Pradeeparul2/house-plan/docs/index.md

# Master Documentation Index

| Section | File | Description |
|---|---|---|
| **Section_00** | `docs/00_section_00.md` | Section details |
| **Table of Contents** | `docs/01_table_of_contents.md` | Section details |
| **1. Executive Architectural Summary** | `docs/02_1_executive_architectural_summ.md` | Section details |
| **2. Visual Renderings Portfolio** | `docs/03_2_visual_renderings_portfolio.md` | Section details |
| **3. 3D Architectural & Structural Component Overview** | `docs/04_3_3d_architectural_structural_.md` | Section details |
| **4. Site, Substructure & Underground Utilities** | `docs/05_4_site_substructure_undergroun.md` | Section details |
| **5. Structural Column Grid & Floor Levels** | `docs/06_5_structural_column_grid_floor.md` | Section details |
| **6. Ground Floor Spatial Program & Room Schedules** | `docs/07_6_ground_floor_spatial_program.md` | Section details |
| **7. Staircase Bay & Integrated Utility Area** | `docs/08_7_staircase_bay_integrated_uti.md` | Section details |
| **8. Staircase Ergonomic & NBC Compliance Audit** | `docs/09_8_staircase_ergonomic_nbc_comp.md` | Section details |
| **9. Front Facade & Exterior Elevation Design** | `docs/10_9_front_facade_exterior_elevat.md` | Section details |
| **10. First Floor (G+1) Modular Expansion Design** | `docs/11_10_first_floor_g_1_modular_exp.md` | Section details |
| **11. Electrical & ELV Surveillance Engineering Specifications** | `docs/12_11_electrical_elv_surveillance.md` | Section details |
| **12. Material, Color & Finish Schedule** | `docs/13_12_material_color_finish_sched.md` | Section details |
| **13. FreeCAD Document Hierarchy & Tree Structure** | `docs/14_13_freecad_document_hierarchy_.md` | Section details |
| **14. Workspace File Organization** | `docs/15_14_workspace_file_organization.md` | Section details |
| **15. Verification & File Status** | `docs/16_15_verification_file_status.md` | Section details |
| **16. Structural Continuous Full-Width 360° Closed-Loop RCC Lintel & Seismic Ring Beam Schedule (IS 4326 & IS 456 / NBC Compliance)** | `docs/17_16_structural_continuous_full_.md` | Section details |
| **17. First Floor North Facade Optimization: Dust Prevention & Staircase Isolation** | `docs/18_17_first_floor_north_facade_op.md` | Section details |
| **18. Rooftop Staircase Headroom (Mumty) Structural Frame Integration** | `docs/19_18_rooftop_staircase_headroom_.md` | Section details |
| **19. First Floor Independent Electricity Board (EB) Service & Electrical Infrastructure (IS 732 & NBC 2016 Compliance)** | `docs/20_19_first_floor_independent_ele.md` | Section details |
| **20. First Floor Dedicated Uninterruptible Power Supply (UPS) System & Utility Loft** | `docs/21_20_first_floor_dedicated_unint.md` | Section details |
| **21. Continuous Vertical Wall Conduit Network into Modular Switch Boxes & Distribution Boards** | `docs/22_21_continuous_vertical_wall_co.md` | Section details |
| **22. Complete 1:1 Duplicate Electrical System Alignment (Ground Floor to First Floor)** | `docs/23_22_complete_1_1_duplicate_elec.md` | Section details |
| **23. Sitout & Entrance Verandah Lighting and Conduit Integration** | `docs/24_23_sitout_entrance_verandah_li.md` | Section details |
| **24. Staircase Luminaire Relocation to East Wall of Toilet** | `docs/25_24_staircase_luminaire_relocat.md` | Section details |
| **25. Direct Switchbox-to-Luminaire Staircase Wall Lighting & Slab Infrastructure De-Cluttering** | `docs/26_25_direct_switchbox_to_luminai.md` | Section details |
| **26. Under-Stair Utility Switchboard (SB-UTIL) Proper Repositioning** | `docs/27_26_under_stair_utility_switchb.md` | Section details |
| **27. De-scoping and Removal of Utility Switchboard (SB-UTIL) from First Floor** | `docs/28_27_de_scoping_and_removal_of_u.md` | Section details |
| **28. Relocation of Staircase Light Switchbox to South Staircase Wall** | `docs/29_28_relocation_of_staircase_lig.md` | Section details |
| **29. Sitout Area Electrical Pipelines Completion & Full Electrical Network Visualization (Walls Hidden)** | `docs/30_29_sitout_area_electrical_pipe.md` | Section details |
| **30. Integration of Deep PVC Pendant Pot Boxes at All Conduit Pipe Crossings & Multi-Branch Junctions** | `docs/31_30_integration_of_deep_pvc_pen.md` | Section details |
| **31. Relocation of Ground Floor Staircase Wall Luminaire to Low-Level Landing Elevation** | `docs/32_31_relocation_of_ground_floor_.md` | Section details |
| **32. FreeCAD GUI Direct Visualization & Tree Node Separation for Staircase Lighting and Switchbox (`SB_STAIR1`)** | `docs/33_32_freecad_gui_direct_visualiz.md` | Section details |
| **33. Relocation of GF Staircase Wall Luminaire to 2 Feet Below FF Stair Mid-Landing Slab** | `docs/34_33_relocation_of_gf_staircase_.md` | Section details |
| **34. First Floor Staircase Wall Luminaire Relocation: 2 Feet Below Rain Protection Canopy Slab** | `docs/35_34_first_floor_staircase_wall_.md` | Section details |
| **35. First Floor Staircase Wall Luminaire Relocation: Headroom Weatherproof Wall (2 Feet Below Headroom Roof Slab)** | `docs/36_35_first_floor_staircase_wall_.md` | Section details |
| **36. Under-Stair Sump Water Pump Motor Switch Integrated into Utility Switchboard (SB-UTIL)** | `docs/37_36_under_stair_sump_water_pump.md` | Section details |
| **37. Ground Floor Living Room: Isolated MEP Electrical & Wiring Pipeline Architecture** | `docs/38_37_ground_floor_living_room_is.md` | Section details |
| **38. Kitchen Exhaust Fan Relocation to East Side Wall (Over Sink Bay)** | `docs/39_38_kitchen_exhaust_fan_relocat.md` | Section details |
| **39. Master Bedroom Electrical Pipeline Optimization** | `docs/40_39_master_bedroom_electrical_p.md` | Section details |
| **40. Ground Floor Toilet (4'-0" x 6'-0") Architectural, MEP & Plumbing Pipeline System** | `docs/41_40_ground_floor_toilet_4_0_x_6.md` | Section details |
| **41. Living Room Slab Conduit Optimization** | `docs/42_41_living_room_slab_conduit_op.md` | Section details |
| **42. Master Bedroom Ceiling Fan Provision (`FB-BED`)** | `docs/43_42_master_bedroom_ceiling_fan_.md` | Section details |
| **43. Complete Living Room Ceiling Electrical Pipeline Optimization & De-duplication** | `docs/44_43_complete_living_room_ceilin.md` | Section details |
| **44. Breakfast Counter Spotlight MEP Pipeline Connection (`DL-BC`)** | `docs/45_44_breakfast_counter_spotlight.md` | Section details |
| **44.1 Ground Floor Master Bedroom (Room 2/5) Pipeline Recheck & Full Restoration** | `docs/46_44_1_ground_floor_master_bedro.md` | Section details |
| **45. Master Bedroom Wardrobe Zone — De-Cluttering & Redundant MEP Excision** | `docs/47_45_master_bedroom_wardrobe_zon.md` | Section details |
| **46. Kitchen Entrance — Removal of North-Facing Switchbox** | `docs/48_46_kitchen_entrance_removal_of.md` | Section details |
| **47. Kitchen & Living Room Pipelines Reconnected — Seamless Orthogonal Conduit Loop** | `docs/49_47_kitchen_living_room_pipelin.md` | Section details |
| **48. Sitout Electrical Pipelines Checked & Optimized — 100% Orthogonal Grid** | `docs/50_48_sitout_electrical_pipelines.md` | Section details |
| **49. Ground Floor Electrical Pipelines — Unified Tree Grouping** | `docs/51_49_ground_floor_electrical_pip.md` | Section details |
| **50. First Floor Electrical Pipelines — Identical Grouping Parity** | `docs/52_50_first_floor_electrical_pipe.md` | Section details |
| **51. First Floor Stairs Wall Light Pipeline — Seamless Jointing (Gap Elimination)** | `docs/53_51_first_floor_stairs_wall_lig.md` | Section details |
| **52. First Floor MCB Distribution Board (MDB) & Main Door Handle — 100% Ground Floor Parity** | `docs/54_52_first_floor_mcb_distributio.md` | Section details |
| **53. Outdoor Switchboard (SB-1) Consolidation into Staircase Switchboard (SB_STAIR1)** | `docs/55_53_outdoor_switchboard_sb_1_co.md` | Section details |
| **54. Full-Building Model Tree Hierarchy & Object Grouping Audit** | `docs/56_54_full_building_model_tree_hi.md` | Section details |
| **55. Under-Stair Utility Switchboard (SB-UTIL) Pipeline Connectivity Resolution** | `docs/57_55_under_stair_utility_switchb.md` | Section details |
| **56. Bedroom East Wall: Loft Removal & Split AC Electrical Provision Integration** | `docs/58_56_bedroom_east_wall_loft_remo.md` | Section details |
| **57. Split AC Outdoor Unit (ODU) East Elevation Implementation (Option 2)** | `docs/59_57_split_ac_outdoor_unit_odu_e.md` | Section details |
| **58. Detailed 2D Ground Floor Plan with Dimensions (From 3D Model)** | `docs/60_58_detailed_2d_ground_floor_pl.md` | Section details |
| **59. Substructure Isolated Footings, Column Pedestals & Plinth Beam System (BOQ & Construction Detailing)** | `docs/61_59_substructure_isolated_footi.md` | Section details |
| **60. Underground Sump Vertical Alignment to Plinth Floor & Sitout Manhole Integration** | `docs/62_60_underground_sump_vertical_a.md` | Section details |
| **61. Septic Tank Vertical Alignment to Plinth Floor & Airtight Inspection Manhole Integration** | `docs/63_61_septic_tank_vertical_alignm.md` | Section details |
| **62. Substructure Spatial Collision Elimination: Raft Foundations & Exact Bay-Fitted Tanks** | `docs/64_62_substructure_spatial_collis.md` | Section details |
| **63. Complete 3D Architectural Building Visualization (All Storeys & Facades Active)** | `docs/65_63_complete_3d_architectural_b.md` | Section details |
| **64. Municipal Water Inflow Pipeline, Dual-Tap Kitchen Sink & Underground Sump Integration** | `docs/66_64_municipal_water_inflow_pipe.md` | Section details |
| **65. Overhead Water Tank (OHT) on Mumty Headroom Roof & Mandatory Construction Safeguards** | `docs/67_65_overhead_water_tank_oht_on_.md` | Section details |
| **66. Closed-Loop Water Distribution Network: Gravity Down-take Risers & Zonal Leak Isolation System** | `docs/68_66_closed_loop_water_distribut.md` | Section details |
| **67. Kitchen Sink Plumbing Re-Orientation: East-Side Tap Relocation & Direct Chase Feed** | `docs/69_67_kitchen_sink_plumbing_re_or.md` | Section details |
| **68. Building Drainage Network: Kitchen Greywater Drainage System & North Road Outfall** | `docs/70_68_building_drainage_network_k.md` | Section details |
| **69. Dual-Stream Toilet Wastewater & Sullage Segregation System (IS 1742 & IS 2470 Compliant)** | `docs/71_69_dual_stream_toilet_wastewat.md` | Section details |
| **70. Toilet Sunken Wet Area (15 cm Drop Below Surface) Architectural & Sanitary Detailing** | `docs/72_70_toilet_sunken_wet_area_15_c.md` | Section details |
| **71. Ergonomic Staircase Overhaul: 4-Winder Turnaround Landing & 17 Uniform 186.65 mm Risers (NBC 2016 Compliant)** | `docs/73_71_ergonomic_staircase_overhau.md` | Section details |
| **72. Comprehensive Staircase Safety Railings & Void Guardrail System (NBC 2016 Compliant)** | `docs/74_72_comprehensive_staircase_saf.md` | Section details |
| **73. OHT Kitchen Sink Down-Take Pipeline Re-Routing: Headroom Weather Curb to Col NE (Zero Window Obstruction)** | `docs/75_73_oht_kitchen_sink_down_take_.md` | Section details |
| **74. Rooftop Terrace Weatherproof Wall Luminaire & Entrance Switchboard (SB-TERRACE)** | `docs/76_74_rooftop_terrace_weatherproo.md` | Section details |
| **75. RCC Structural Optimization: 8-Column Frame Layout, Primary Living Hall Cross-Beam & Substructure Sync** | `docs/77_75_rcc_structural_optimization.md` | Section details |
| **76. Ground Floor AAC Block Wall Schedule & Specifications** | `docs/02_ground_floor.md` | Parametric AAC masonry wall ledger, clearances, aperture cutouts & material takeoffs |
| **77. First Floor AAC Block Wall Schedule & Specifications** | `docs/03_first_floor.md` | First floor parametric AAC masonry wall ledger, 1:1 parity & material takeoffs |
| **78. Pre-Drafting Model Health & Specification Readiness Audit** | `docs/78_pre_drafting_audit.md` | Pre-drafting health audit, discrepancy matrix, 2D sheet readiness scorecard & automated fix validation |
