Pradeeparul2/house-plan/docs/31_30_integration_of_deep_pvc_pen.md

## 30. Integration of Deep PVC Pendant Pot Boxes at All Conduit Pipe Crossings & Multi-Branch Junctions

In strict compliance with the client's directive (*"whenever pipe crossing happen add Pendant Pot Boxes"*) and Indian electrical standard **IS 732 / NBC Part 8**, deep PVC circular pendant pot boxes ($\varnothing 85\text{ mm} \times 60\text{ mm}$) have been engineered and cast into the slab at every single horizontal conduit crossing and multi-branch convergence junction:

```carousel
![Direct Top Plan View Showing Pendant Pot Boxes at All Slab Conduit Crossings](C:\Users\prade\.gemini\antigravity\brain\086e9390-dcd1-4cec-9724-3cc5bbdd6a28\pendant_pot_boxes_top_view.png)
<!-- slide -->
![Zoomed-in Perspective View of Central Dining & Corridor Crossing Pot Boxes](C:\Users\prade\.gemini\antigravity\brain\086e9390-dcd1-4cec-9724-3cc5bbdd6a28\pendant_pot_boxes_crossing_zoom.png)
<!-- slide -->
![Full Two-Storey Isometric Overview Highlighting All 34 Embedded Blue Downlight & Pendant Pot Boxes](C:\Users\prade\.gemini\antigravity\brain\086e9390-dcd1-4cec-9724-3cc5bbdd6a28\pendant_pot_boxes_crossings_iso.png)
```

### 30.1 Engineering Rationale & Benefits of Crossing Pot Boxes

1. **Zero Slab Conduit Overlap & Flattening:**
   - In RCC monolithic slabs ($125\text{ mm}$ thickness), running $25\text{ mm}$ conduits over or under each other consumes $50\text{ mm} + \text{clearance}$, which severely degrades structural concrete cover and risks pipe crushing during concrete compaction.
   - Inserting a 4-way/3-way deep junction pot box allows all intersecting conduits to enter orthogonally at the exact same horizontal centerline elevation ($Z = 4020.0\text{ mm}$ GF / $Z = 7193.0\text{ mm}$ FF), preventing pipe pinch-points and easing cable pulling.
2. **Dual-Function Lighting & Access:**
   - Each crossing box provides a flush circular ceiling portal ($\varnothing 85\text{ mm}$) that functions as:
     - A decorative pendant chandelier / hanging luminaire point.
     - An inspection and wire pulling junction box for circuit branching and loop-in maintenance.

### 30.2 Newly Integrated Crossing & Multi-Branch Pot Boxes

Five critical crossing and convergence hubs have been upgraded with dedicated Pendant Pot Boxes across both Ground and First Floors:

| Pot Box ID | Room / Zone | Coordinates $(X, Y)$ (mm) | Slab Elevation ($Z$) | Intersecting / Converging Conduit Branches | Architectural & Lighting Function |
| :--- | :--- | :--- | :--- | :--- | :--- |
| **PB-CROSS-1** | Bedroom Entry Corridor | $(2572.9, 4720.2)$ | GF: $3992.4$, FF: $7165.4$ | - Living Fan `FB-1` to Bedroom Downlight `DL-5`<br>- Dining Entry to Bedroom Study Switchboard `SB-11` | Resolves interior conduit crossing; serves as a corridor transition downlight. |
| **PB-CROSS-2** | Central Dining Hall | $(1850.0, 4775.1)$ | GF: $3992.4$, FF: $7165.4$ | - Feeder from Kitchen Pot `DL-7`<br>- Drop to Dining Entry `SB-4`<br>- Drop to Dining South `SB-5`<br>- Drop to Bedroom Entry `SB-8`<br>- Feeder to Bedroom Study `SB-11` | Major 5-way central distribution hub; accommodates the Dining Table pendant chandelier. |
| **PB-CROSS-3** | Toilet & Stair Lobby | $(3810.0, 1828.8)$ | GF: $3992.4$, FF: $7165.4$ | - Living Room East Pot `DL-2`<br>- Toilet Entrance Drop `SB-12`<br>- Toilet Geyser Drop `SB-13`<br>- Under-Stair Utility Station `SB-UTIL` | 4-way wet-zone distribution hub; provides ceiling lobby ambient downlight. |
| **PB-CROSS-4** | Master Bedroom South Aisle | $(2200.0, 7467.6)$ | GF: $3992.4$, FF: $7165.4$ | - Bedroom Fan `FB-2`<br>- Bedside Left `SB-9`<br>- Wardrobe / AC Drop on South Wall | 3-way bedroom power distribution hub; wardrobe passage recessed downlight. |
| **PB-CROSS-5** | Sitout Entrance Transition | $(370.0, 1720.0)$ | GF: $3992.4$, FF: $7165.4$ | - Sitout Downlight Pot $(857, 857)$<br>- Vertical drop to Sitout Switchboard `SB-1`<br>- Plinth drop to Gate Post | Transition junction linking horizontal slab runs to vertical wall drops and gate feeds. |

### 30.3 Component Schedule Audit

* **`Electrical_Slab_Light_Pots` (Ground Floor):** Expanded from 12 to **17 solid pot units** (12 room downlights + 5 crossing/multi-branch pendant boxes).
* **`FF_Electrical_Slab_Light_Pots` (First Floor):** Expanded from 12 to **17 solid pot units** (exact 1:1 vertical duplicate shifted by $\Delta Z = +3173.0\text{ mm}$).
* **Total Building Ceiling Junction Units:** **34 deep PVC pot boxes** (Electric Blue `#0074E4`) + **6 heavy-duty fan hook boxes** (Crimson Red `#E74C3C`).
* **Document Integrity:** Fully recomputed in `HomeConstruction.FCStd` with zero geometric errors.

---
