Pradeeparul2/house-plan/docs/38_37_ground_floor_living_room_is.md

## 37. Ground Floor Living Room: Isolated MEP Electrical & Wiring Pipeline Architecture

Per user directive (*"lets move to living room hide all other areas show the living room and wiring pipelines"*), all external areas (First Floor, Terrace Mumty, Bedroom, Kitchen, Toilet, Sitout, and Stairwell) have been hidden in FreeCAD. The **Ground Floor Living Room** and its complete concealed electrical conduit pipeline network have been isolated and highlighted:

```carousel
![FreeCAD Viewport Showing Ground Floor Living Room Isolated with Complete Slab and Wall Wiring Pipelines](C:\Users\prade\.gemini\antigravity\brain\086e9390-dcd1-4cec-9724-3cc5bbdd6a28\living_room_pipelines_annotated.png)
<!-- slide -->
![Axonometric View Showing Ceiling Conduit Network and TV Feature Wall Media Drops](c:\Users\prade\OneDrive\Desktop\home plan\renders\living_room_perfect_fit.png)
```

### 37.1 Architectural Envelope & Boundary Definition
* **Room Footprint:** $X \in [0.0, 5029.2\text{ mm}]$ ($16'\text{-}6"$), $Y \in [1714.5, 5181.6\text{ mm}]$ ($11'\text{-}4"$), $Z \in [914.4, 4087.4\text{ mm}]$ ($10'\text{-}0"$ ceiling clearance). Total area $\approx 187\text{ sq ft}$.
* **Wall Treatments:** Chased solid brickwork rendered in 75% translucent ghosting to reveal the internal vertical conduit drop runs.
* **Key Built-In Features:**
  - **North:** Teak 5-Panel Main Entrance Door (`Main_Door`) with classical white architectural arch surround.
  - **East:** 3-Panel casement window (`Living_Room_Window_East_Group`) with reinforced precast utility loft (`Living_Room_Loft_East`).
  - **West:** Modern TV Feature Wall with charcoal fluted acoustic wall panel, 65" smart display, floating console cabinet, and soundbar.

### 37.2 Ceiling Slab Lighting & Fan Infrastructure
* **Central Fan Box (`FB-1`):** Parametric galvanized octagonal fan box with integrated hook at $(X = 2514.6, Y = 3257.4, Z = 4020.0\text{ mm})$, centered in the ceiling.
* **4-Point Recessed Downlight Grid (`DL-1` to `DL-4`):**
  - **DL-1 (NE):** $(X = 1200.0, Y = 2500.0, Z = 4020.0\text{ mm})$
  - **DL-2 (NW):** $(X = 3800.0, Y = 2500.0, Z = 4020.0\text{ mm})$
  - **DL-3 (SE):** $(X = 1200.0, Y = 4000.0, Z = 4020.0\text{ mm})$
  - **DL-4 (SW):** $(X = 3800.0, Y = 4000.0, Z = 4020.0\text{ mm})$
* **Slab Conduit Piping (`Living_Slab_Conduit_Network`):**
  - $25\text{ mm}$ heavy-gauge rigid PVC in **Conduit Orange (`#FF7300`)** embedded at $Z = 4020.0\text{ mm}$.
  - Spider layout connecting `FB-1` directly to each of the 4 downlight pots and branching out to the perimeter wall headers.

### 37.3 Concealed Wall Chases & Modular Switchboards (`Living_Slab_Wall_Drops`)
All drops utilize $25\text{ mm}$ rigid PVC pipe in **Safety Emerald Green (`#10AC84`)**:
1. **Main Distribution Board (MDB):**
   - Location: North Foyer Wall at $(X = 1600.0, Y = 1930.0, Z = 2254.4 - 2574.4\text{ mm})$.
   - Houses 40A 30mA 4-pole RCCB, master DP isolator, and individual circuit MCBs.
2. **Main Room Switchboard (`SB-2`):**
   - Location: North Wall beside Main Door at $(X = 1700.0, Y = 1937.0, Z = 2114.4\text{ mm})$.
   - 8-Module plate controlling Ceiling Fan speed, chandelier/center cove, and the 4 recessed ceiling downlights.
3. **TV Media Console Switchboards (`SB-3` & `SB-3B`):**
   - Location: West Feature Wall at $X = 4845.0\text{ mm}, Y = 3262.0\text{ mm}$.
   - **SB-3 (Low-Level, $Z = 1460.0\text{ mm}$):** 6-module entertainment power sockets (Set-top box, gaming console, AV receiver) + RJ45 data point.
   - **SB-3B (Mid-Level, $Z = 2050.0\text{ mm}$):** Dedicated hidden power socket & HDMI pass-through behind the 65" wall-mounted display.
4. **Security & Tech Loft Hub (`SB-16`):**
   - Location: East Wall utility loft at $(X = 157.0, Y = 2325.0, Z = 3260.0\text{ mm})$ supplying the CCTV NVR and emergency UPS backup.

### 37.4 Master CAD Model State
* **CAD Master File:** [`HomeConstruction.FCStd`](file:///c:/Users/prade/OneDrive/Desktop/home%20plan/HomeConstruction.FCStd)
* **Isolated Display Objects:** `Living_Slab_Conduit_Network`, `Living_Slab_Wall_Drops`, `Living_Slab_Fan_Box`, `Living_Slab_Light_Pots`, `Living_Room_Switchboard_Plates`, and `Living_Room_Switchboard_Switches`.

### 37.5 Switchboard Model Consolidation: Plates & Switches Unified
In response to user feedback (*"why we have seperate boxes, is it possible to make it single"*), the switchboards were merged:
* **Previous Split Reason:** In CAD, plates (polycarbonate white) and rockers/sockets (charcoal black) were kept in separate compounds solely for multi-material color display.
* **Unified Resolution:** `Living_Room_Switchboard_Plates` and `Living_Room_Switchboard_Switches` were permanently fused into a single unified parametric object: **`Living_Room_Switchboards`**.
* **Benefits:** Eliminates tree clutter, provides clean single-click selection, and maintains 100% solid manifold geometry for all room controls (MDB, SB-2, SB-3, SB-16).

### 37.6 Living Room North Entrance MEP Consolidation: Combined Console & Single Pipeline
Per user request (*"Living Room Switchboards (MDB, SB-2, SB-3, SB-16 - Unified) make it compaine and single pipe line now i can see two pipe lines"*), the North entrance wall electrical infrastructure was completely re-architected:

```carousel
![Living Room Entrance Electrical Upgrade Showing Unified MDB and SB-2 Console Fed by Single Vertical Drop](C:\Users\prade\.gemini\antigravity\brain\086e9390-dcd1-4cec-9724-3cc5bbdd6a28\living_room_single_pipeline_combined_console.png)
<!-- slide -->
![Interior View of Living Room Looking at Main Entrance Showing Flush Multi-Tier Console and Single Drop](C:\Users\prade\.gemini\antigravity\brain\086e9390-dcd1-4cec-9724-3cc5bbdd6a28\living_room_combined_console_interior_annotated.png)
```

#### 1. Combined Architectural Console (MDB + SB-2 Unified Enclosure)
* **Previous State:** Two separate boxes were stacked vertically—the 12-way Main Distribution Board (`MDB`) at $+1340\text{ to }+1660\text{ mm}$ AFF and the 8-module Room Switchboard (`SB-2`) at $+1200\text{ mm}$ AFF, linked by an external interconnect pipe.
* **Unified Console Design:** Replaced both separate enclosures with a **Single 2-Tier Flush Architectural Console** ($X \in [1485, 1715\text{ mm}]$, $Y \in [1893, 1948\text{ mm}]$, $Z \in [2050, 2550\text{ mm}]$):
  - **Upper Section ($Z \in [2210, 2550\text{ mm}]$):** 12-Way SPN Distribution Board (40A RCCB, 32A DP Isolator, 6x MCBs) protected by a flush smoked-acrylic hinged door.
  - **Lower Section ($Z \in [2050, 2190\text{ mm}]$):** 8-Module Light & Fan Controller (6x 6A rocker switches, 1x fan speed regulator, 1x universal 6/16A socket).
  - **Internal Interconnect:** Factory-wired internal busbar links eliminate the external interlink pipe entirely.
  - **Single CAD Entity:** Integrated into `Living_Room_Switchboards` as a 100% solid manifold compound.

#### 2. Single Pipeline Vertical Conduit Drop
* **Eliminated Clutter:**
  - Removed Drop 1 (secondary $25\text{ mm}$ drop at $X = 1700\text{ mm}$).
  - Removed Drop 11 (horizontal interlink pipe at $Z = 2300\text{ mm}$).
  - Removed Slab Solid 2 (ceiling slab lateral connector between the two drops).
* **New Single Drop Run:**
  - **Diameter:** $25\text{ mm}$ heavy-gauge rigid PVC in Emerald Green (`#10AC84`).
  - **Route:** Centered at $(X = 1600.0, Y = 1930.0\text{ mm})$, running continuously from ceiling slab junction ($Z = 4020.0\text{ mm}$) straight down into the top flange of the combined console ($Z = 2550.0\text{ mm}$).
  - **Masonry Advantage:** Reduces wall chiseling to **exactly one vertical chase**, preserving structural masonry integrity beside the Main Door jamb.
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
