Pradeeparul2/house-plan/docs/39_38_kitchen_exhaust_fan_relocat.md

## 38. Kitchen Exhaust Fan Relocation to East Side Wall (Over Sink Bay)

Following client directive (*"move exhaust fan east side wall since south side wall common wall"*), the kitchen exhaust fan has been relocated to the **East exterior wall directly adjacent to the sink bay**, completely avoiding the South boundary wall which is a shared common wall with the adjacent property.
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
