Pradeeparul2/house-plan/renders/3d_axonometric_model.png

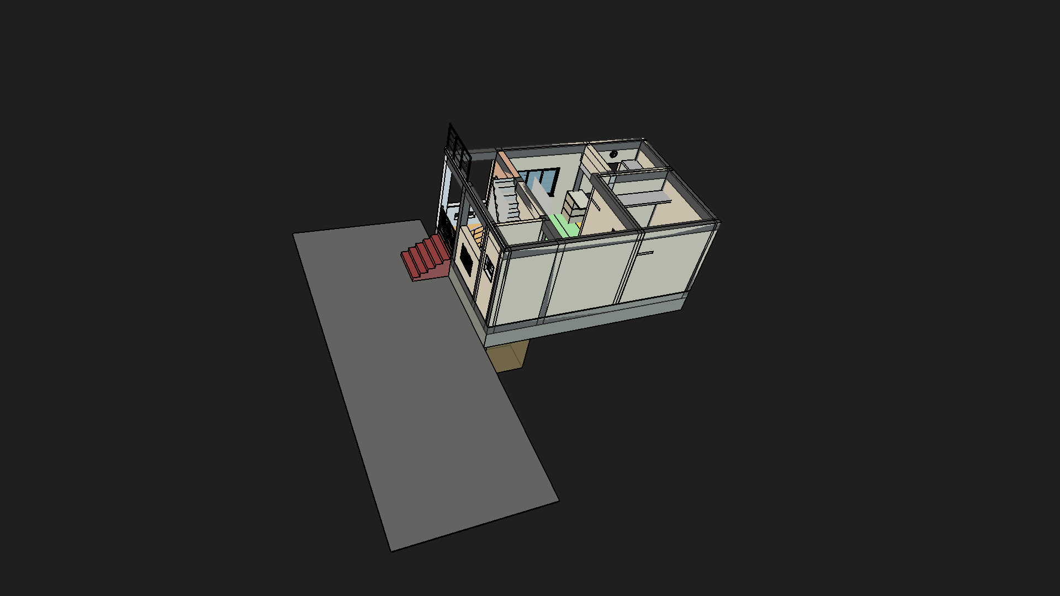
renders/3d_axonometric_model.png
