Pradeeparul2/house-plan/renders/3d_bedroom_door_wall_view.png

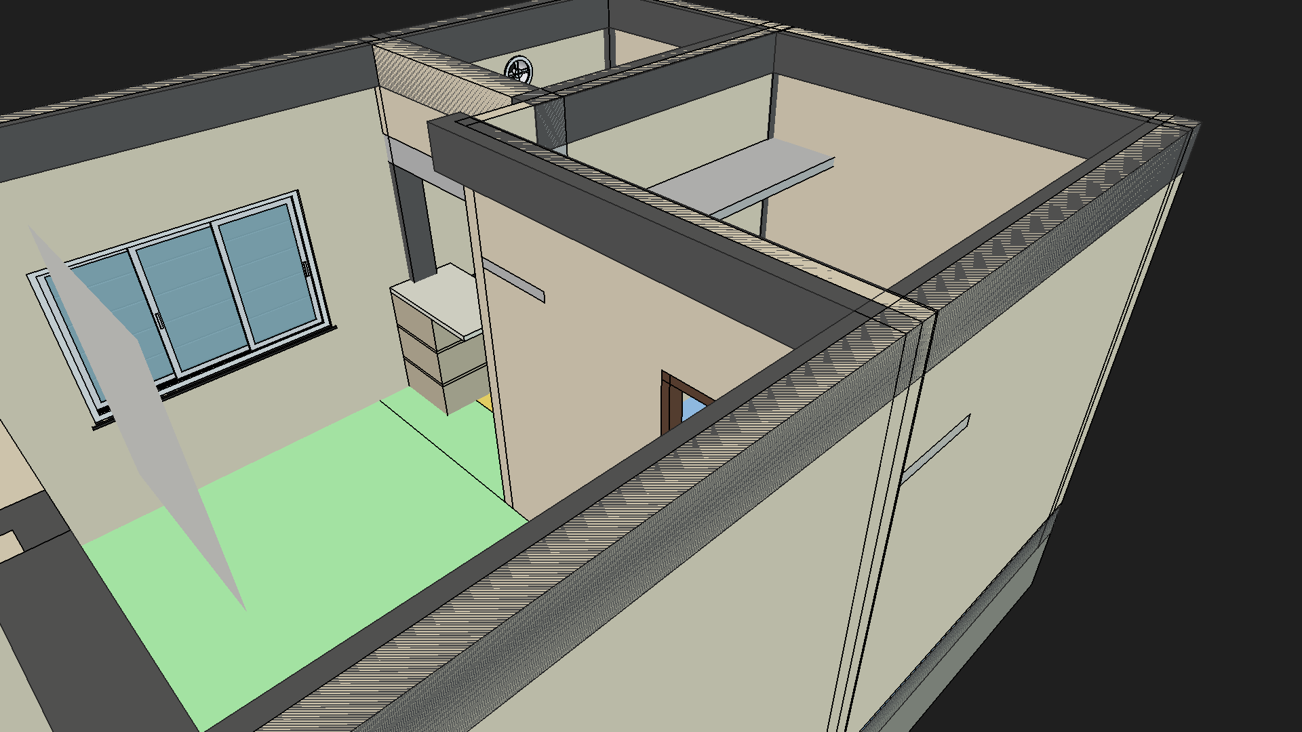
renders/3d_bedroom_door_wall_view.png
