Pradeeparul2/house-plan/renders/3d_model_painted_front_elevation.png

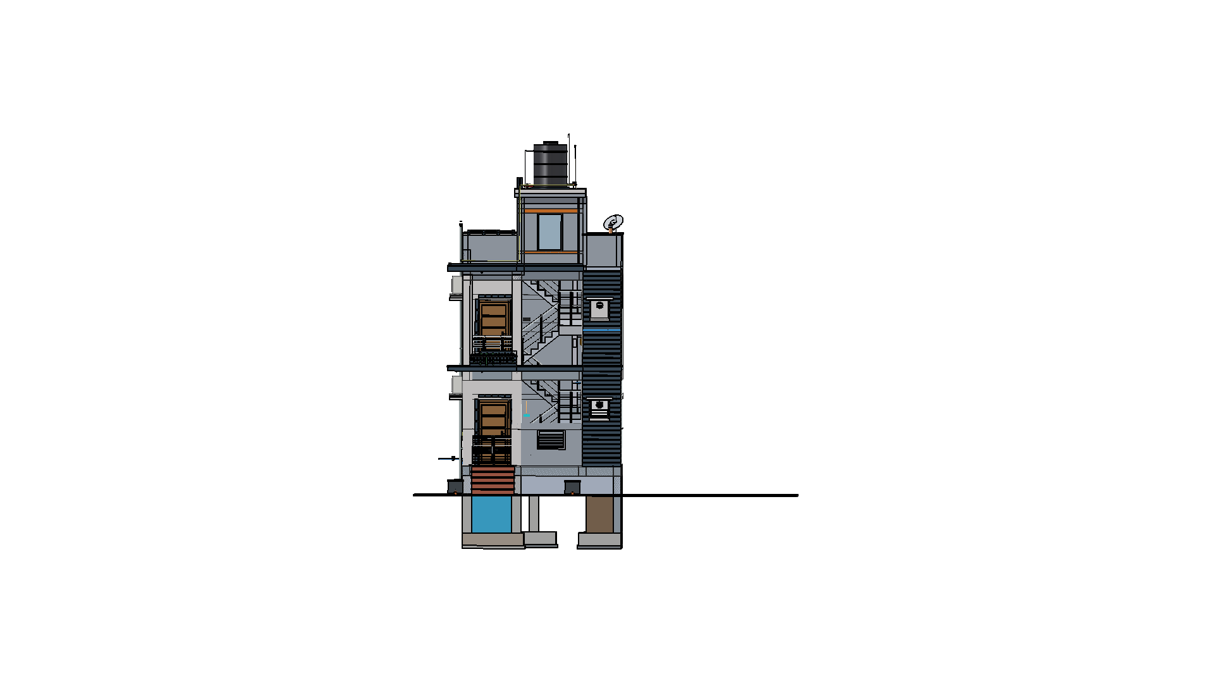
renders/3d_model_painted_front_elevation.png
