Pradeeparul2/house-plan/renders/all_electrical_pipelines_connected_southeast.png

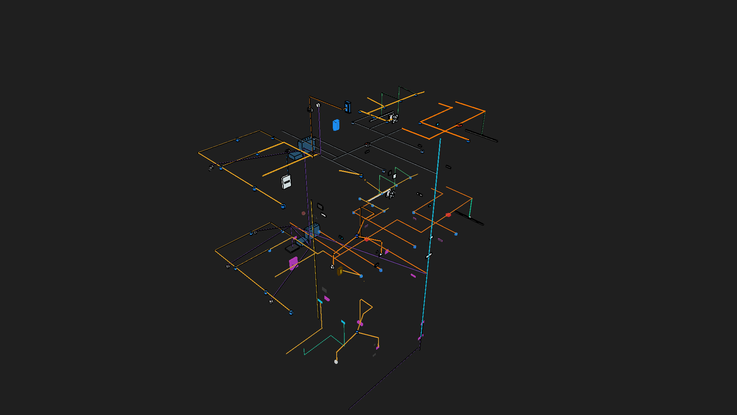
renders/all_electrical_pipelines_connected_southeast.png
