Pradeeparul2/house-plan/renders/all_electrical_pipelines_connected_top_plan.png

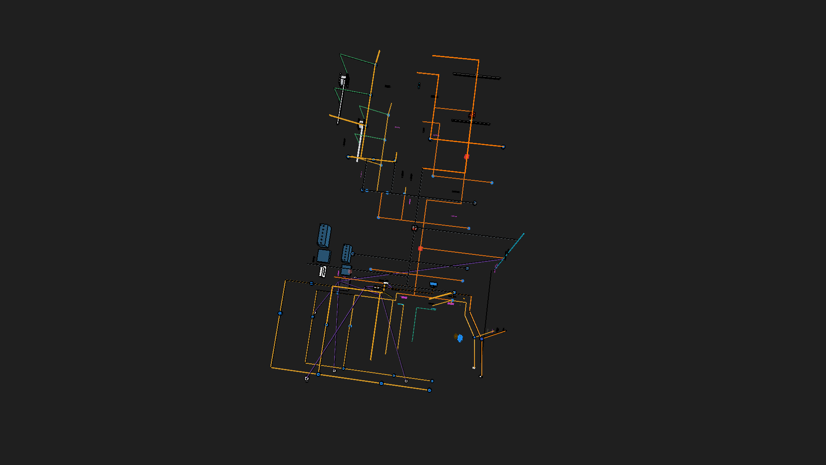
renders/all_electrical_pipelines_connected_top_plan.png
