Pradeeparul2/house-plan/renders/all_electrical_pipelines_front.png

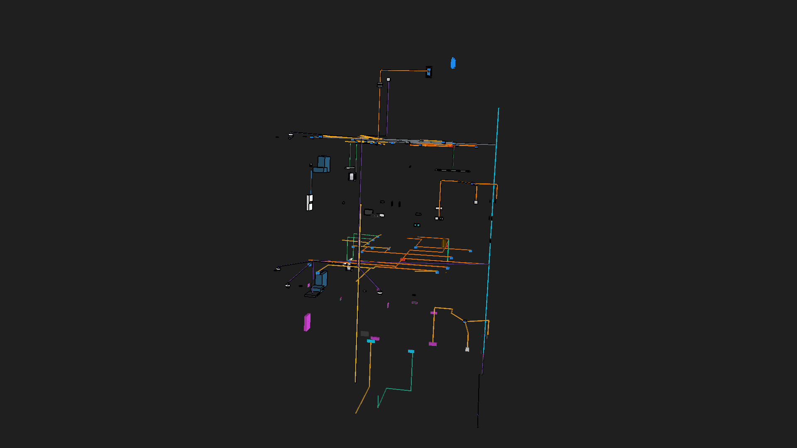
renders/all_electrical_pipelines_front.png
