Pradeeparul2/house-plan/renders/all_electrical_pipelines_full_view.png

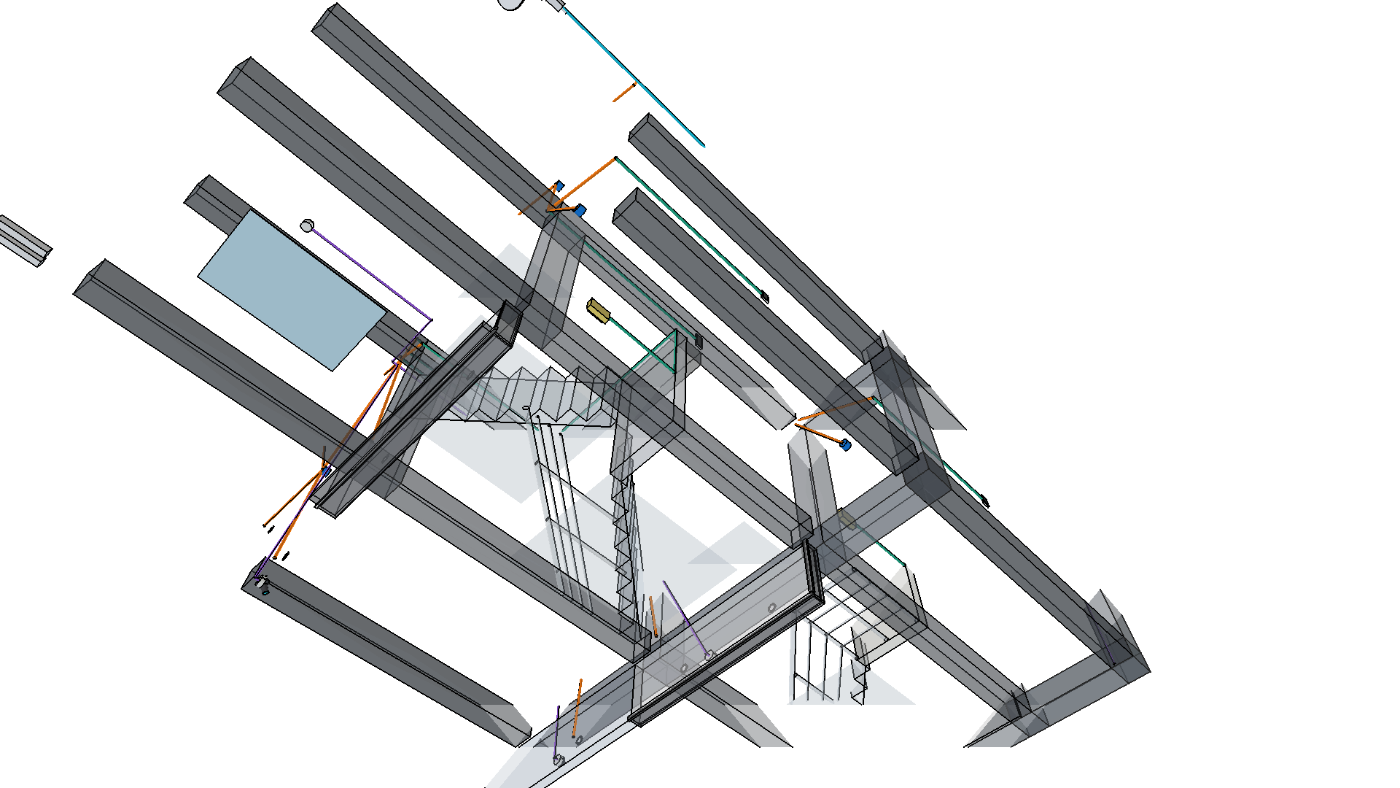
renders/all_electrical_pipelines_full_view.png
