Pradeeparul2/house-plan/renders/all_electrical_pipelines_isometric.png

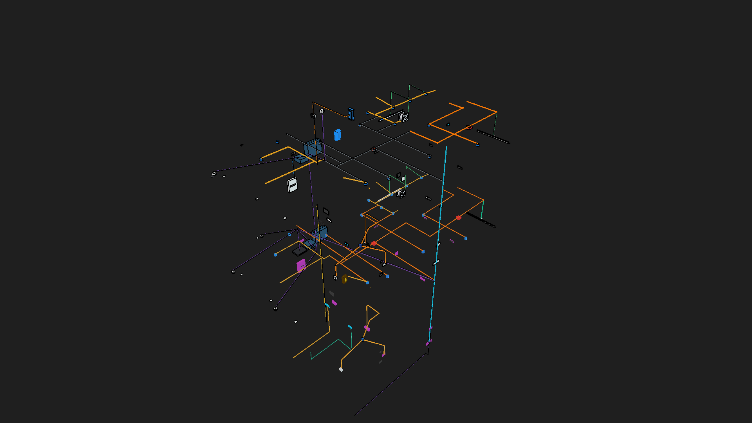
renders/all_electrical_pipelines_isometric.png
