Pradeeparul2/house-plan/renders/all_electrical_pipelines_top_plan_no_walls.png

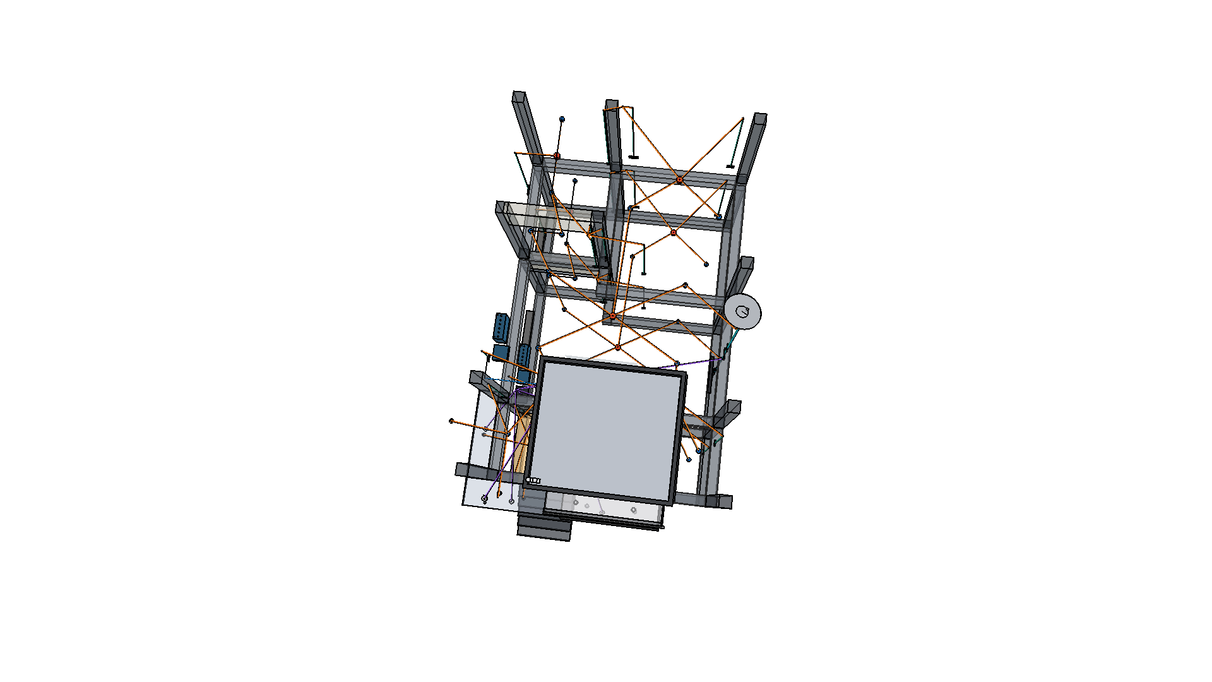
renders/all_electrical_pipelines_top_plan_no_walls.png
