Pradeeparul2/house-plan/renders/all_objects_visible_front.png

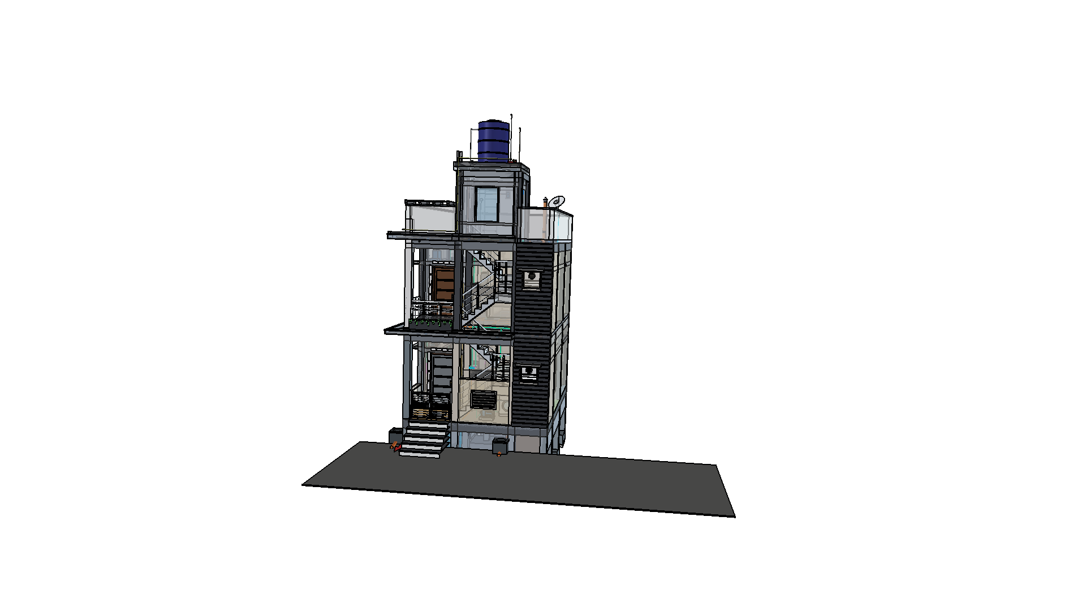
renders/all_objects_visible_front.png
