Pradeeparul2/house-plan/renders/all_staircase_railings_complete.png

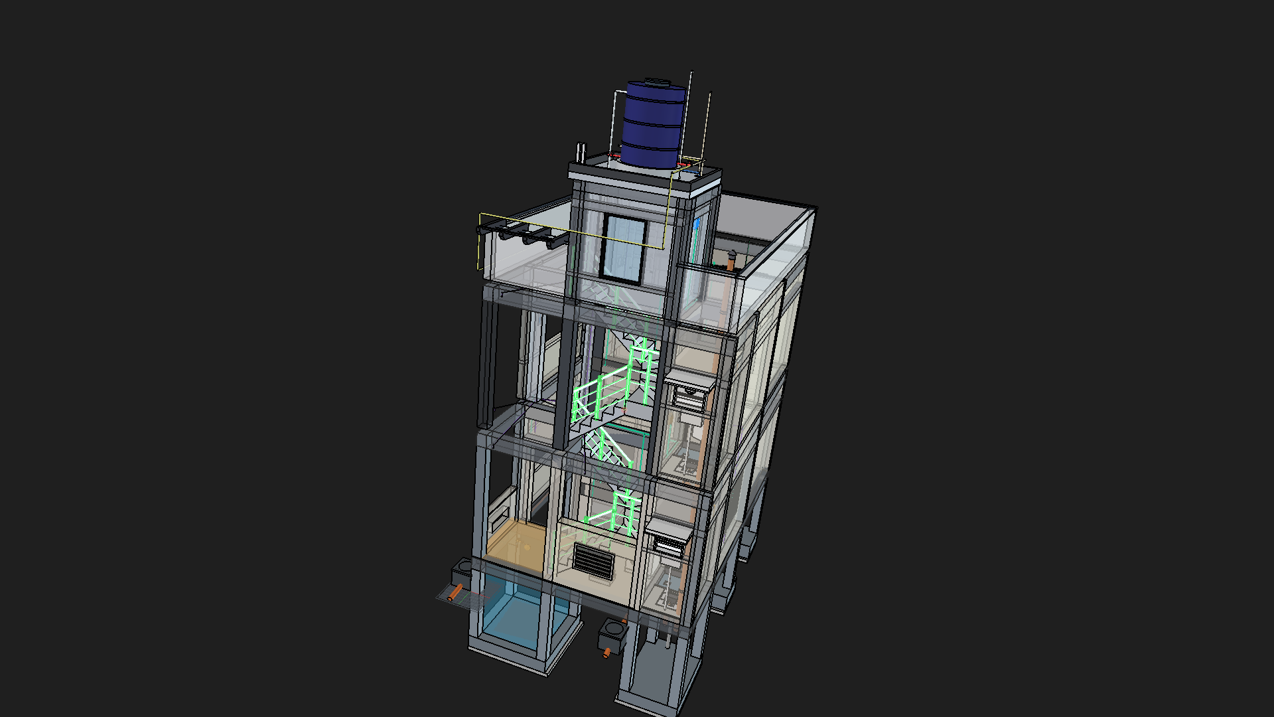
renders/all_staircase_railings_complete.png
