Pradeeparul2/house-plan/renders/bedroom_pipelines_and_switchboxes_annotated.png

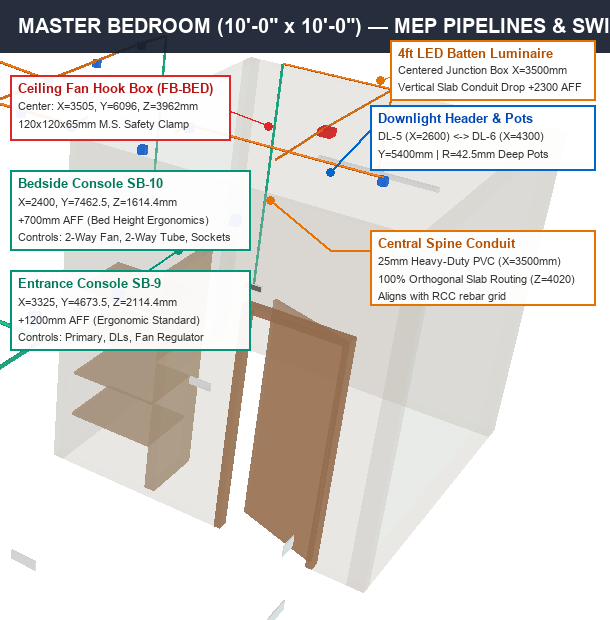
renders/bedroom_pipelines_and_switchboxes_annotated.png
