Pradeeparul2/house-plan/renders/bedroom_windows_both_floors.png

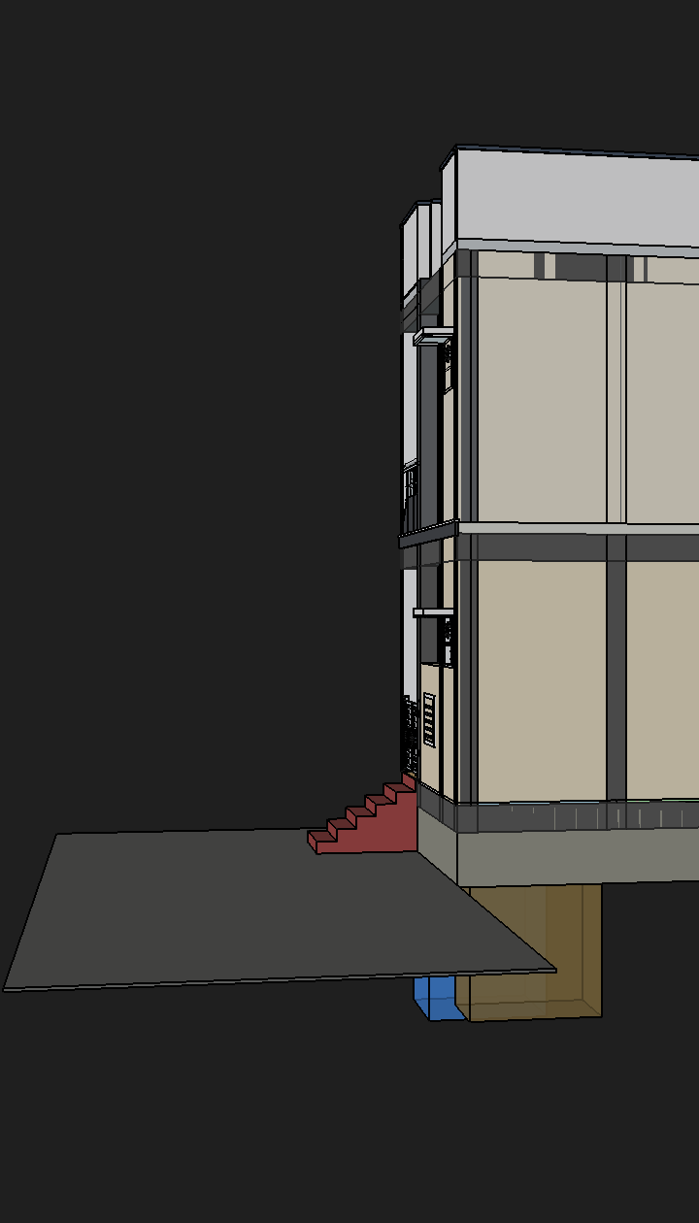
renders/bedroom_windows_both_floors.png
