Pradeeparul2/house-plan/renders/cam01_entrance_closeup.png

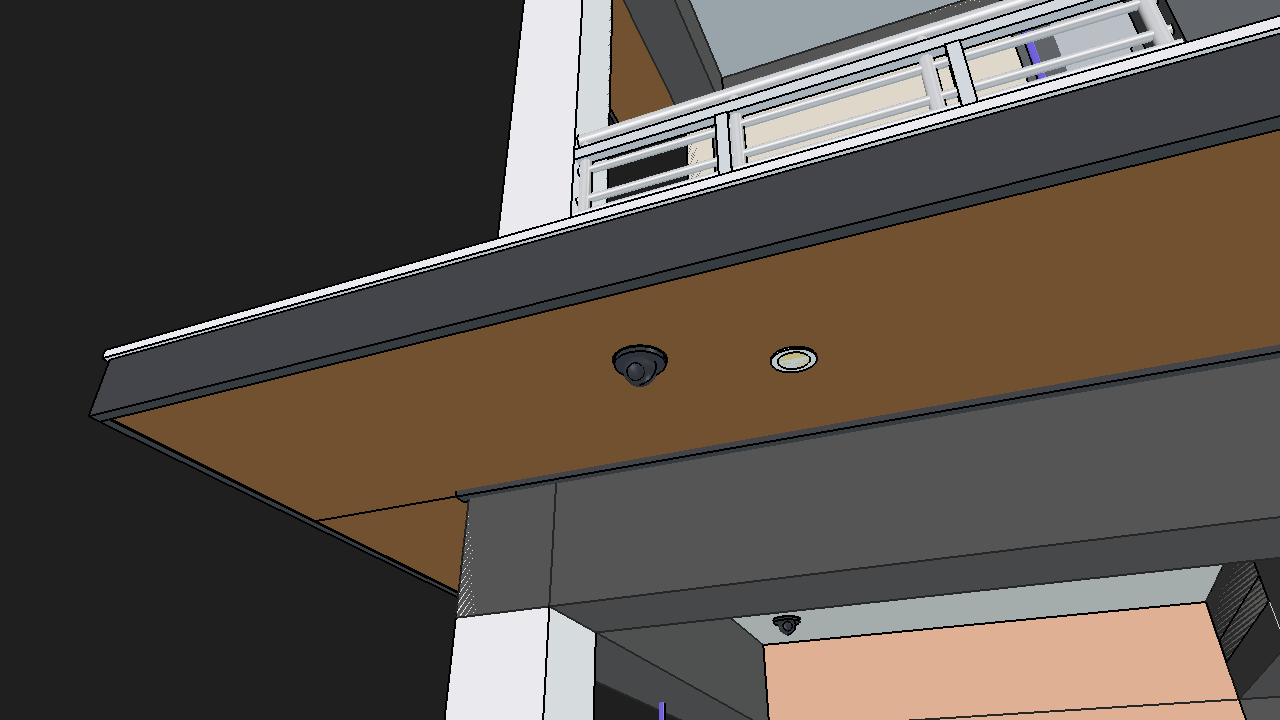
renders/cam01_entrance_closeup.png
