Pradeeparul2/house-plan/renders/cam03_east_closeup.png

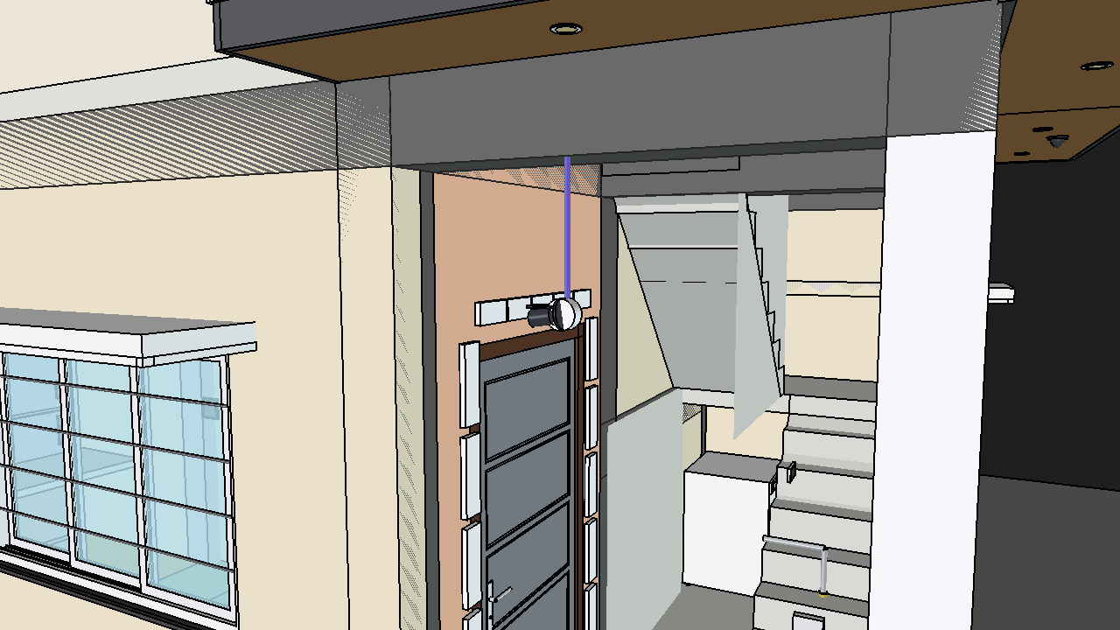
renders/cam03_east_closeup.png
