Pradeeparul2/house-plan/renders/cam05_mumty_terrace_view.png

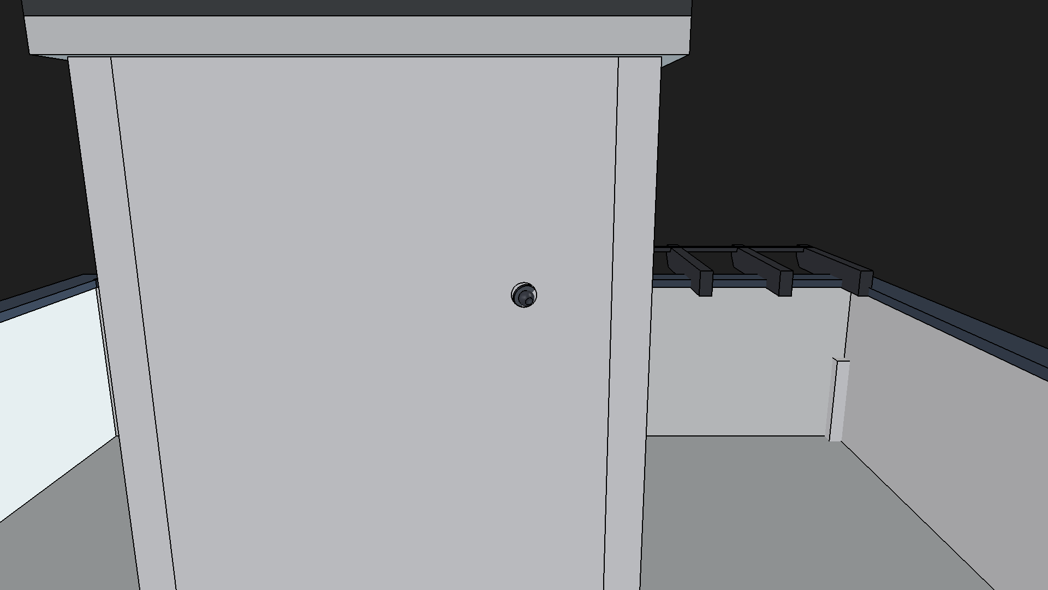
renders/cam05_mumty_terrace_view.png
