Pradeeparul2/house-plan/renders/canopy_pipes_closeup_top.png

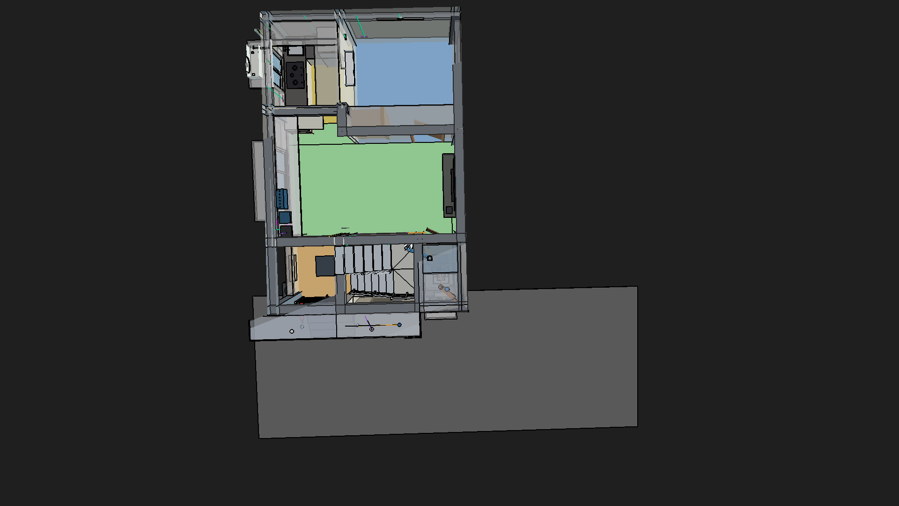
renders/canopy_pipes_closeup_top.png
