Pradeeparul2/house-plan/renders/cctv_complete_3storey_xray.png

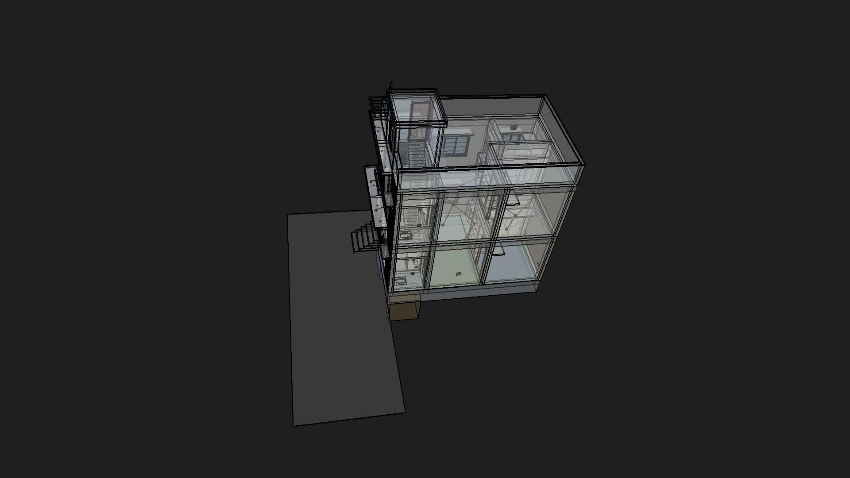
renders/cctv_complete_3storey_xray.png
