Pradeeparul2/house-plan/renders/cctv_east_facade_concealed.png

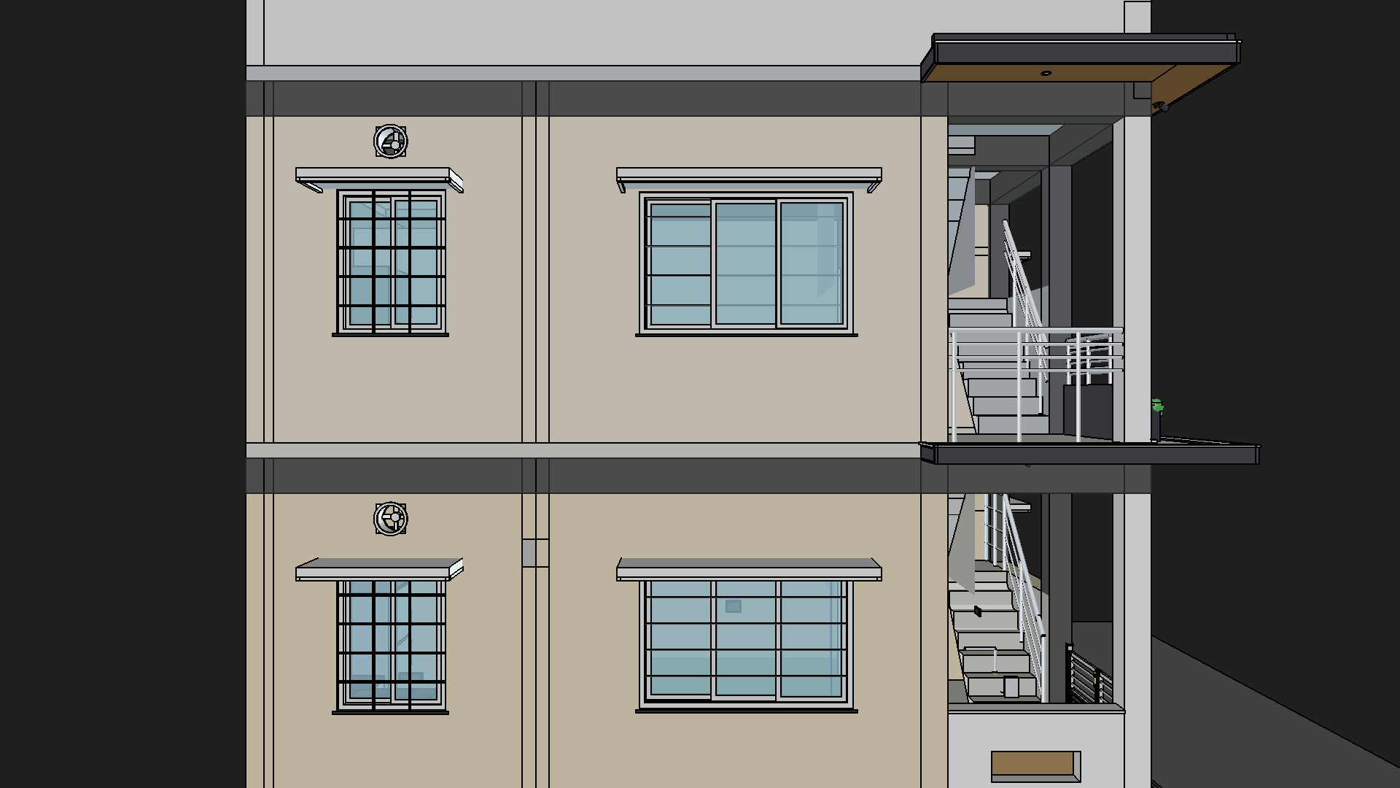
renders/cctv_east_facade_concealed.png
