Pradeeparul2/house-plan/renders/cctv_isolated_mep_iso.png

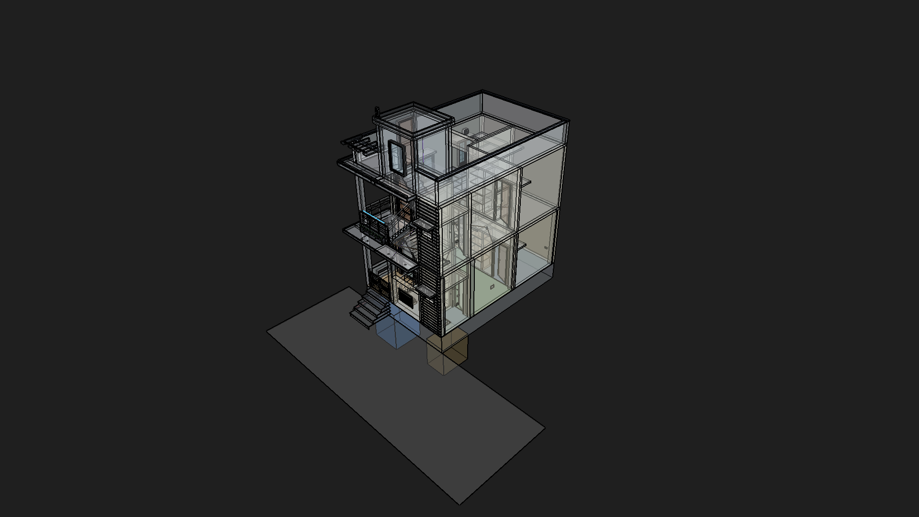
renders/cctv_isolated_mep_iso.png
