Pradeeparul2/house-plan/renders/cctv_wifi_conduit_full_schematic.png

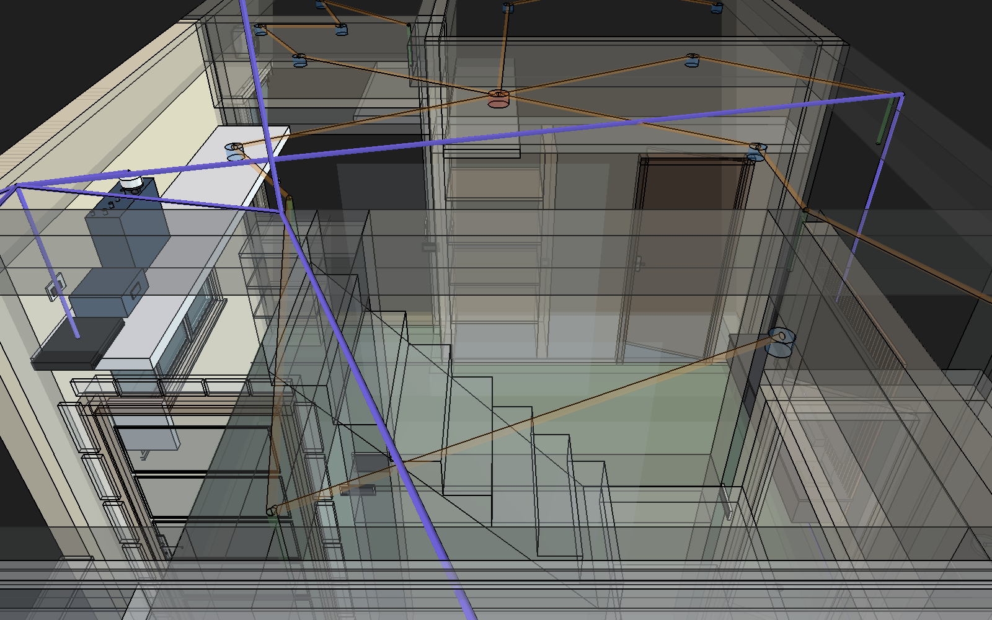
renders/cctv_wifi_conduit_full_schematic.png
