Pradeeparul2/house-plan/renders/column_clash_fixed_isometric.png

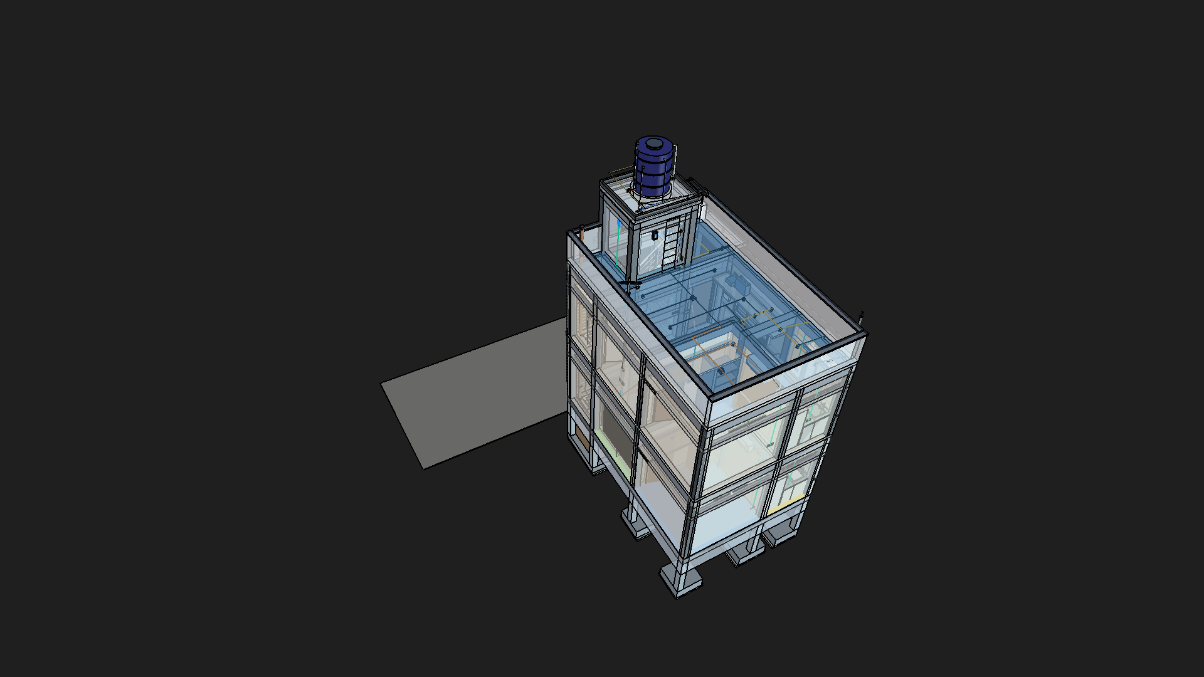
renders/column_clash_fixed_isometric.png
