Pradeeparul2/house-plan/renders/concealed_cctv_front.png

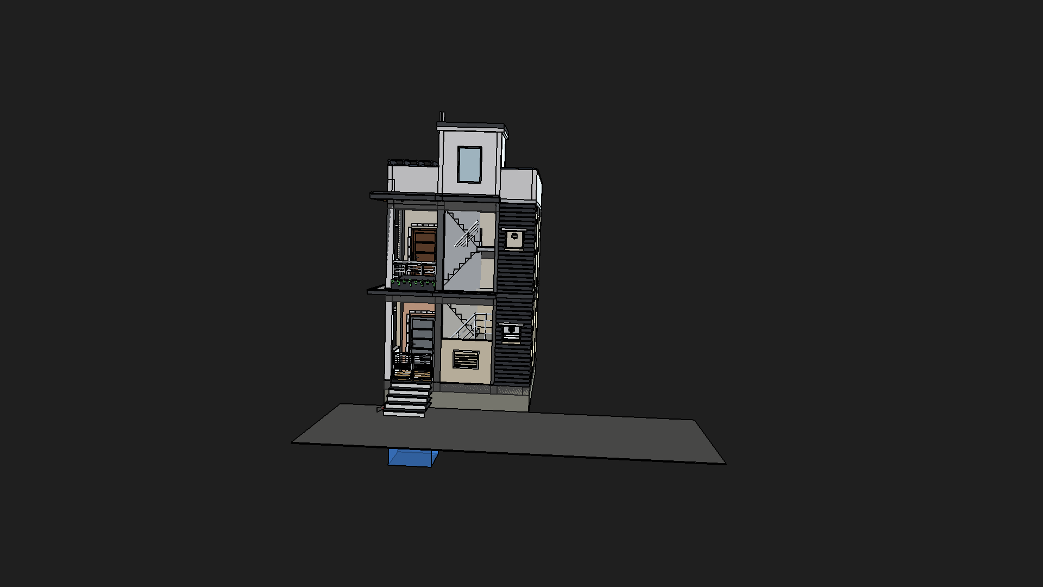
renders/concealed_cctv_front.png
