Pradeeparul2/house-plan/renders/crop_entry_area.png

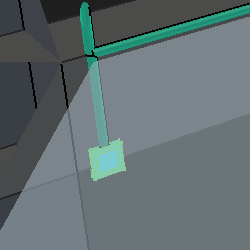
renders/crop_entry_area.png
