Pradeeparul2/house-plan/renders/crop_ff_light_rain_protection.png

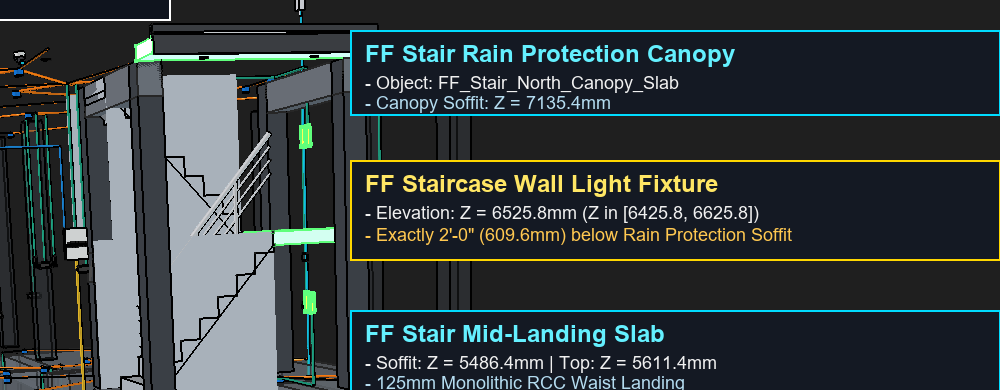
renders/crop_ff_light_rain_protection.png
