Pradeeparul2/house-plan/renders/crop_headroom_wall_light.png

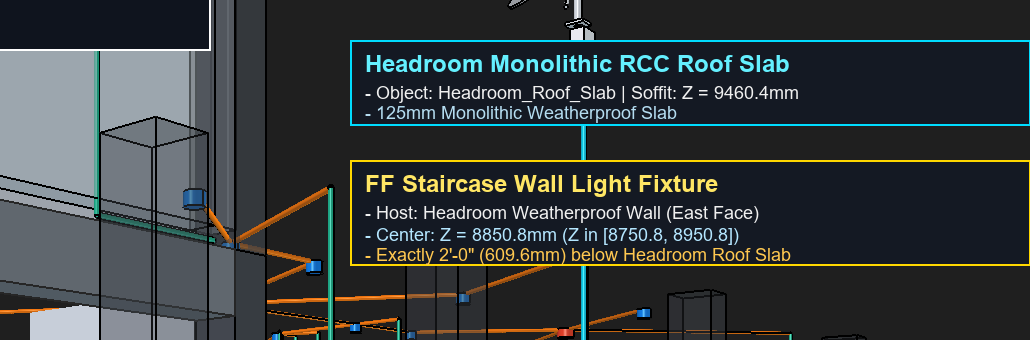
renders/crop_headroom_wall_light.png
