Pradeeparul2/house-plan/renders/crop_light_2ft_below_ff_landing.png

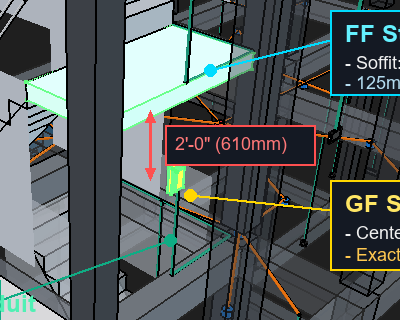
renders/crop_light_2ft_below_ff_landing.png
