Pradeeparul2/house-plan/renders/crop_light_fixture.png

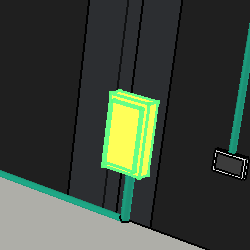
renders/crop_light_fixture.png
