Pradeeparul2/house-plan/renders/crop_under_stair_pump_power.png

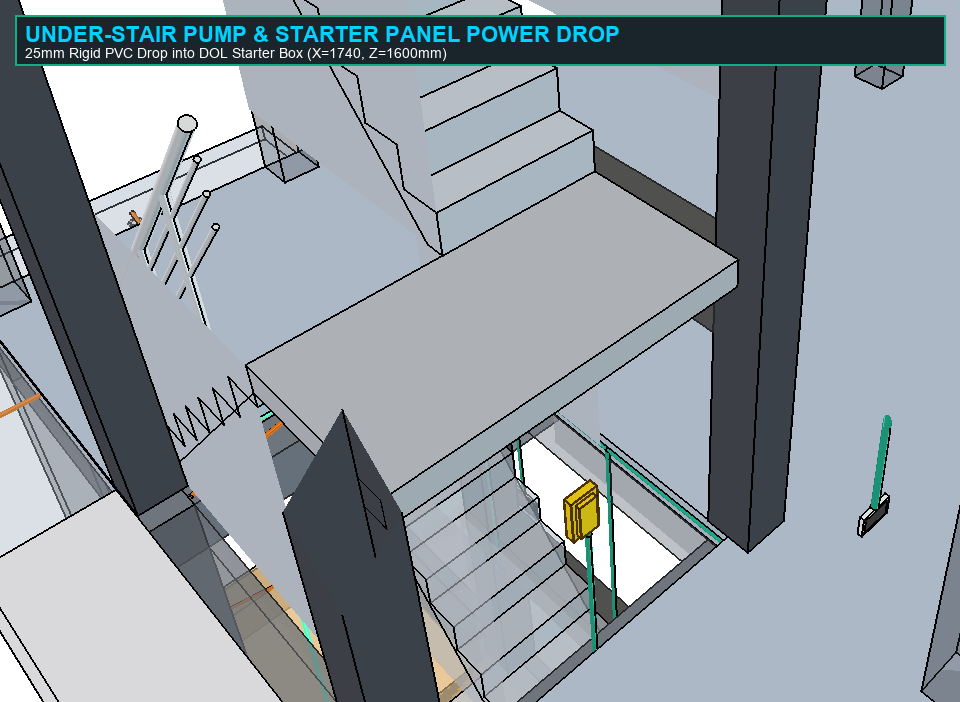
renders/crop_under_stair_pump_power.png
