Pradeeparul2/house-plan/renders/current_freecad_view.png

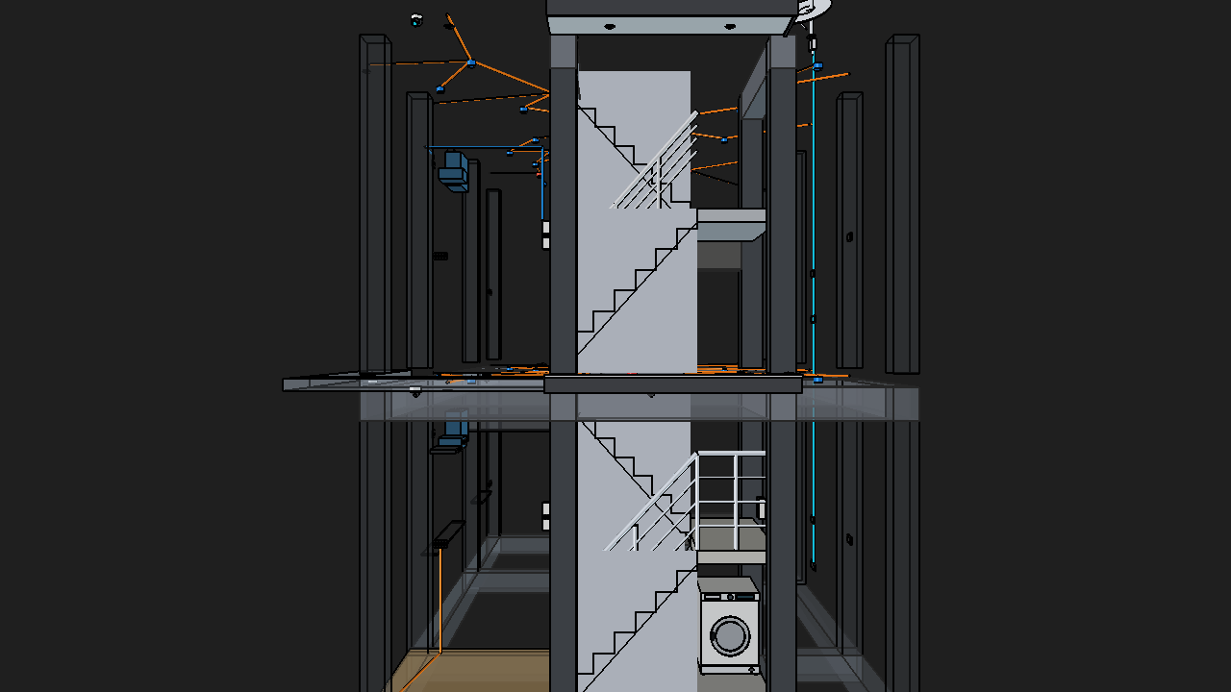
renders/current_freecad_view.png
