Pradeeparul2/house-plan/renders/dual_ups_two_storey_overview.png

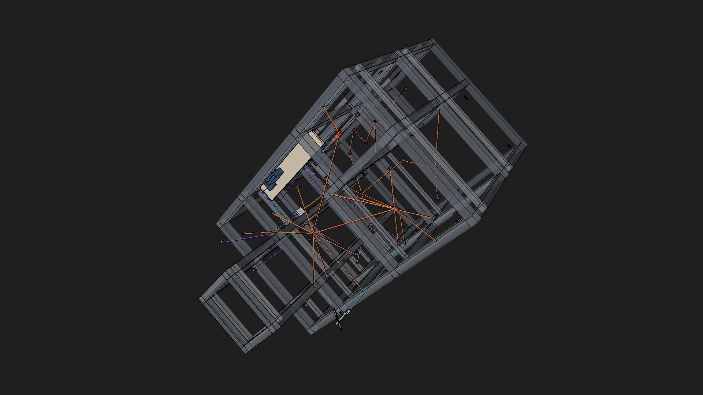
renders/dual_ups_two_storey_overview.png
