Pradeeparul2/house-plan/renders/east_elevation_lintels_sills.png

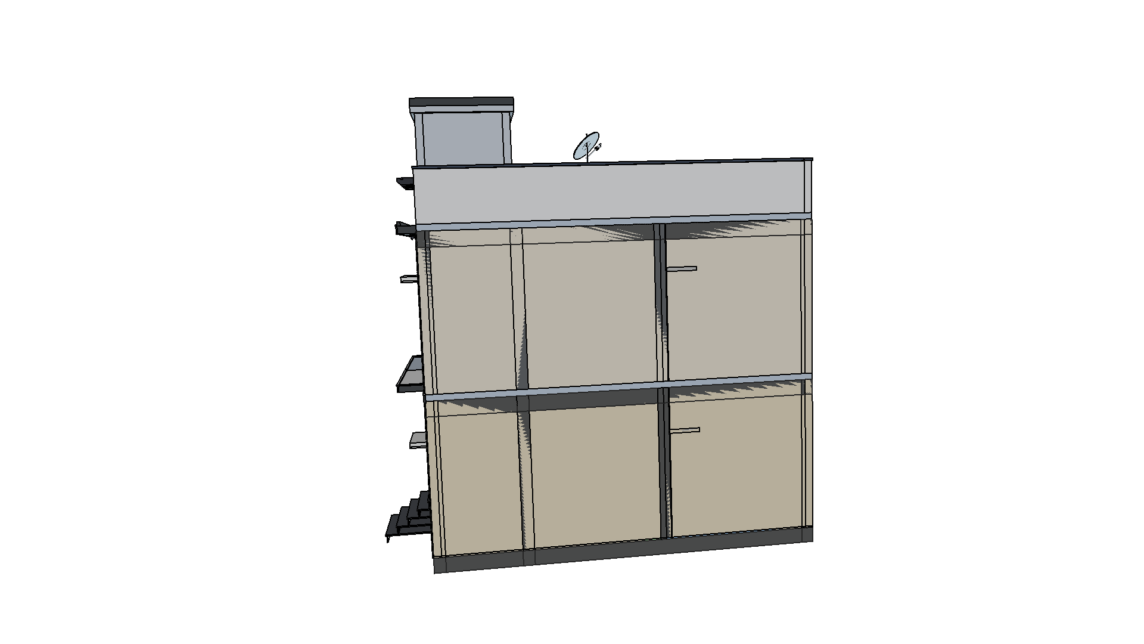
renders/east_elevation_lintels_sills.png
