Pradeeparul2/house-plan/renders/east_outer_parapet_pipeline.png

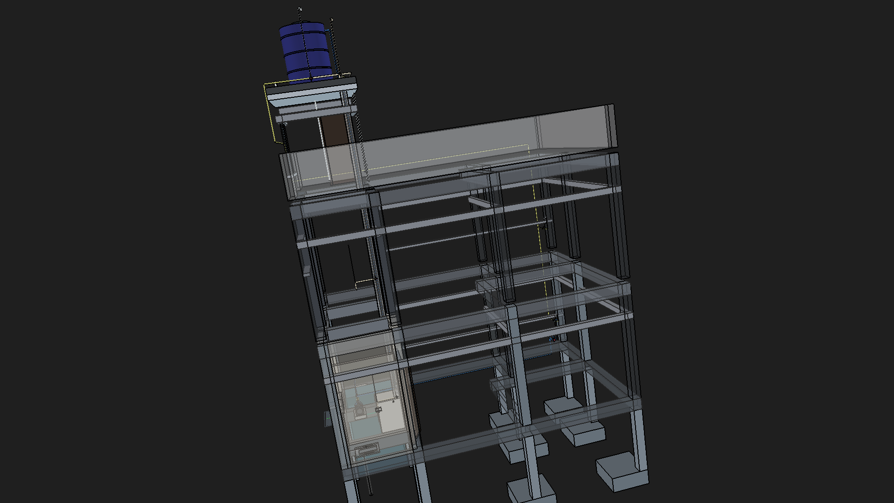
renders/east_outer_parapet_pipeline.png
