Pradeeparul2/house-plan/renders/east_parapet_kitchen_pipeline.png

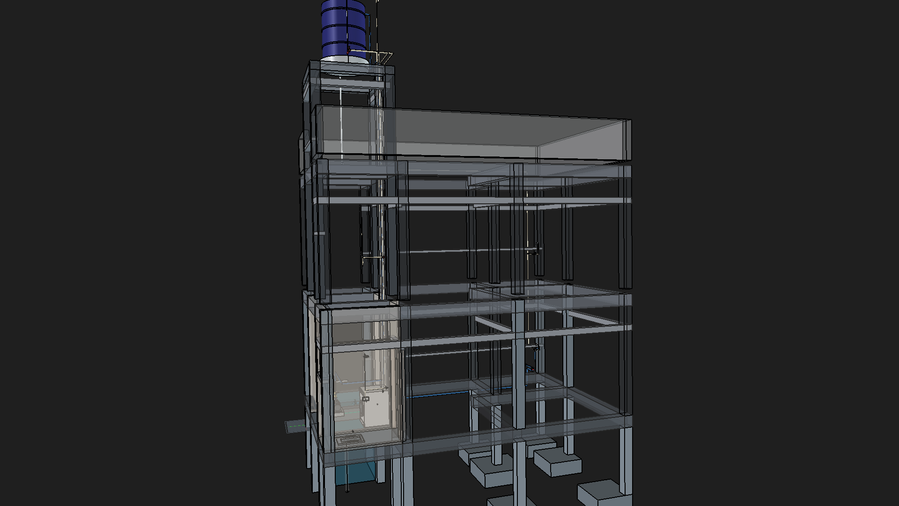
renders/east_parapet_kitchen_pipeline.png
