Pradeeparul2/house-plan/renders/east_side_switchbox_orange_pipe_explained.png

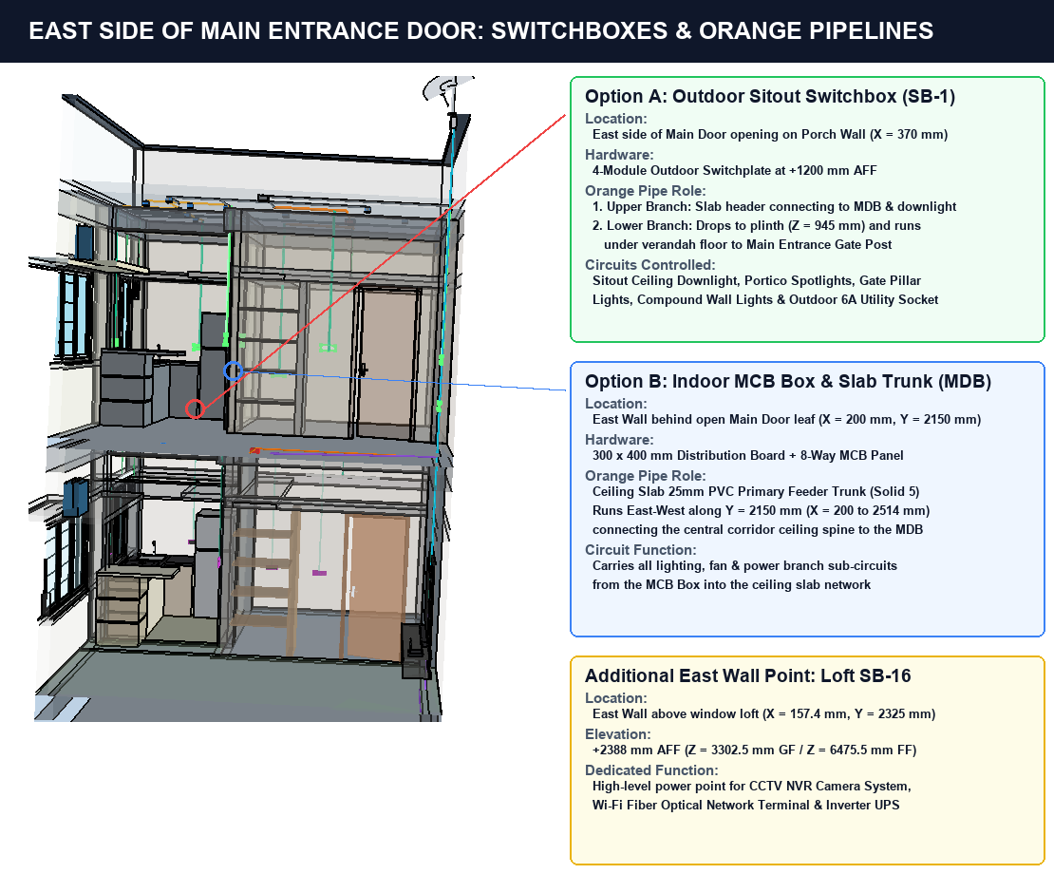
renders/east_side_switchbox_orange_pipe_explained.png
