Pradeeparul2/house-plan/renders/electrical_conduit_iso_tight.png

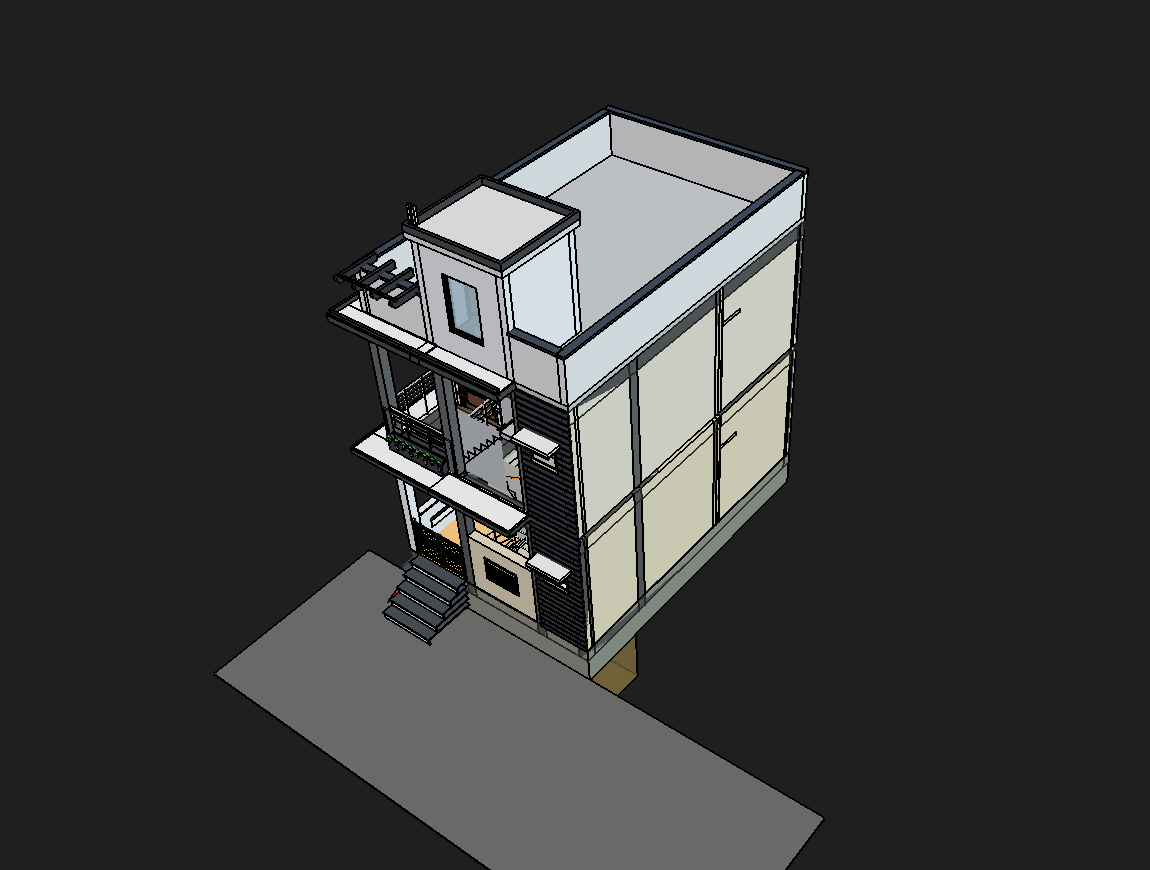
renders/electrical_conduit_iso_tight.png
