Pradeeparul2/house-plan/renders/electrical_conduits_to_switchboxes_overview.png

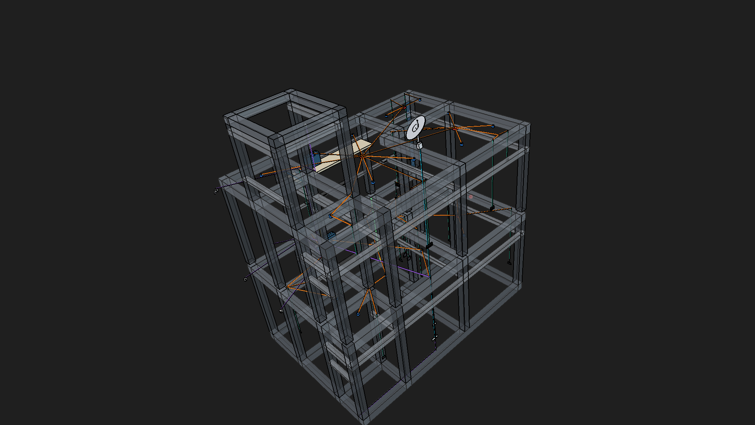
renders/electrical_conduits_to_switchboxes_overview.png
