Pradeeparul2/house-plan/renders/electrical_right_view_all_conduits.png

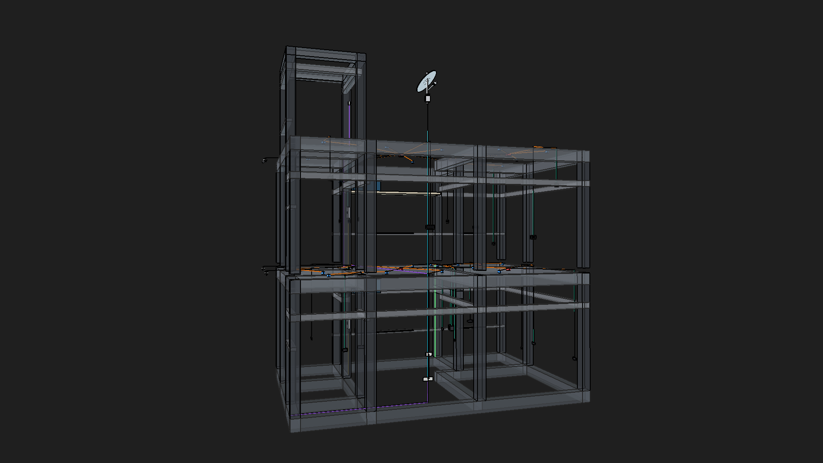
renders/electrical_right_view_all_conduits.png
