Pradeeparul2/house-plan/renders/ff_conduits_isometric_closeup.png

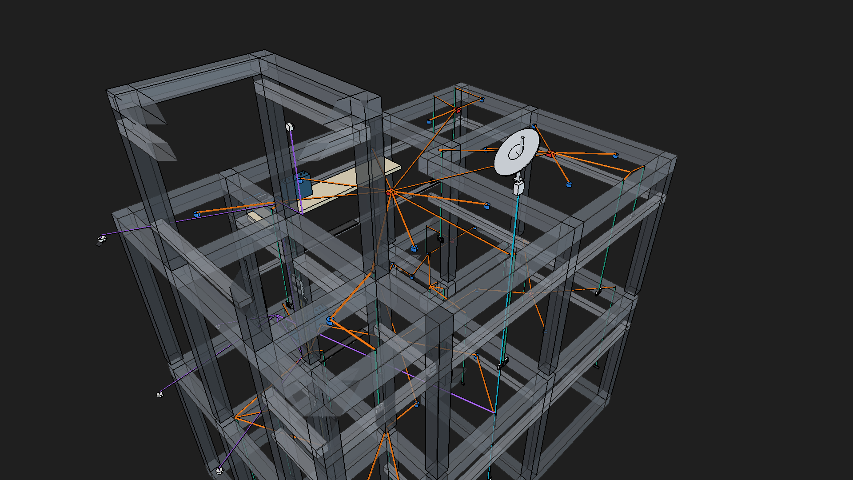
renders/ff_conduits_isometric_closeup.png
