Pradeeparul2/house-plan/renders/ff_electrical_plan_final_duplicate.png

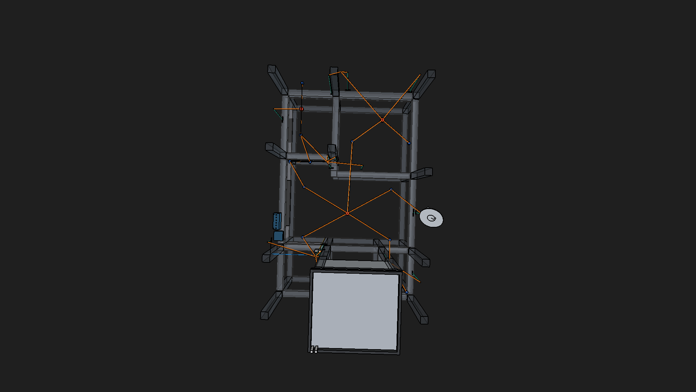
renders/ff_electrical_plan_final_duplicate.png
