Pradeeparul2/house-plan/renders/ff_entrance_stair_conduit_fixed_view1.png

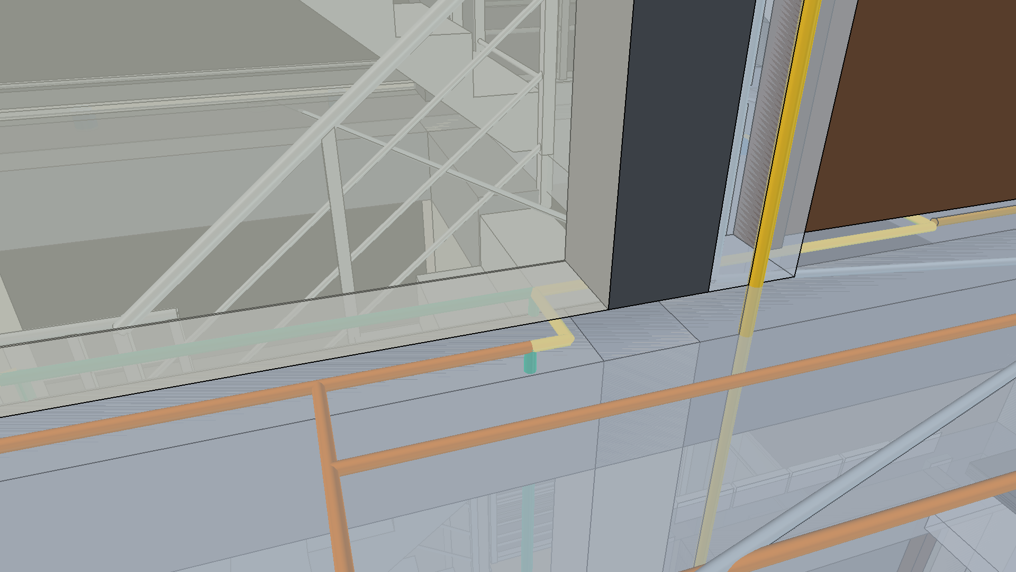
renders/ff_entrance_stair_conduit_fixed_view1.png
