Pradeeparul2/house-plan/renders/ff_entrance_stair_conduit_view2.png

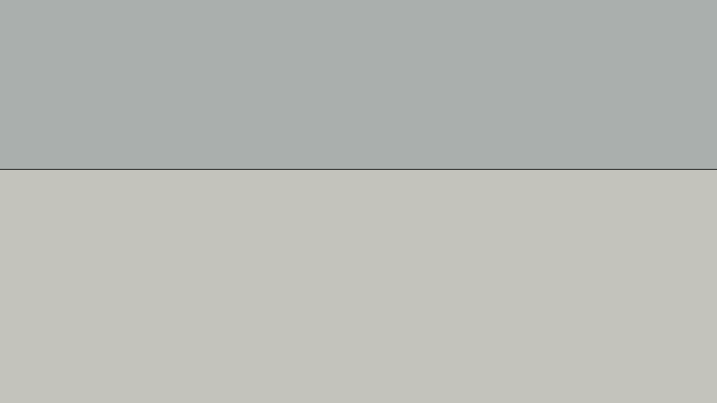
renders/ff_entrance_stair_conduit_view2.png
