Pradeeparul2/house-plan/renders/ff_gf_mcb_boxes_aligned_annotated.png

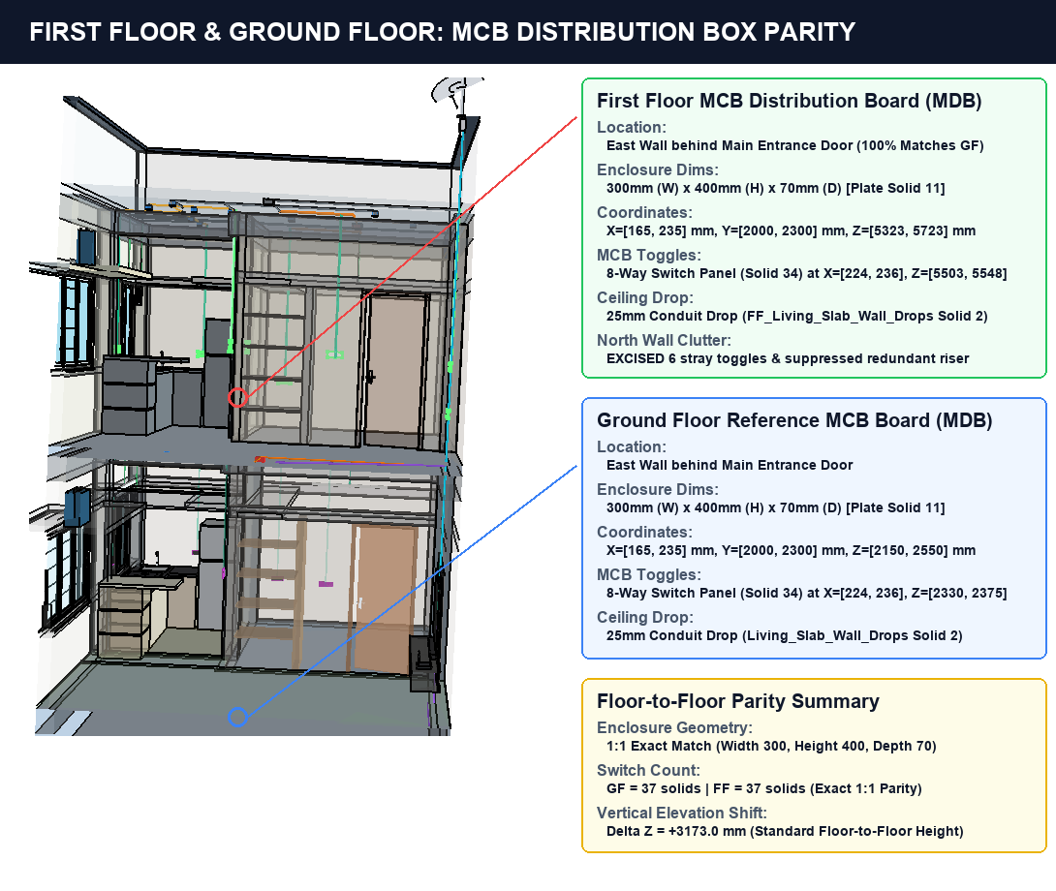
renders/ff_gf_mcb_boxes_aligned_annotated.png
