Pradeeparul2/house-plan/renders/ff_living_room_north_wall_solid.png

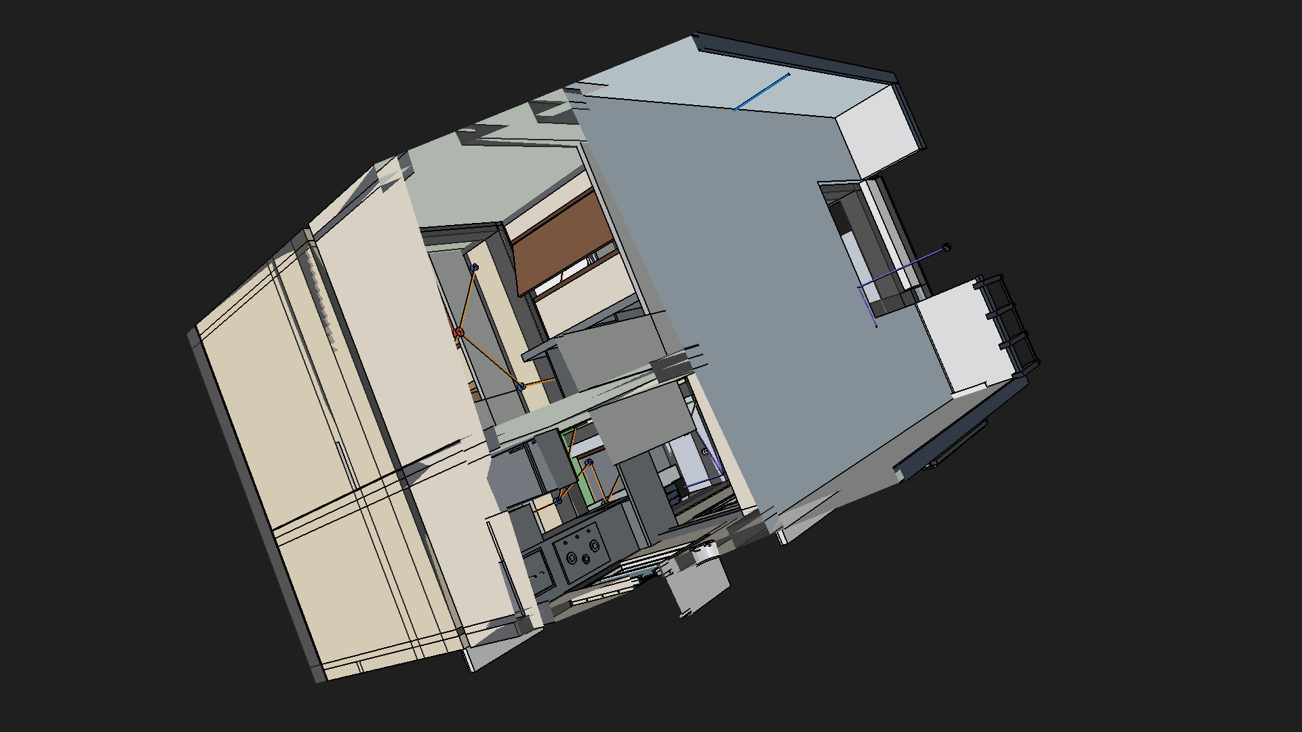
renders/ff_living_room_north_wall_solid.png
