Pradeeparul2/house-plan/renders/ff_north_no_window_balcony_stair.png

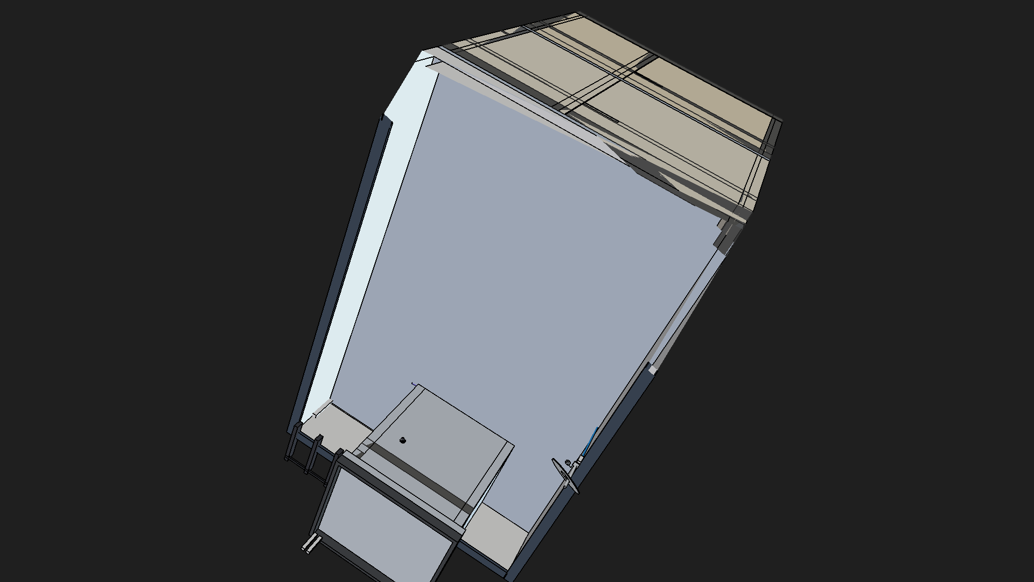
renders/ff_north_no_window_balcony_stair.png
