Pradeeparul2/house-plan/renders/ff_north_no_window_elevation.png

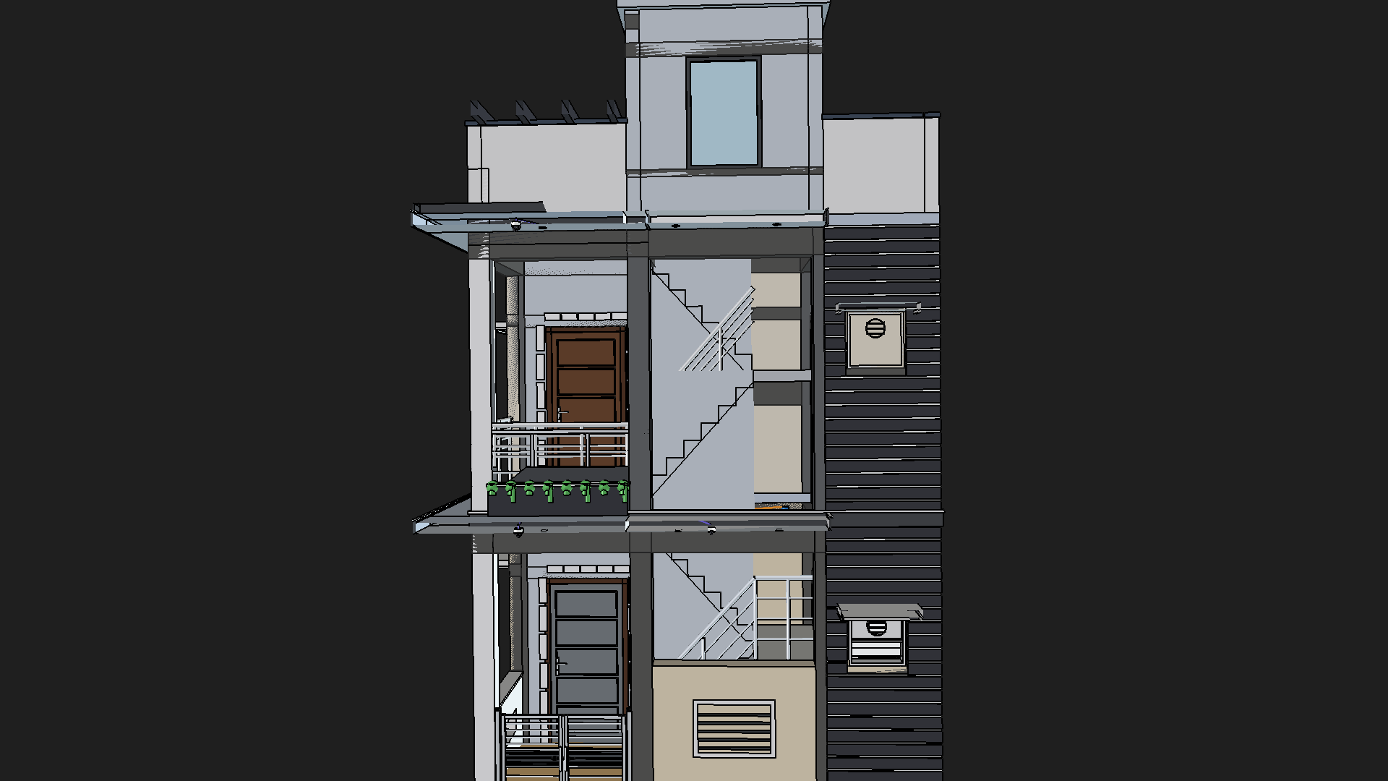
renders/ff_north_no_window_elevation.png
