Pradeeparul2/house-plan/renders/ff_rear_bedroom_kitchen_conduits.png

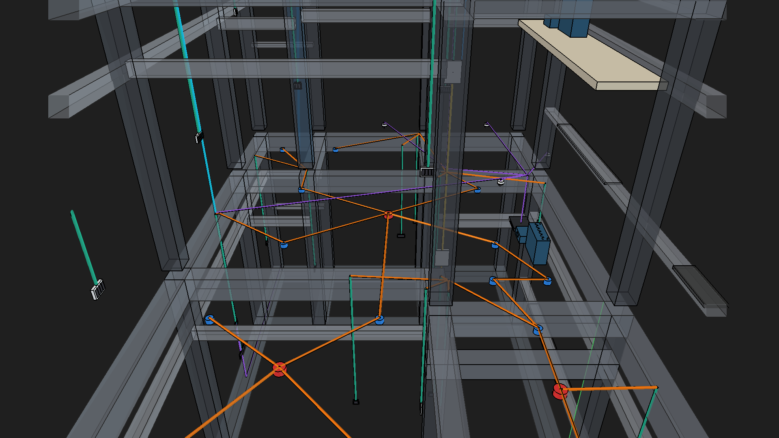
renders/ff_rear_bedroom_kitchen_conduits.png
