Pradeeparul2/house-plan/renders/ff_stair_entrance_cleared_view2.png

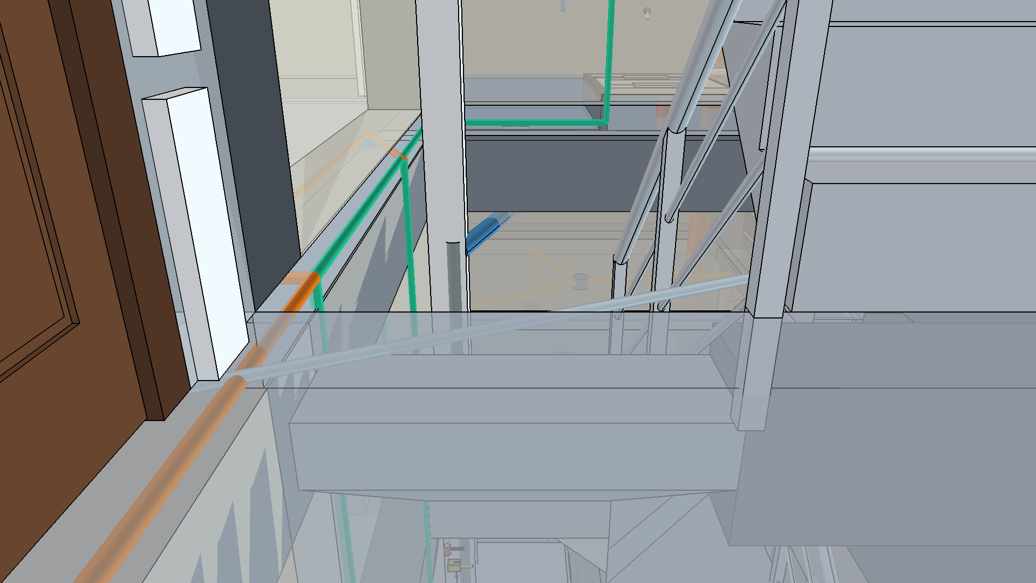
renders/ff_stair_entrance_cleared_view2.png
