Pradeeparul2/house-plan/renders/ff_stair_light_rain_protection_annotated.png

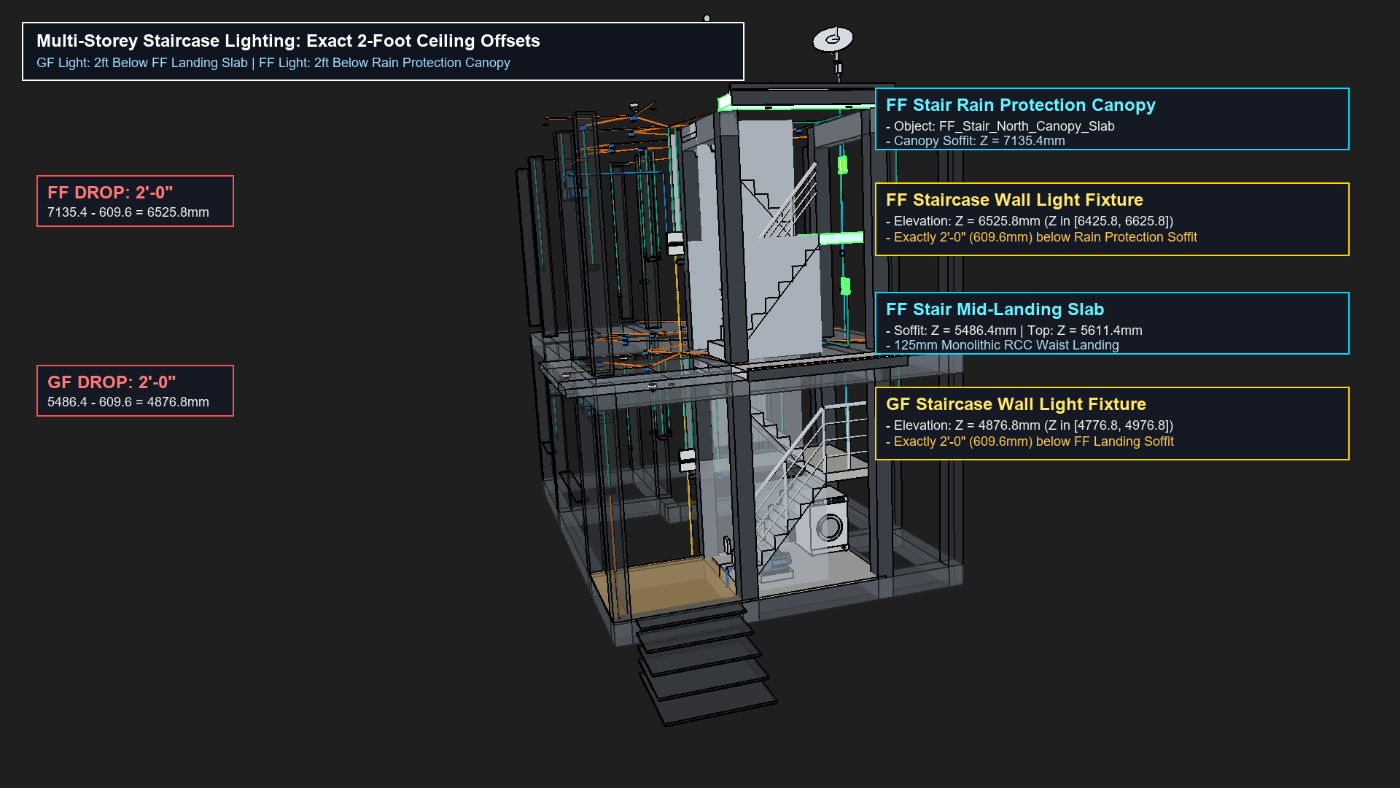
renders/ff_stair_light_rain_protection_annotated.png
