Pradeeparul2/house-plan/renders/ff_true_east_elevation.png

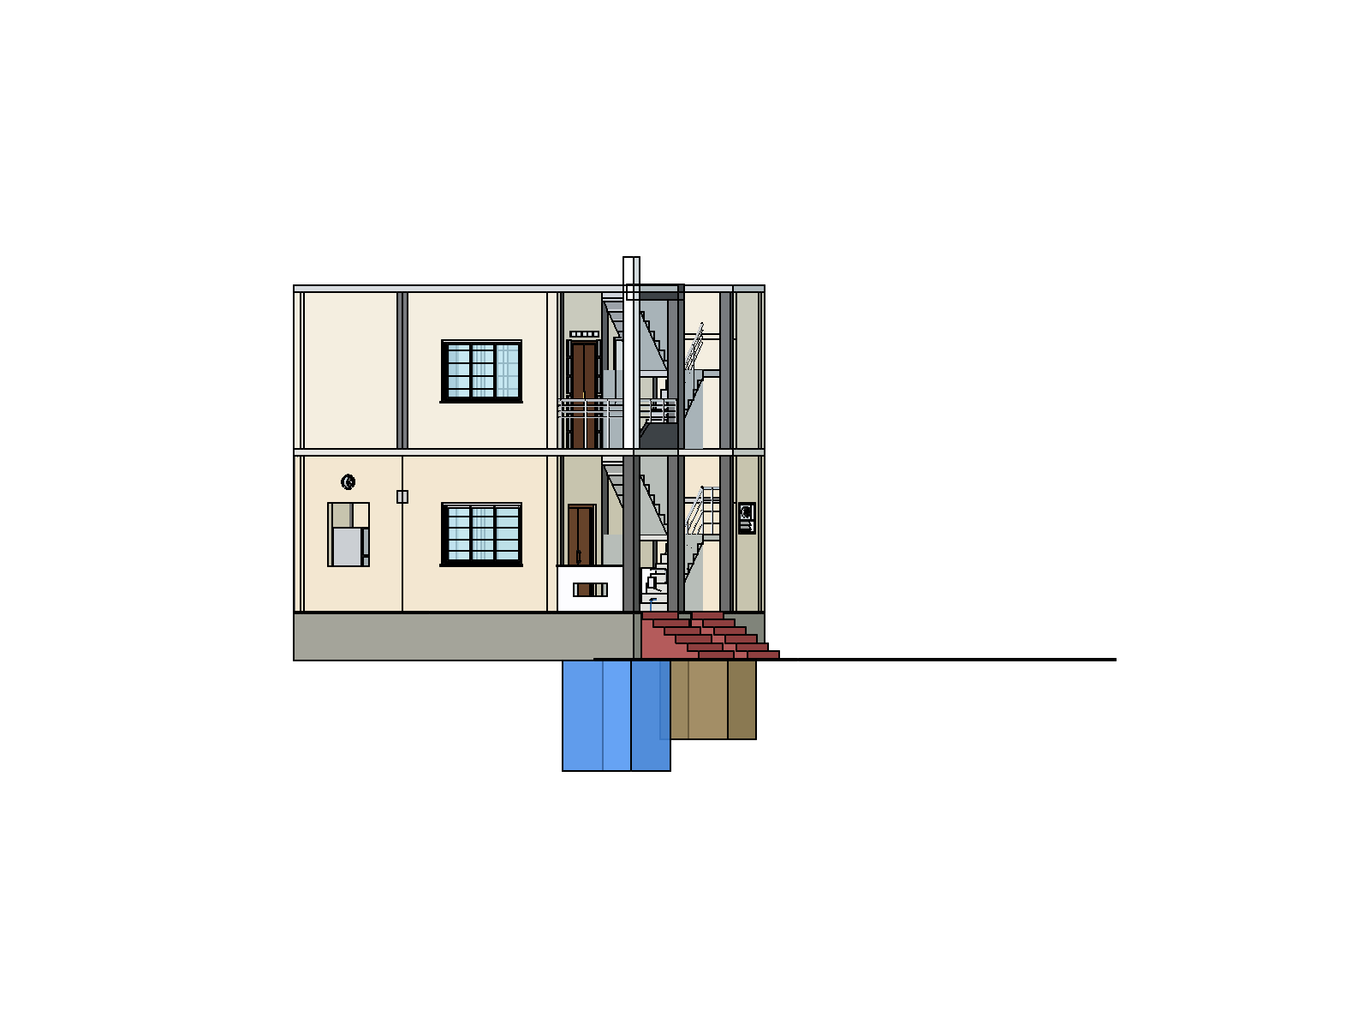
renders/ff_true_east_elevation.png
