Pradeeparul2/house-plan/renders/first_floor_north_closeup.png

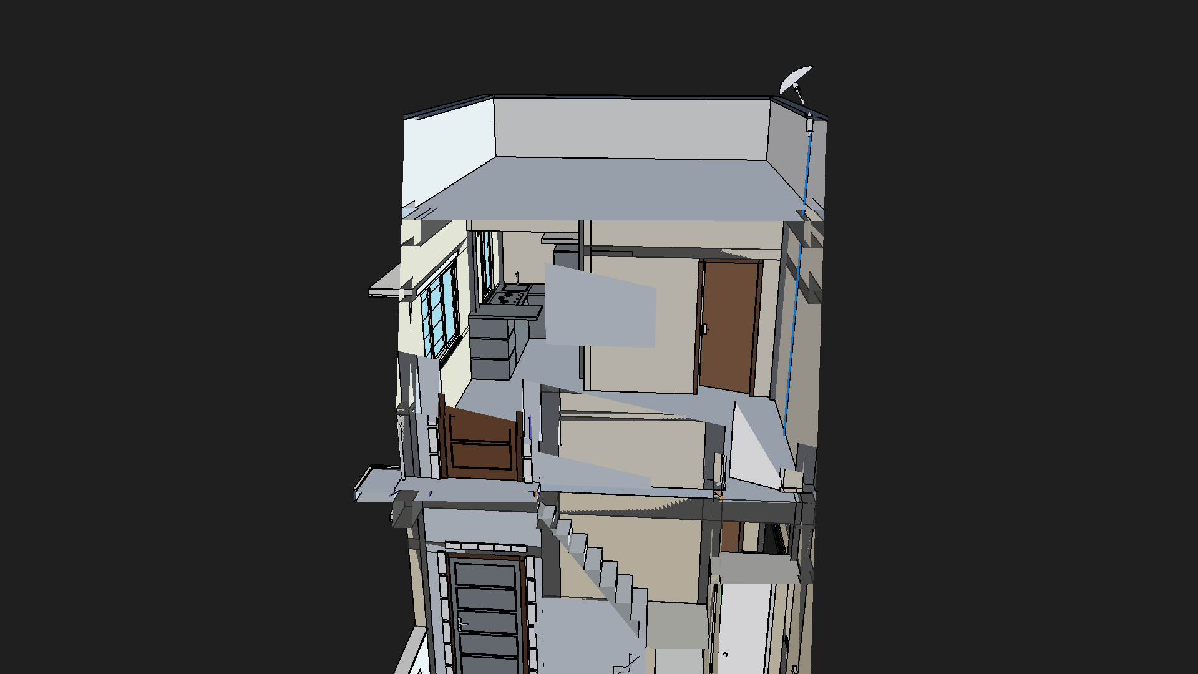
renders/first_floor_north_closeup.png
