Pradeeparul2/house-plan/renders/freecad_columns_and_beams_only.png

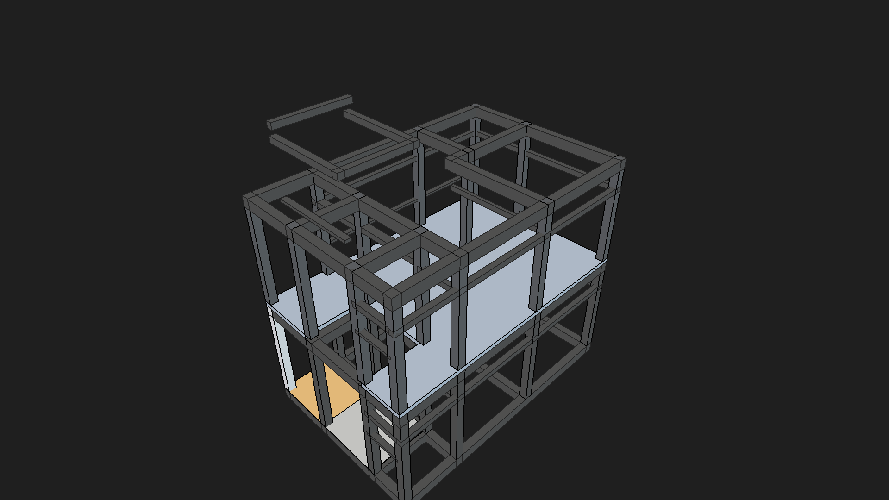
renders/freecad_columns_and_beams_only.png
