Pradeeparul2/house-plan/renders/freecad_gui_cctv_tree_scrolled.png

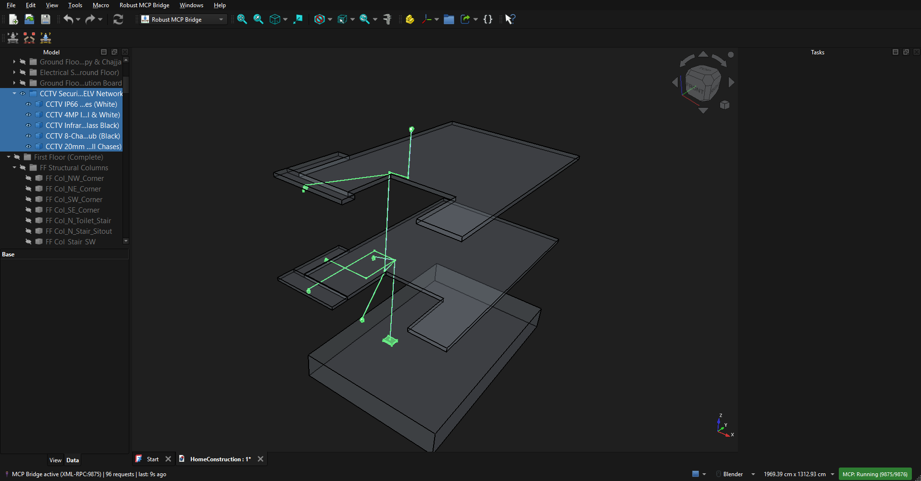
renders/freecad_gui_cctv_tree_scrolled.png
