Pradeeparul2/house-plan/renders/freecad_gui_dish_pipeline.png

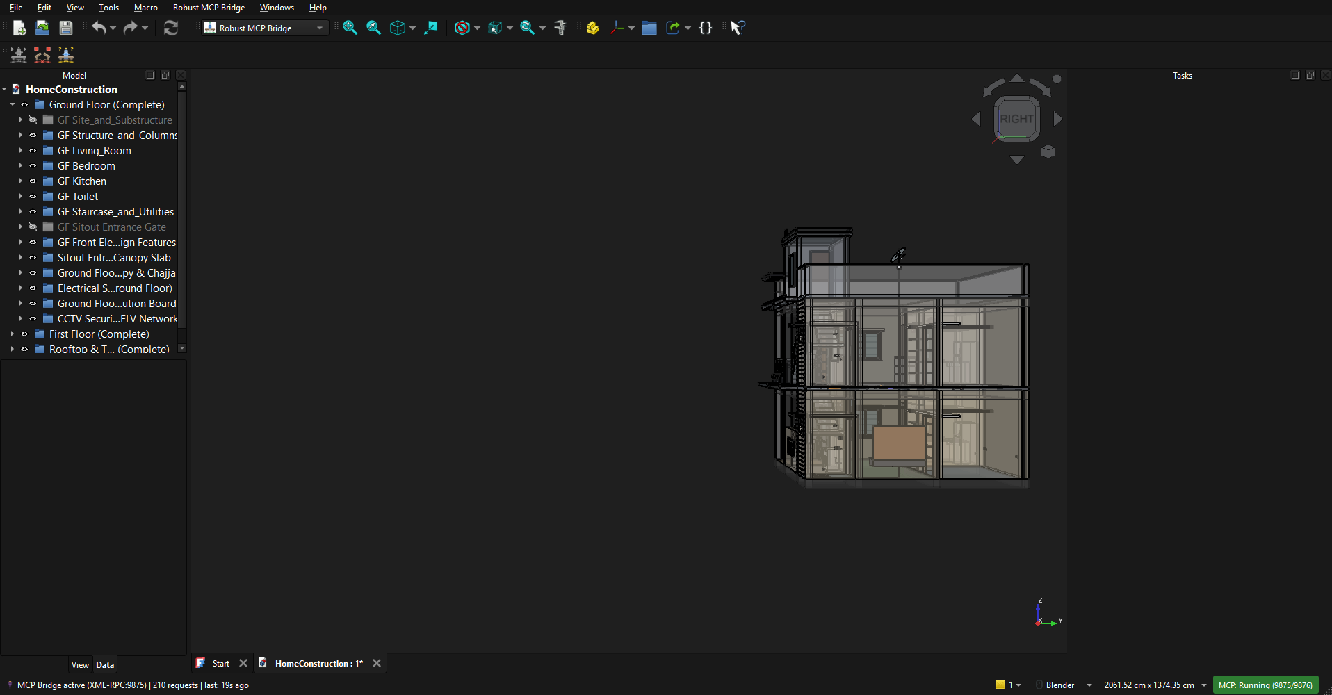
renders/freecad_gui_dish_pipeline.png
