Pradeeparul2/house-plan/renders/freecad_gui_single_door.png

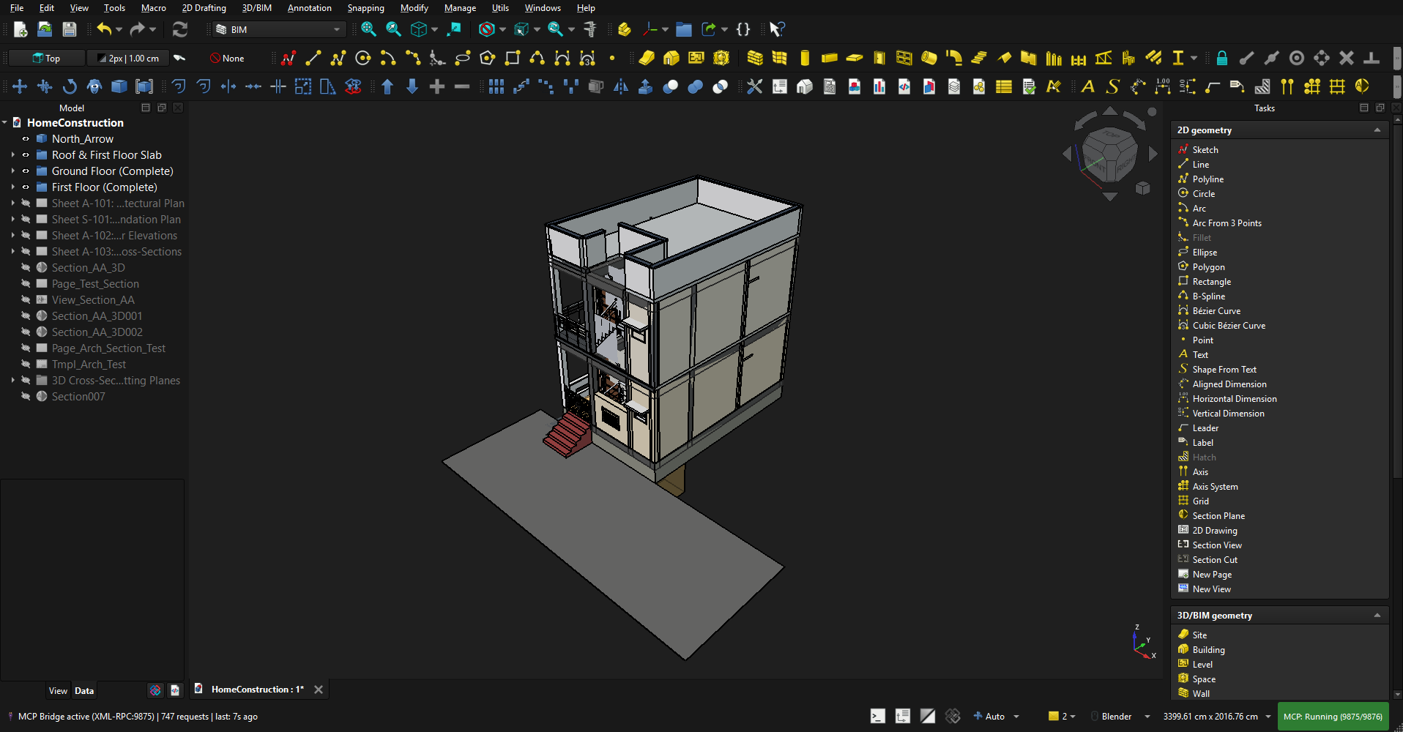
renders/freecad_gui_single_door.png
