Pradeeparul2/house-plan/renders/freecad_mainwindow_active.png

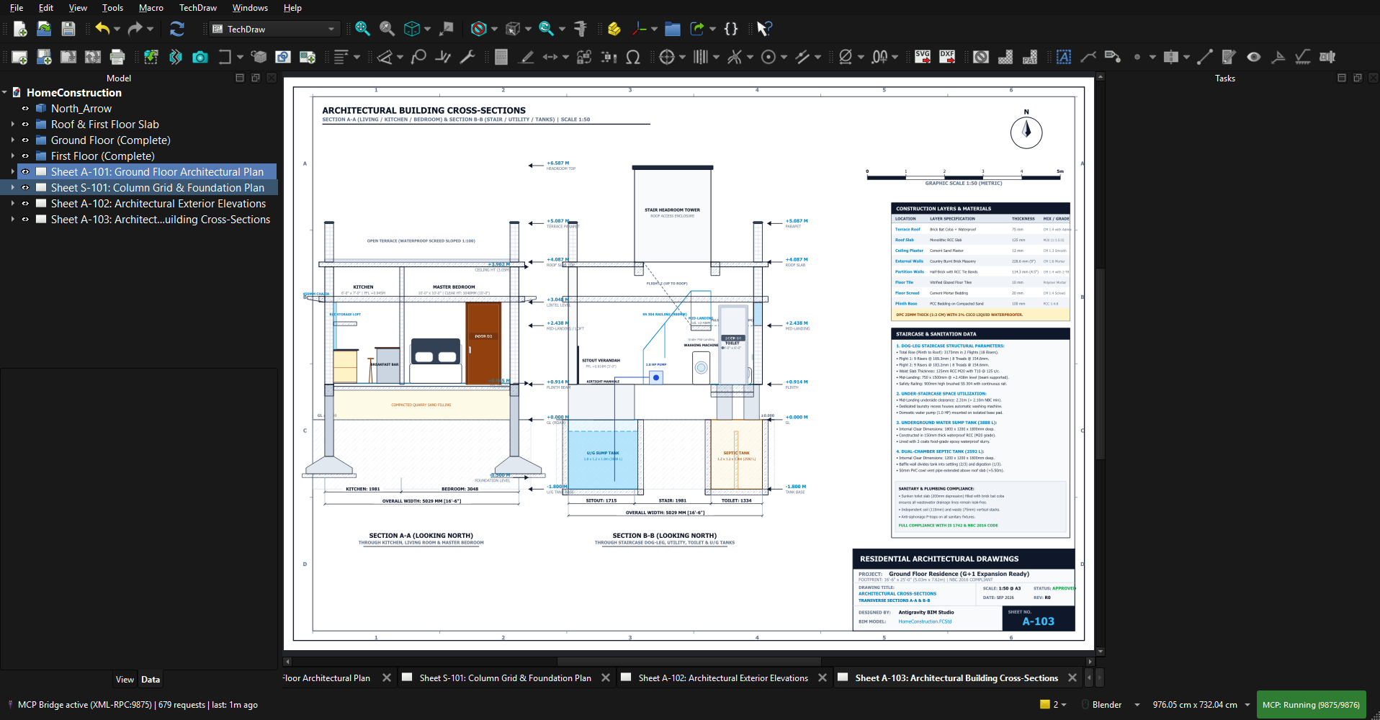
renders/freecad_mainwindow_active.png
