Pradeeparul2/house-plan/renders/freecad_structural_frame_styled.png

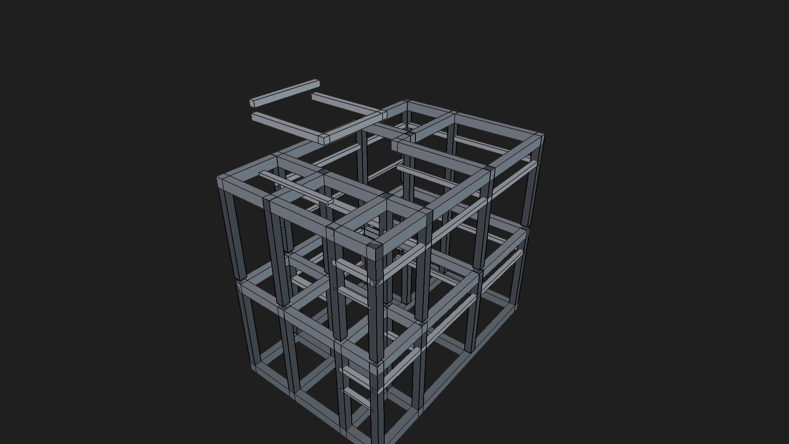
renders/freecad_structural_frame_styled.png
