Pradeeparul2/house-plan/renders/front_elevation_mystic_dream_white_oracle.jpg

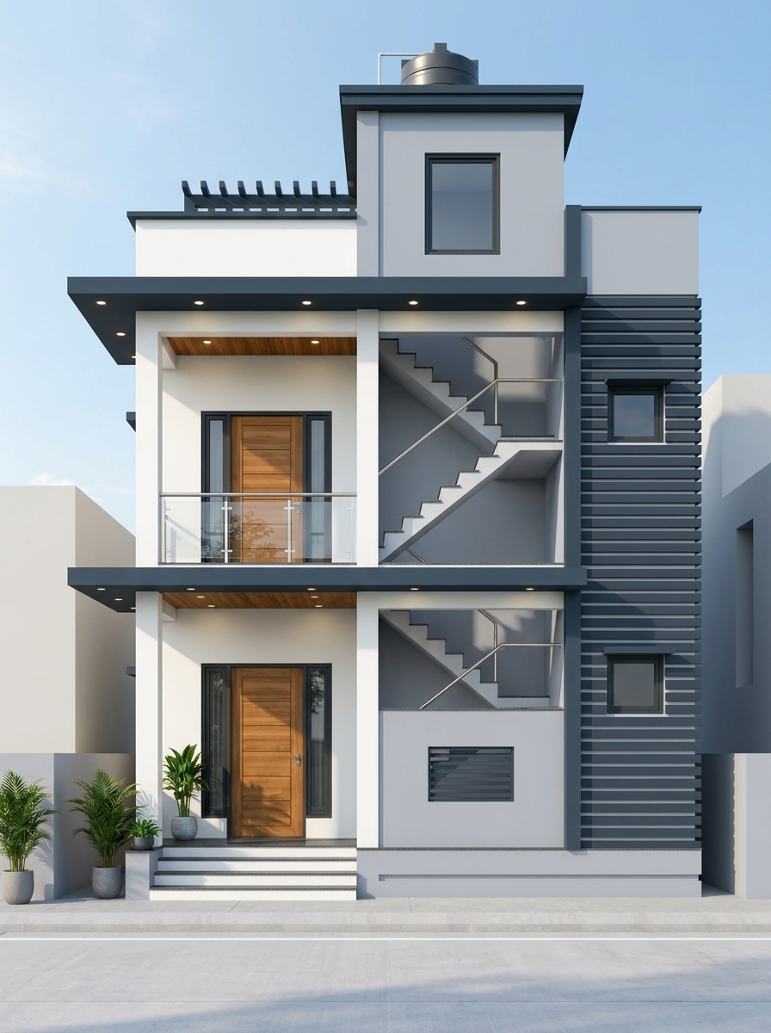
renders/front_elevation_mystic_dream_white_oracle.jpg
