Pradeeparul2/house-plan/renders/front_elevation_walls_100_visible.png

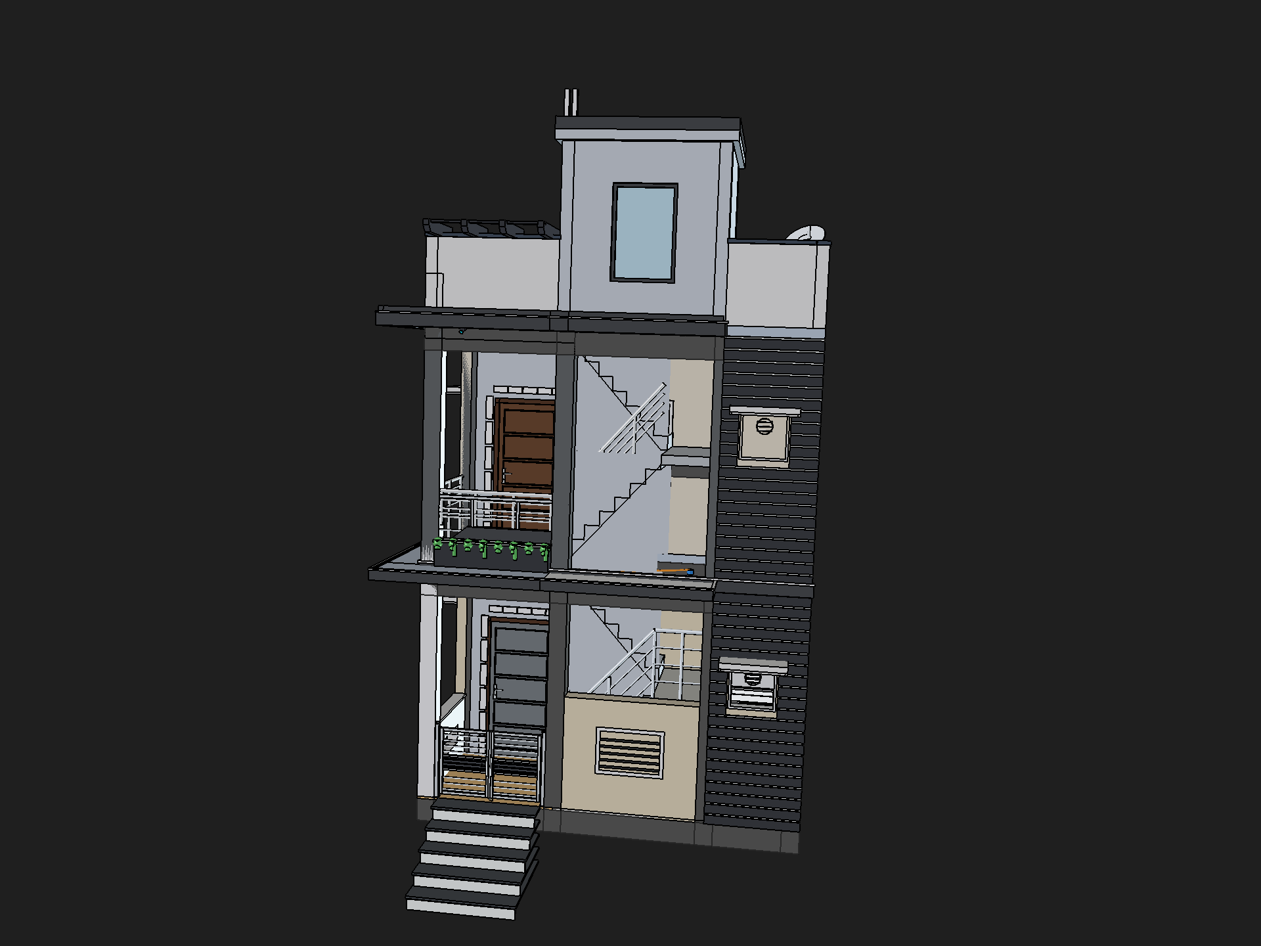
renders/front_elevation_walls_100_visible.png
