Pradeeparul2/house-plan/renders/full_width_east_loft_perspective.png

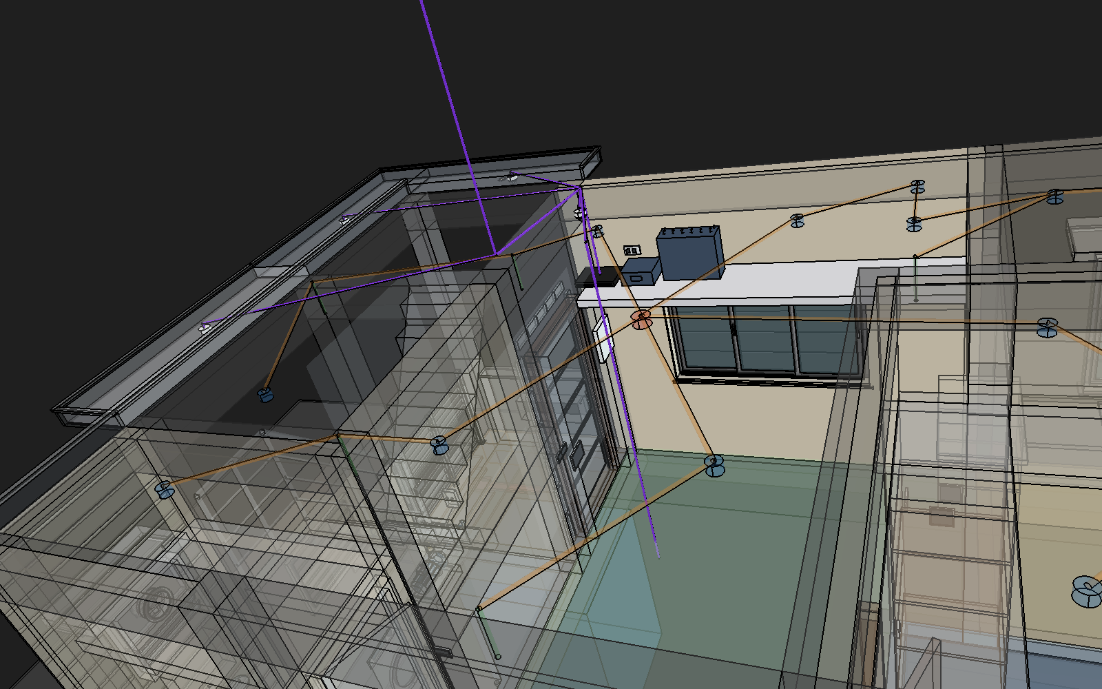
renders/full_width_east_loft_perspective.png
