Pradeeparul2/house-plan/renders/gf_bedroom_window_closeup.png

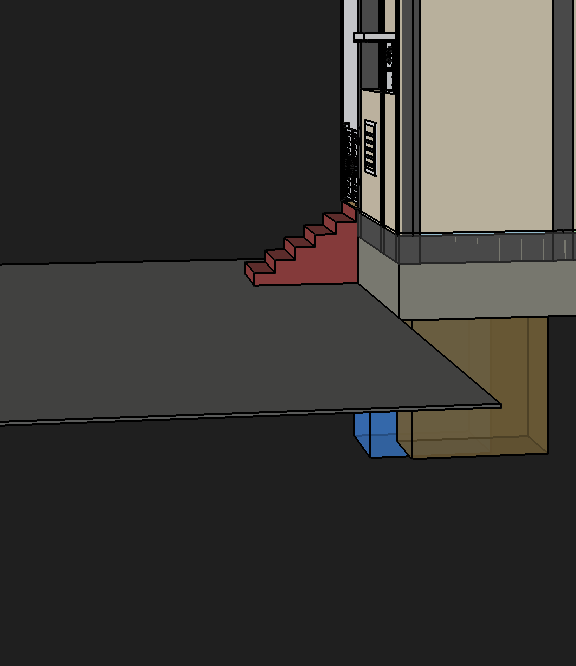
renders/gf_bedroom_window_closeup.png
