Pradeeparul2/house-plan/renders/gf_conduits_to_switchboxes_closeup.png

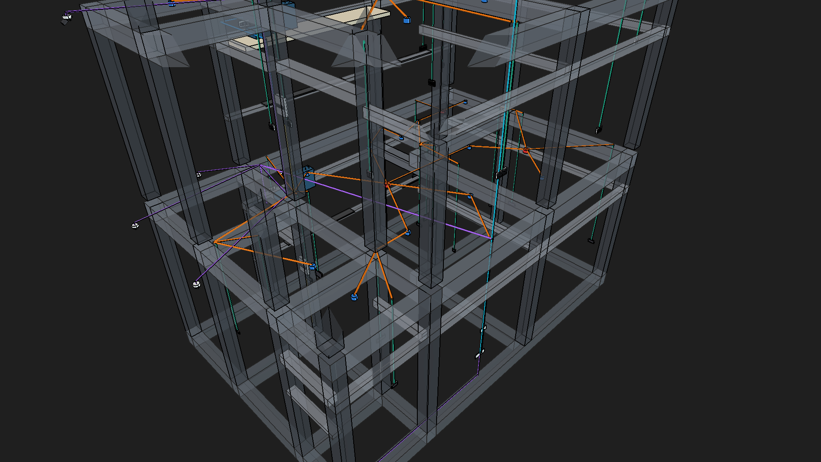
renders/gf_conduits_to_switchboxes_closeup.png
