Pradeeparul2/house-plan/renders/gf_electrical_conduit_plan_tight.png

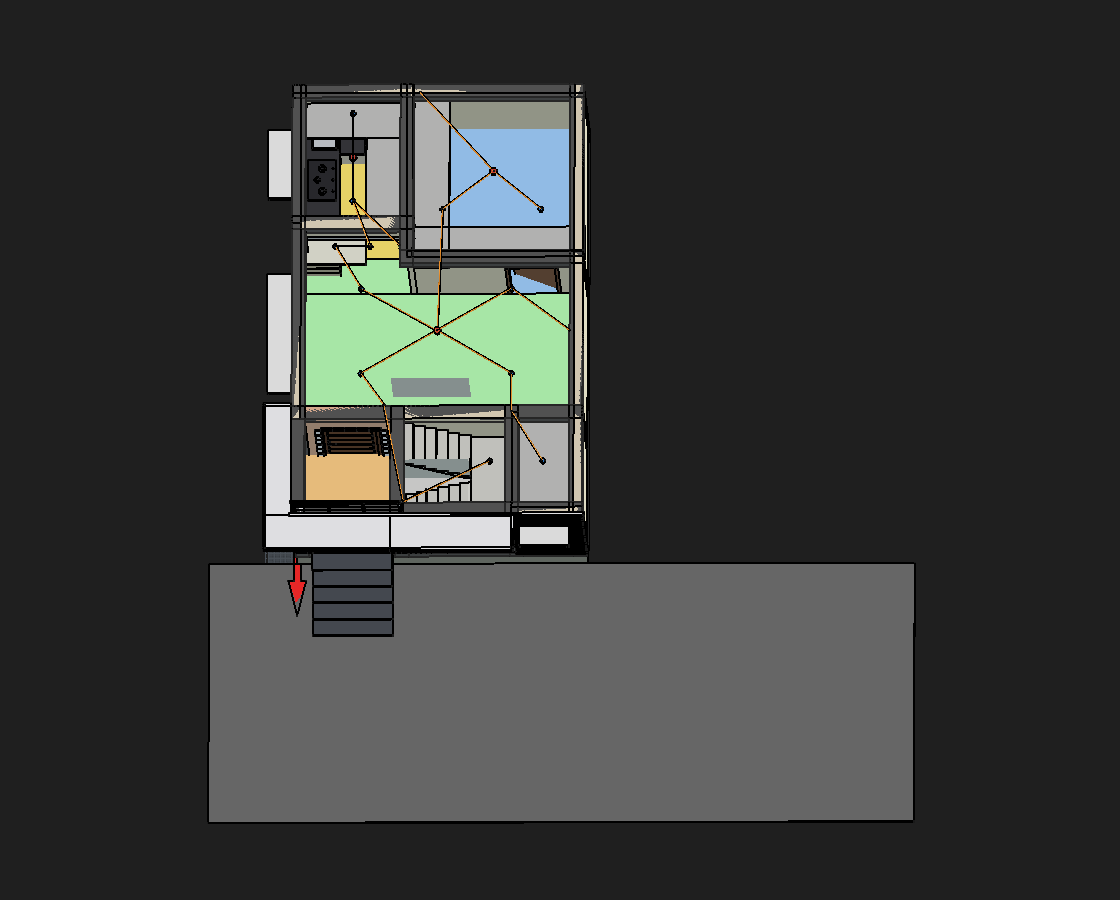
renders/gf_electrical_conduit_plan_tight.png
