Pradeeparul2/house-plan/renders/gf_electrical_conduit_zoom_tight.png

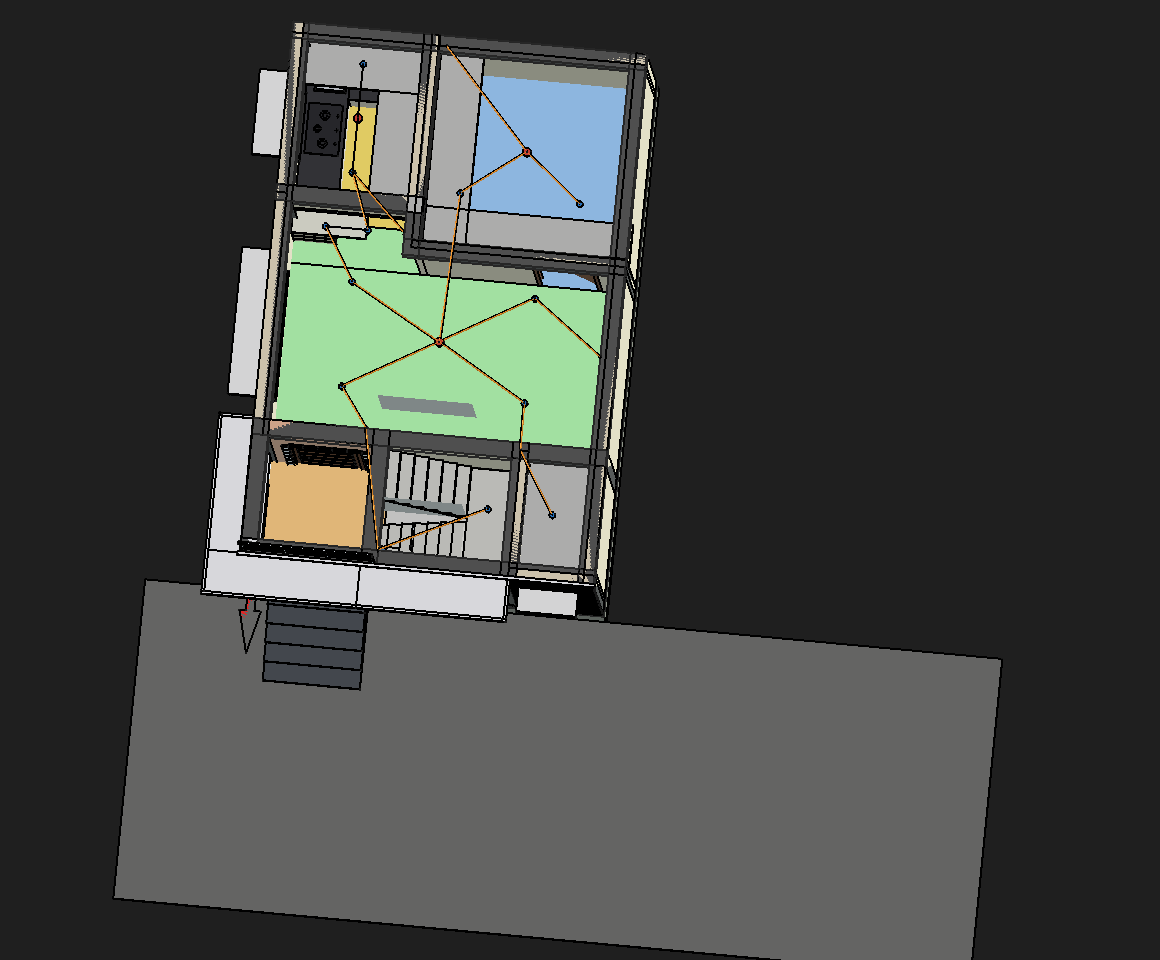
renders/gf_electrical_conduit_zoom_tight.png
