Pradeeparul2/house-plan/renders/gf_electrical_plan_top_view.png

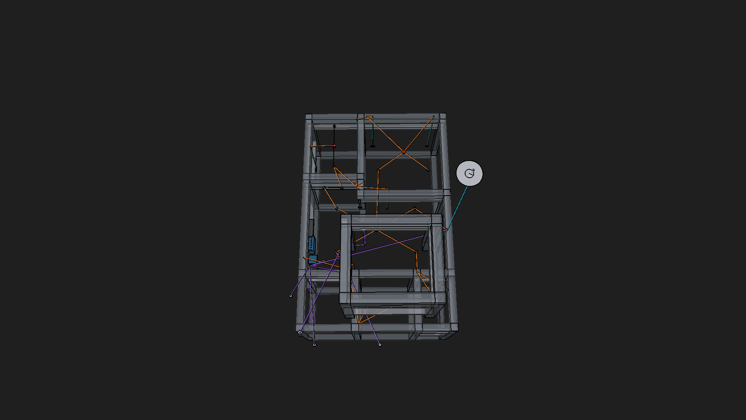
renders/gf_electrical_plan_top_view.png
