Pradeeparul2/house-plan/renders/gf_elev_front_cropped.png

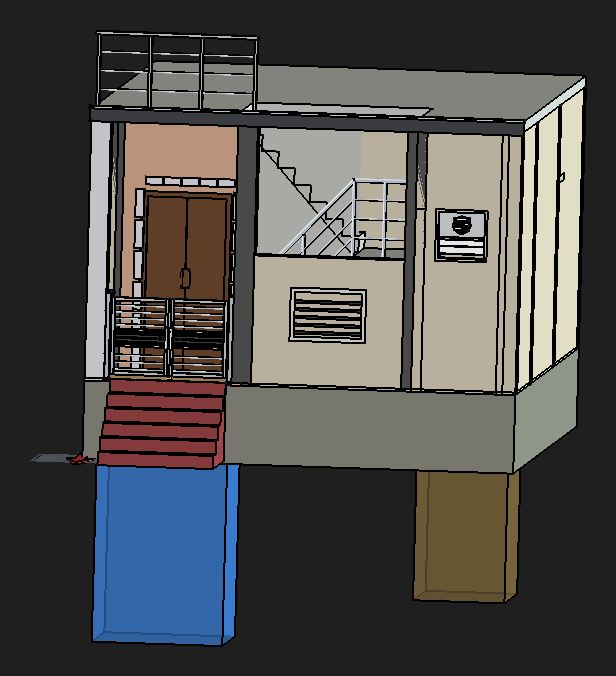
renders/gf_elev_front_cropped.png
