Pradeeparul2/house-plan/renders/gf_elev_persp_cropped.png

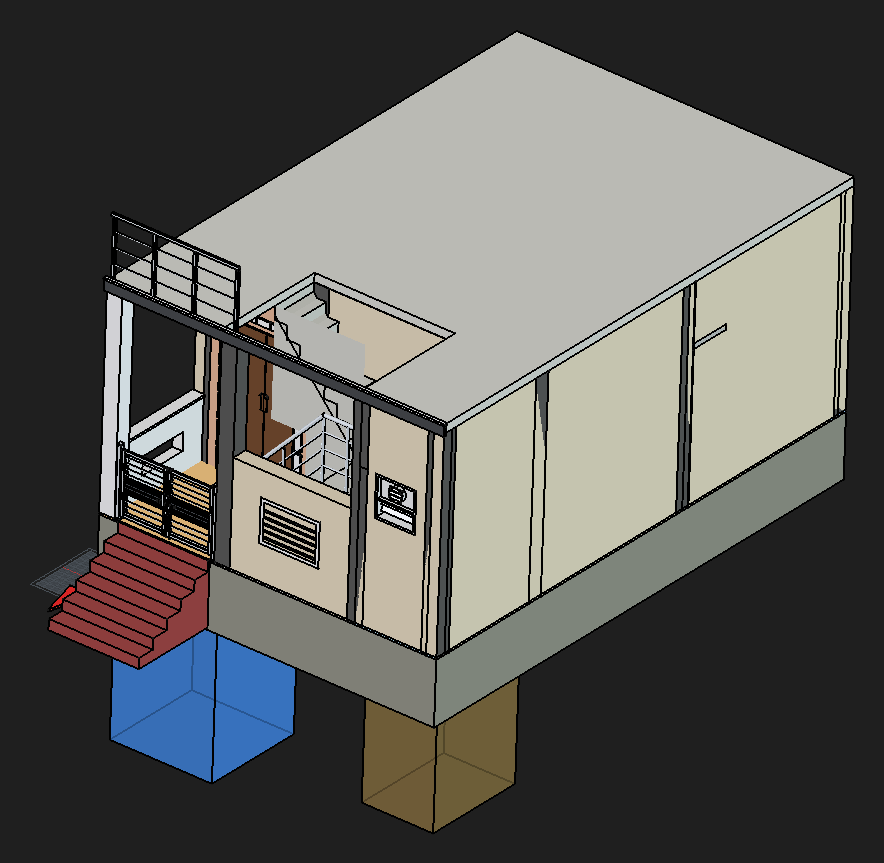
renders/gf_elev_persp_cropped.png
