Pradeeparul2/house-plan/renders/gf_interior_cutaway_cropped.png

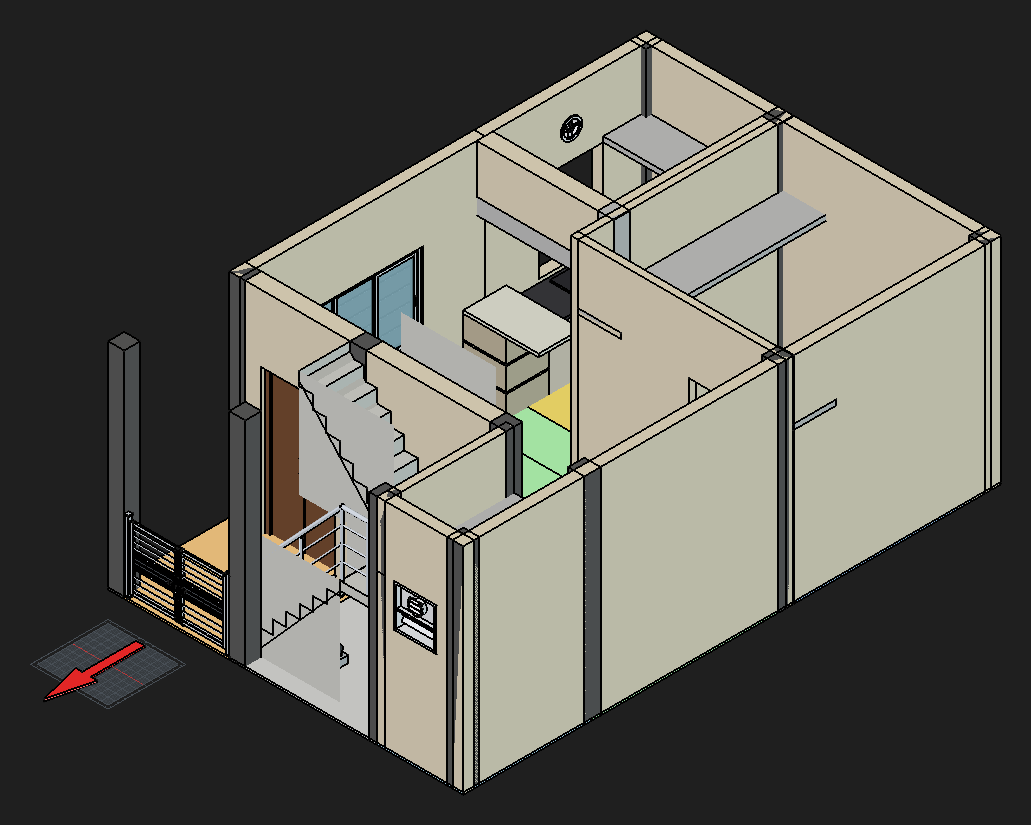
renders/gf_interior_cutaway_cropped.png
