Pradeeparul2/house-plan/renders/gf_kitchen_under_sink_valve_xray.png

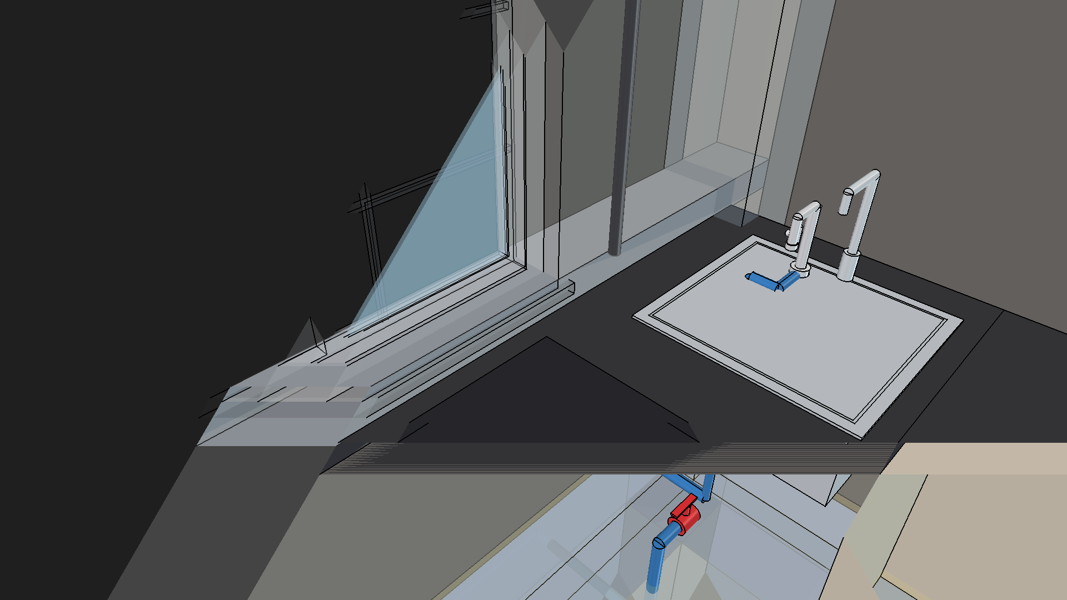
renders/gf_kitchen_under_sink_valve_xray.png
