Pradeeparul2/house-plan/renders/gf_toilet_wm_front_view.png

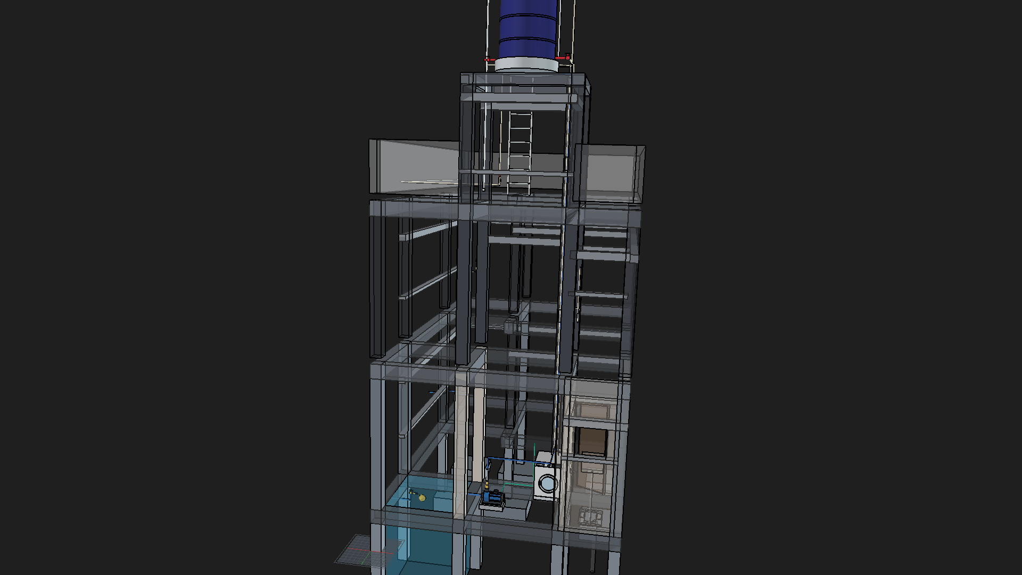
renders/gf_toilet_wm_front_view.png
