Pradeeparul2/house-plan/renders/gf_utility_wm_overlap_resolved.png

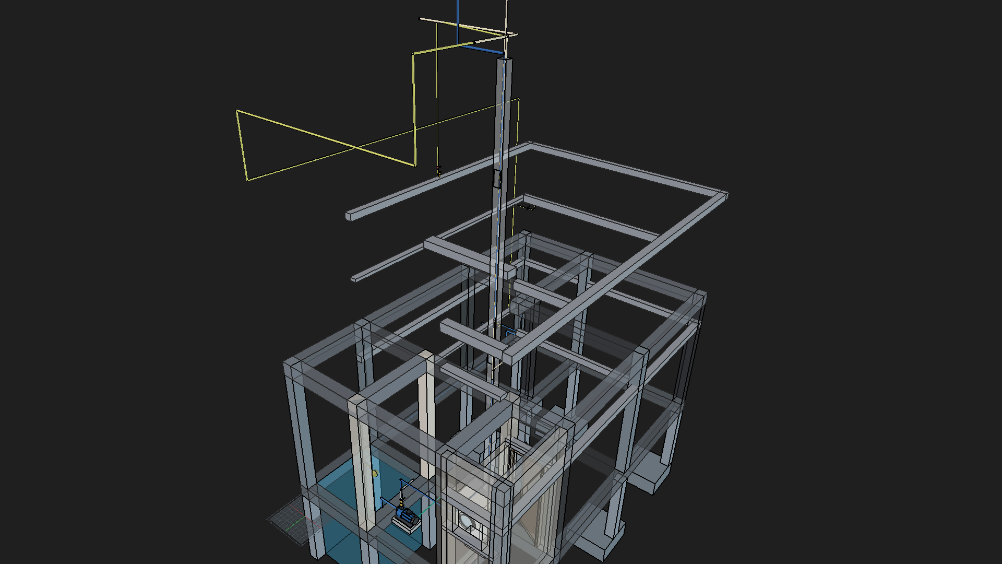
renders/gf_utility_wm_overlap_resolved.png
