Pradeeparul2/house-plan/renders/ground_floor_plan_2d_preview.png

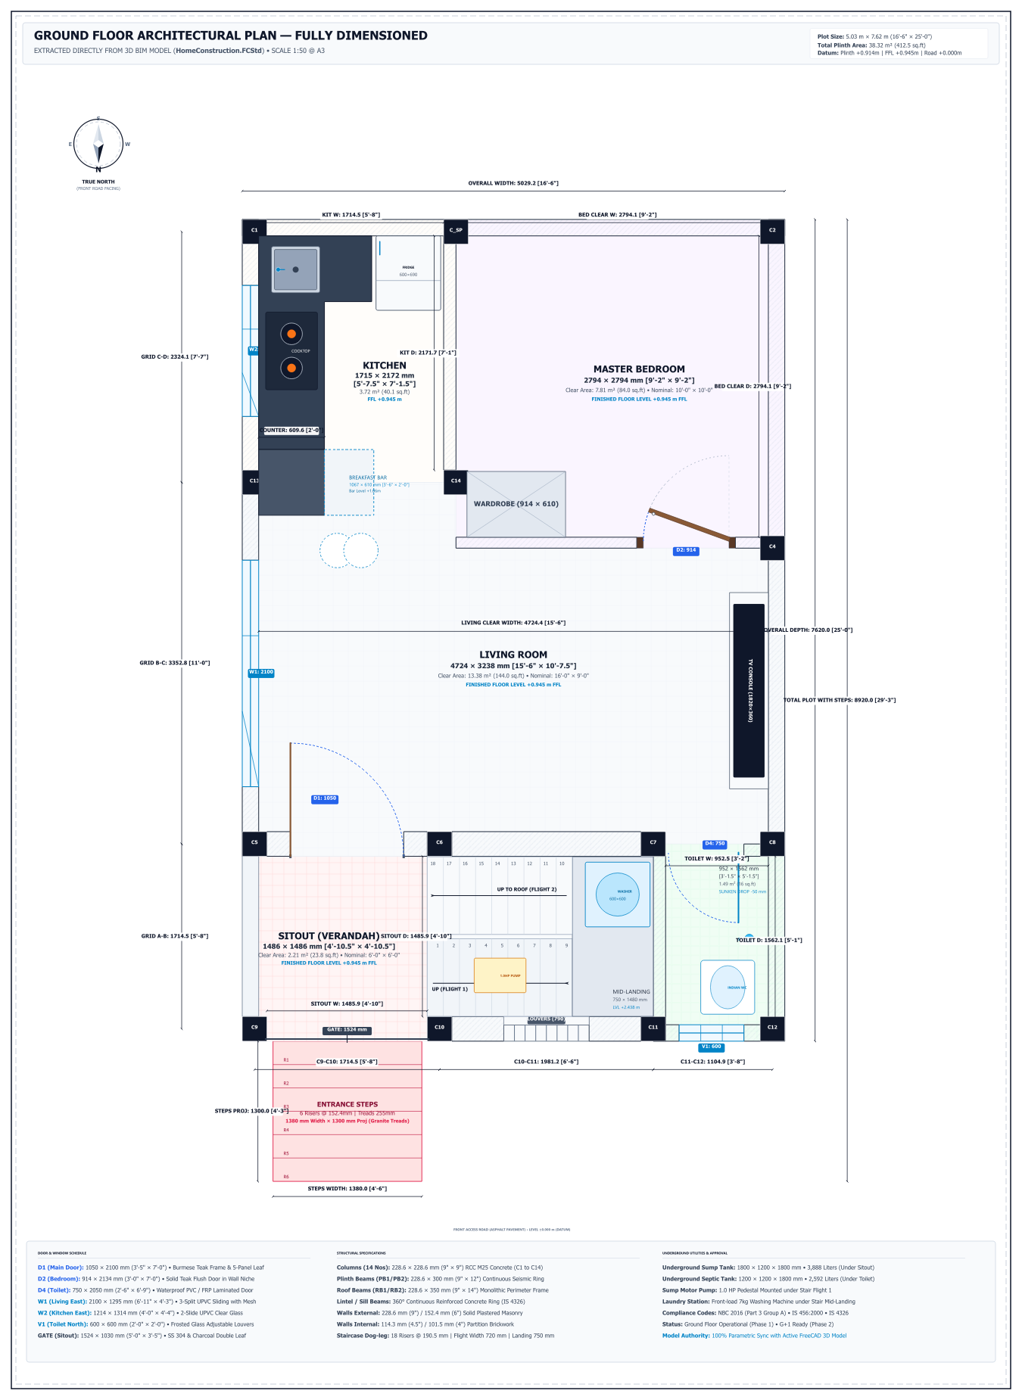
renders/ground_floor_plan_2d_preview.png
