Pradeeparul2/house-plan/renders/headroom_light_full_raw.png

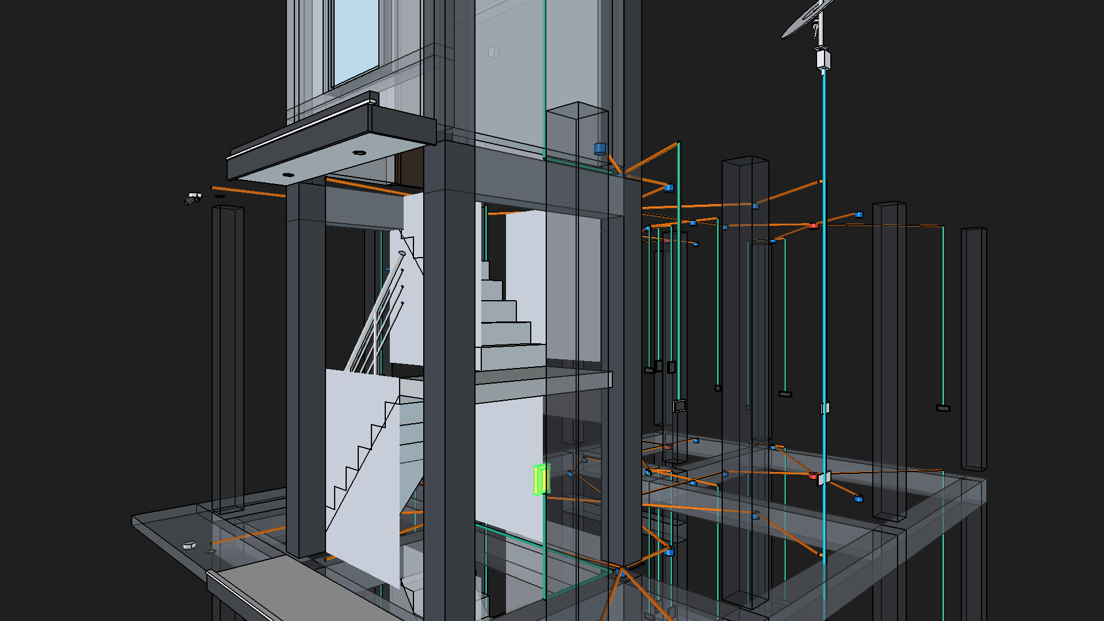
renders/headroom_light_full_raw.png
