Pradeeparul2/house-plan/renders/headroom_window_pipeline_reroute_front.png

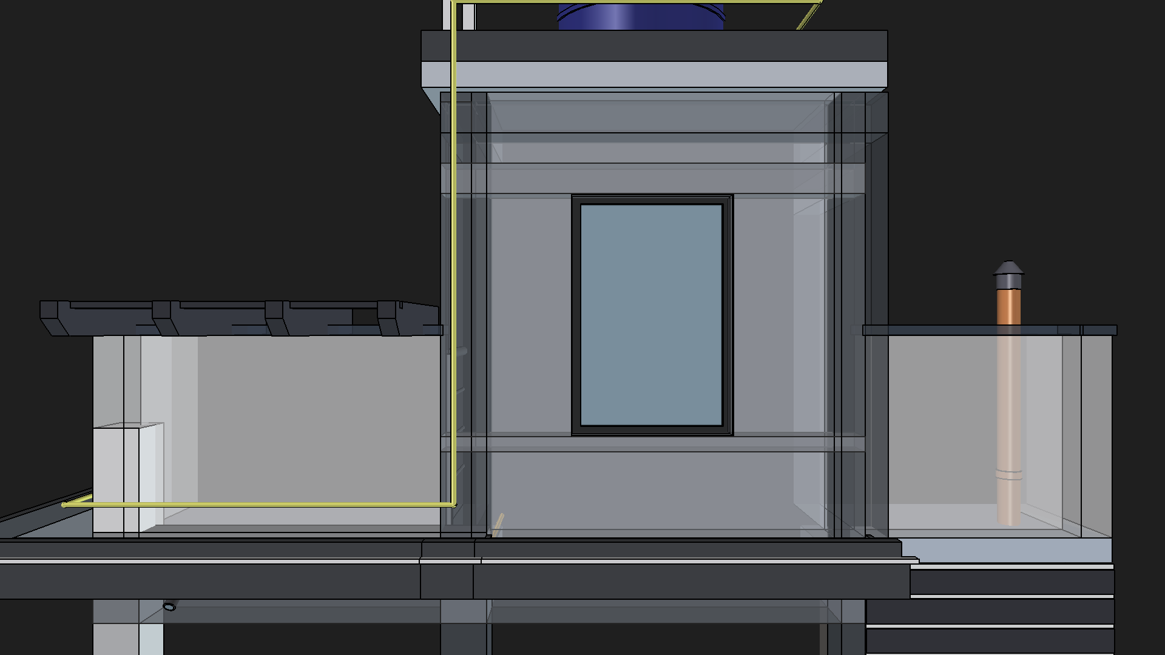
renders/headroom_window_pipeline_reroute_front.png
