Pradeeparul2/house-plan/renders/isometric_lintels_sills_solid.png

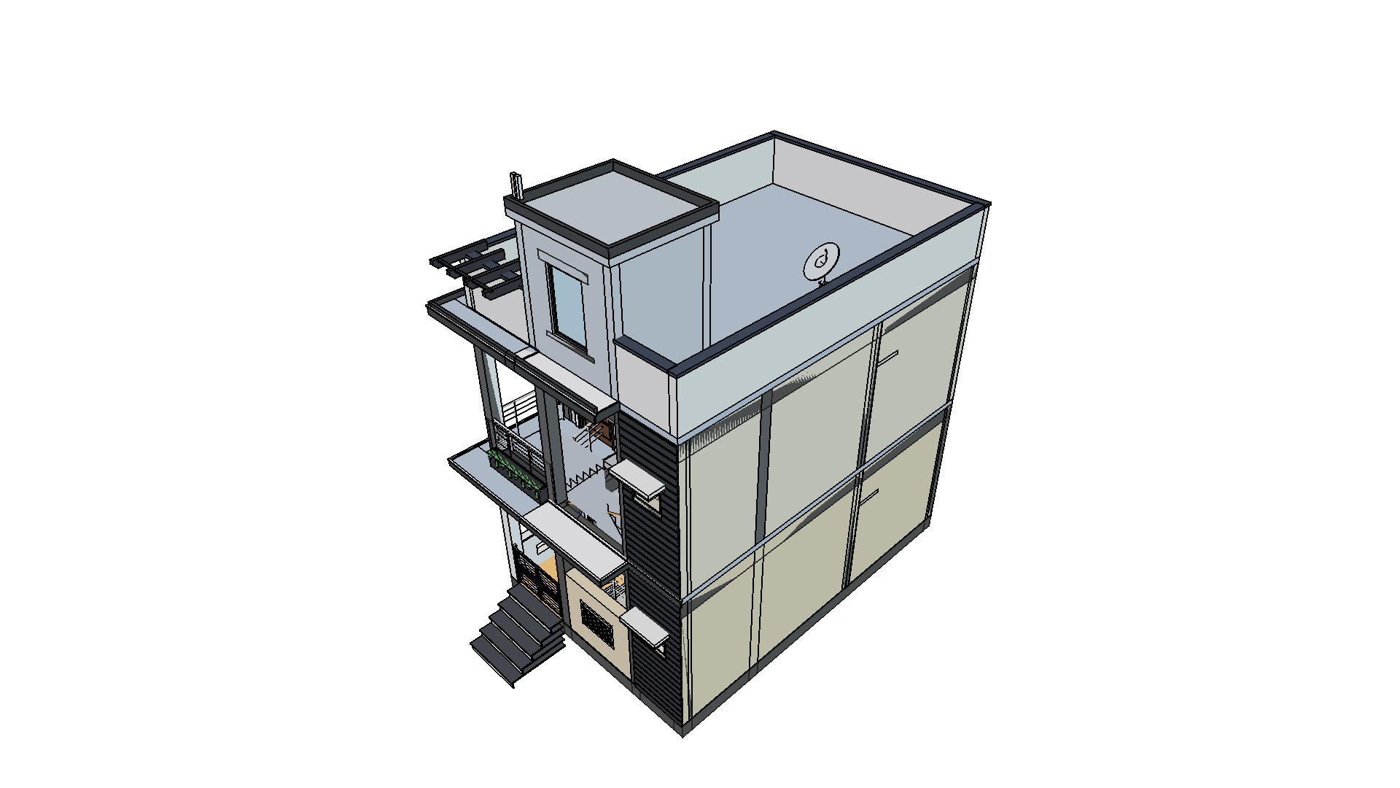
renders/isometric_lintels_sills_solid.png
