Pradeeparul2/house-plan/renders/isometric_view_single_door.png

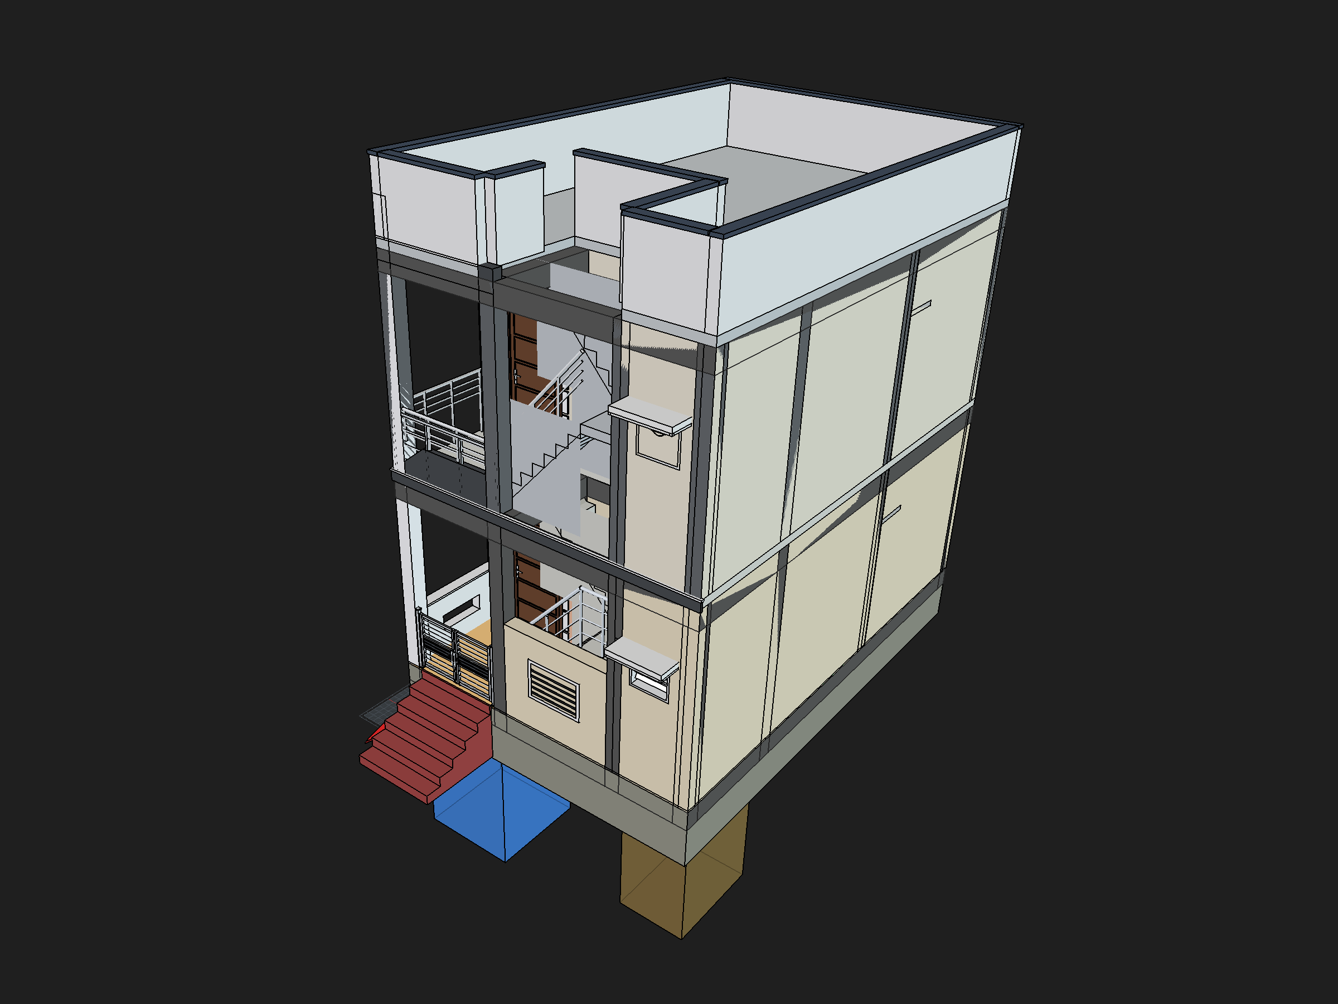
renders/isometric_view_single_door.png
