Pradeeparul2/house-plan/renders/kitchen_counter_detail_view.png

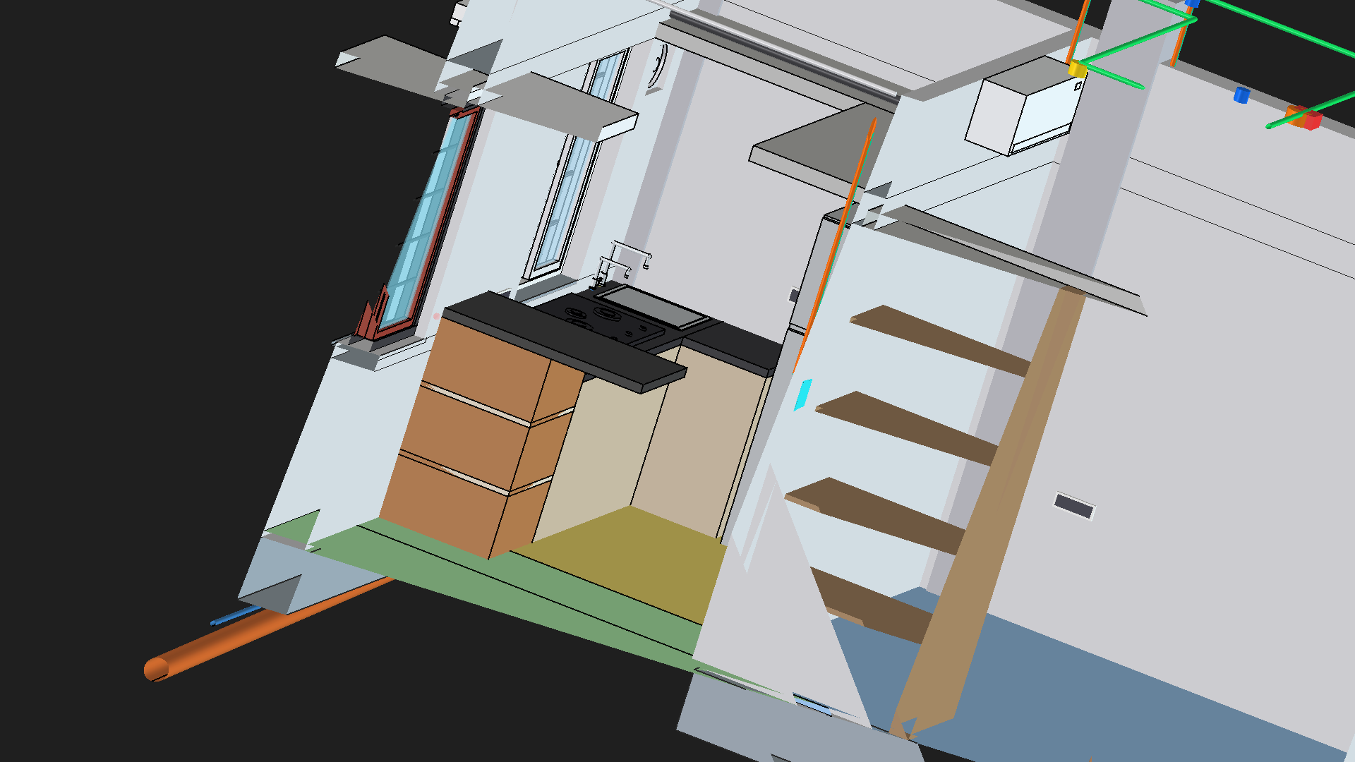
renders/kitchen_counter_detail_view.png
