Pradeeparul2/house-plan/renders/kitchen_counter_top_perspective.png

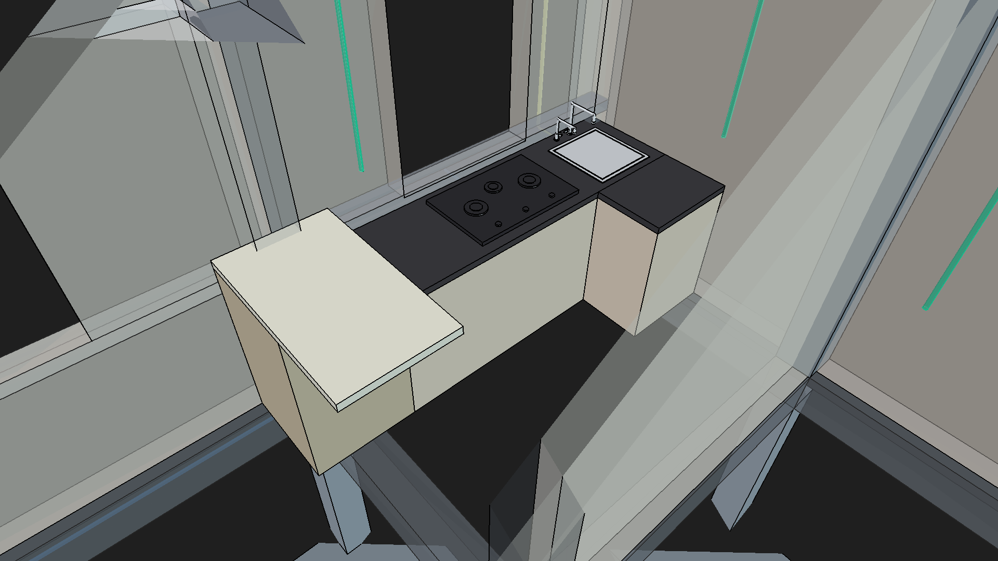
renders/kitchen_counter_top_perspective.png
