Pradeeparul2/house-plan/renders/kitchen_counter_top_plan.png

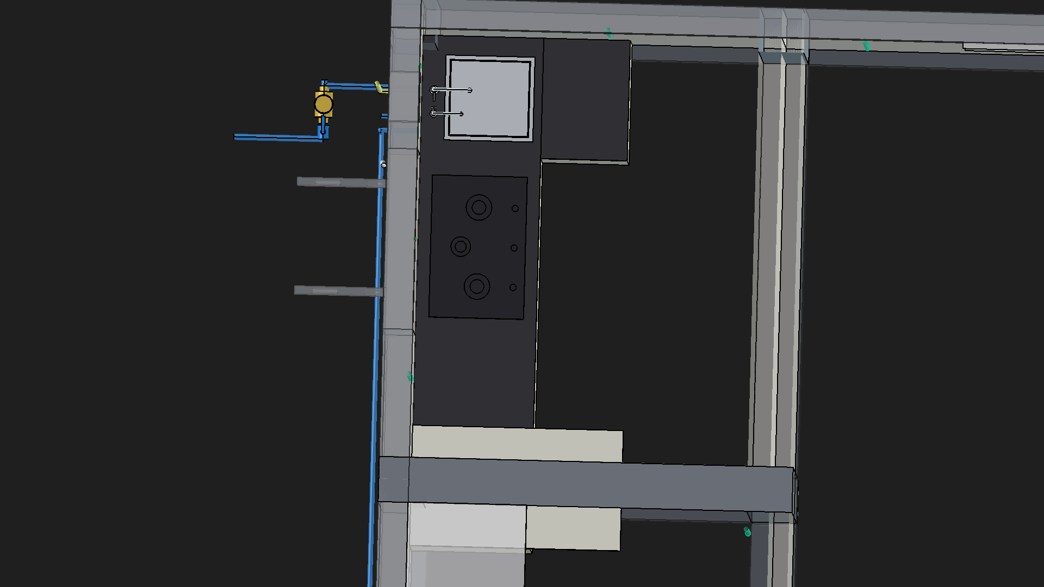
renders/kitchen_counter_top_plan.png
