Pradeeparul2/house-plan/renders/kitchen_drainage_east_profile_slope.png

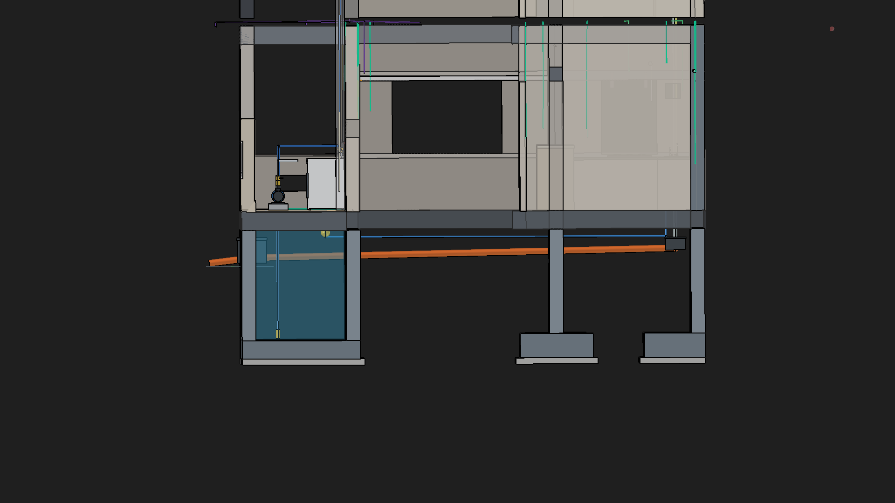
renders/kitchen_drainage_east_profile_slope.png
