Pradeeparul2/house-plan/renders/kitchen_drainage_gully_trap_closeup.png

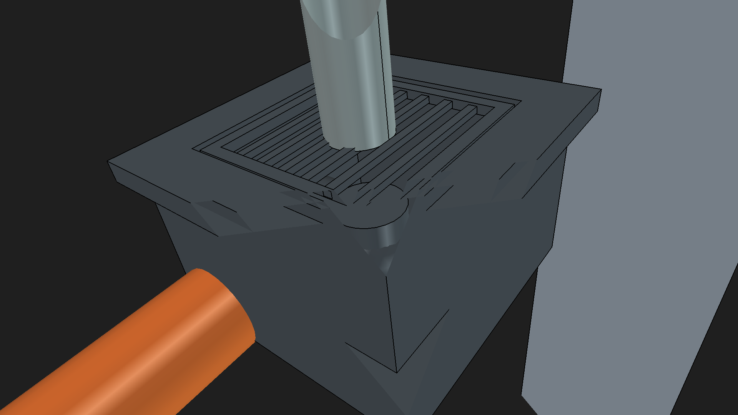
renders/kitchen_drainage_gully_trap_closeup.png
