Pradeeparul2/house-plan/renders/kitchen_drainage_ic1_road_outfall_closeup.png

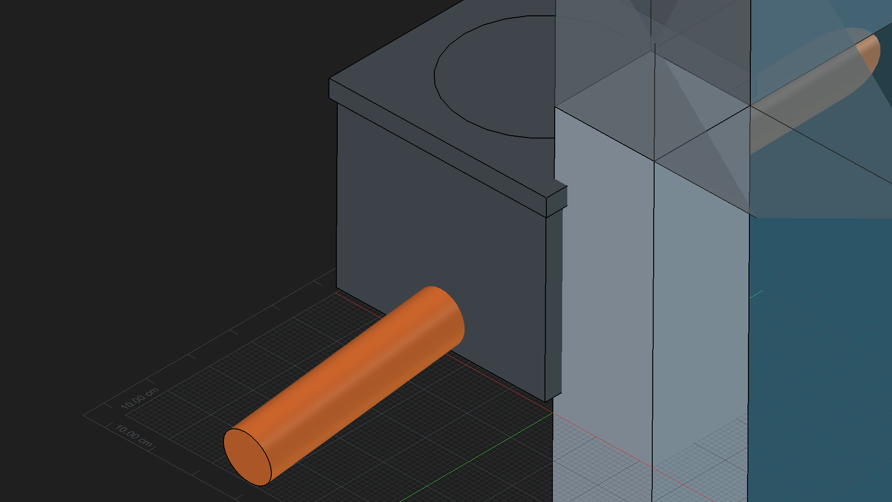
renders/kitchen_drainage_ic1_road_outfall_closeup.png
