Pradeeparul2/house-plan/renders/kitchen_interior_view.png

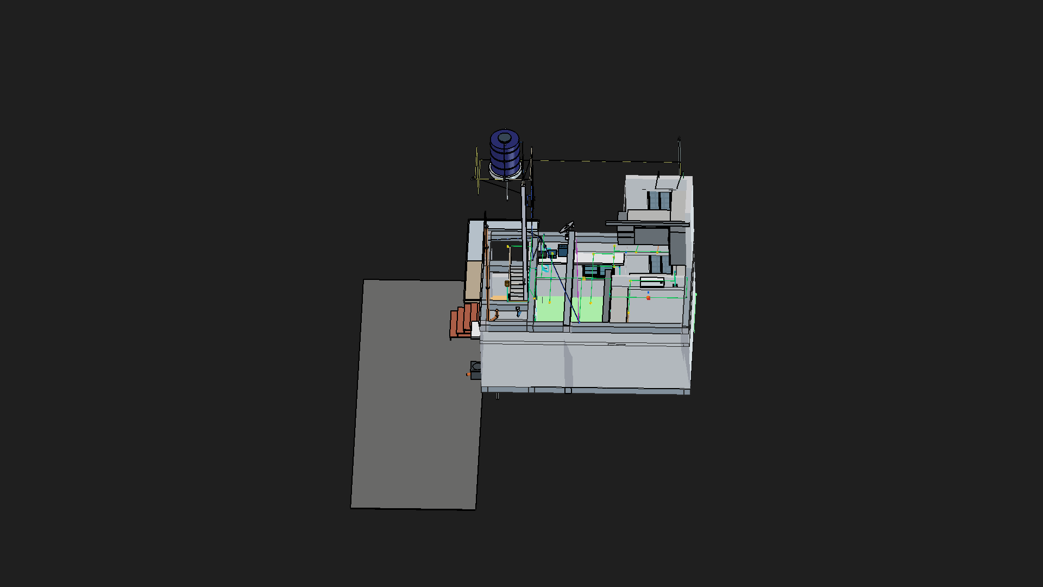
renders/kitchen_interior_view.png
