Pradeeparul2/house-plan/renders/kitchen_perspective_overview.png

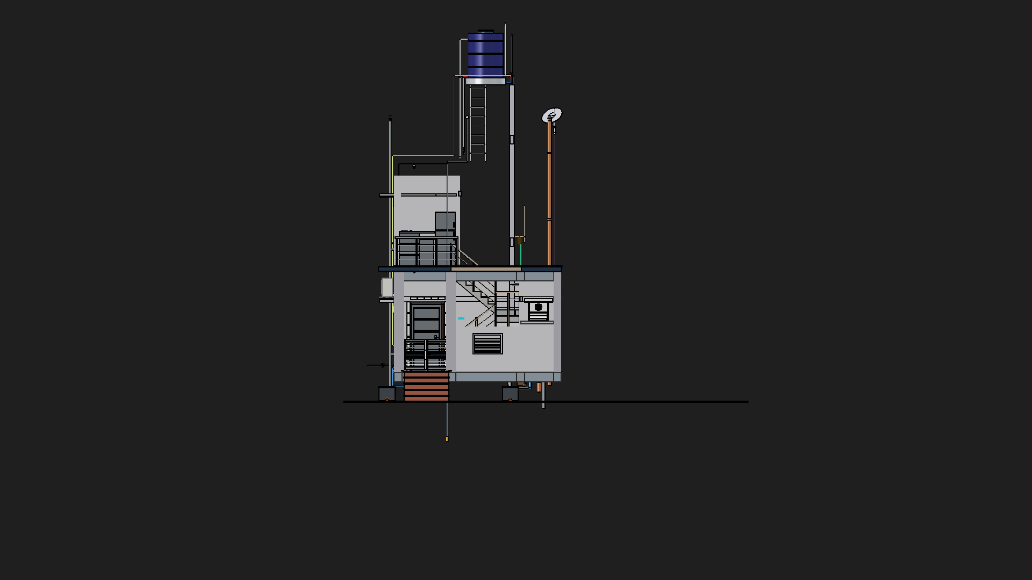
renders/kitchen_perspective_overview.png
