Pradeeparul2/house-plan/renders/kitchen_pipeline_headroom_curb.png

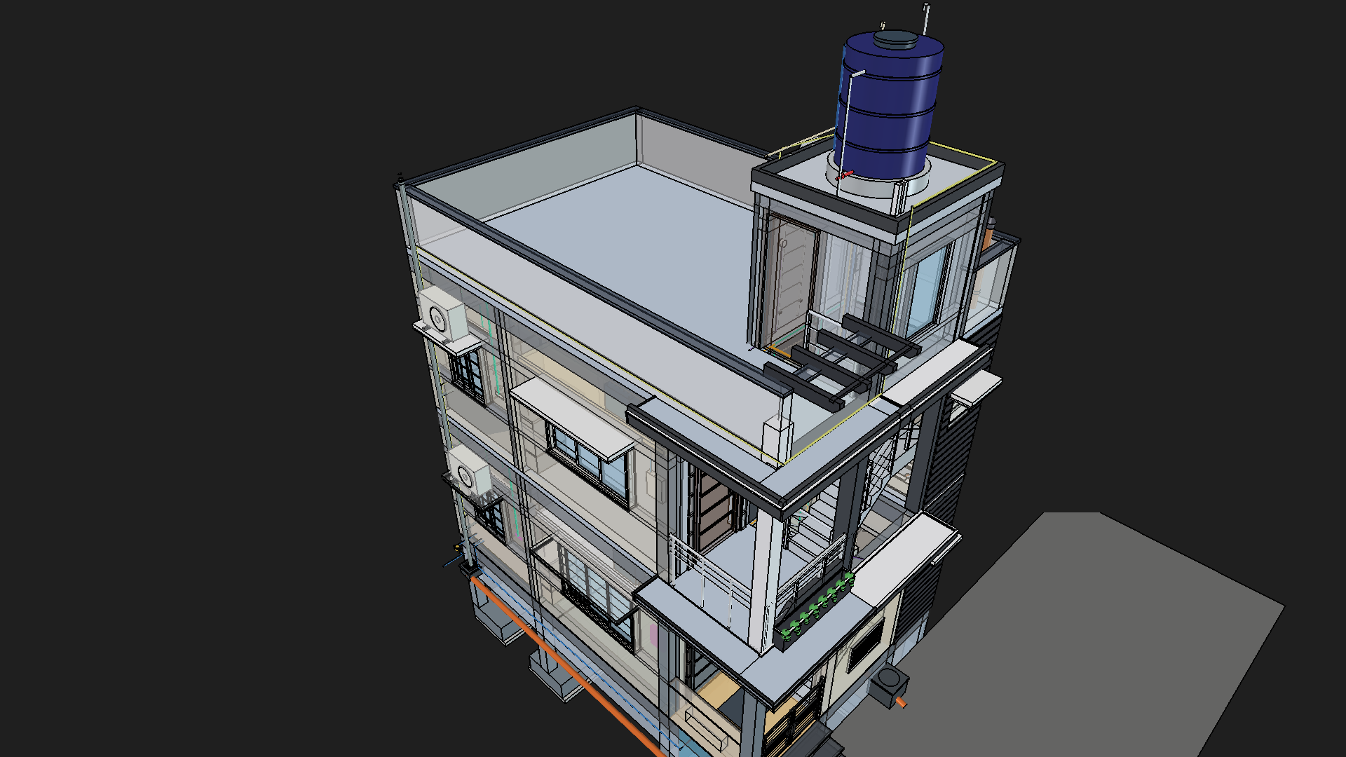
renders/kitchen_pipeline_headroom_curb.png
