Pradeeparul2/house-plan/renders/kitchen_sink_east_taps_closeup.png

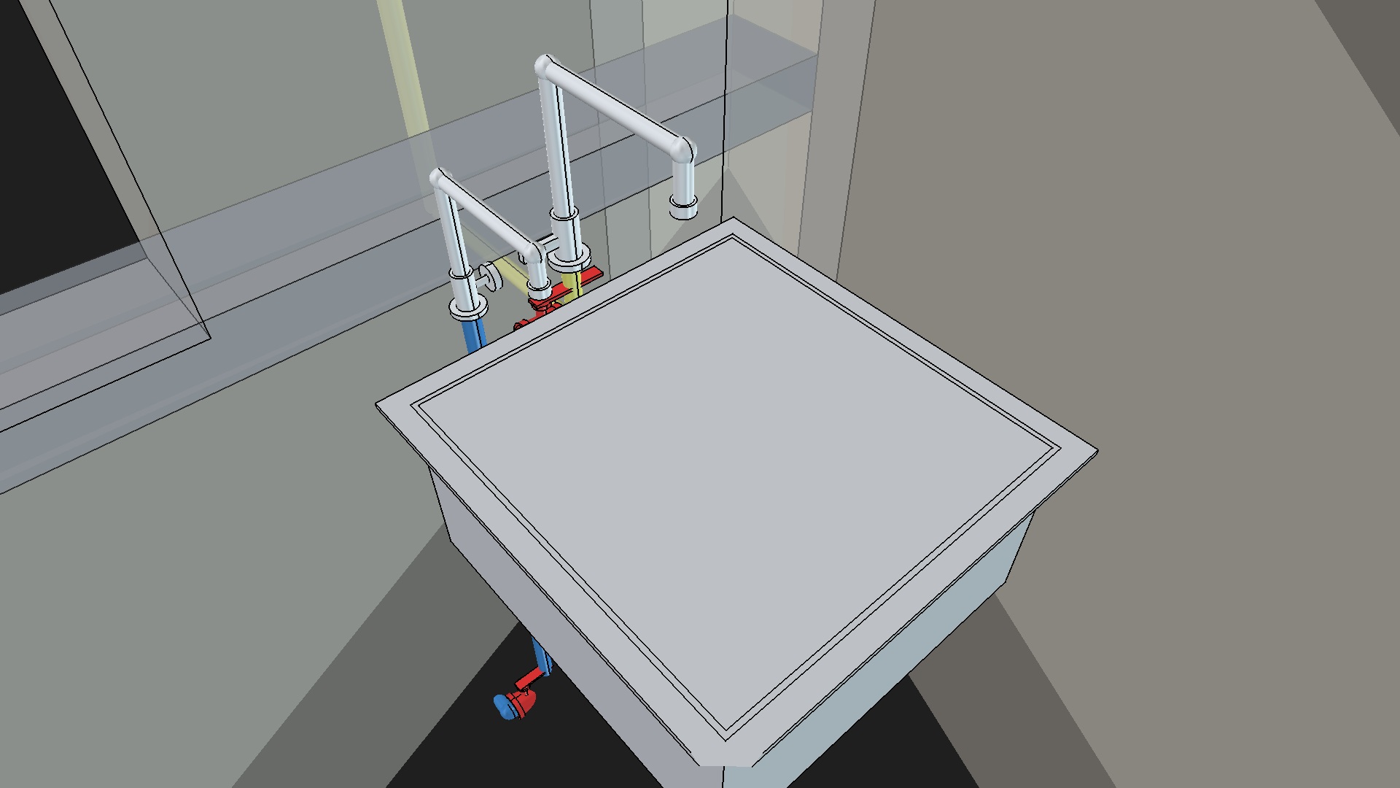
renders/kitchen_sink_east_taps_closeup.png
