Pradeeparul2/house-plan/renders/living_room_north_wall_mdb.png

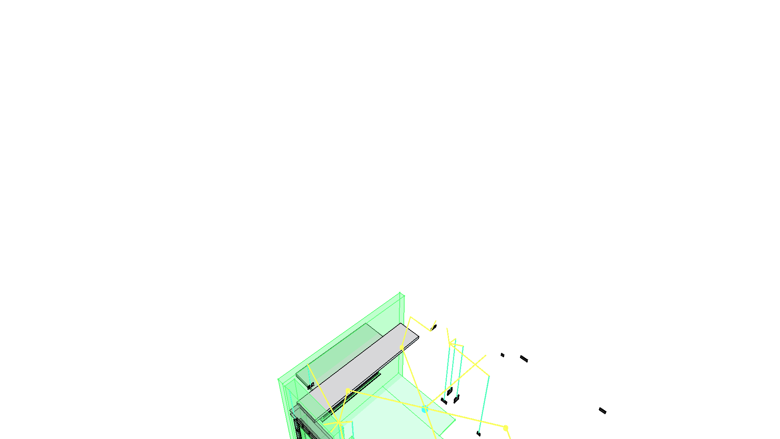
renders/living_room_north_wall_mdb.png
