Pradeeparul2/house-plan/renders/living_room_perfect_fit.png

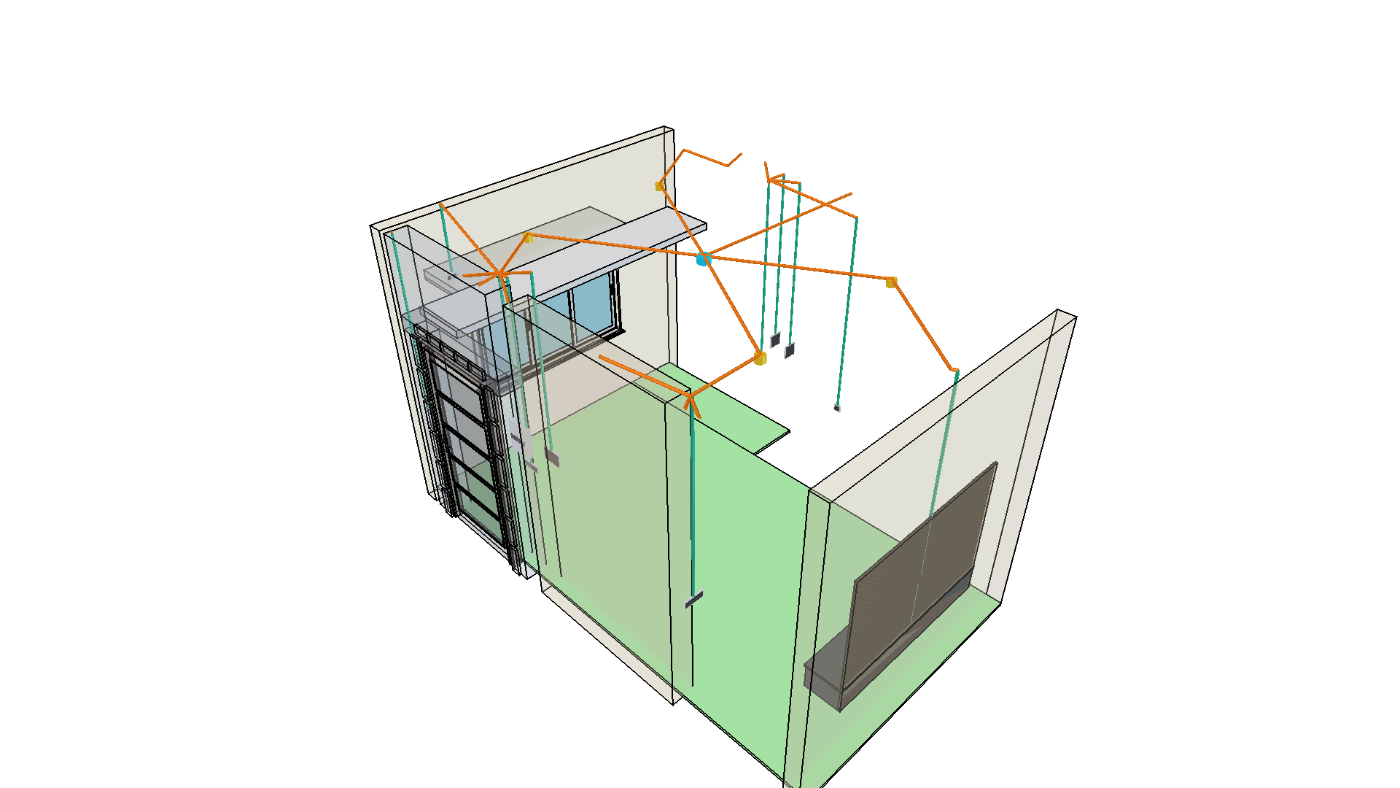
renders/living_room_perfect_fit.png
