Pradeeparul2/house-plan/renders/living_room_unified_switchboards_annotated.png

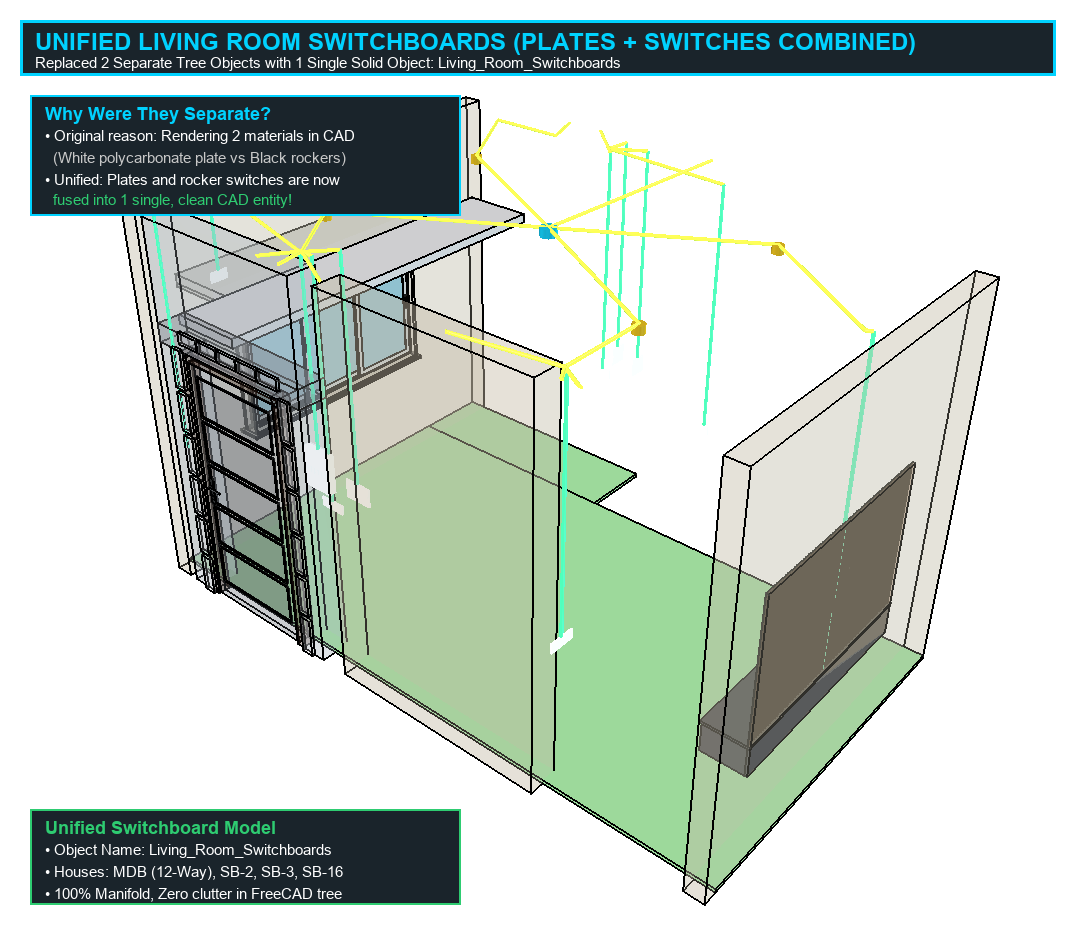
renders/living_room_unified_switchboards_annotated.png
