Pradeeparul2/house-plan/renders/living_room_view1.png

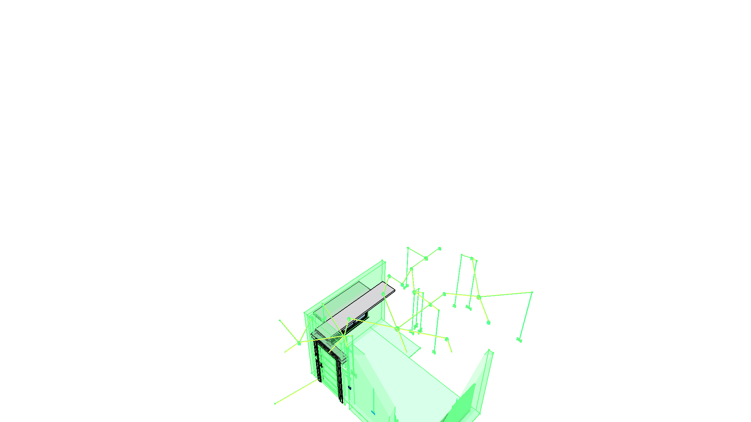
renders/living_room_view1.png
