Pradeeparul2/house-plan/renders/looking_at_main_door_from_inside.png

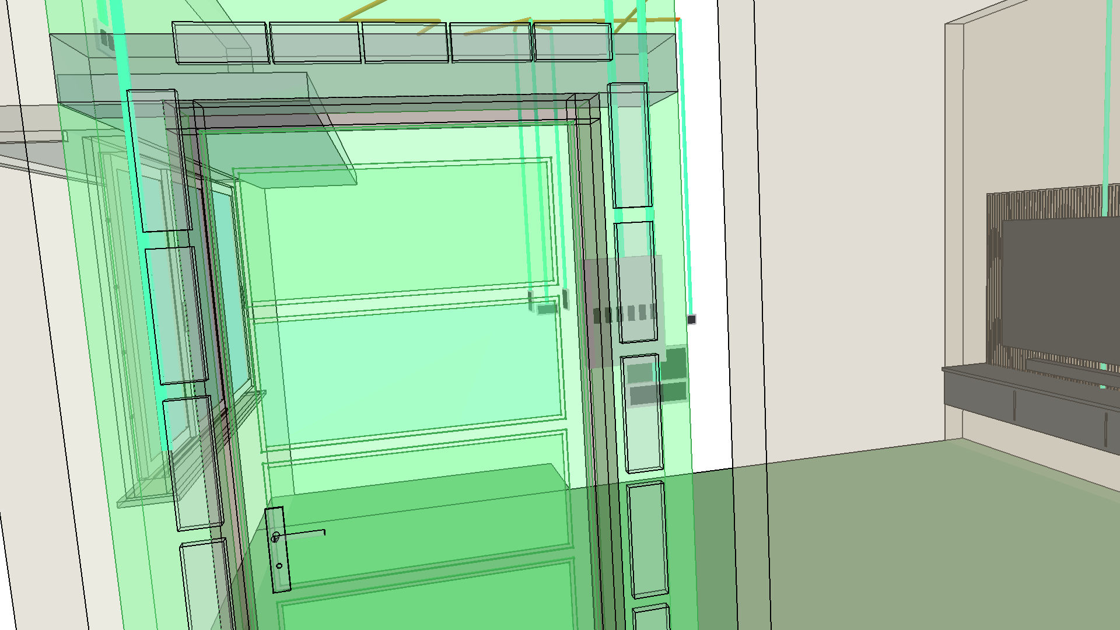
renders/looking_at_main_door_from_inside.png
