Pradeeparul2/house-plan/renders/main_door_east_pipeline_annotated.png

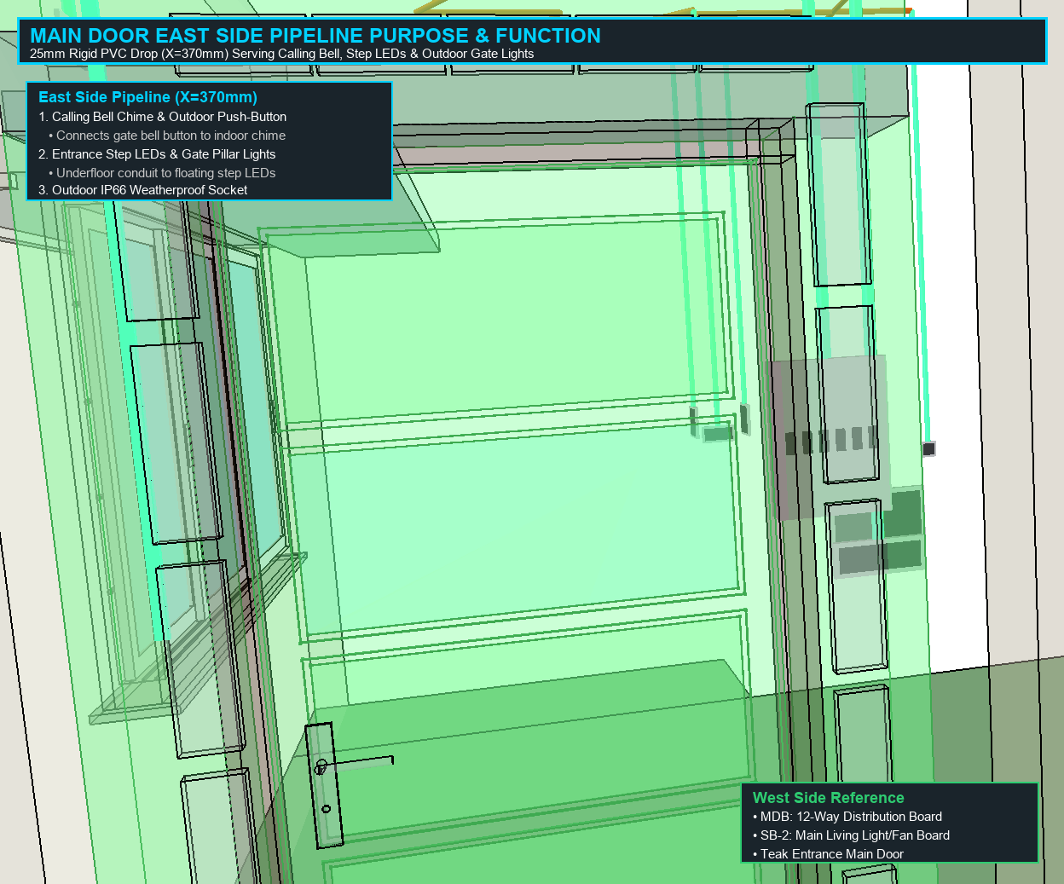
renders/main_door_east_pipeline_annotated.png
