Pradeeparul2/house-plan/renders/mdb_stack_conduit_connections.png

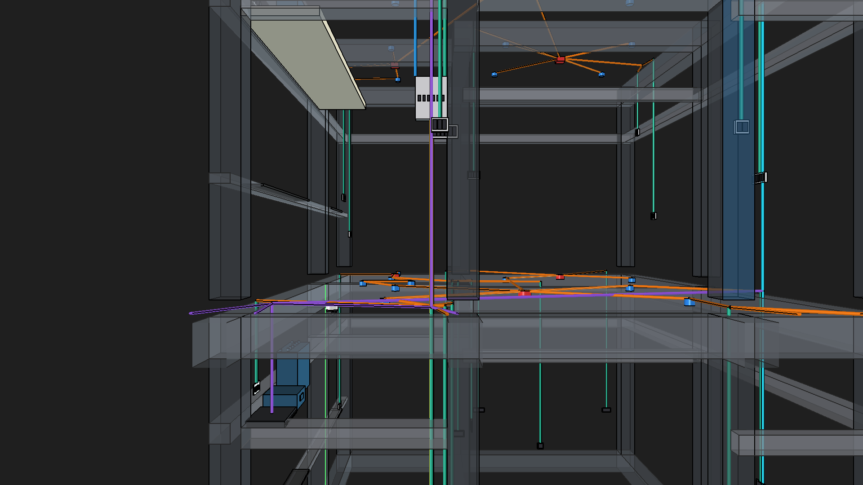
renders/mdb_stack_conduit_connections.png
