Pradeeparul2/house-plan/renders/mdb_vertical_stack_gf_ff.png

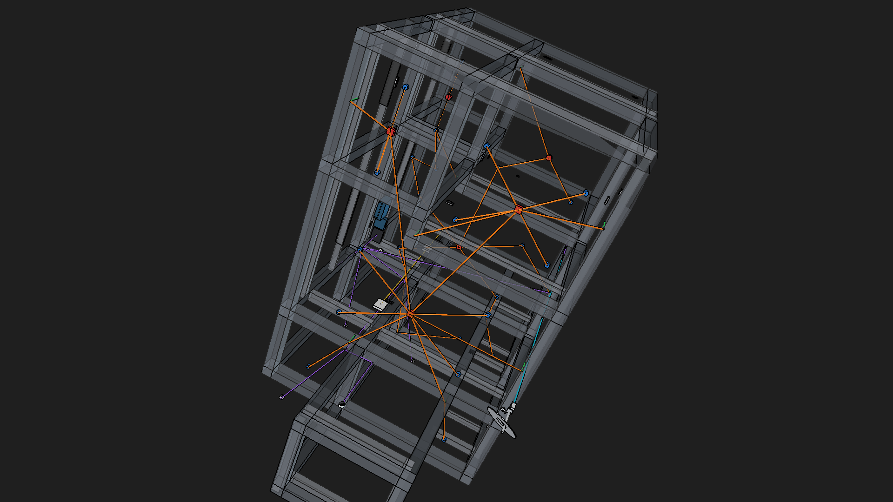
renders/mdb_vertical_stack_gf_ff.png
