Pradeeparul2/house-plan/renders/model_50pct_transparency_southeast.png

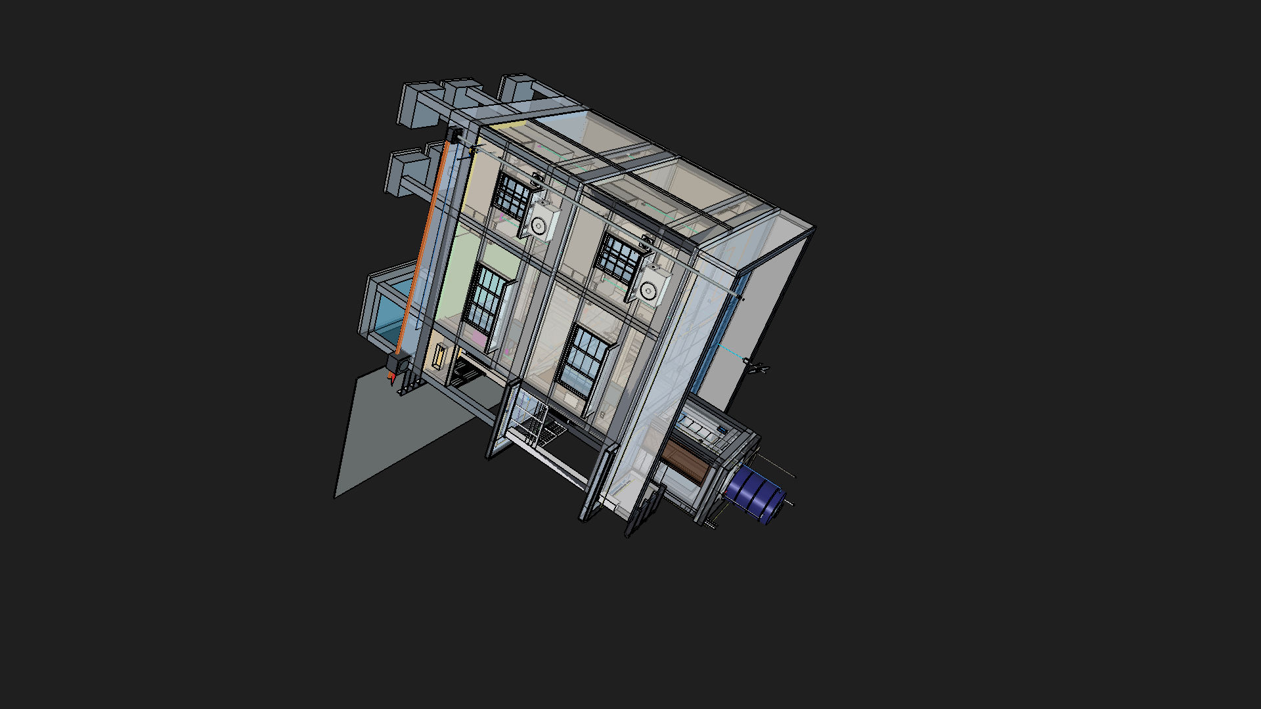
renders/model_50pct_transparency_southeast.png
