Pradeeparul2/house-plan/renders/model_50pct_transparency_sw_upright.png

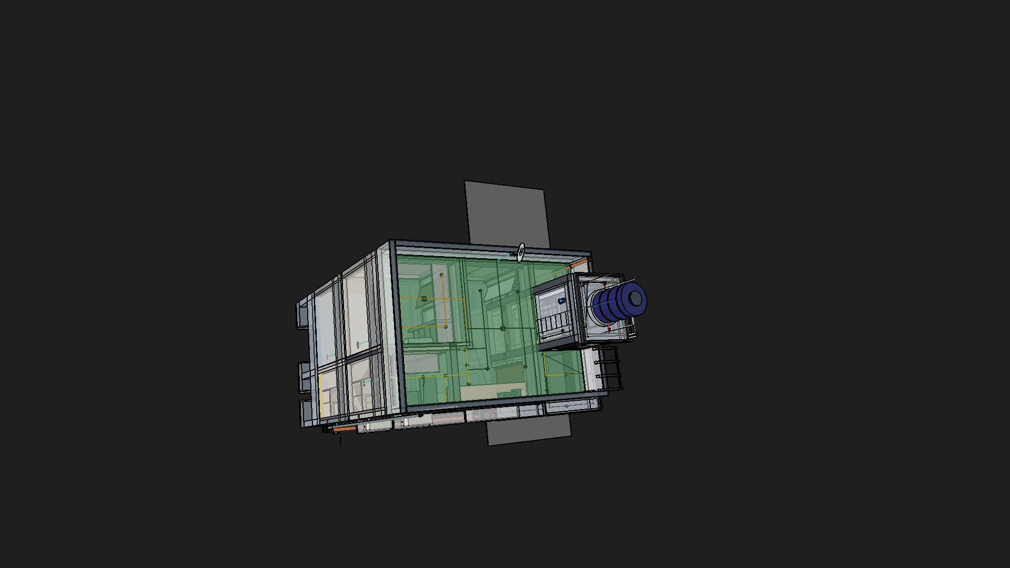
renders/model_50pct_transparency_sw_upright.png
