Pradeeparul2/house-plan/renders/new_single_door_isometric.png

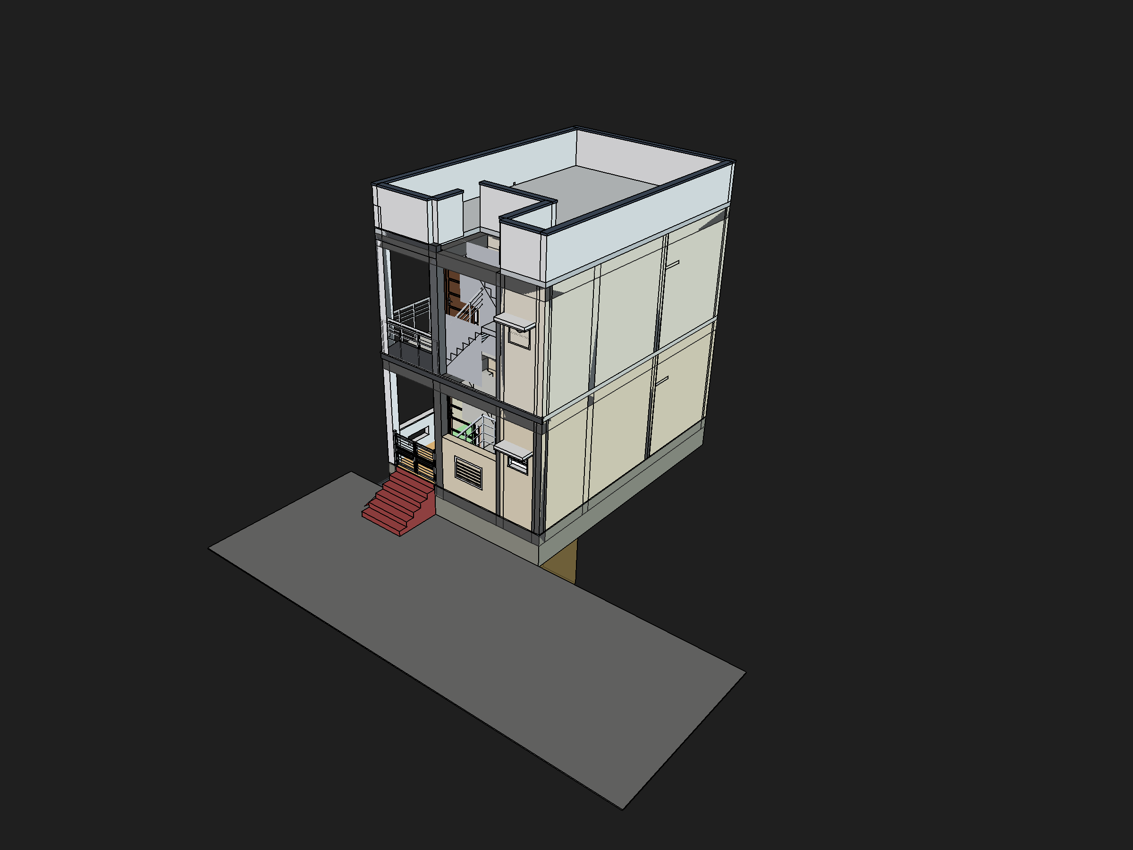
renders/new_single_door_isometric.png
