Pradeeparul2/house-plan/renders/north_road_drainage_front_overview.png

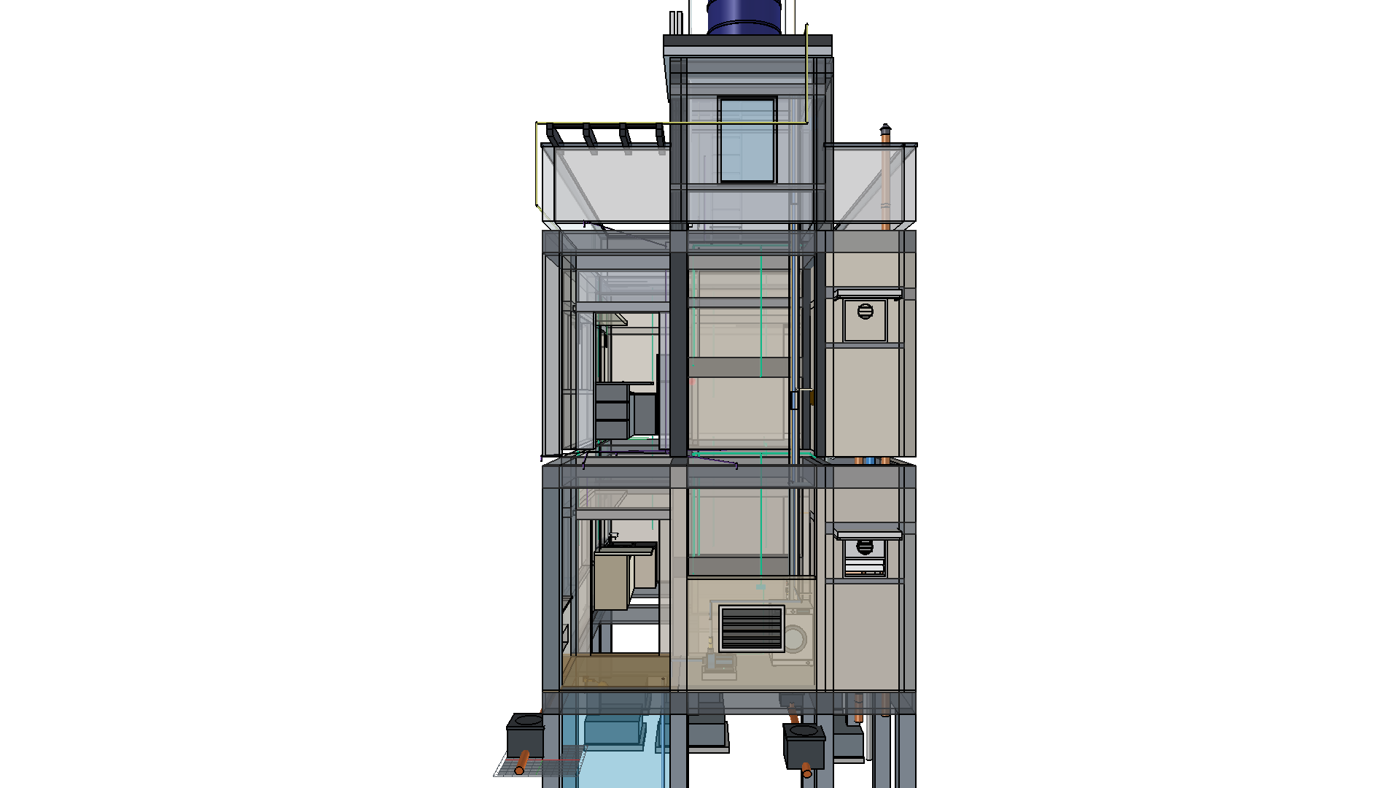
renders/north_road_drainage_front_overview.png
