Pradeeparul2/house-plan/renders/oht_headroom_roof_iso_overview.png

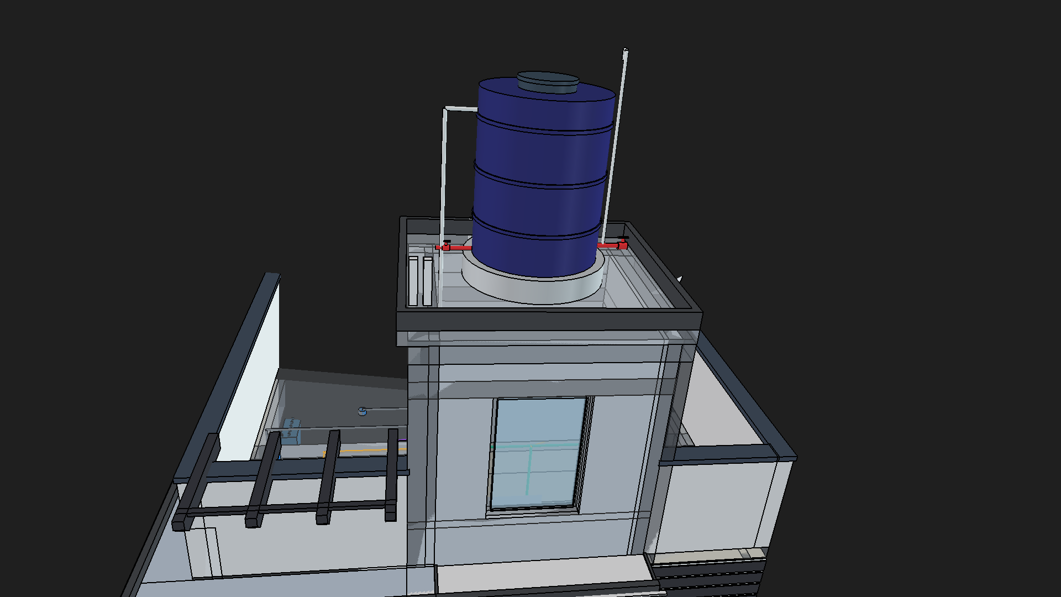
renders/oht_headroom_roof_iso_overview.png
