Pradeeparul2/house-plan/renders/oht_valves_and_pedestal_closeup.png

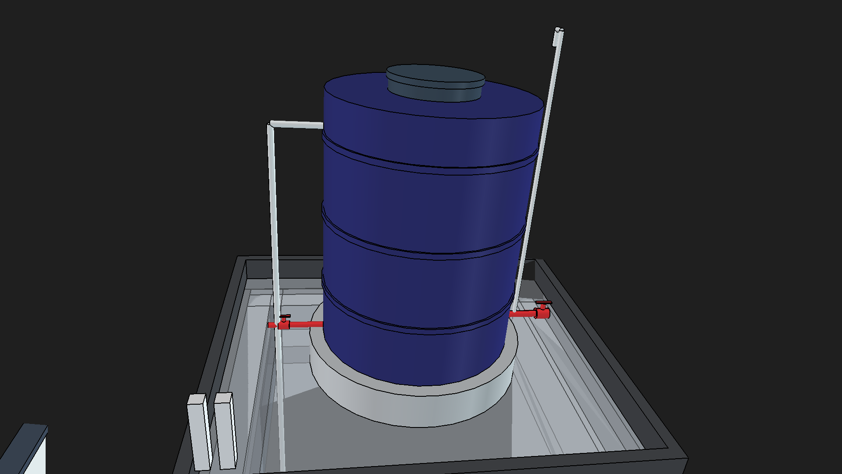
renders/oht_valves_and_pedestal_closeup.png
