Pradeeparul2/house-plan/renders/paint_palette_tower_and_entrance_closeup.png

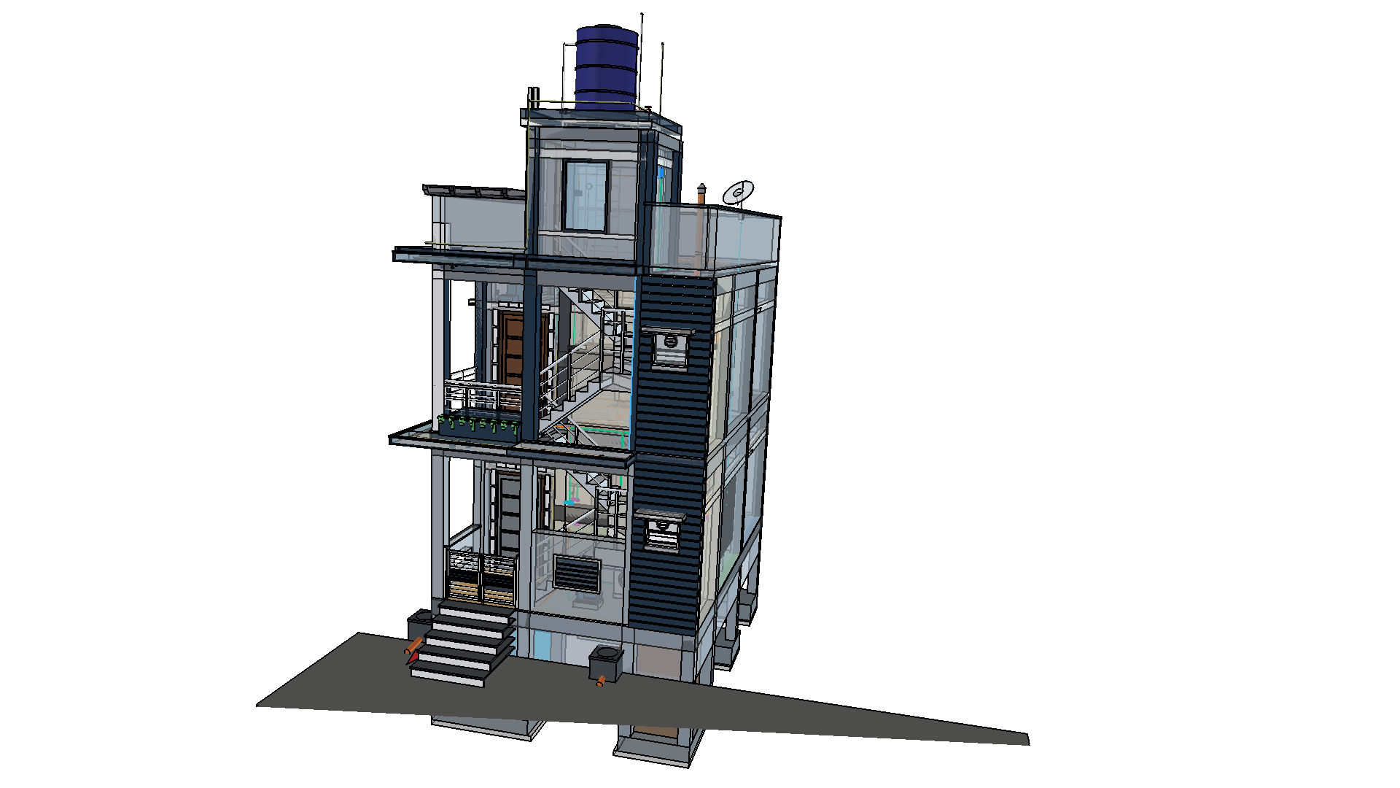
renders/paint_palette_tower_and_entrance_closeup.png
