Pradeeparul2/house-plan/renders/pipeline_undersink_shutoff_valve_focus.png

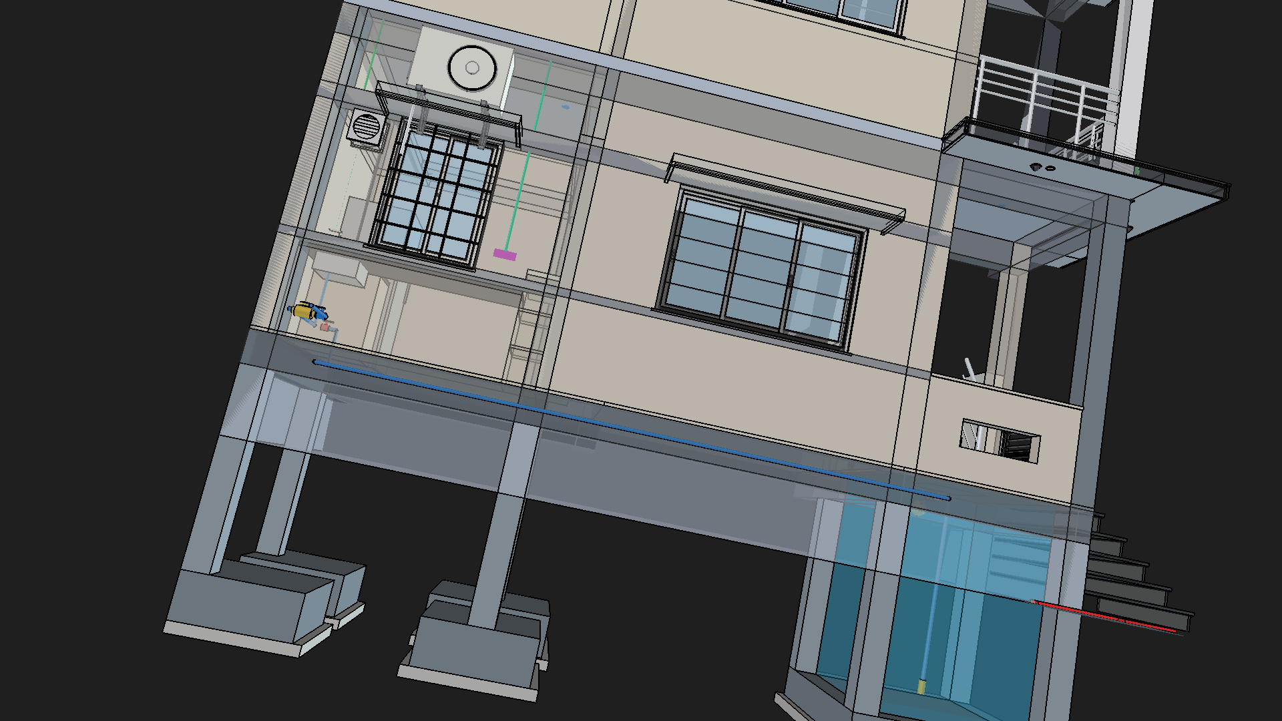
renders/pipeline_undersink_shutoff_valve_focus.png
