Pradeeparul2/house-plan/renders/pipeline_zero_beam_collision_east_elev.png

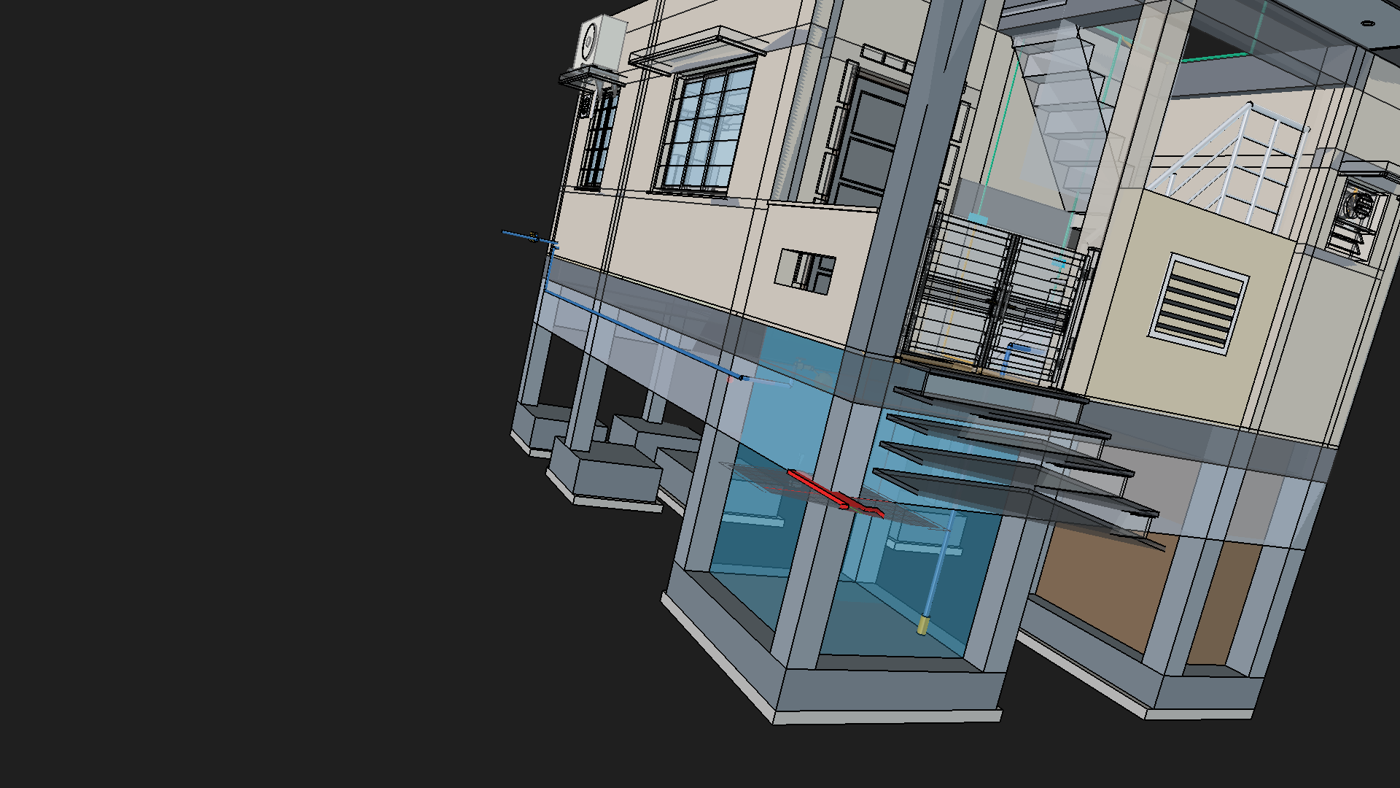
renders/pipeline_zero_beam_collision_east_elev.png
