Pradeeparul2/house-plan/renders/plumbing_full_system_xray.png

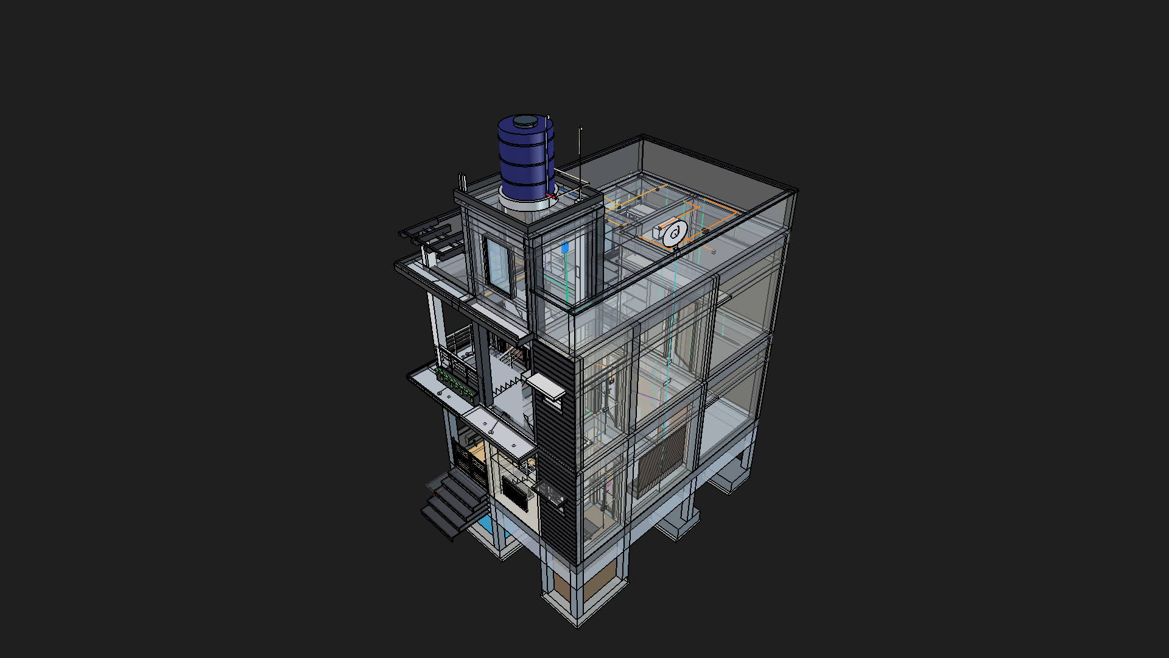
renders/plumbing_full_system_xray.png
