Pradeeparul2/house-plan/renders/plumbing_gf_kitchen_dual_taps.png

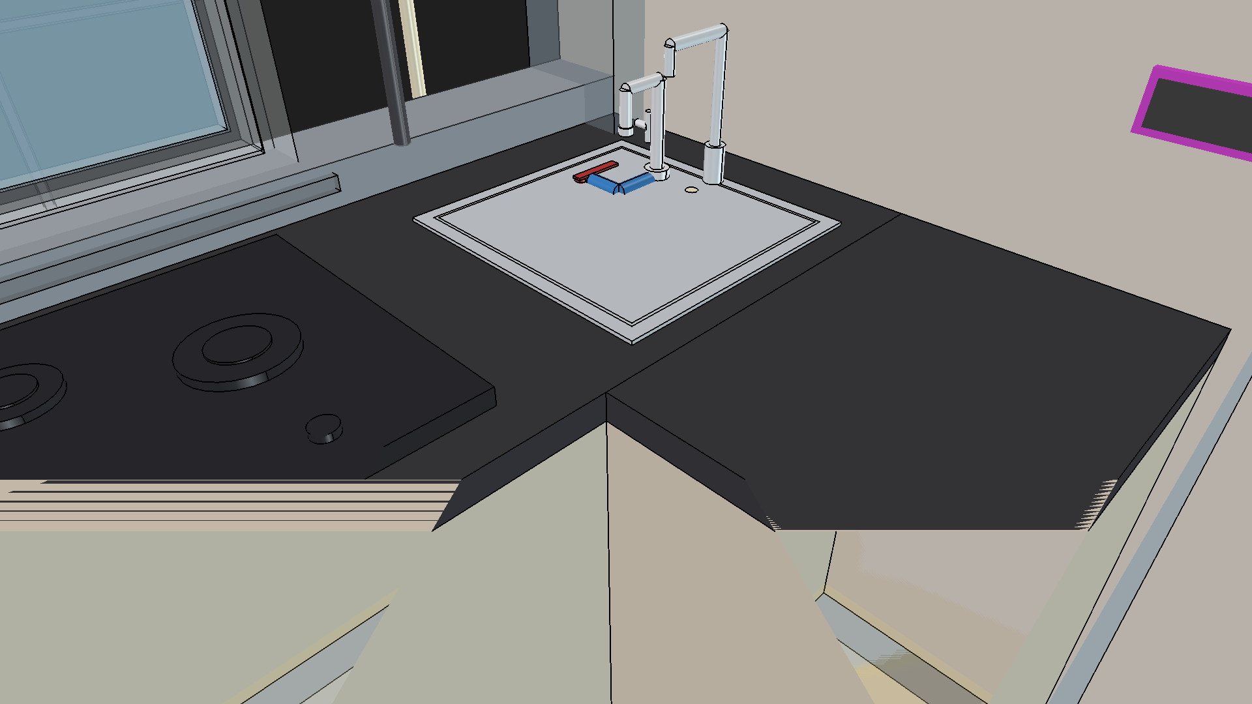
renders/plumbing_gf_kitchen_dual_taps.png
