Pradeeparul2/house-plan/renders/plumbing_sitout_outdoor_bibcock.png

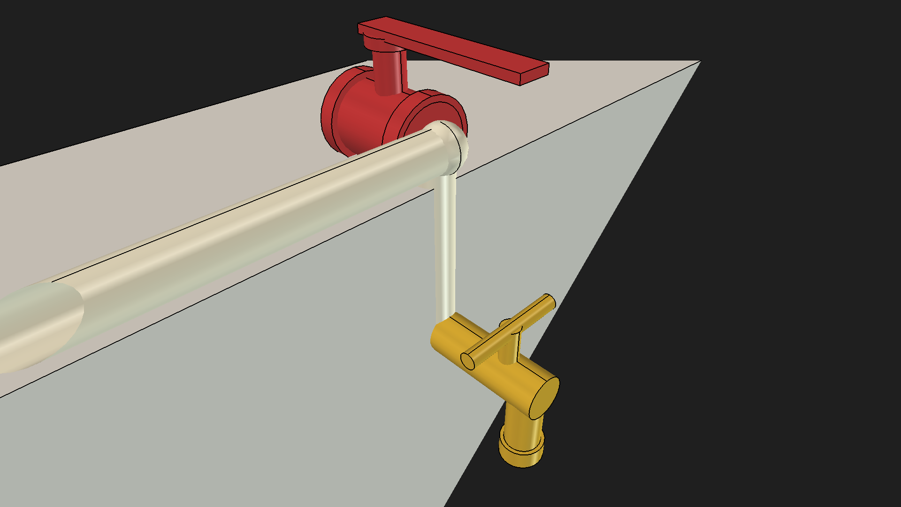
renders/plumbing_sitout_outdoor_bibcock.png
