Pradeeparul2/house-plan/renders/plumbing_terrace_utility_tap.png

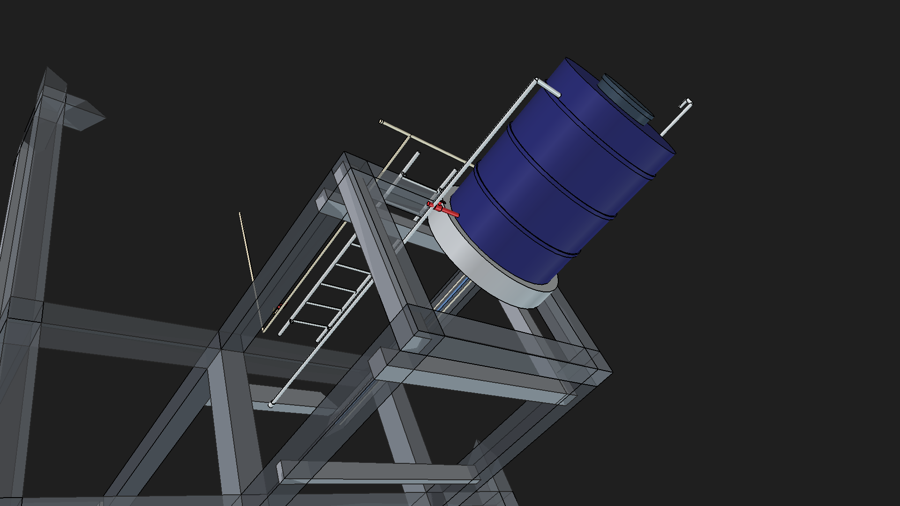
renders/plumbing_terrace_utility_tap.png
