Pradeeparul2/house-plan/renders/plumbing_utility_multipurpose_tap.png

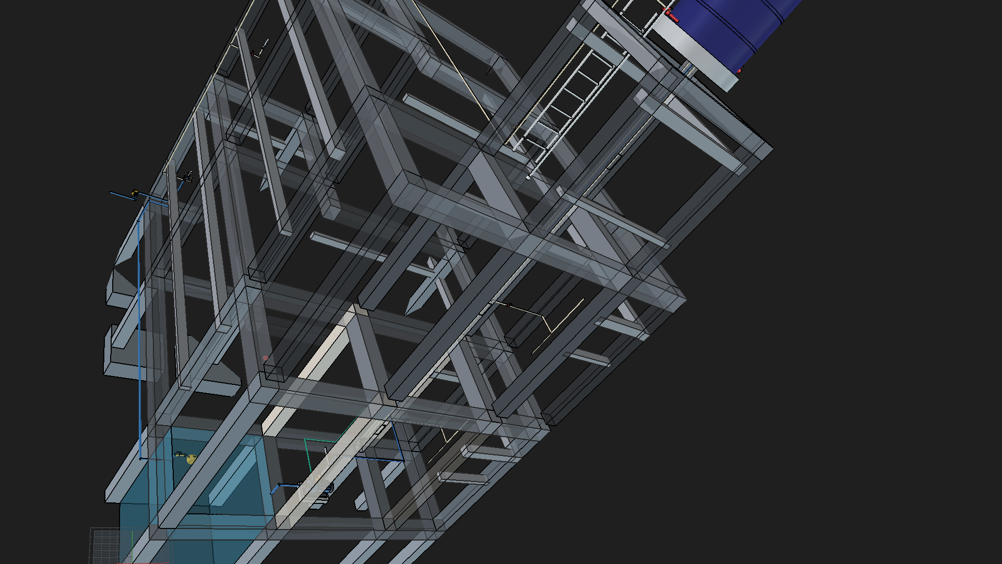
renders/plumbing_utility_multipurpose_tap.png
