Pradeeparul2/house-plan/renders/plumbing_utility_wm_valve.png

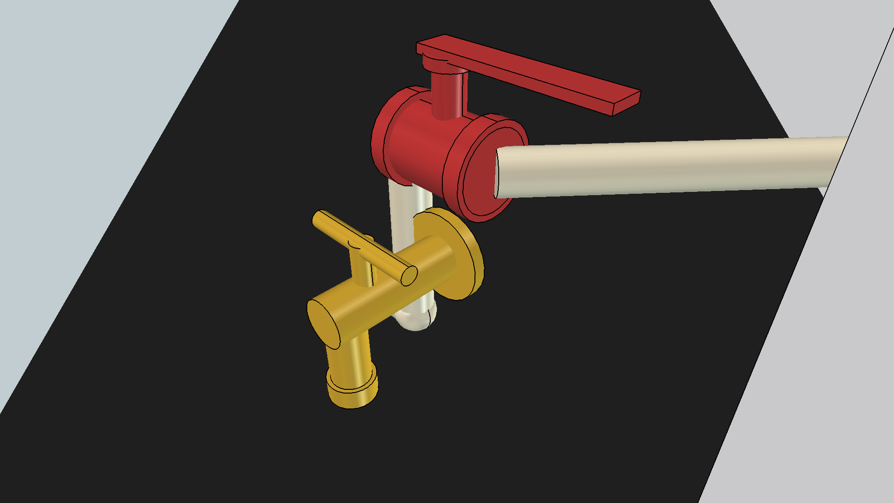
renders/plumbing_utility_wm_valve.png
