Pradeeparul2/house-plan/renders/pump_power_close_up.png

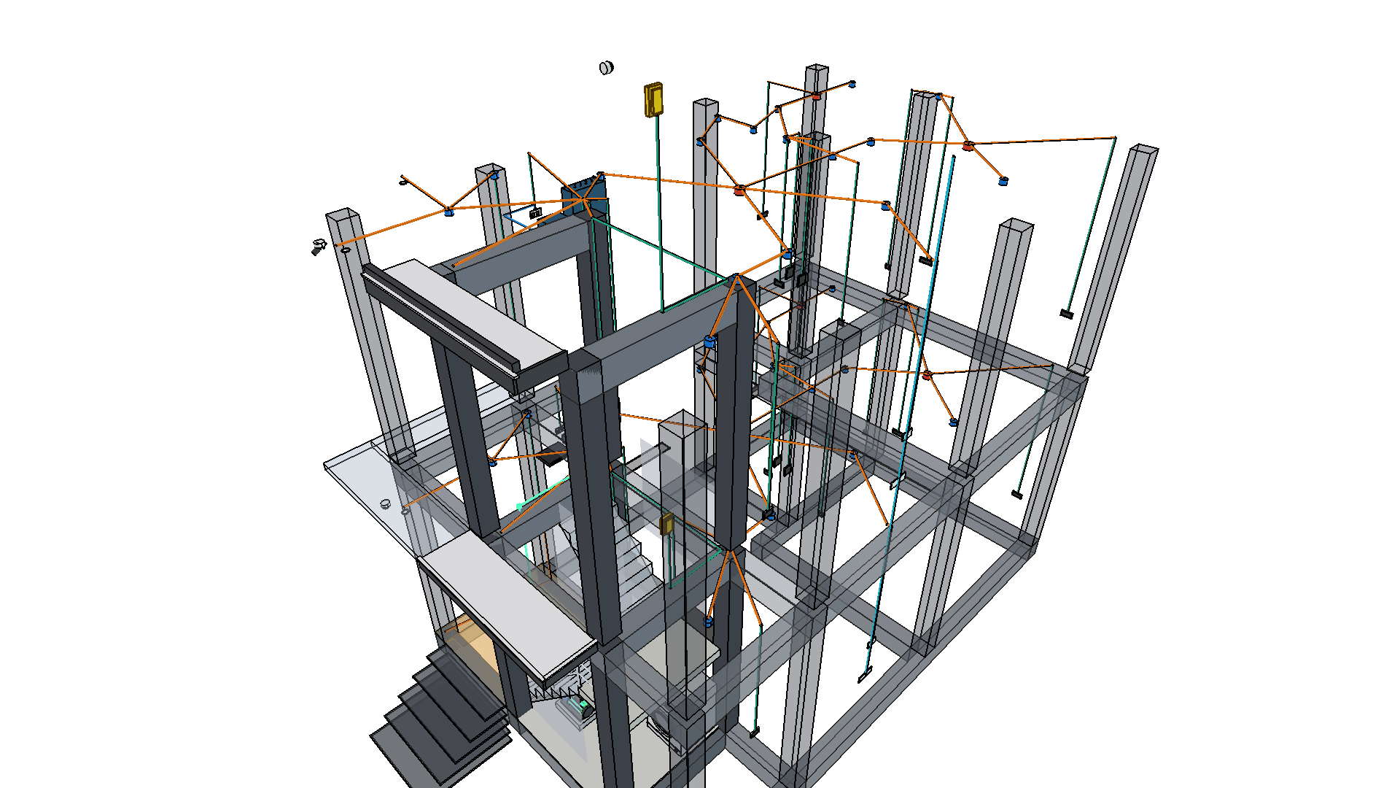
renders/pump_power_close_up.png
