Pradeeparul2/house-plan/renders/pump_power_zoom.png

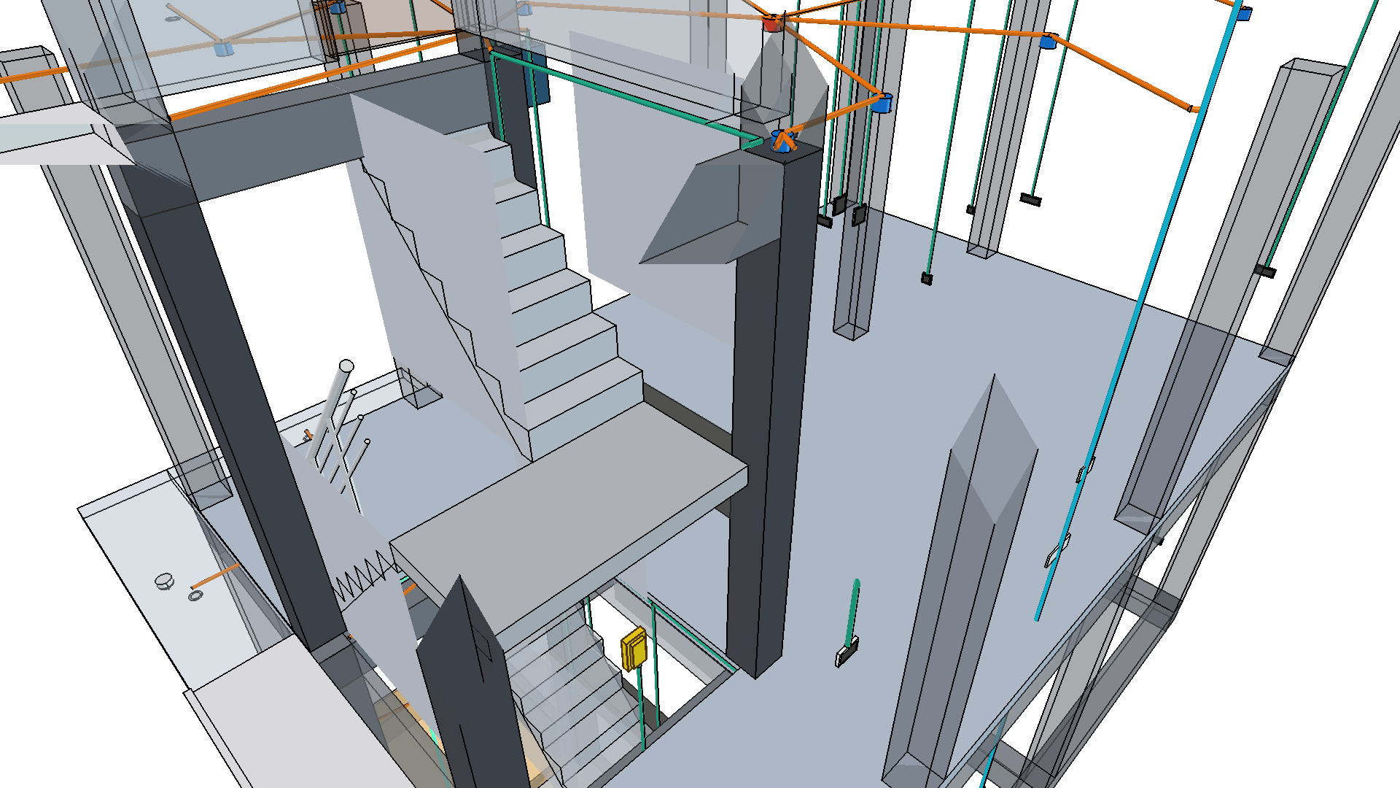
renders/pump_power_zoom.png
