Pradeeparul2/house-plan/renders/pump_view_from_inside.png

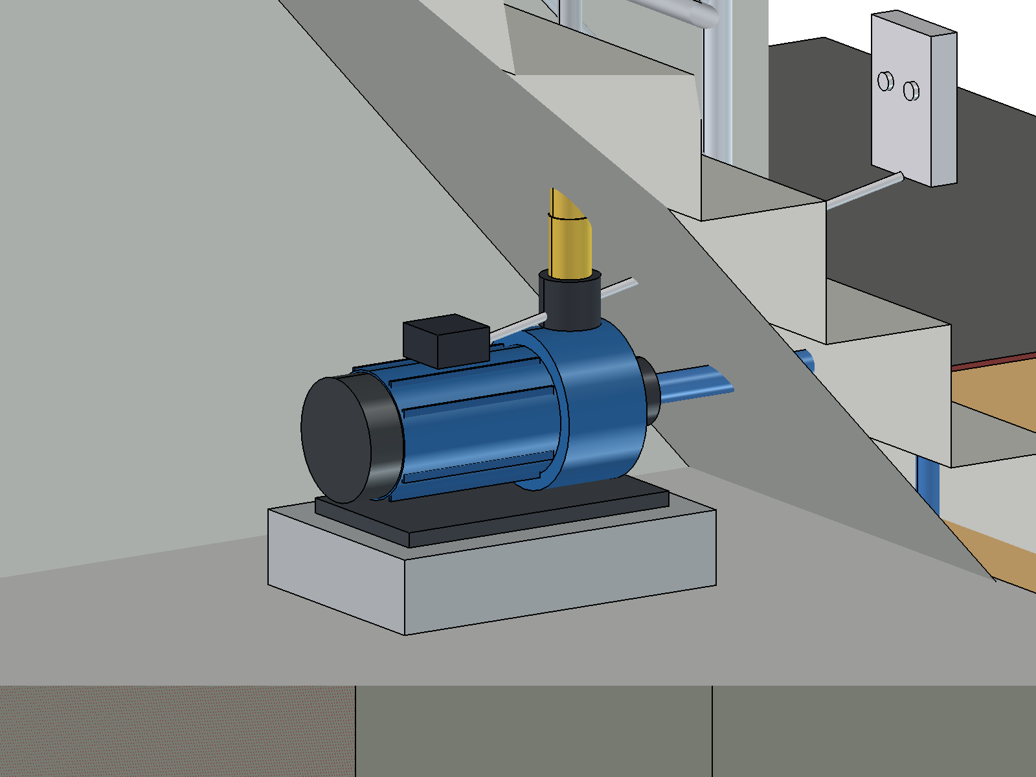
renders/pump_view_from_inside.png
