Pradeeparul2/house-plan/renders/pure_rcc_skeleton_frame.png

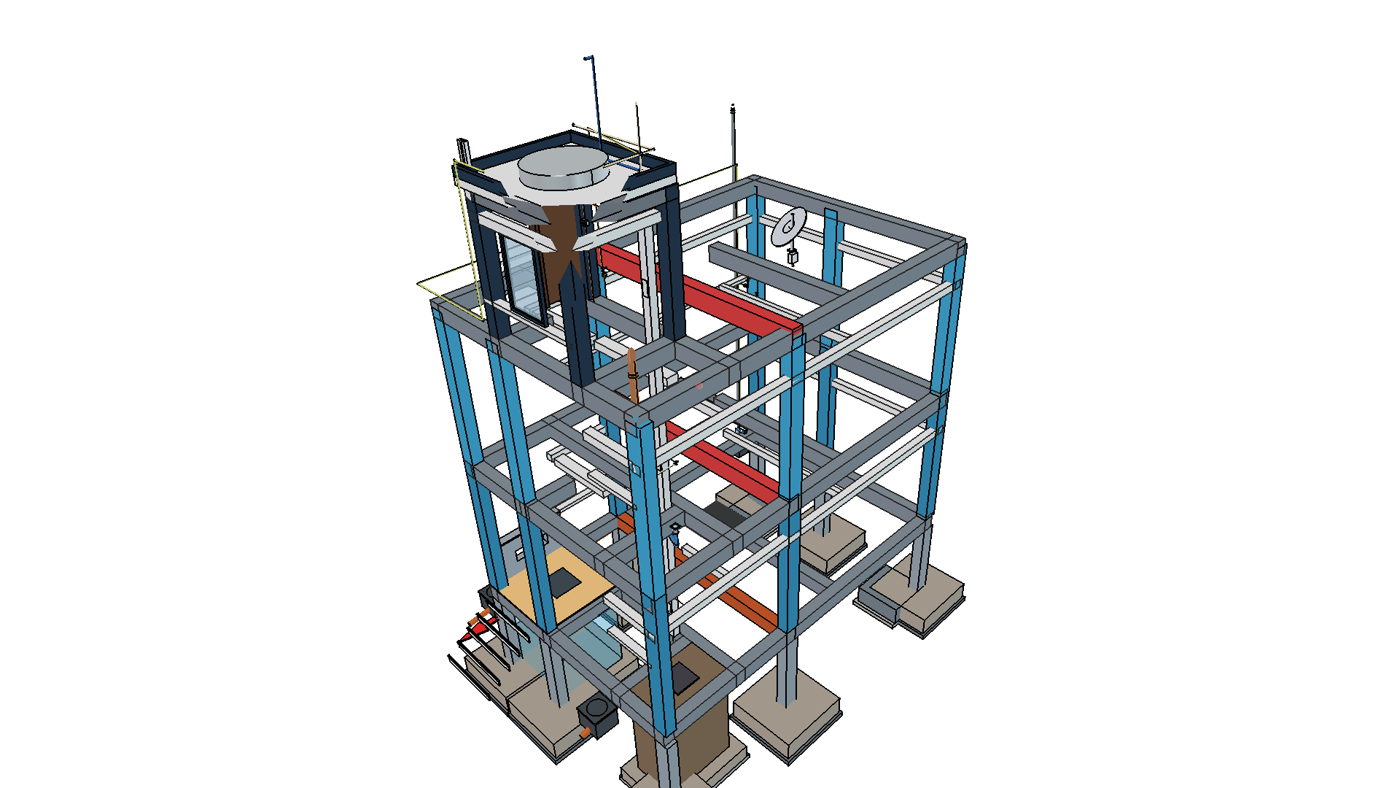
renders/pure_rcc_skeleton_frame.png
