Pradeeparul2/house-plan/renders/realistic_front_elevation_render.jpg

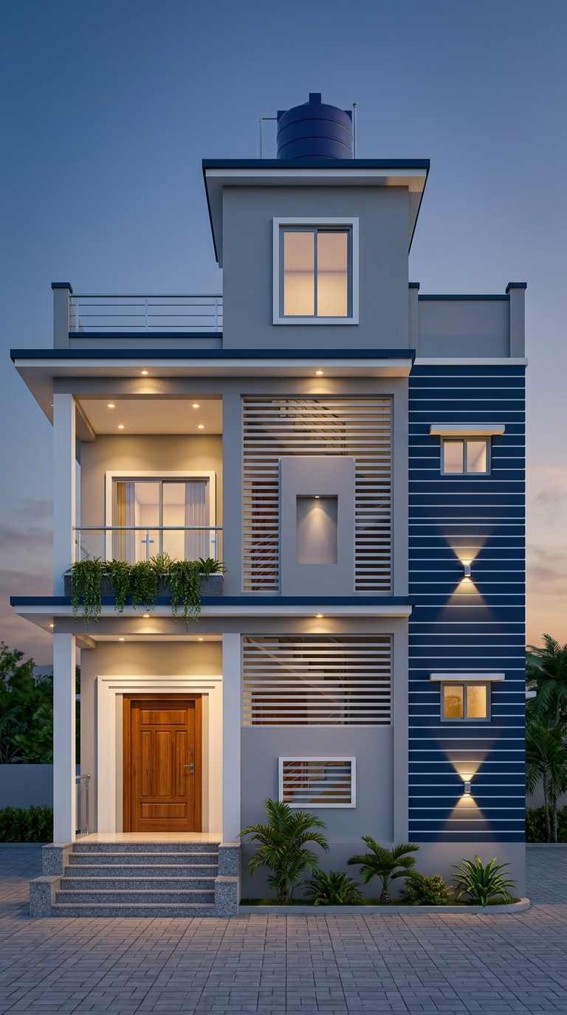
renders/realistic_front_elevation_render.jpg
