Pradeeparul2/house-plan/renders/rising_main_false_duct_staircase_view.png

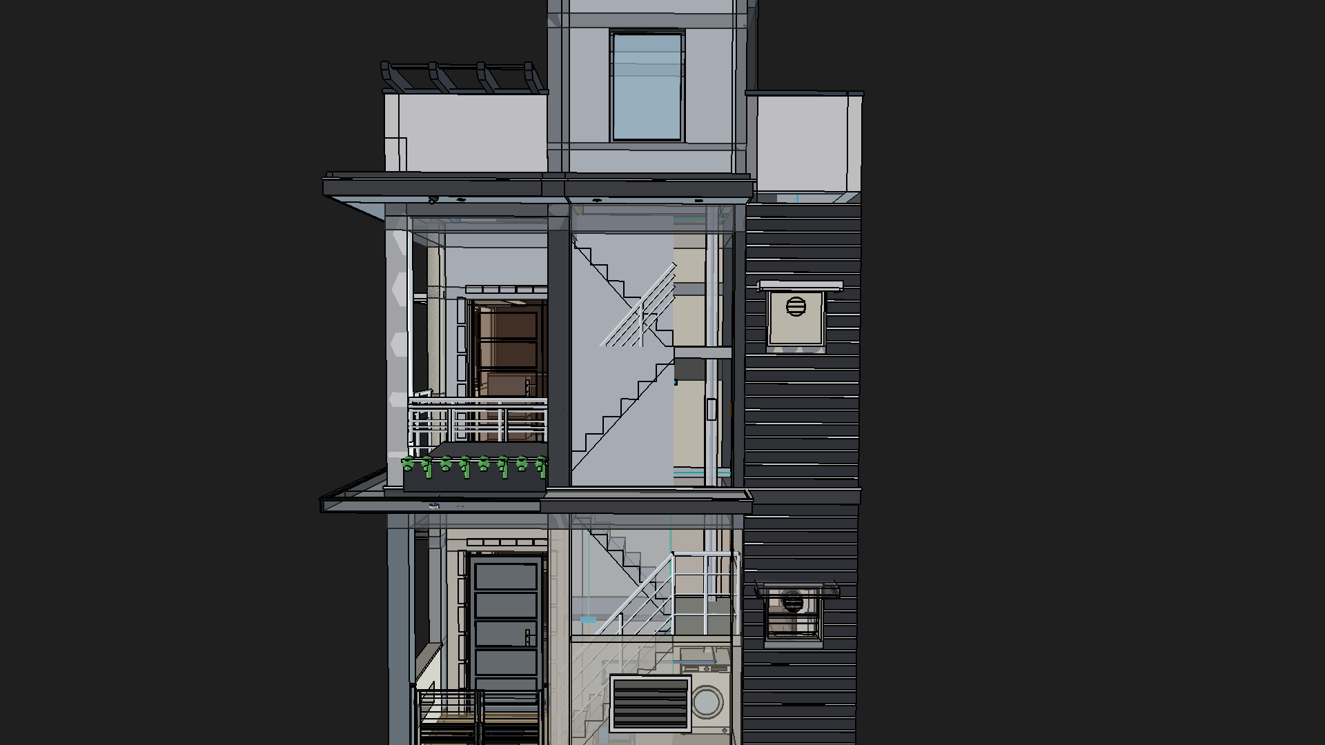
renders/rising_main_false_duct_staircase_view.png
