Pradeeparul2/house-plan/renders/rising_main_understair_pump_connection.png

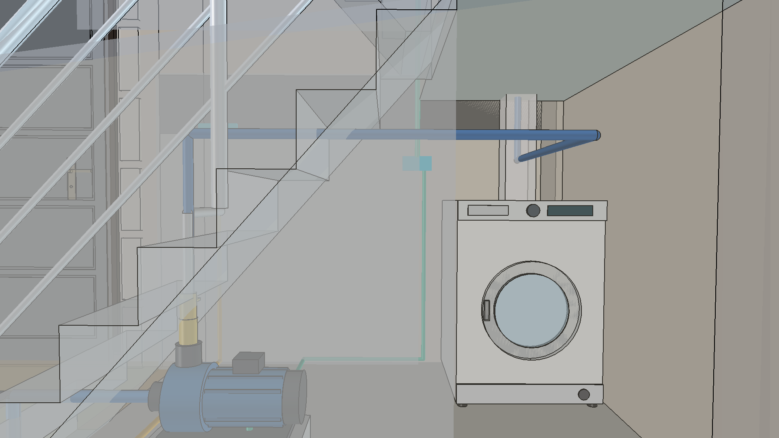
renders/rising_main_understair_pump_connection.png
