Pradeeparul2/house-plan/renders/rooftop_dish_tv_closeup.png

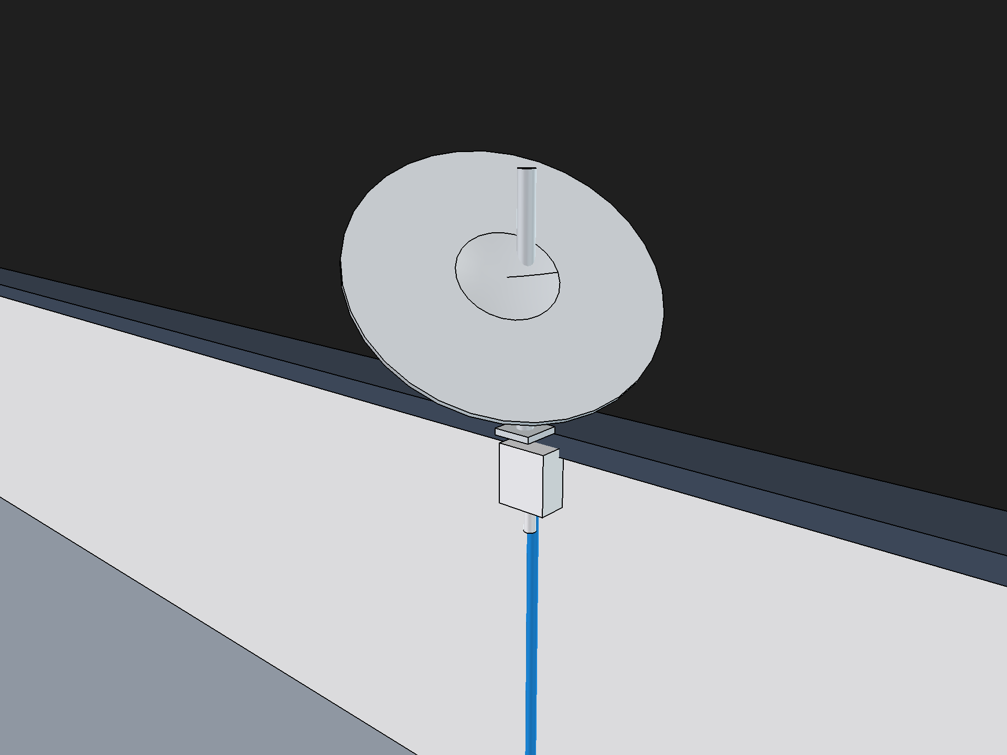
renders/rooftop_dish_tv_closeup.png
