Pradeeparul2/house-plan/renders/rooftop_dish_tv_terrace_view.png

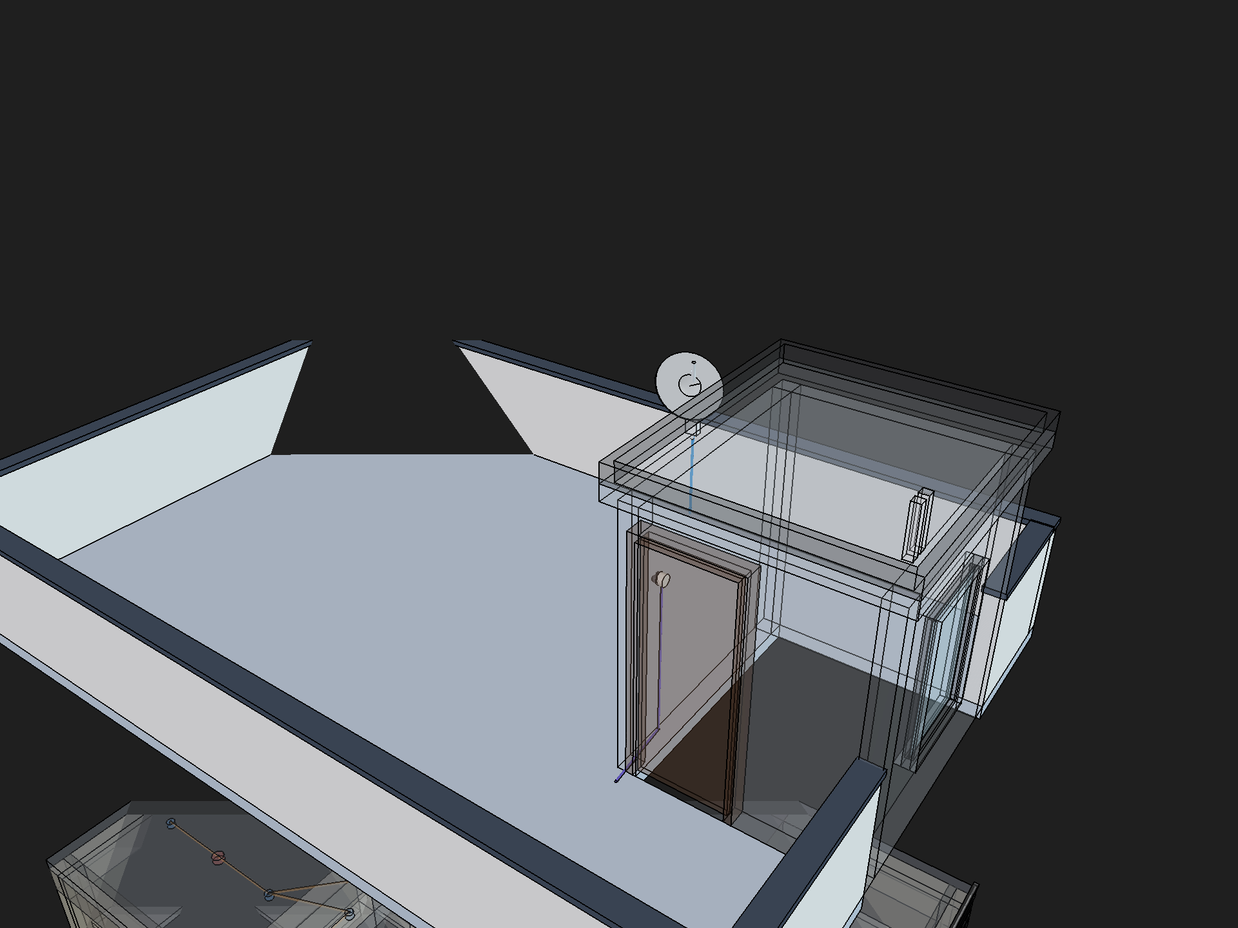
renders/rooftop_dish_tv_terrace_view.png
