Pradeeparul2/house-plan/renders/sb1_merged_into_staircase_switchboard_annotated.png

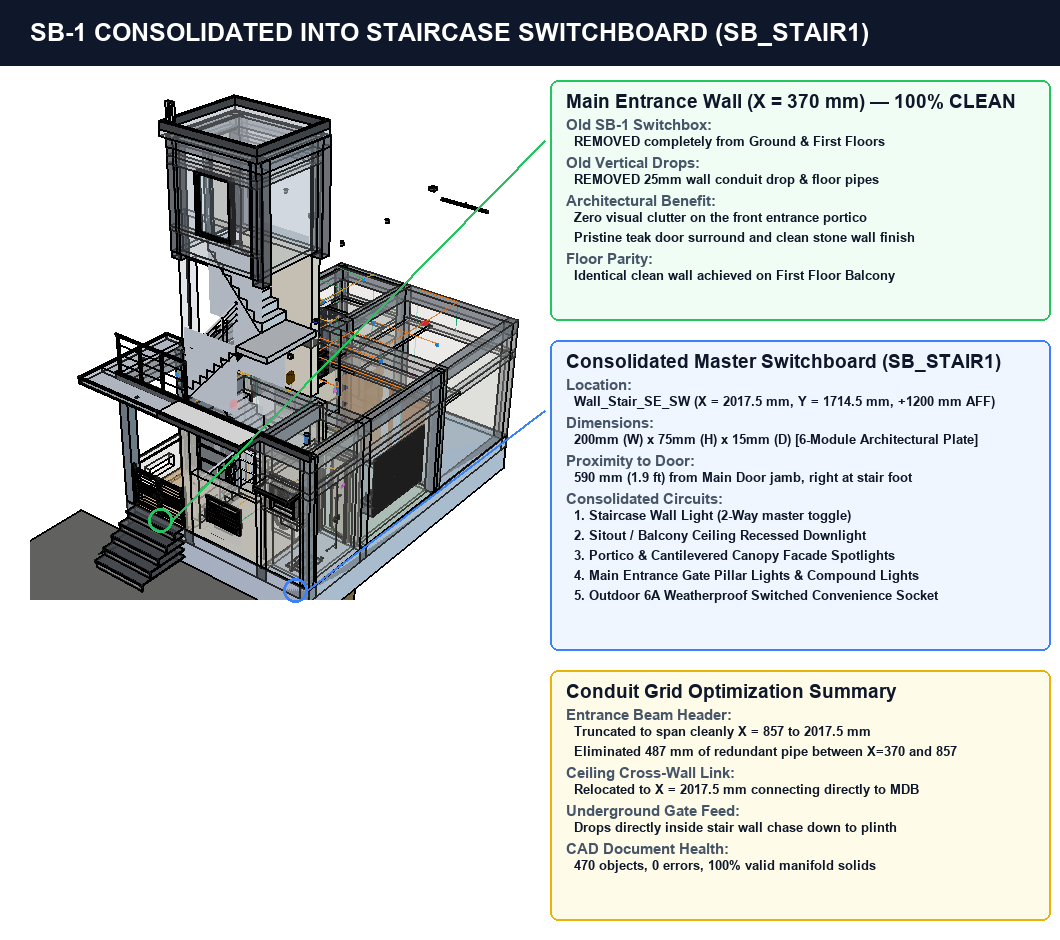
renders/sb1_merged_into_staircase_switchboard_annotated.png
