Pradeeparul2/house-plan/renders/sb2_beam_clearance_closeup.png

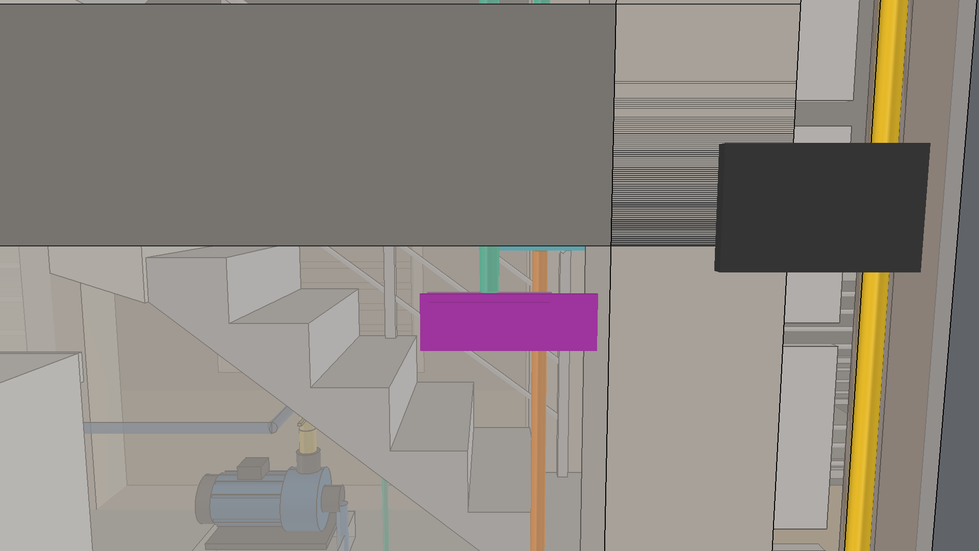
renders/sb2_beam_clearance_closeup.png
