Pradeeparul2/house-plan/renders/sb_util_integrated_pump_switch_annotated.png

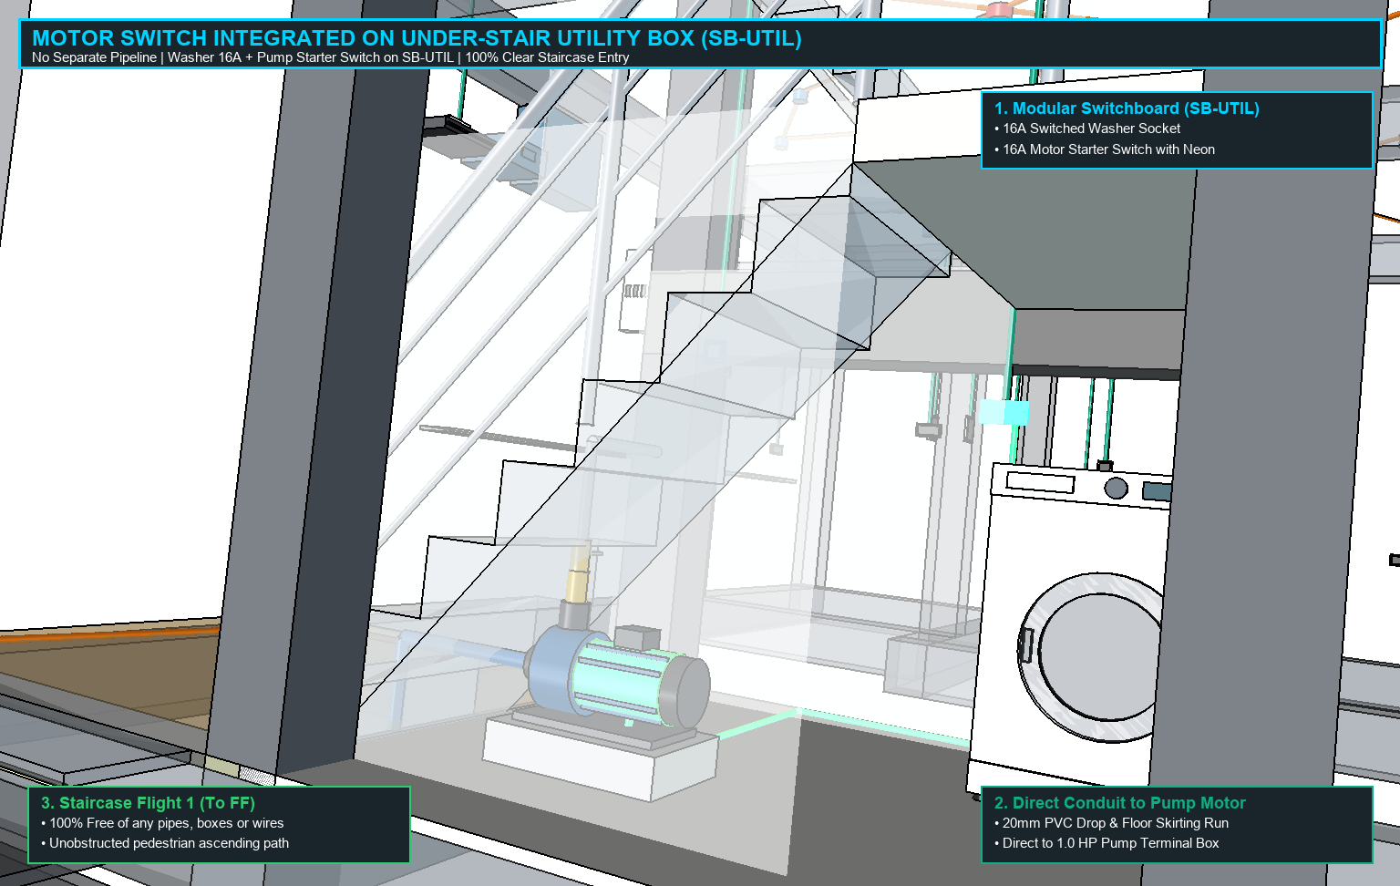
renders/sb_util_integrated_pump_switch_annotated.png
