Pradeeparul2/house-plan/renders/sb_util_repositioned_annotated.png

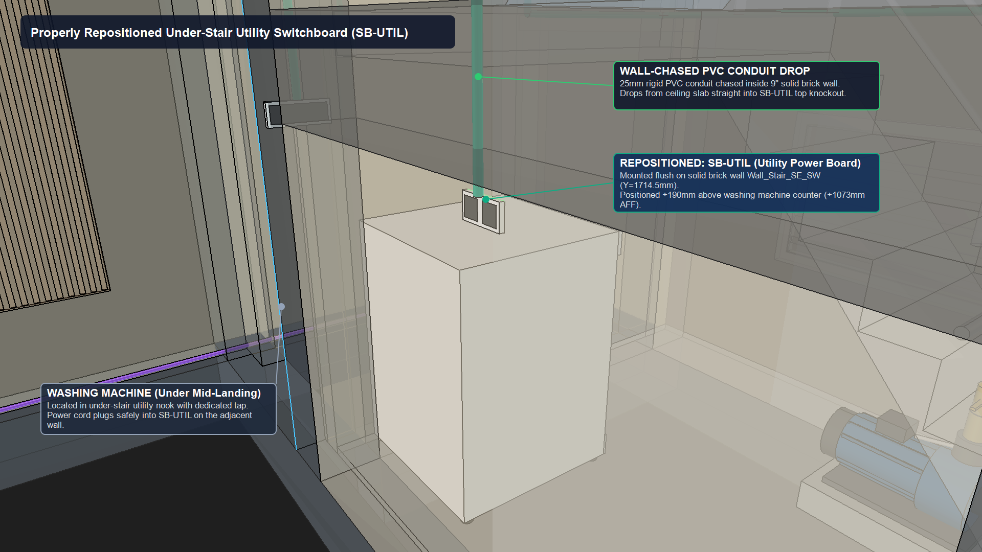
renders/sb_util_repositioned_annotated.png
