Pradeeparul2/house-plan/renders/shutoff_valve_east_boundary_closeup.png

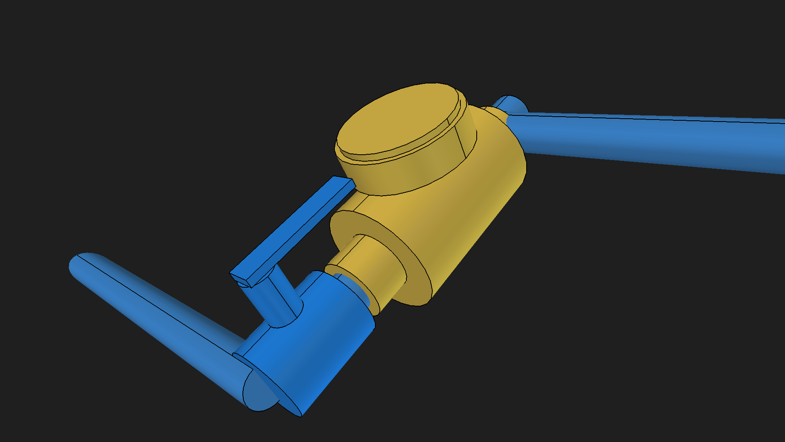
renders/shutoff_valve_east_boundary_closeup.png
