Pradeeparul2/house-plan/renders/shutoff_valve_undersink_tight_closeup.png

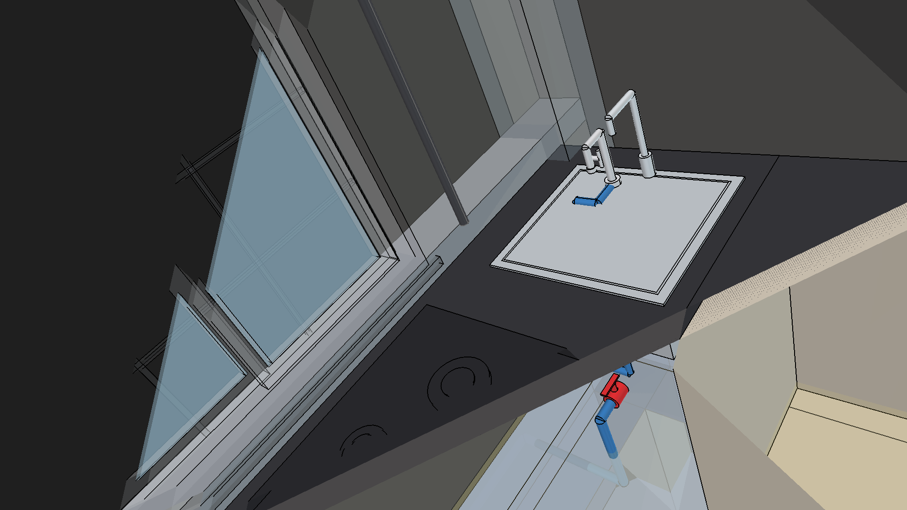
renders/shutoff_valve_undersink_tight_closeup.png
