Pradeeparul2/house-plan/renders/single_door_ff_closeup.png

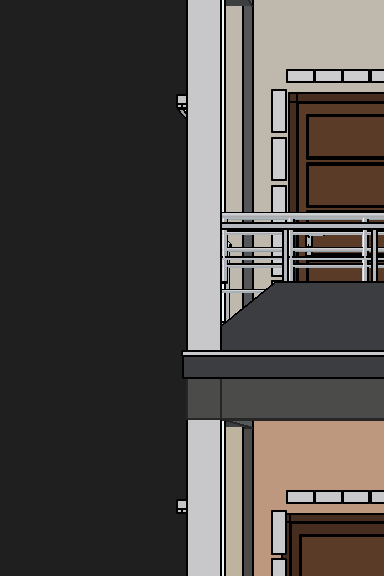
renders/single_door_ff_closeup.png
