Pradeeparul2/house-plan/renders/single_door_gf_closeup.png

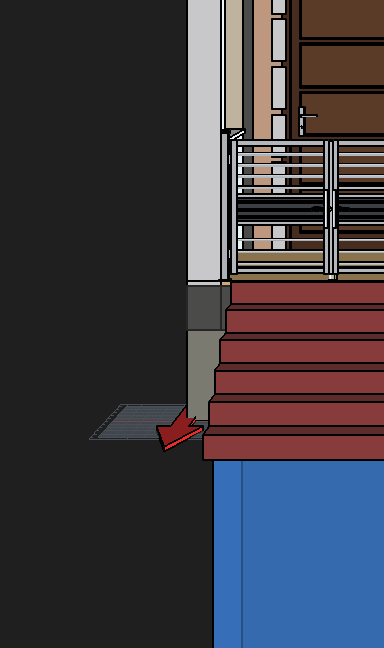
renders/single_door_gf_closeup.png
