Pradeeparul2/house-plan/renders/single_door_iso_perfect.png

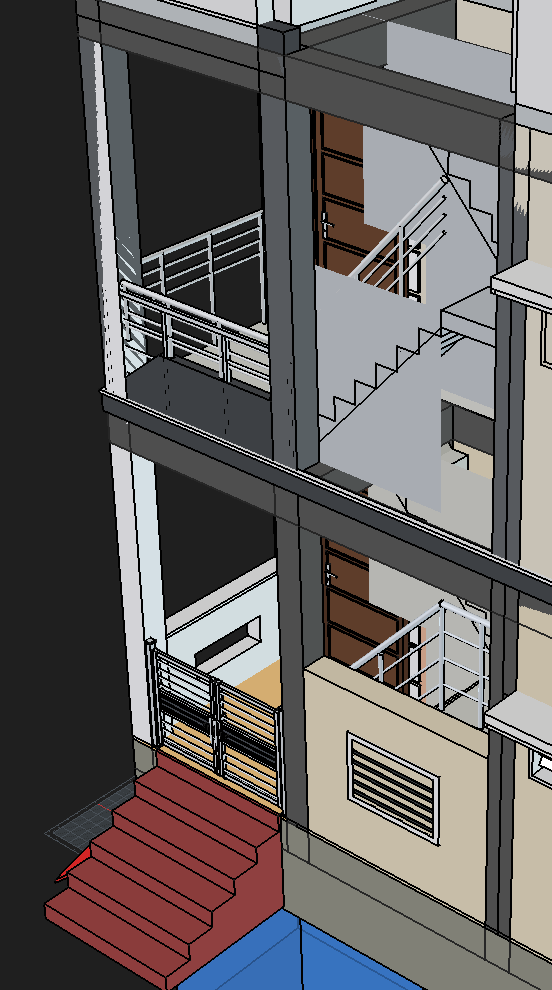
renders/single_door_iso_perfect.png
