Pradeeparul2/house-plan/renders/single_doors_both_floors.png

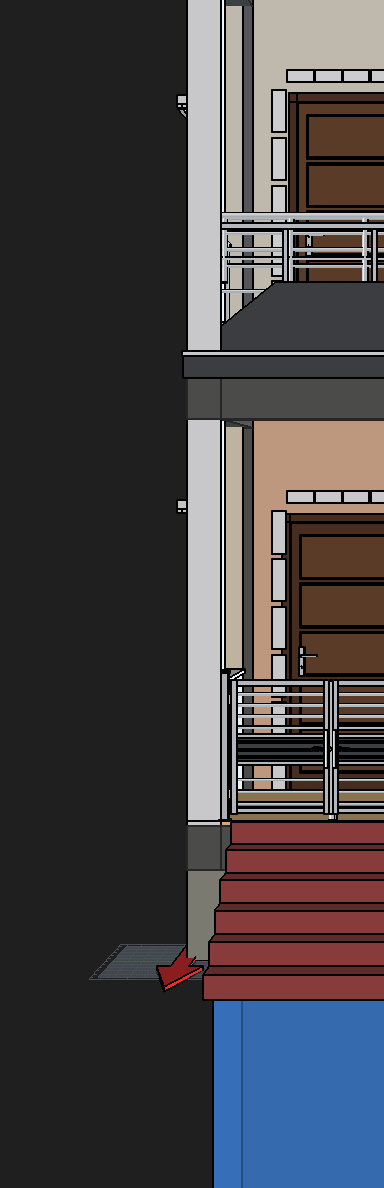
renders/single_doors_both_floors.png
