Pradeeparul2/house-plan/renders/sitout_electrical_front_view.png

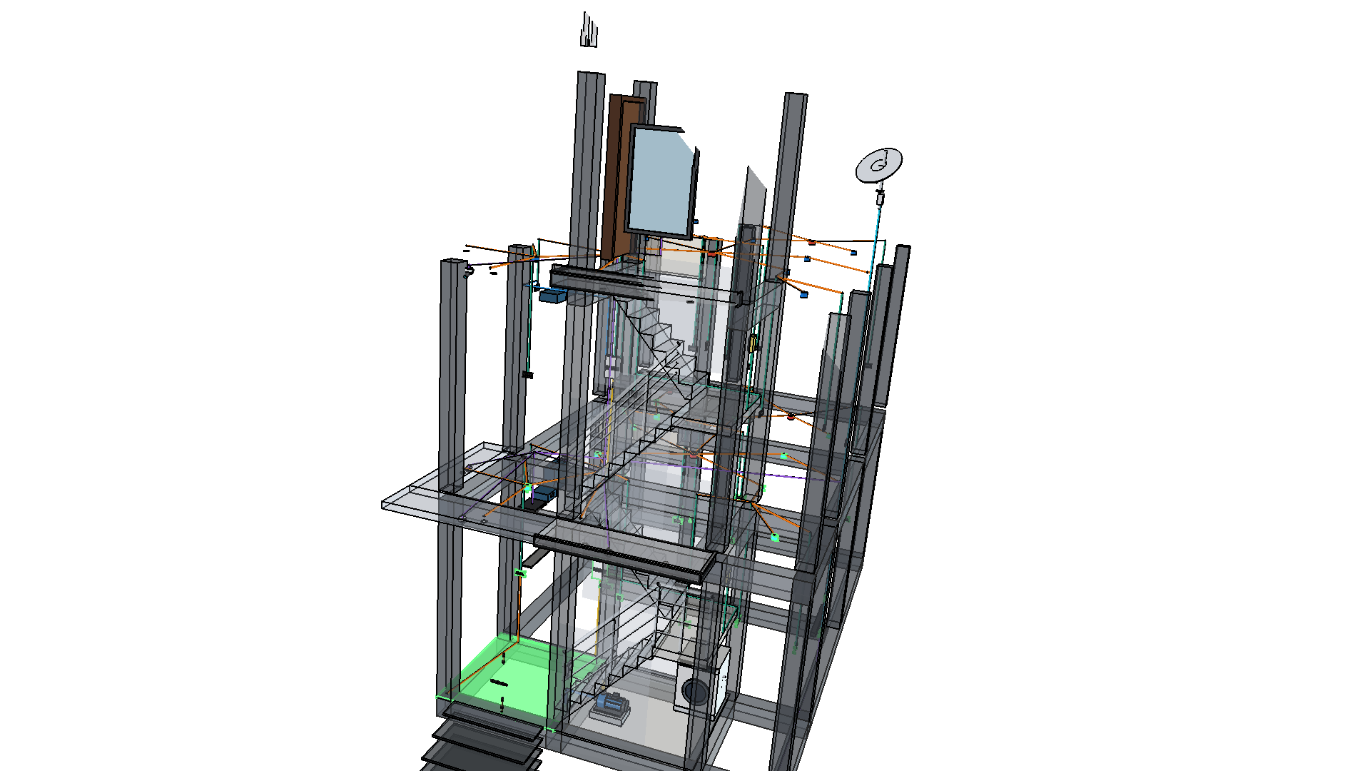
renders/sitout_electrical_front_view.png
