Pradeeparul2/house-plan/renders/sitout_electrical_pipelines_closeup_focused.png

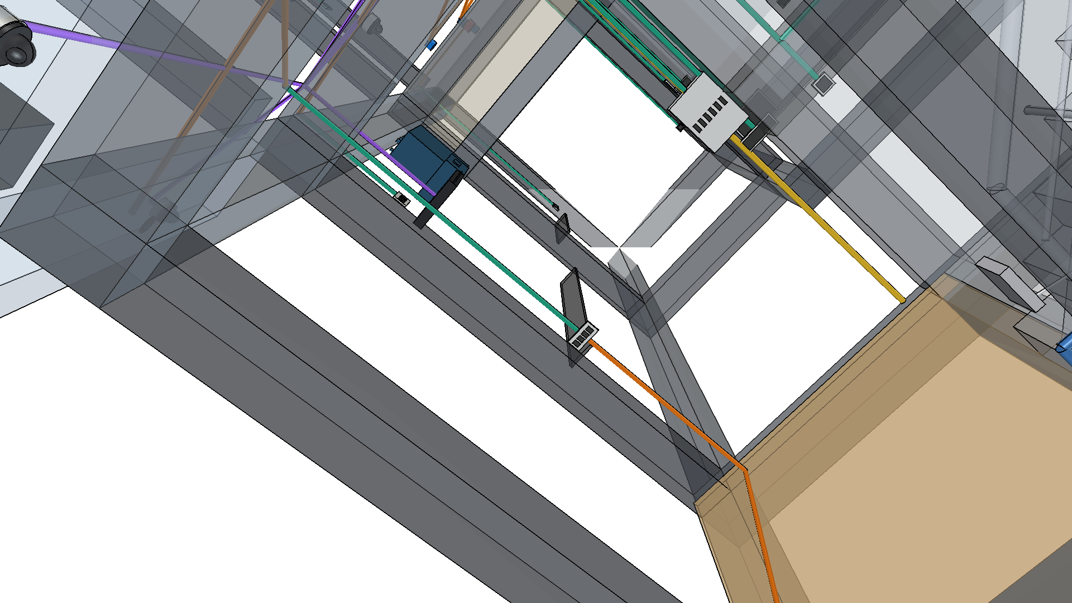
renders/sitout_electrical_pipelines_closeup_focused.png
