Pradeeparul2/house-plan/renders/sitout_electrical_pipelines_iso.png

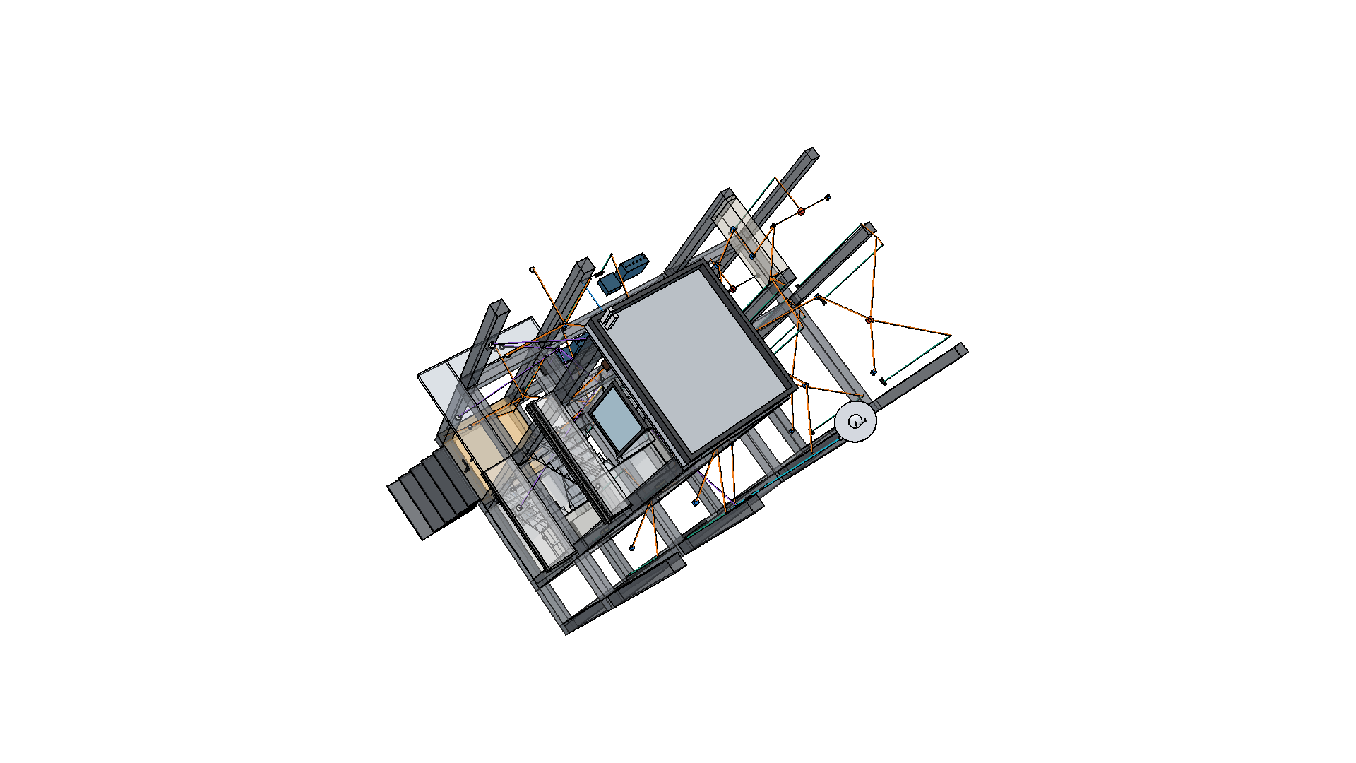
renders/sitout_electrical_pipelines_iso.png
