Pradeeparul2/house-plan/renders/stair_entrance_closeup_south.png

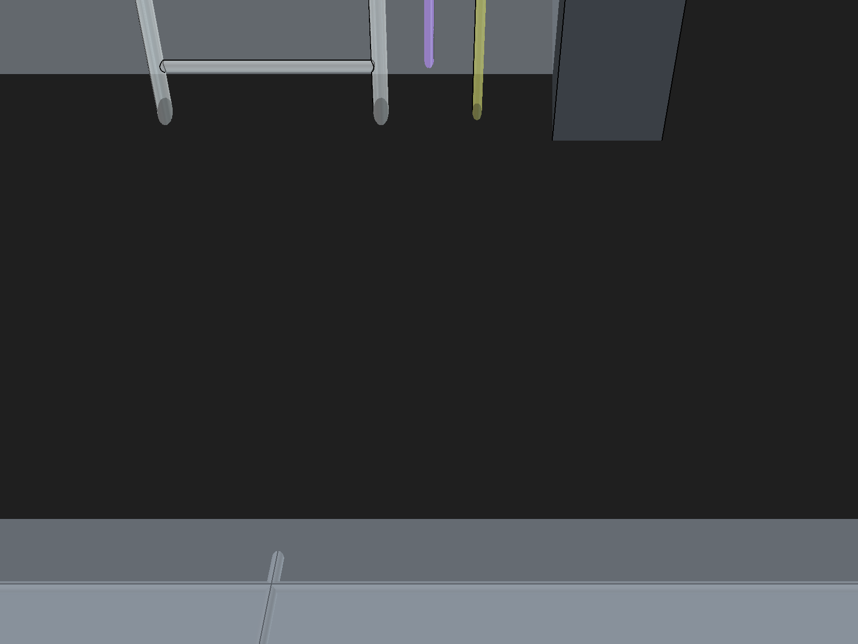
renders/stair_entrance_closeup_south.png
