Pradeeparul2/house-plan/renders/stair_pipes_highlighted_looking_up.png

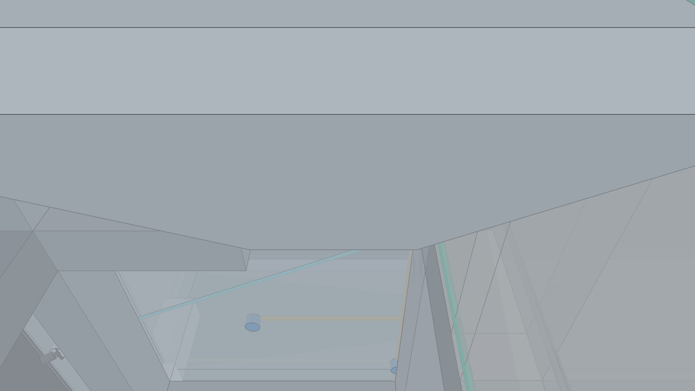
renders/stair_pipes_highlighted_looking_up.png
