Pradeeparul2/house-plan/renders/stair_pipes_highlighted_se.png

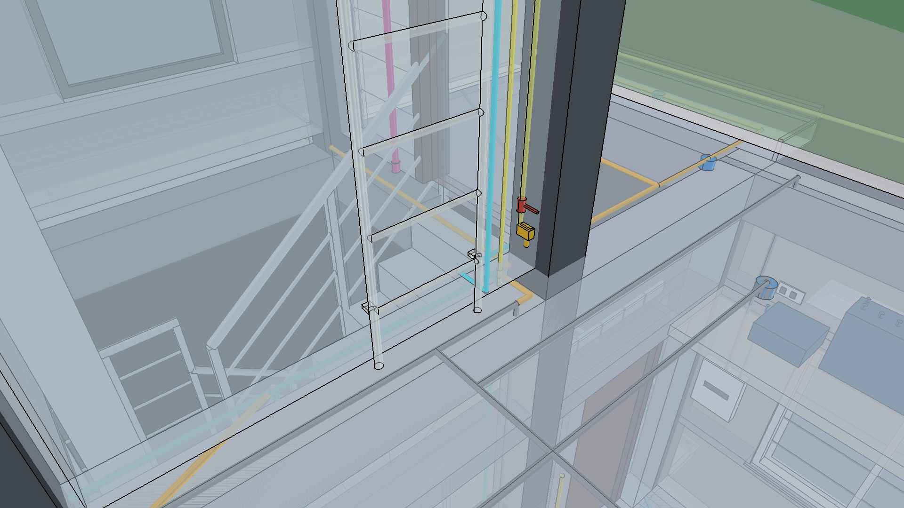
renders/stair_pipes_highlighted_se.png
