Pradeeparul2/house-plan/renders/stair_void_terrace_view_cleared.png

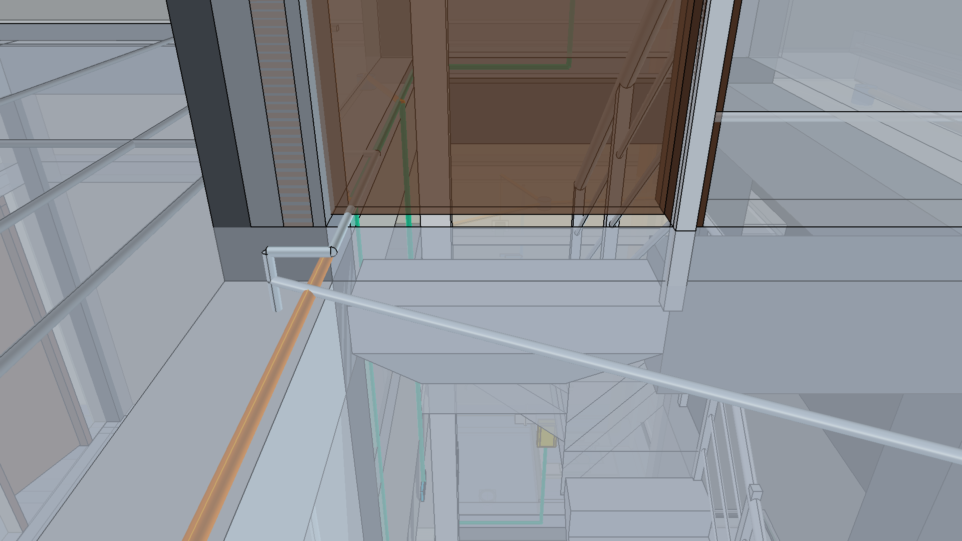
renders/stair_void_terrace_view_cleared.png
