Pradeeparul2/house-plan/renders/staircase_current_light_side.png

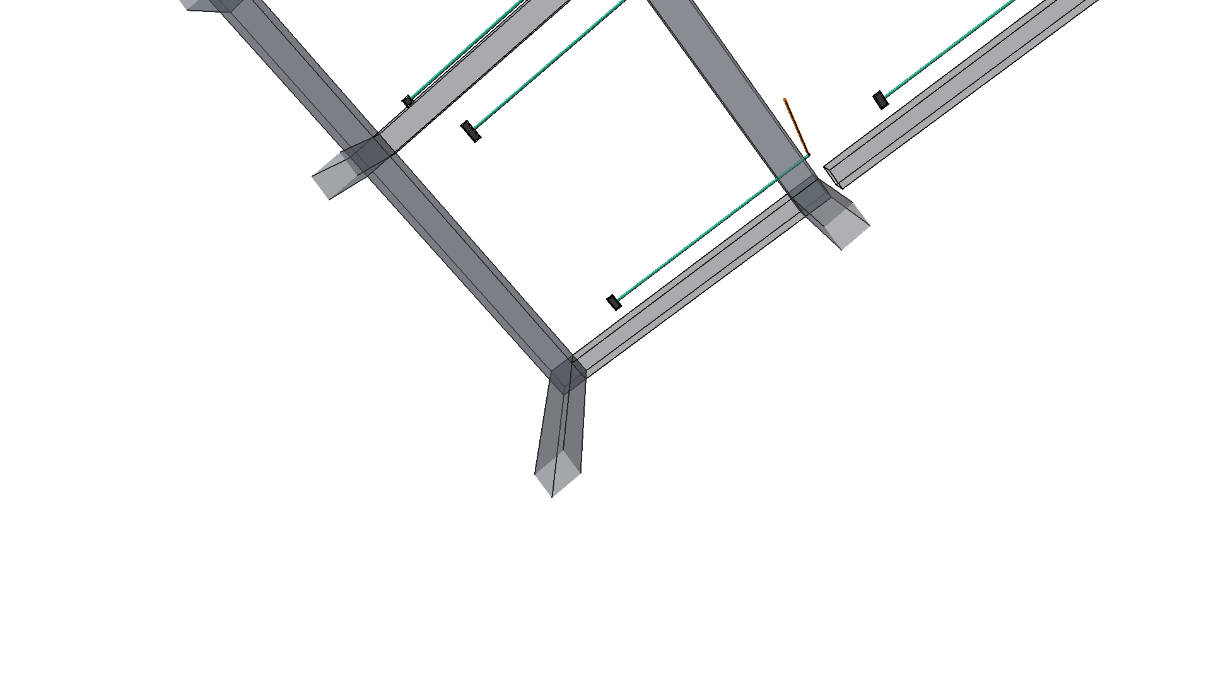
renders/staircase_current_light_side.png
