Pradeeparul2/house-plan/renders/staircase_electrical_fit_selection.png

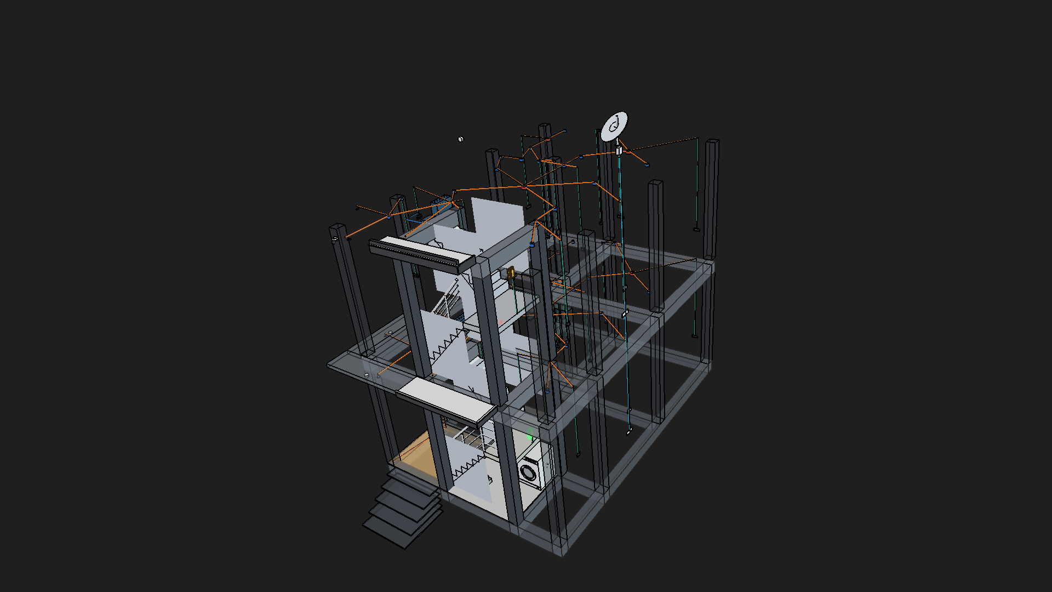
renders/staircase_electrical_fit_selection.png
