Pradeeparul2/house-plan/renders/staircase_electrical_located_annotated.png

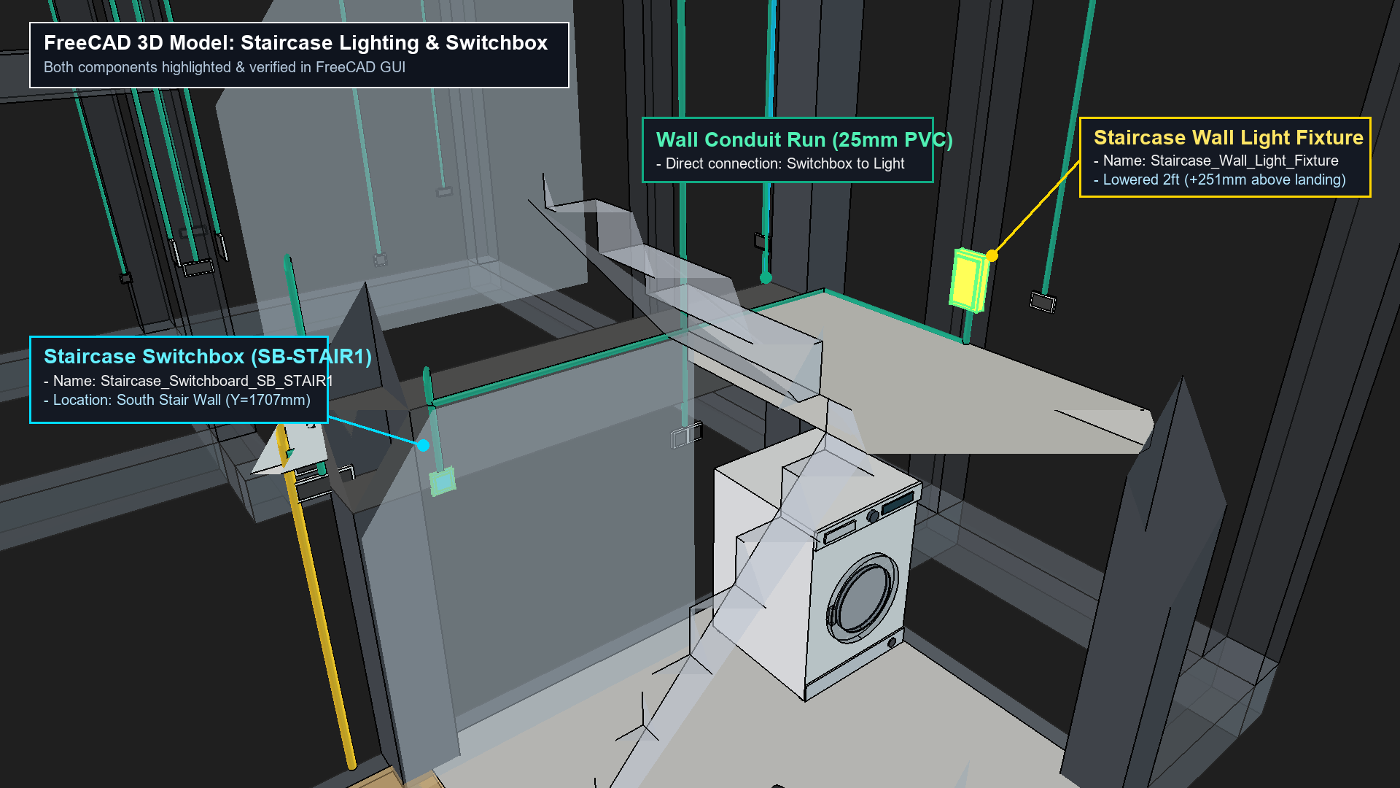
renders/staircase_electrical_located_annotated.png
