Pradeeparul2/house-plan/renders/staircase_lowered_light_clean_front.png

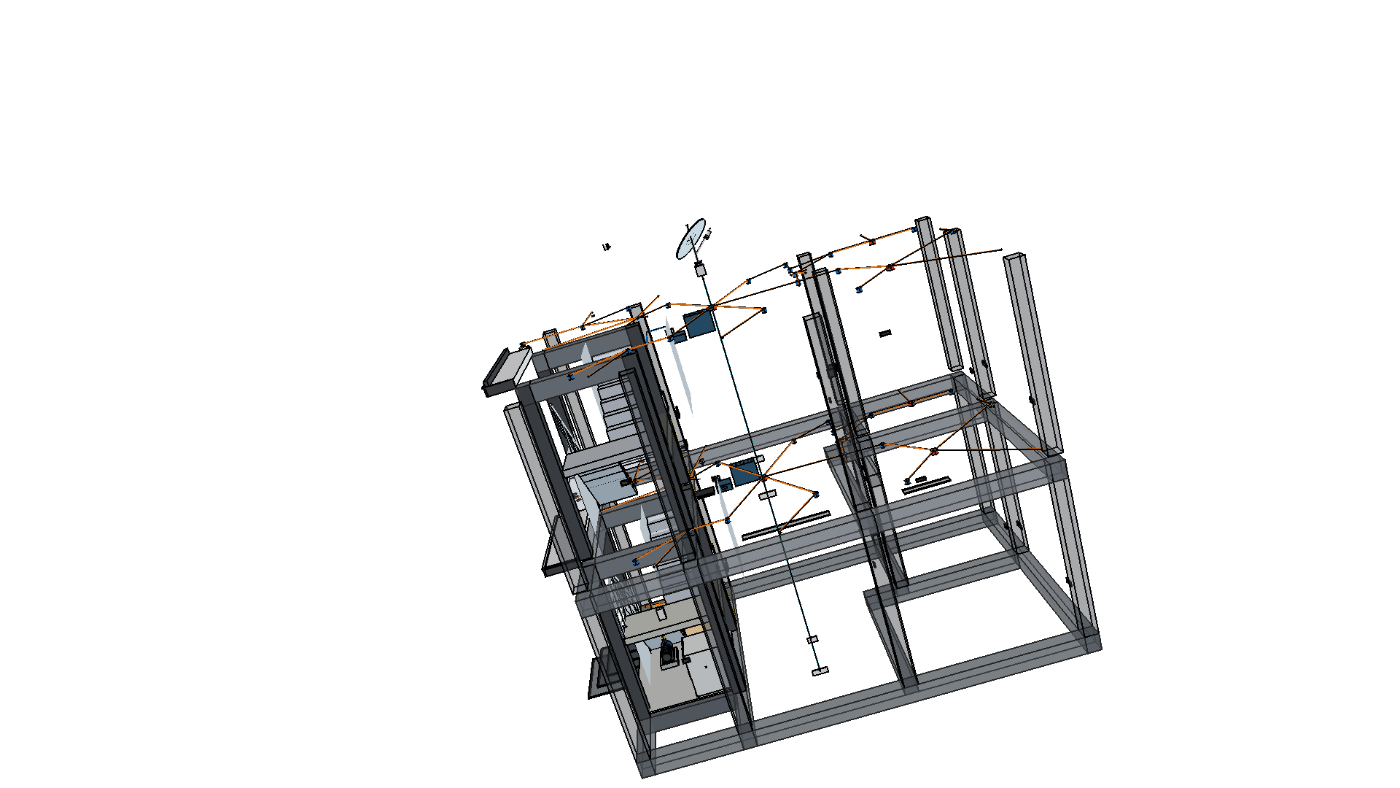
renders/staircase_lowered_light_clean_front.png
