Pradeeparul2/house-plan/renders/staircase_south_wall_routing_iso.png

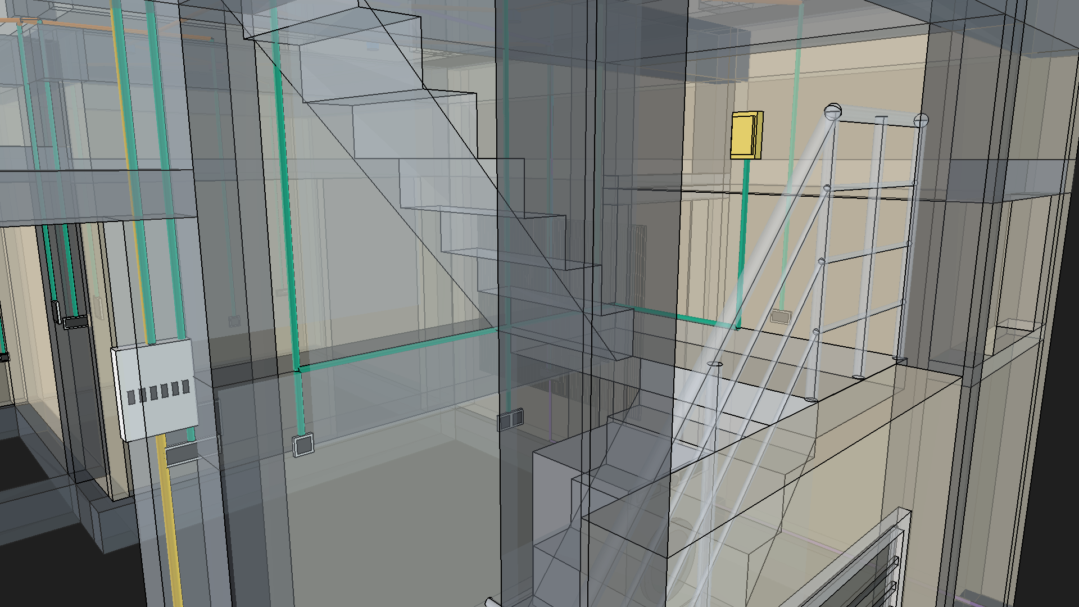
renders/staircase_south_wall_routing_iso.png
