Pradeeparul2/house-plan/renders/staircase_switchbox_closeup_annotated.png

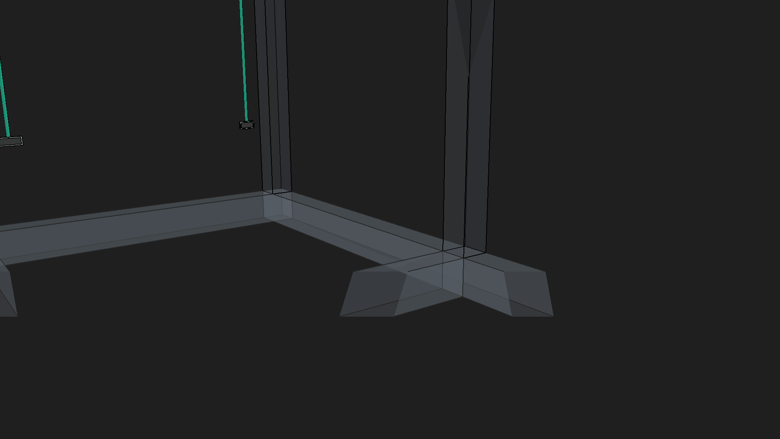
renders/staircase_switchbox_closeup_annotated.png
