Pradeeparul2/house-plan/renders/staircase_switchbox_south_wall_closeup.png

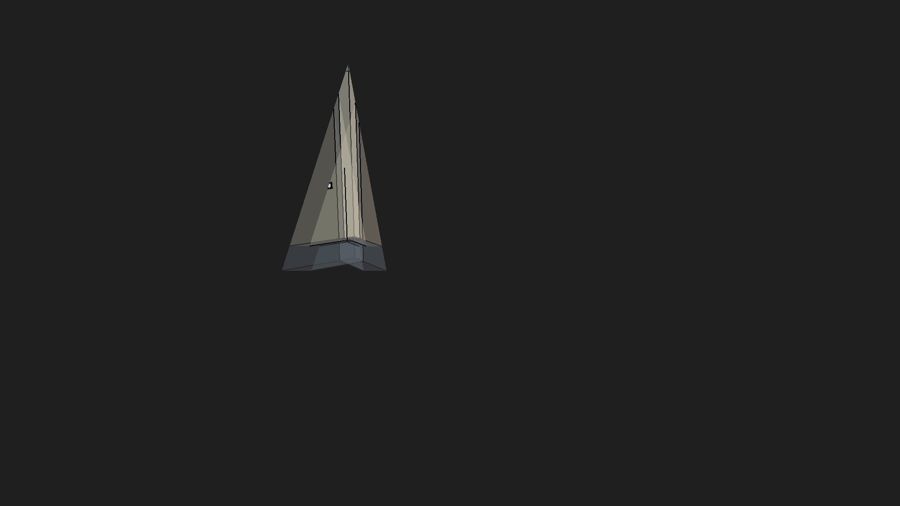
renders/staircase_switchbox_south_wall_closeup.png
