Pradeeparul2/house-plan/renders/staircase_switchboxes_explained.png

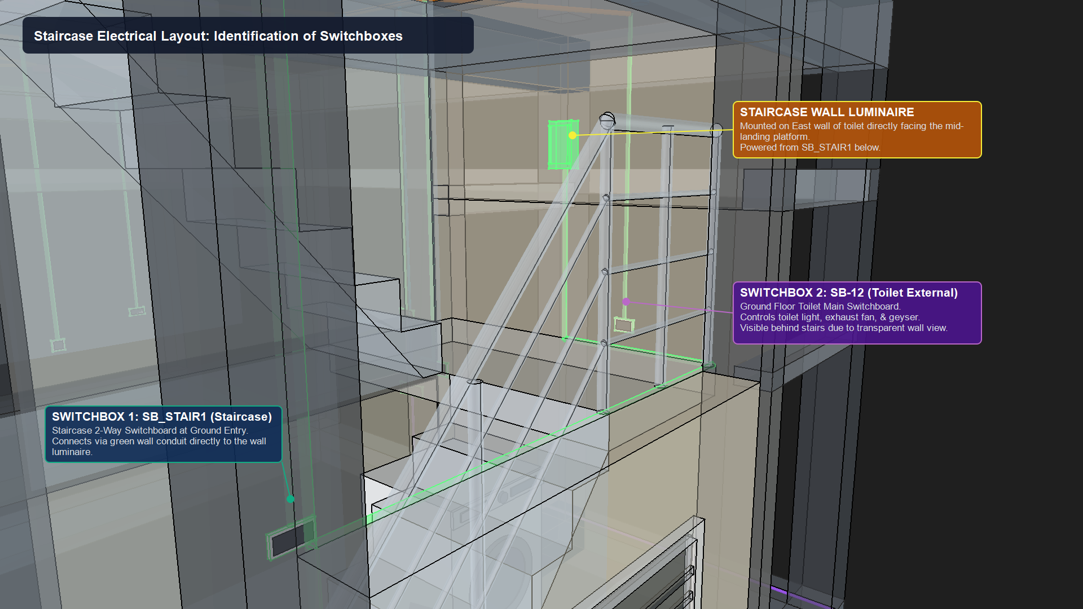
renders/staircase_switchboxes_explained.png
