Pradeeparul2/house-plan/renders/staircase_toilet_east_wall_light_closeup.png

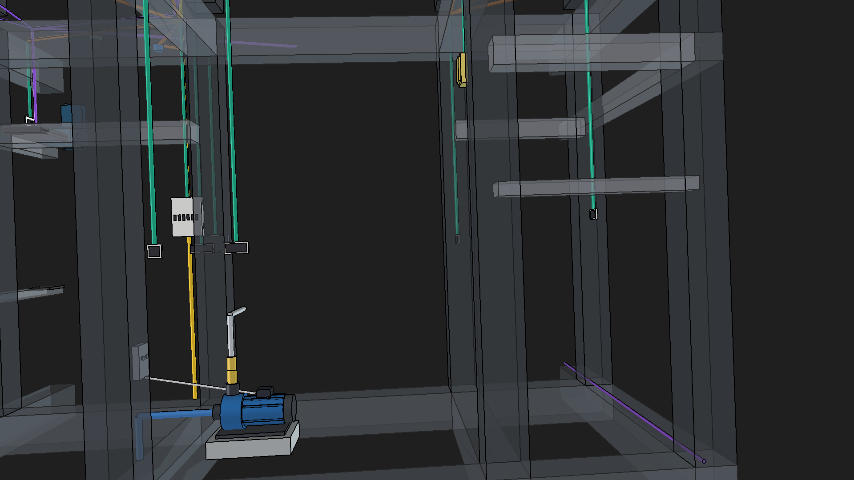
renders/staircase_toilet_east_wall_light_closeup.png
