Pradeeparul2/house-plan/renders/staircase_wall_light_2ft_below_ff_landing_fit.png

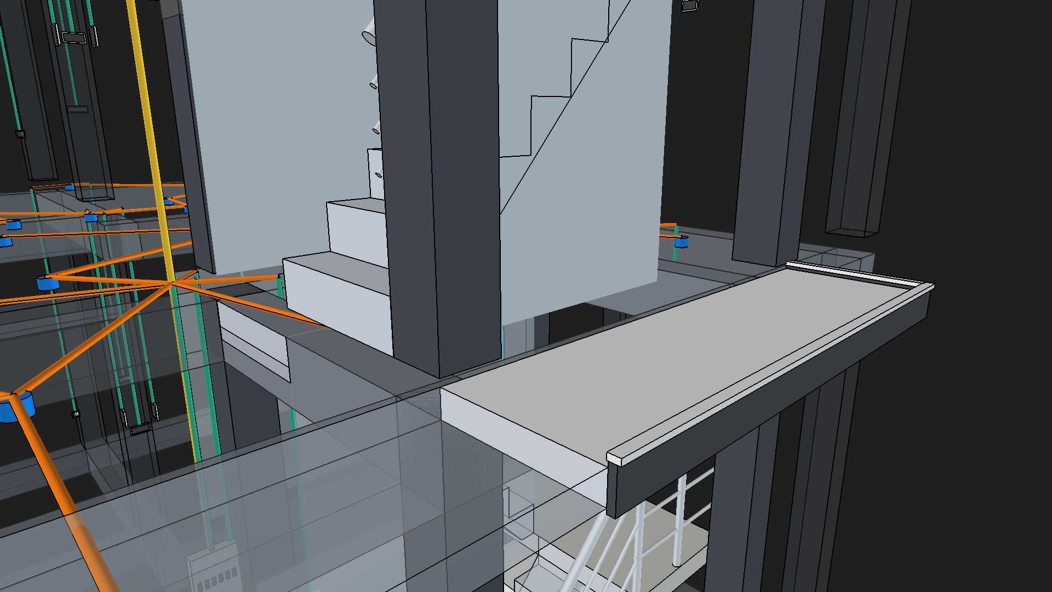
renders/staircase_wall_light_2ft_below_ff_landing_fit.png
