Pradeeparul2/house-plan/renders/staircase_wall_lights_two_storey_iso.png

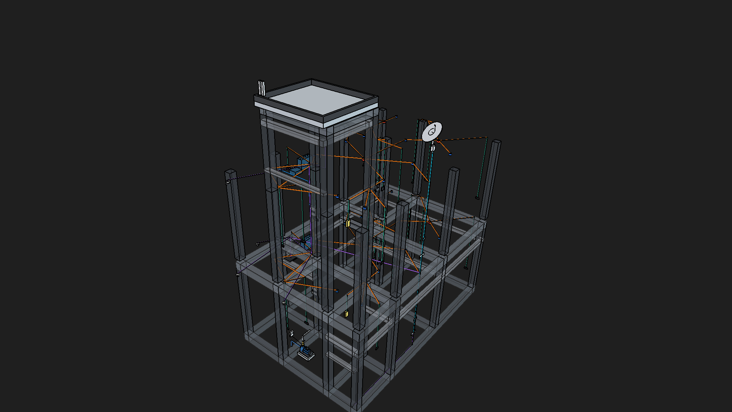
renders/staircase_wall_lights_two_storey_iso.png
