Pradeeparul2/house-plan/renders/staircase_west_to_east_view.png

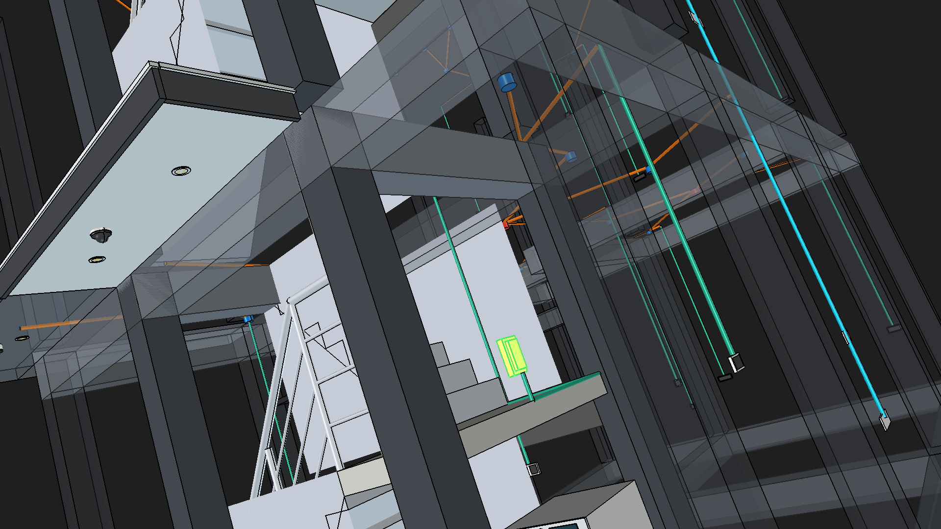
renders/staircase_west_to_east_view.png
