Pradeeparul2/house-plan/renders/structural_elements_top_plan.png

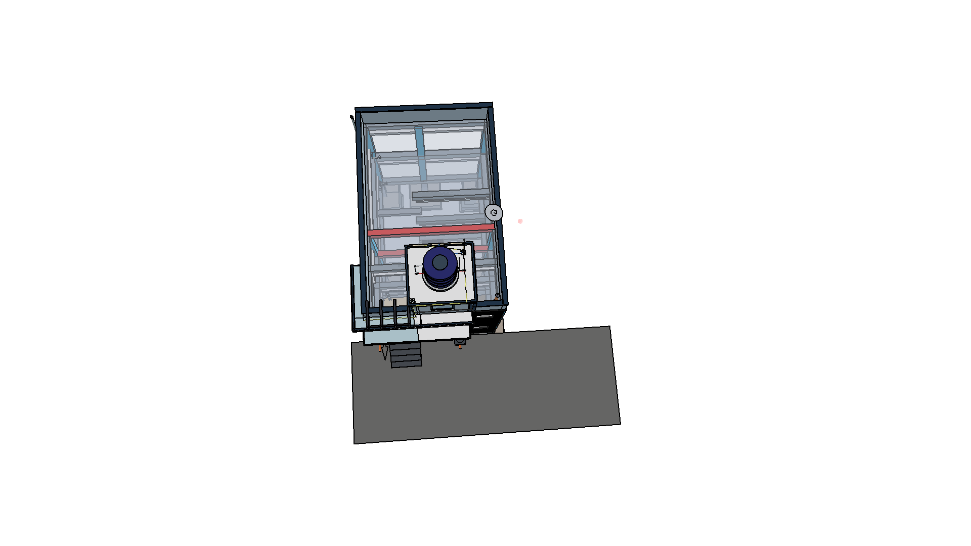
renders/structural_elements_top_plan.png
