Pradeeparul2/house-plan/renders/structural_frame_only_front.png

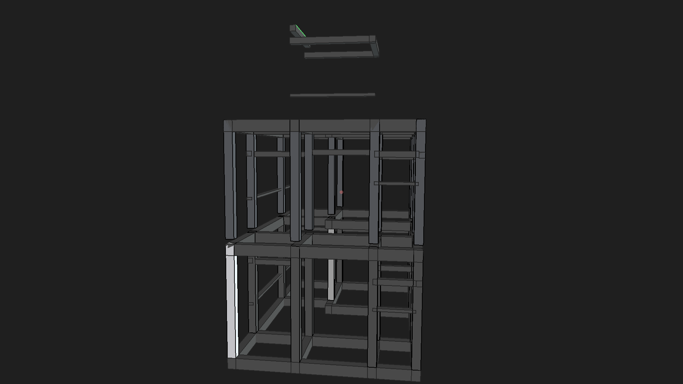
renders/structural_frame_only_front.png
