Pradeeparul2/house-plan/renders/structural_frame_plumbing_east.png

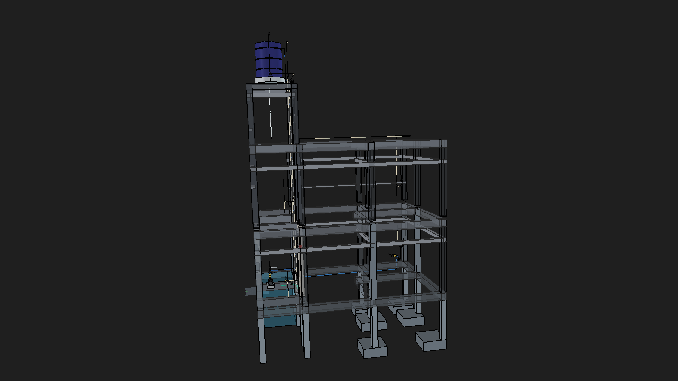
renders/structural_frame_plumbing_east.png
