Pradeeparul2/house-plan/renders/structural_frame_plumbing_updated.png

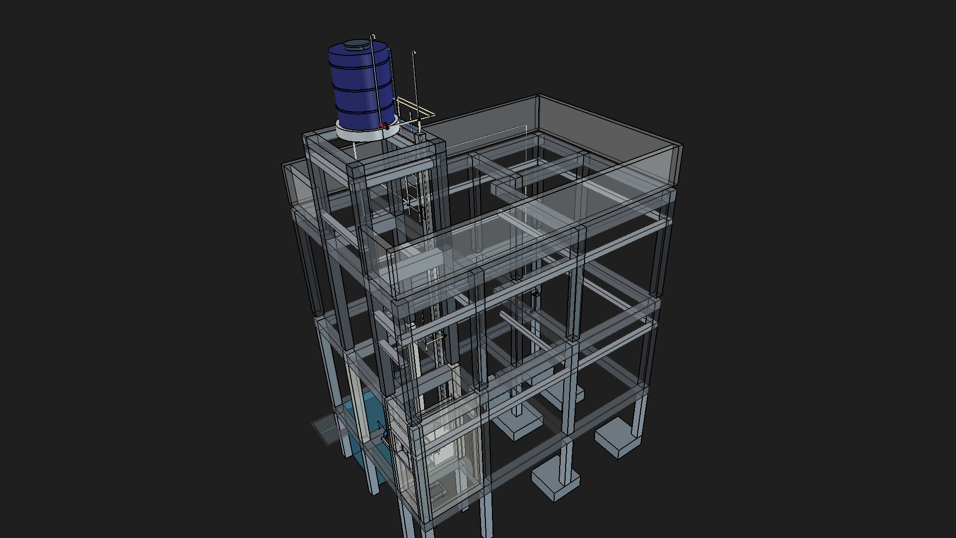
renders/structural_frame_plumbing_updated.png
