Pradeeparul2/house-plan/renders/structural_frame_with_mumty_columns.png

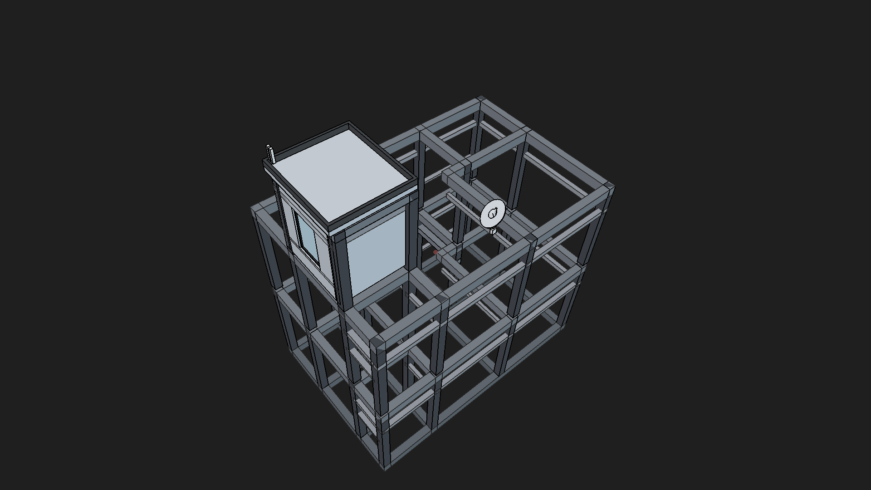
renders/structural_frame_with_mumty_columns.png
