Pradeeparul2/house-plan/renders/substructure_both_tanks_raised_iso.png

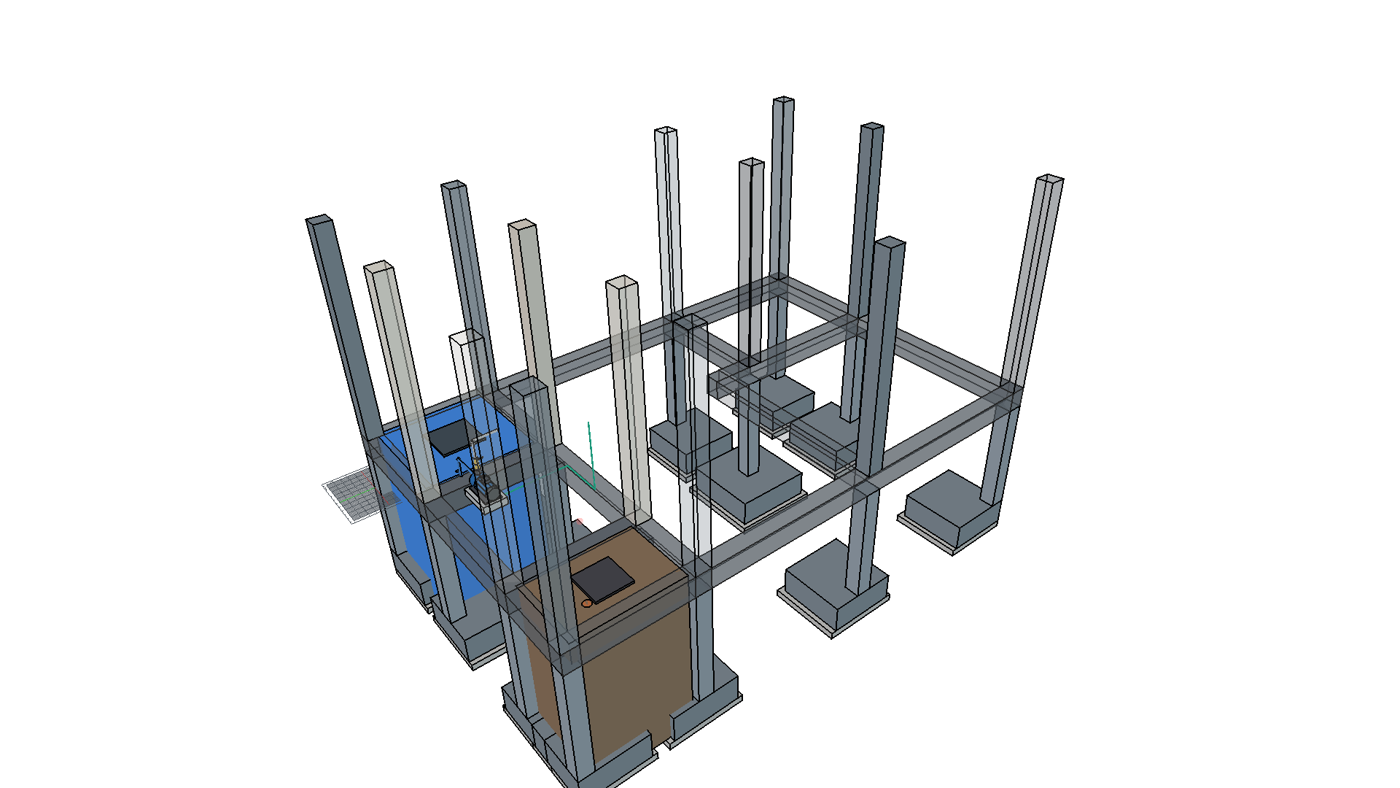
renders/substructure_both_tanks_raised_iso.png
