Pradeeparul2/house-plan/renders/substructure_ground_transition_closeup.png

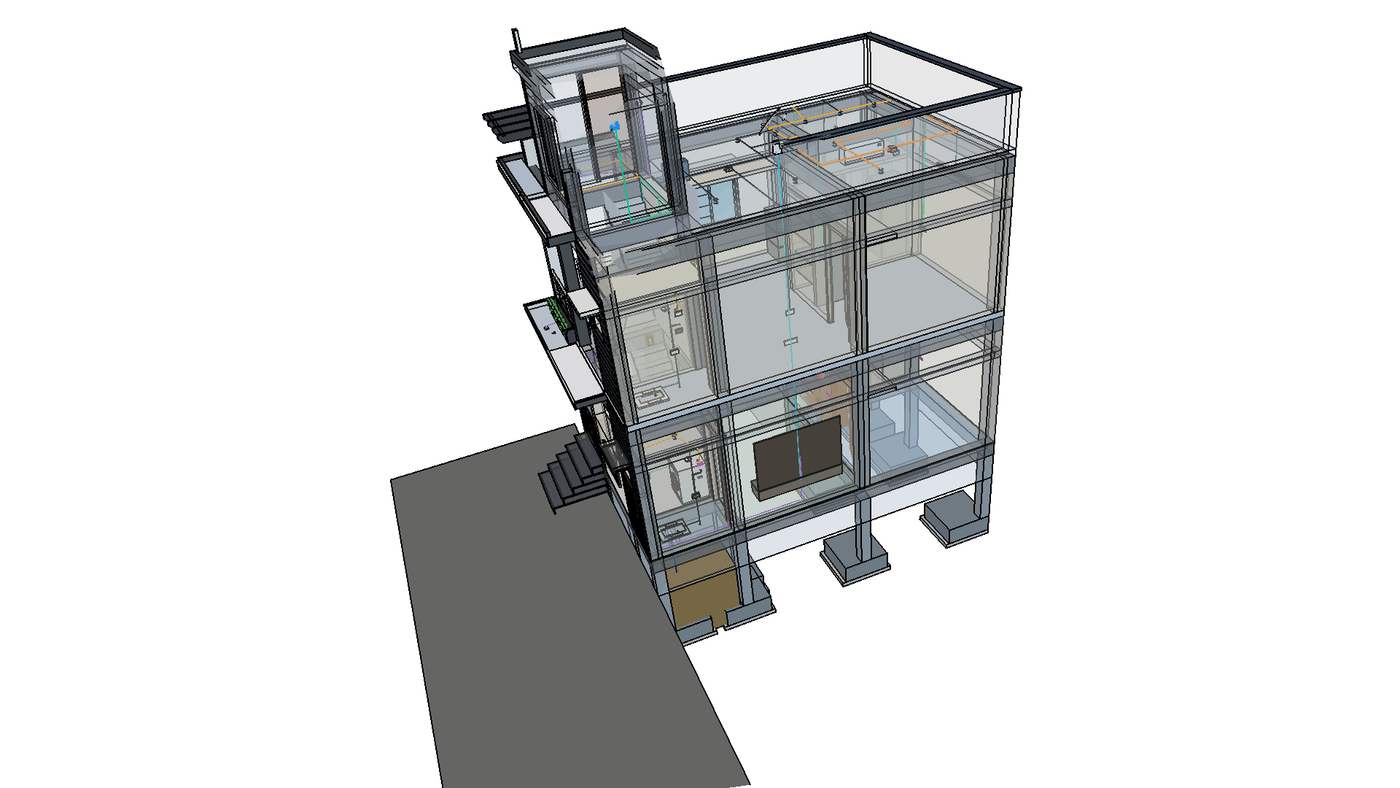
renders/substructure_ground_transition_closeup.png
