Pradeeparul2/house-plan/renders/substructure_zero_collision_front.png

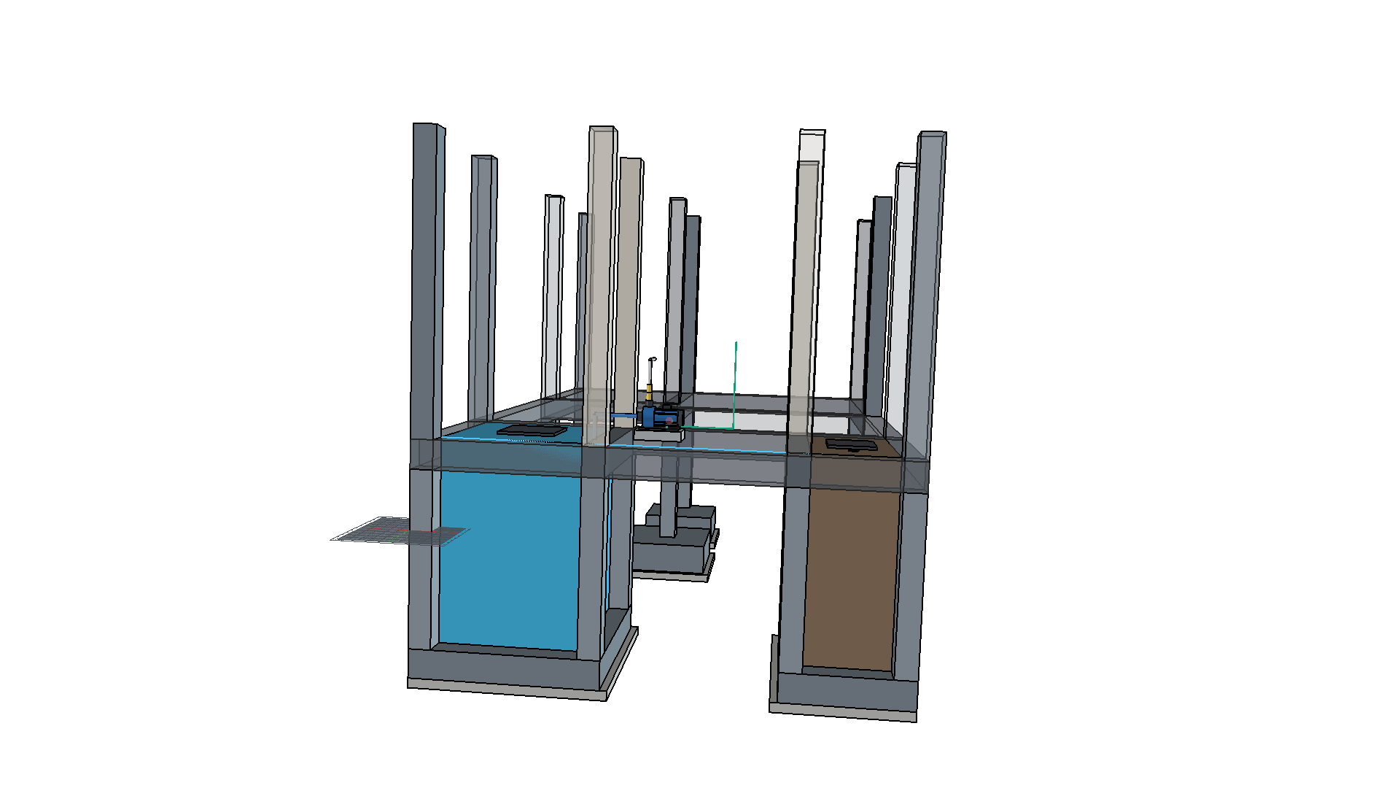
renders/substructure_zero_collision_front.png
