Pradeeparul2/house-plan/renders/substructure_zero_collision_iso.png

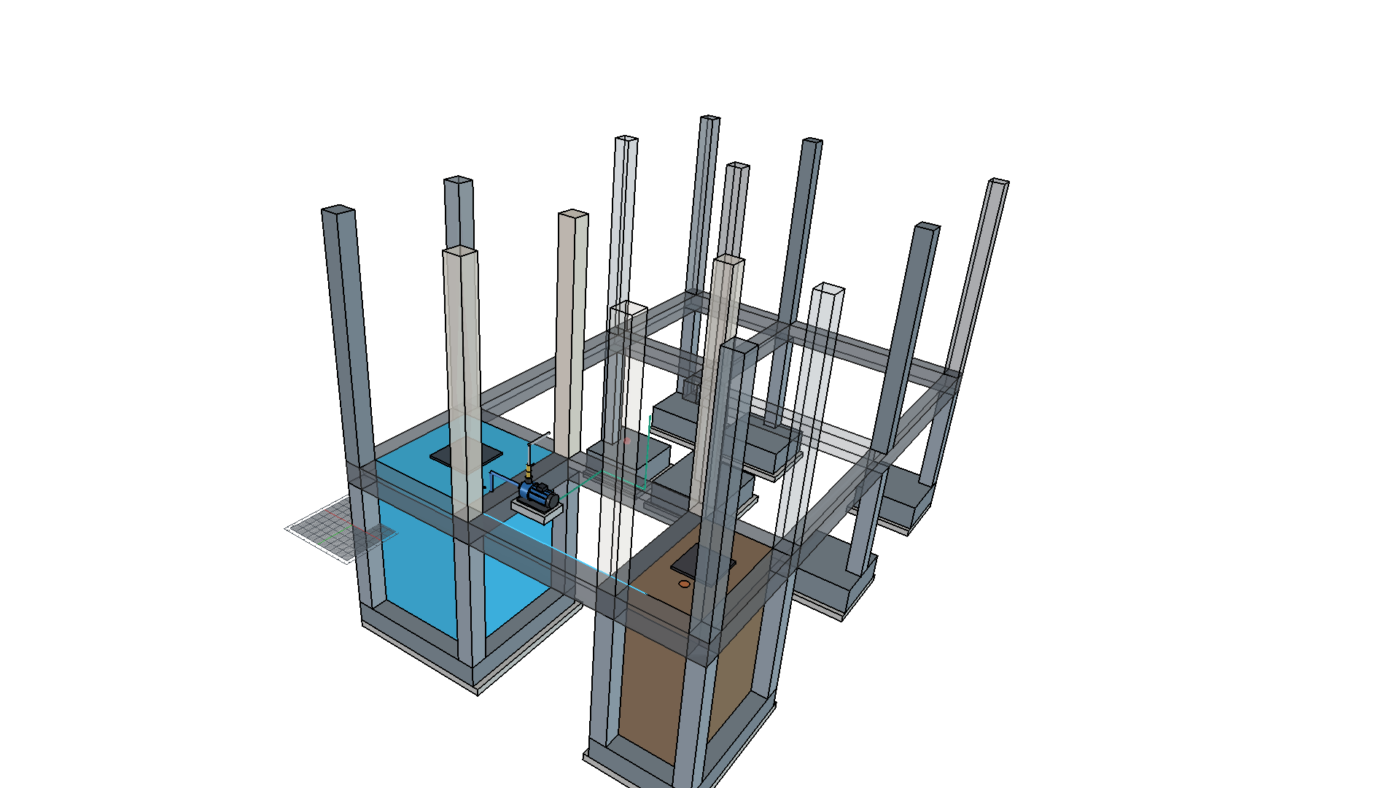
renders/substructure_zero_collision_iso.png
