Pradeeparul2/house-plan/renders/sump_raised_front_elev.png

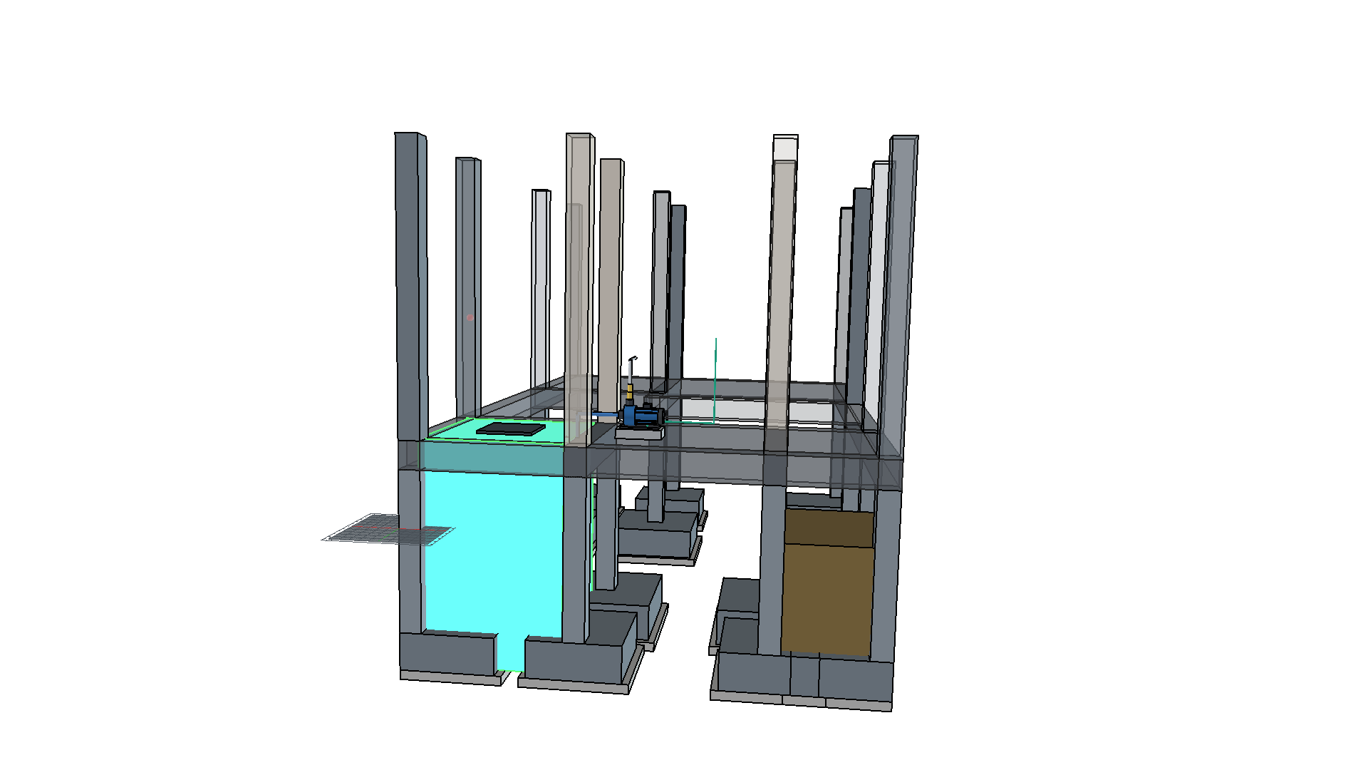
renders/sump_raised_front_elev.png
