Pradeeparul2/house-plan/renders/switchboard_beam_clearance_ff.png

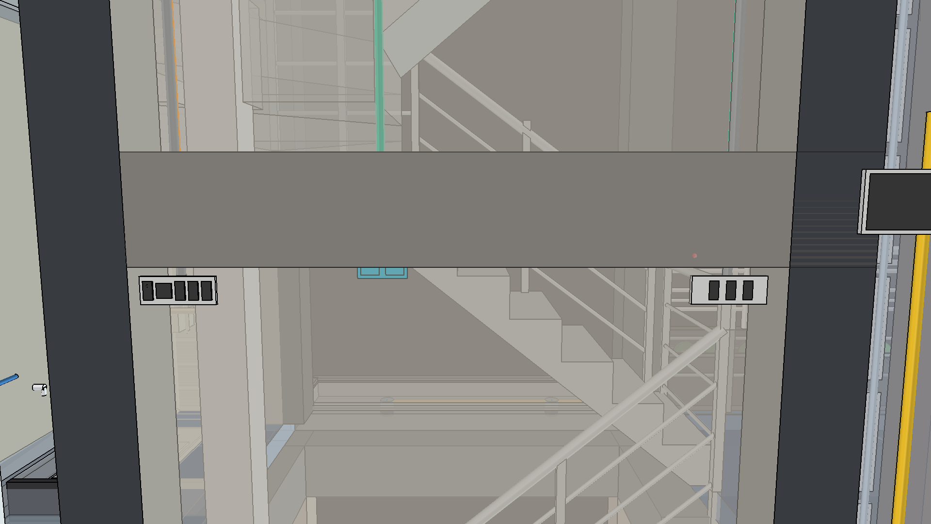
renders/switchboard_beam_clearance_ff.png
