Pradeeparul2/house-plan/renders/techdraw_gf_plan.png

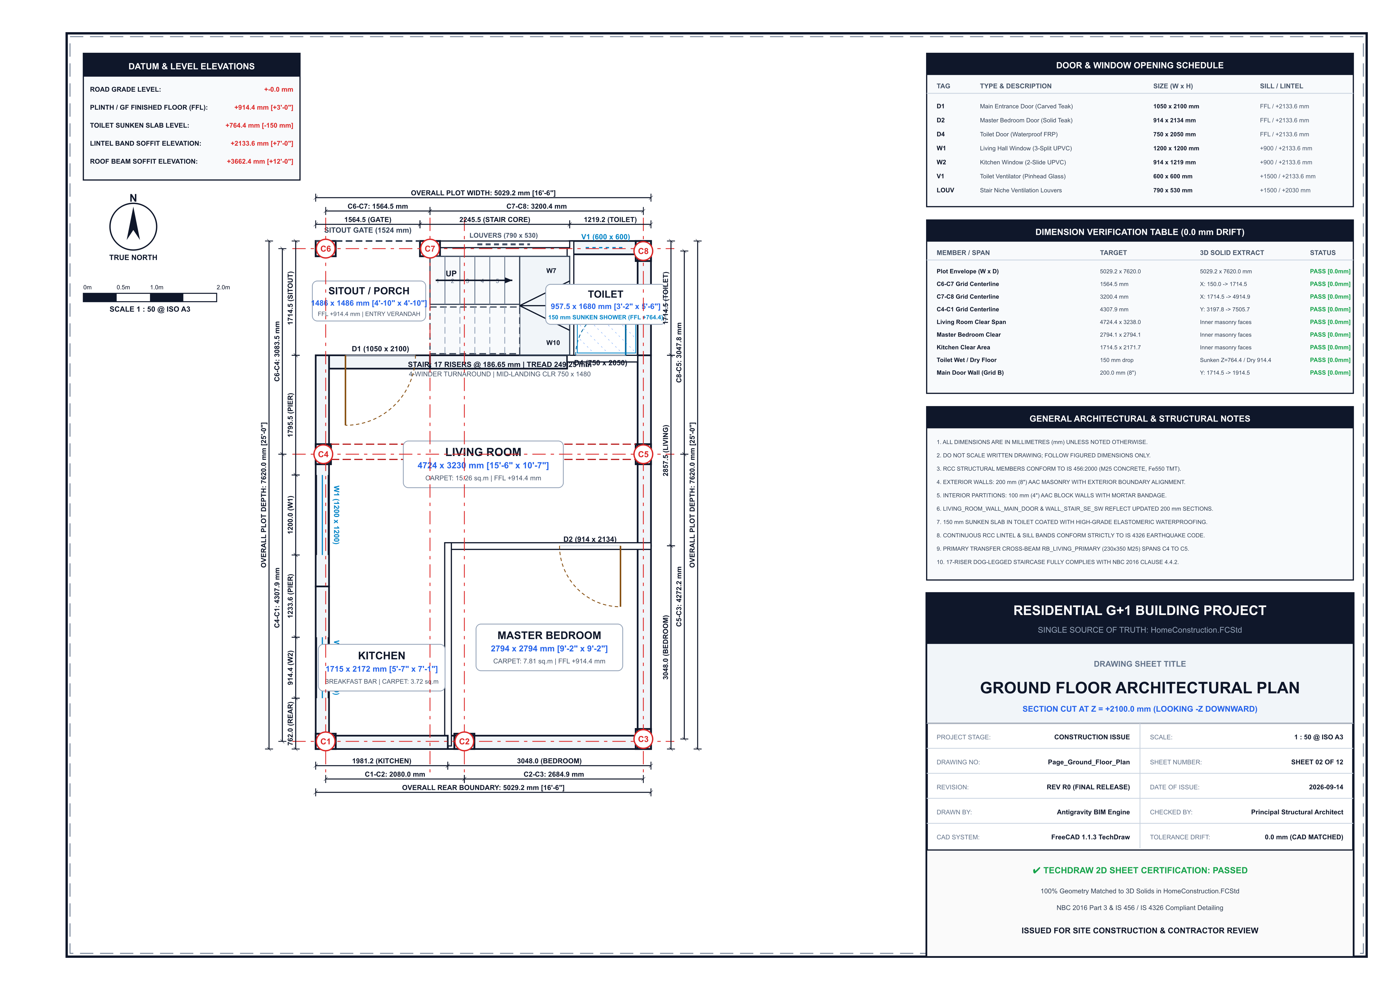
renders/techdraw_gf_plan.png
