Pradeeparul2/house-plan/renders/terrace_electrical_circuit_complete.png

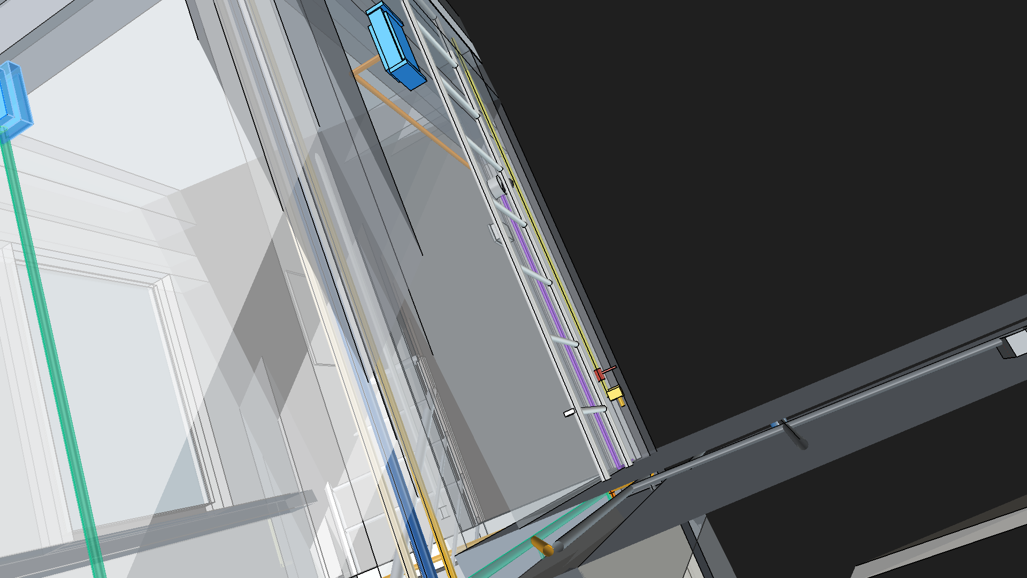
renders/terrace_electrical_circuit_complete.png
