Pradeeparul2/house-plan/renders/terrace_entrance_stair_conduit_fixed_view3.png

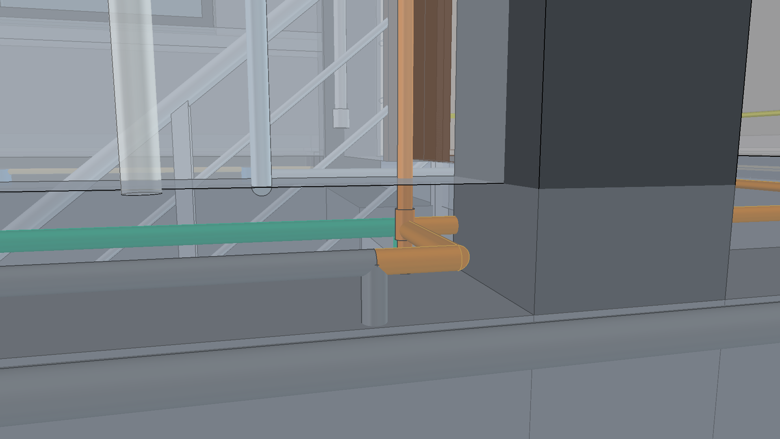
renders/terrace_entrance_stair_conduit_fixed_view3.png
