Pradeeparul2/house-plan/renders/terrace_lighting_isometric_overview.png

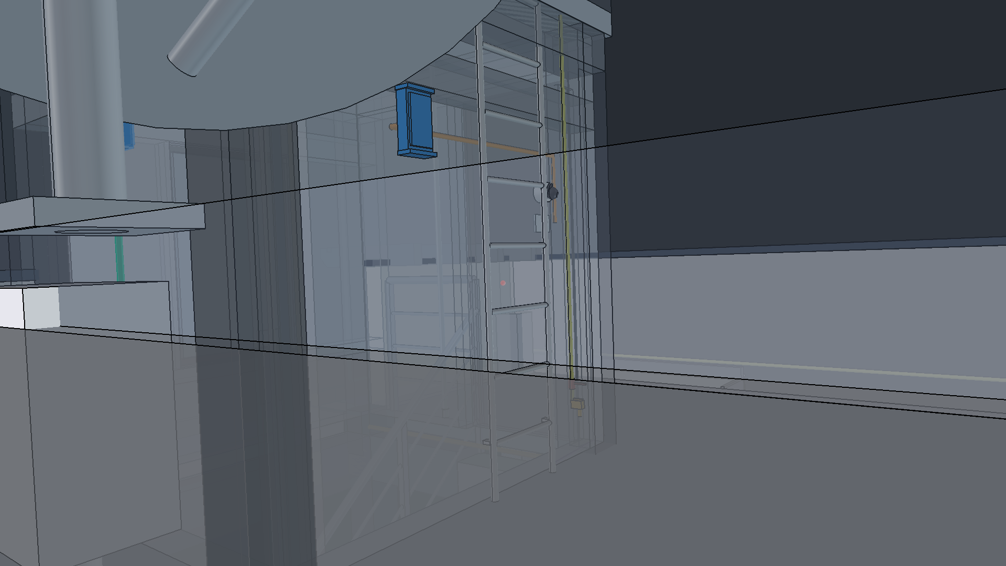
renders/terrace_lighting_isometric_overview.png
