Pradeeparul2/house-plan/renders/terrace_south_wall_light.png

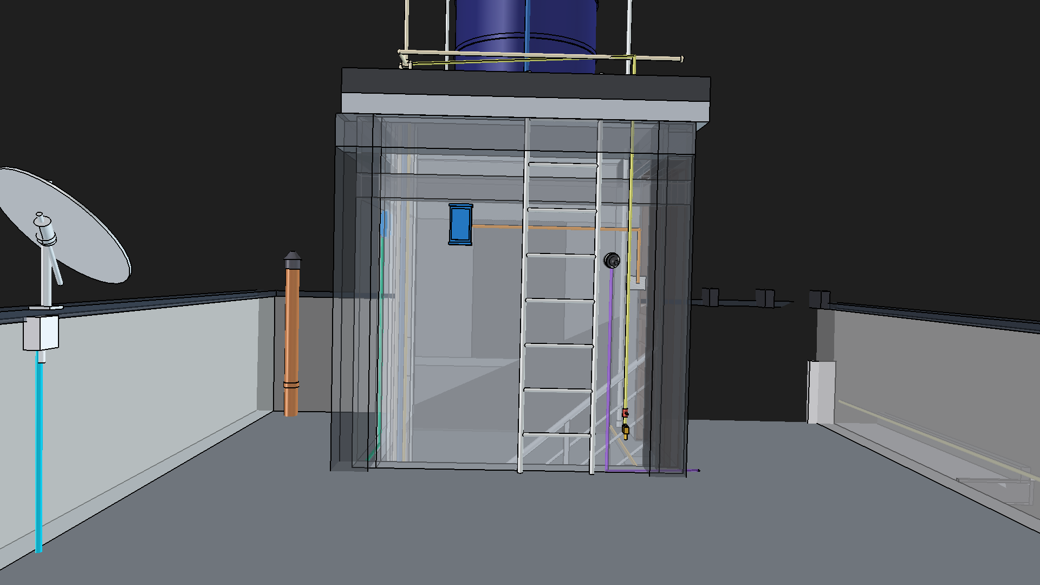
renders/terrace_south_wall_light.png
