Pradeeparul2/house-plan/renders/terrace_stair_entrance_cleared_view3.png

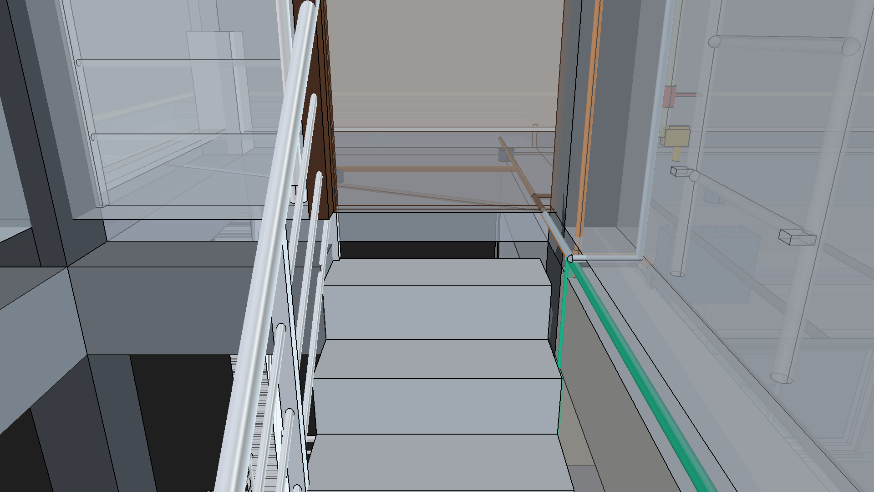
renders/terrace_stair_entrance_cleared_view3.png
