Pradeeparul2/house-plan/renders/terrace_switchboard_doorway_view.png

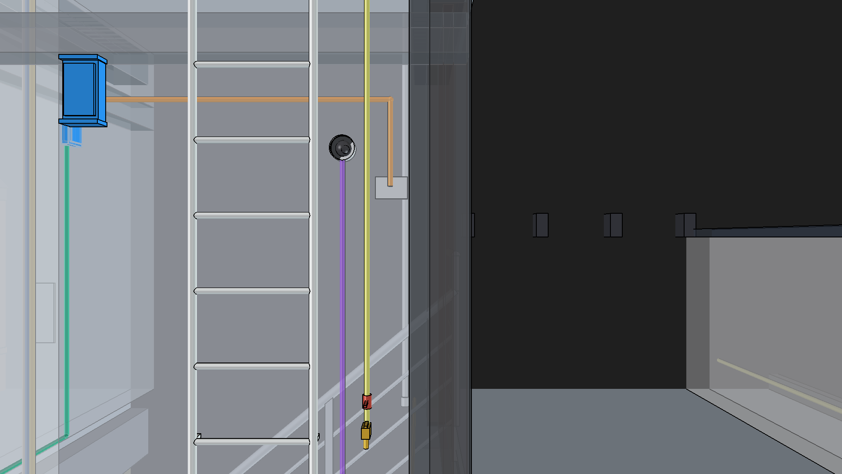
renders/terrace_switchboard_doorway_view.png
