Pradeeparul2/house-plan/renders/terrace_switchbox_power_supply_upright.png

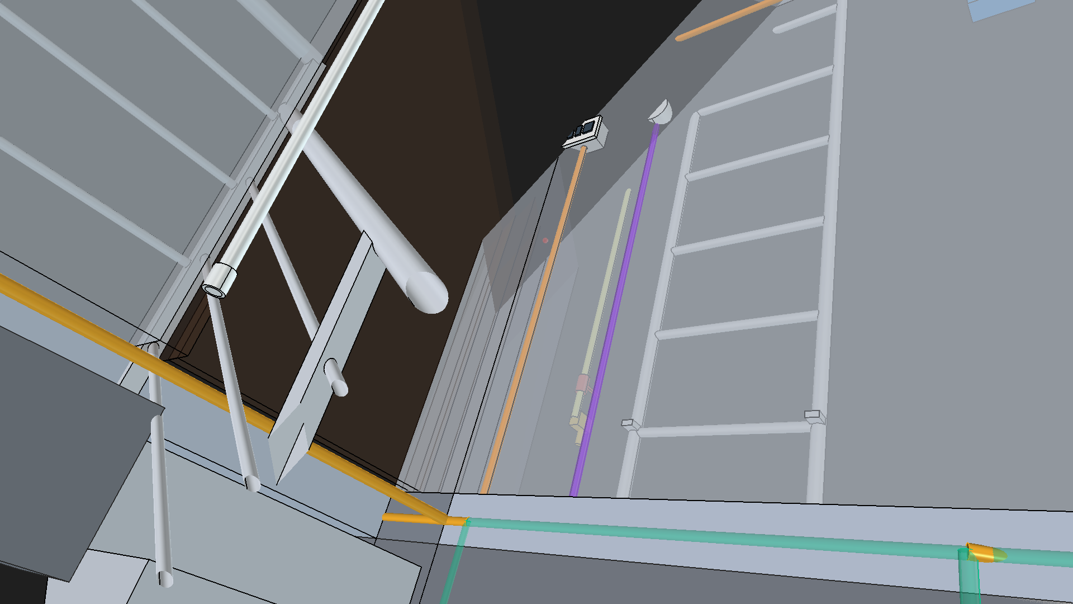
renders/terrace_switchbox_power_supply_upright.png
