Pradeeparul2/house-plan/renders/toilet_dual_stream_closeup.png

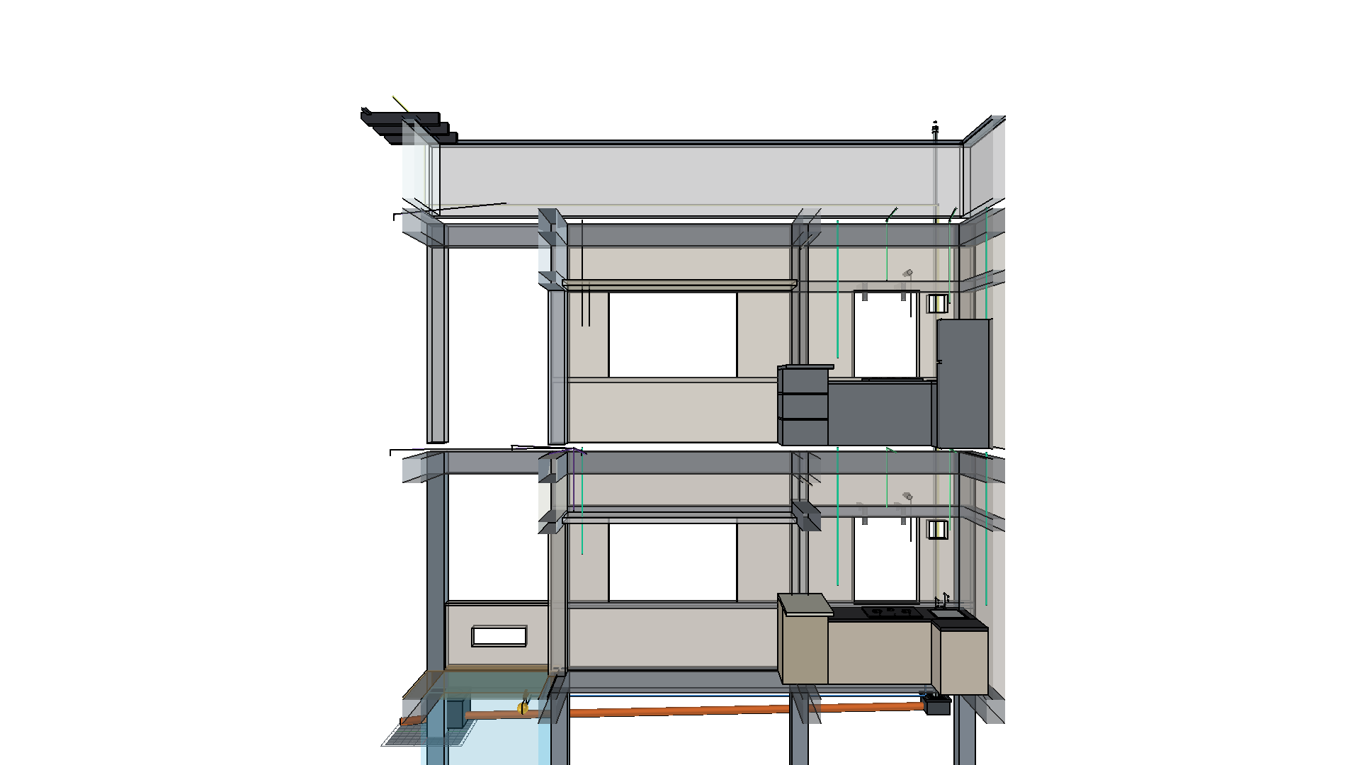
renders/toilet_dual_stream_closeup.png
