Pradeeparul2/house-plan/renders/toilet_dual_stream_closeup_detail.png

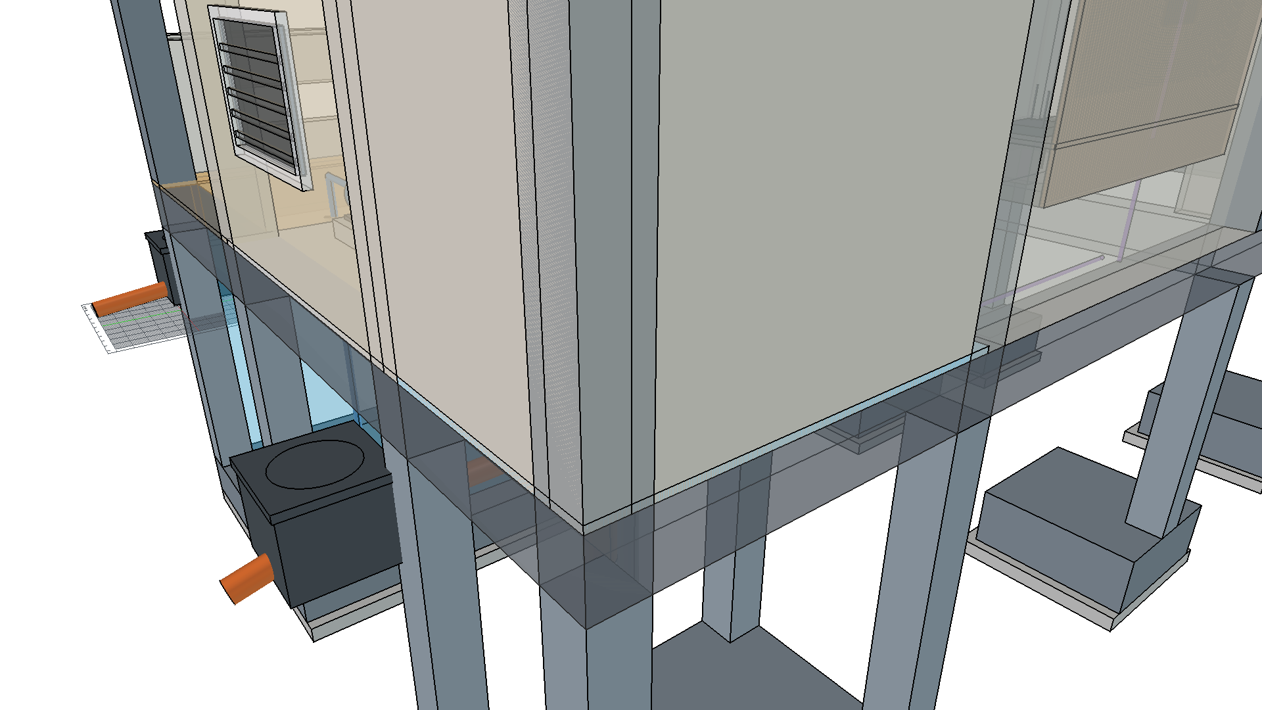
renders/toilet_dual_stream_closeup_detail.png
