Pradeeparul2/house-plan/renders/toilet_gt2_laundry_standpipe_closeup.png

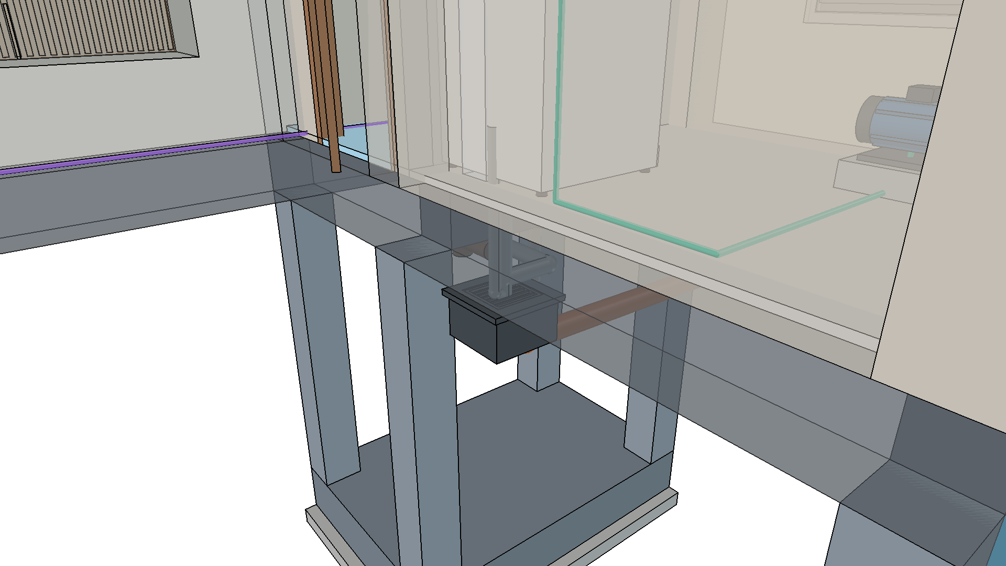
renders/toilet_gt2_laundry_standpipe_closeup.png
