Pradeeparul2/house-plan/renders/toilet_septic_south_elevation.png

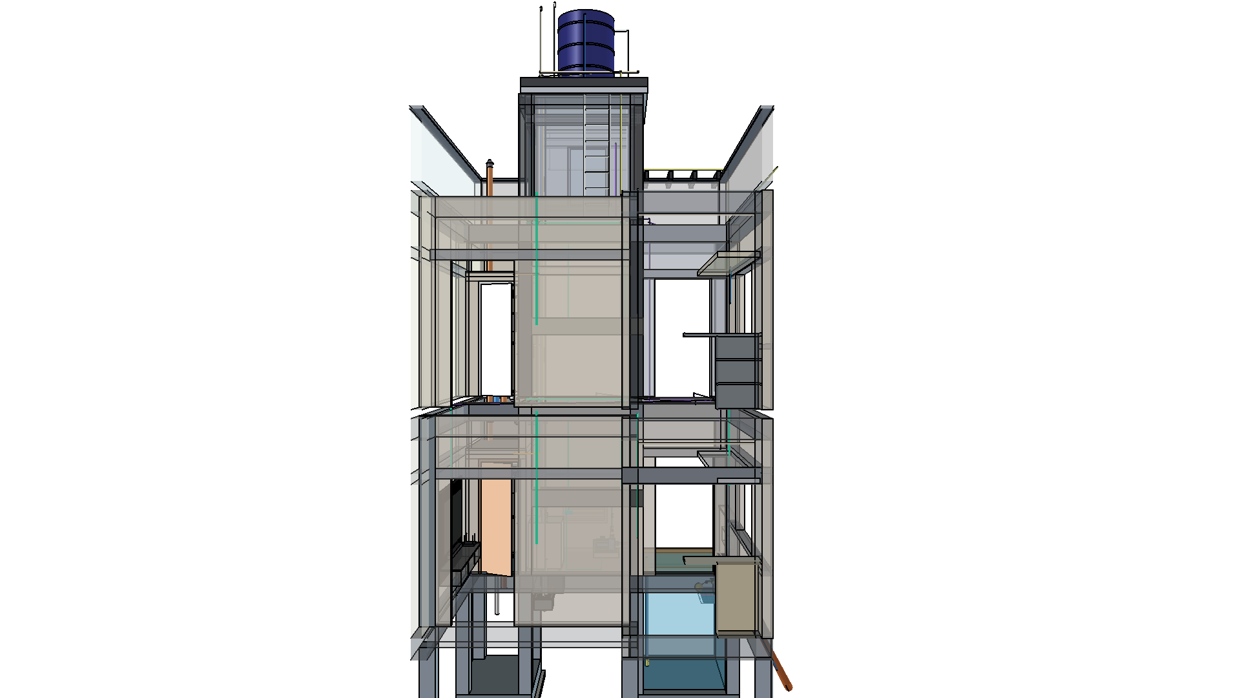
renders/toilet_septic_south_elevation.png
