Pradeeparul2/house-plan/renders/toilet_sunken_wet_area_isometric.png

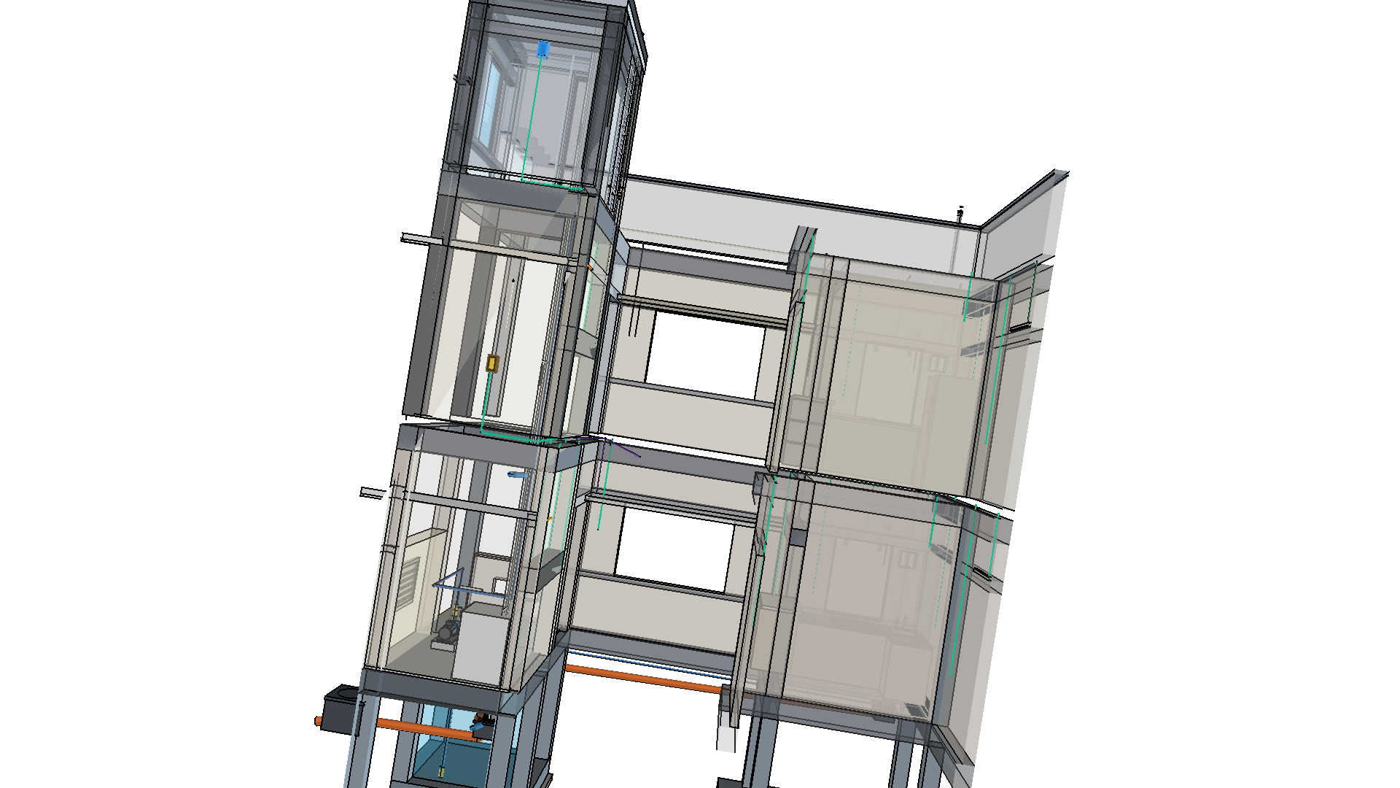
renders/toilet_sunken_wet_area_isometric.png
