Pradeeparul2/house-plan/renders/toilet_wall_translucent_closeup.png

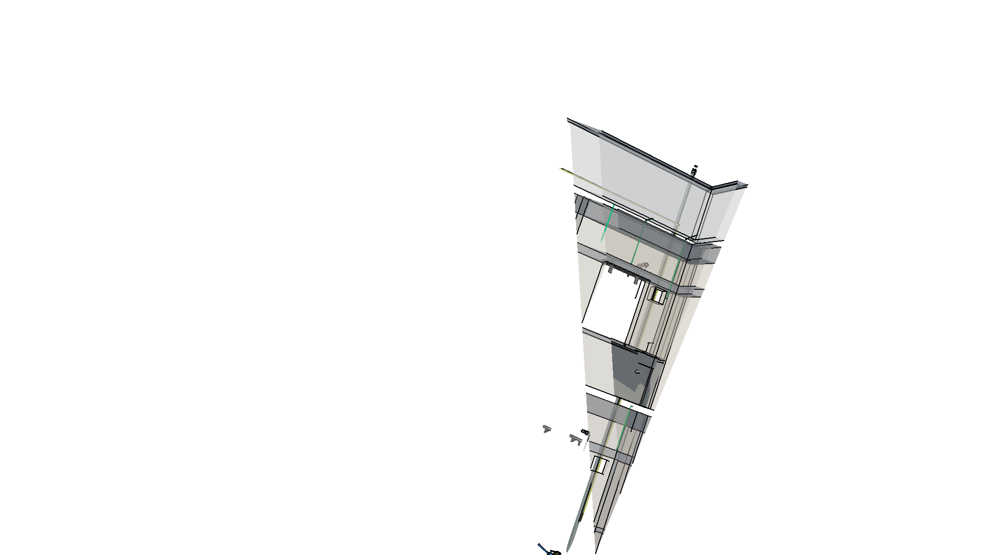
renders/toilet_wall_translucent_closeup.png
