Pradeeparul2/house-plan/renders/toilet_west_profile.png

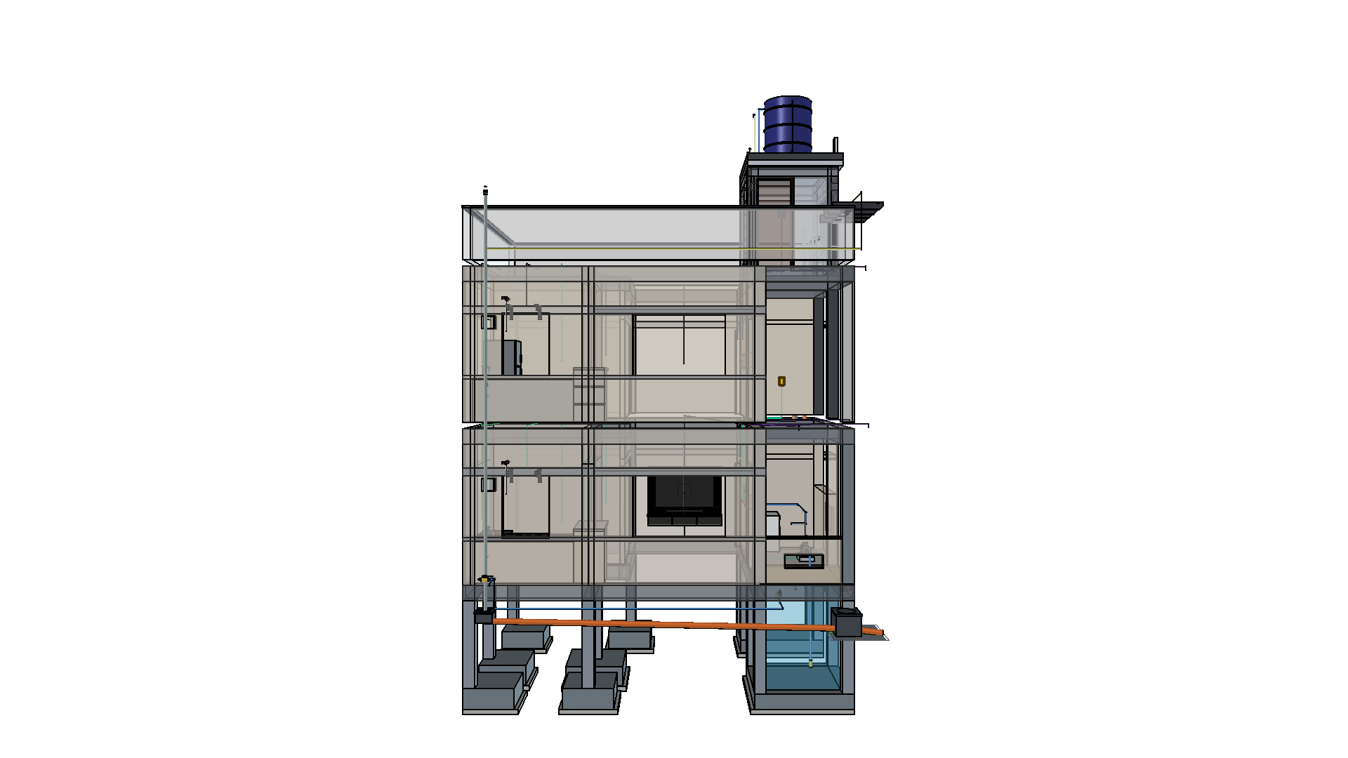
renders/toilet_west_profile.png
