Pradeeparul2/house-plan/renders/two_storey_electrical_pipelines.png

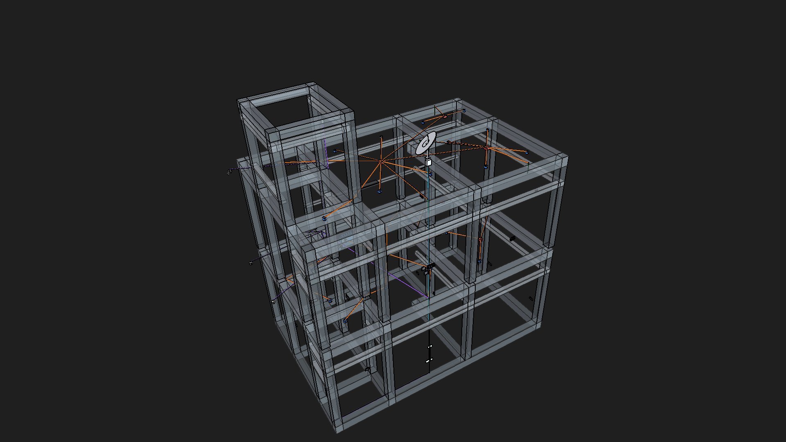
renders/two_storey_electrical_pipelines.png
