Pradeeparul2/house-plan/renders/two_storey_sb_util_gf_only_iso.png

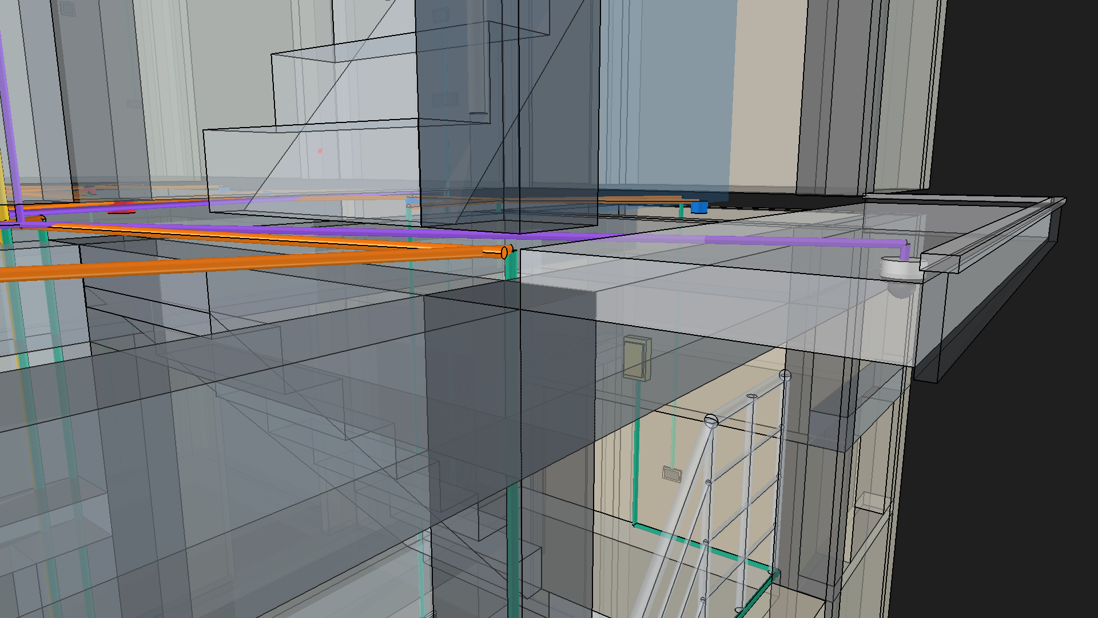
renders/two_storey_sb_util_gf_only_iso.png
