Pradeeparul2/house-plan/renders/two_storey_staircase_south_wall_iso.png

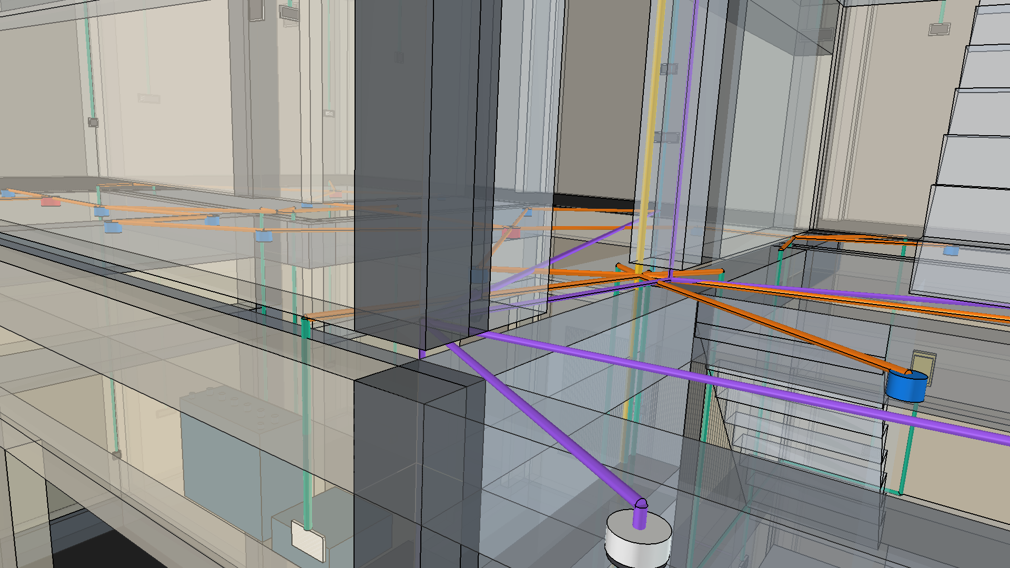
renders/two_storey_staircase_south_wall_iso.png
