Pradeeparul2/house-plan/renders/utility_stair_overview.png

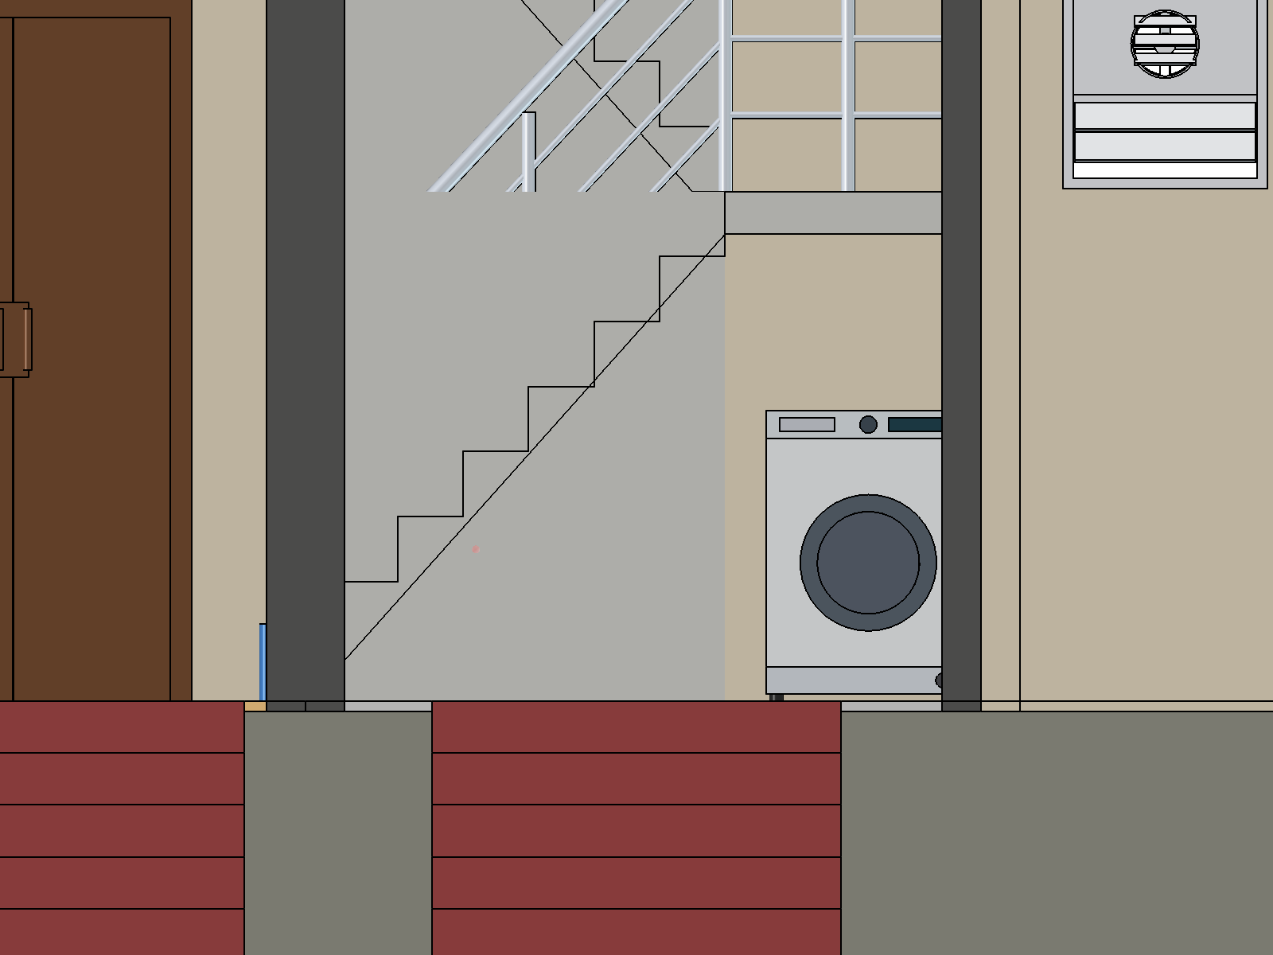
renders/utility_stair_overview.png
