Pradeeparul2/house-plan/renders/west_elevation_bedroom_windows.png

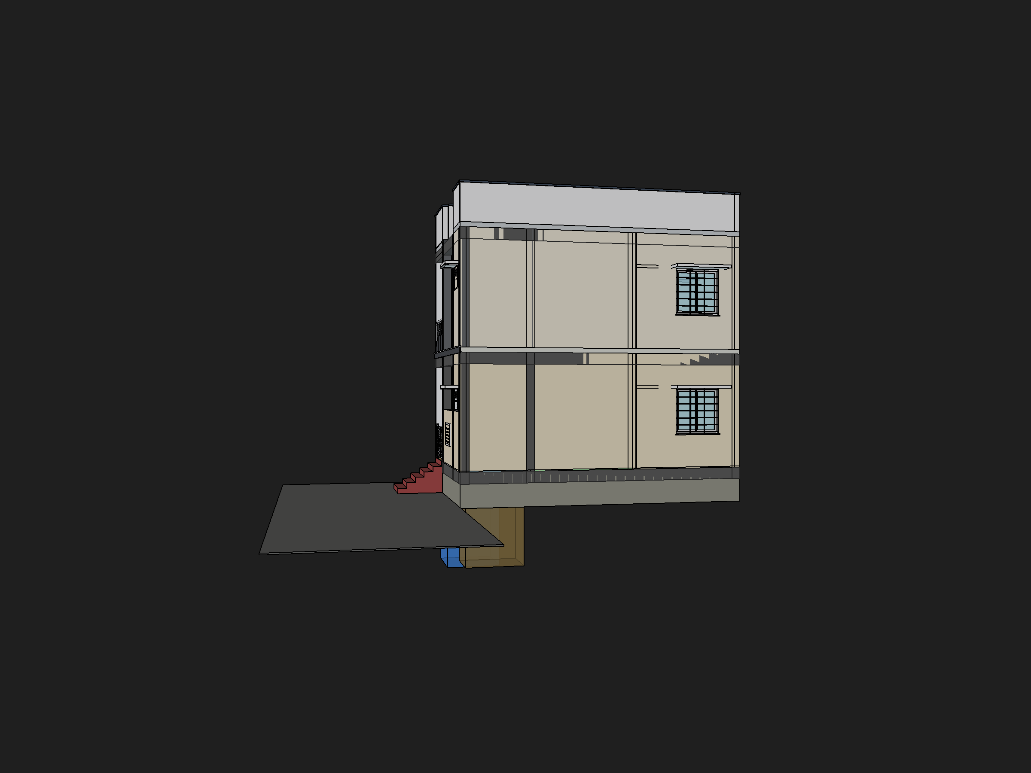
renders/west_elevation_bedroom_windows.png
