Pradeeparul2/house-plan/renders/west_elevation_walls_100_visible.png

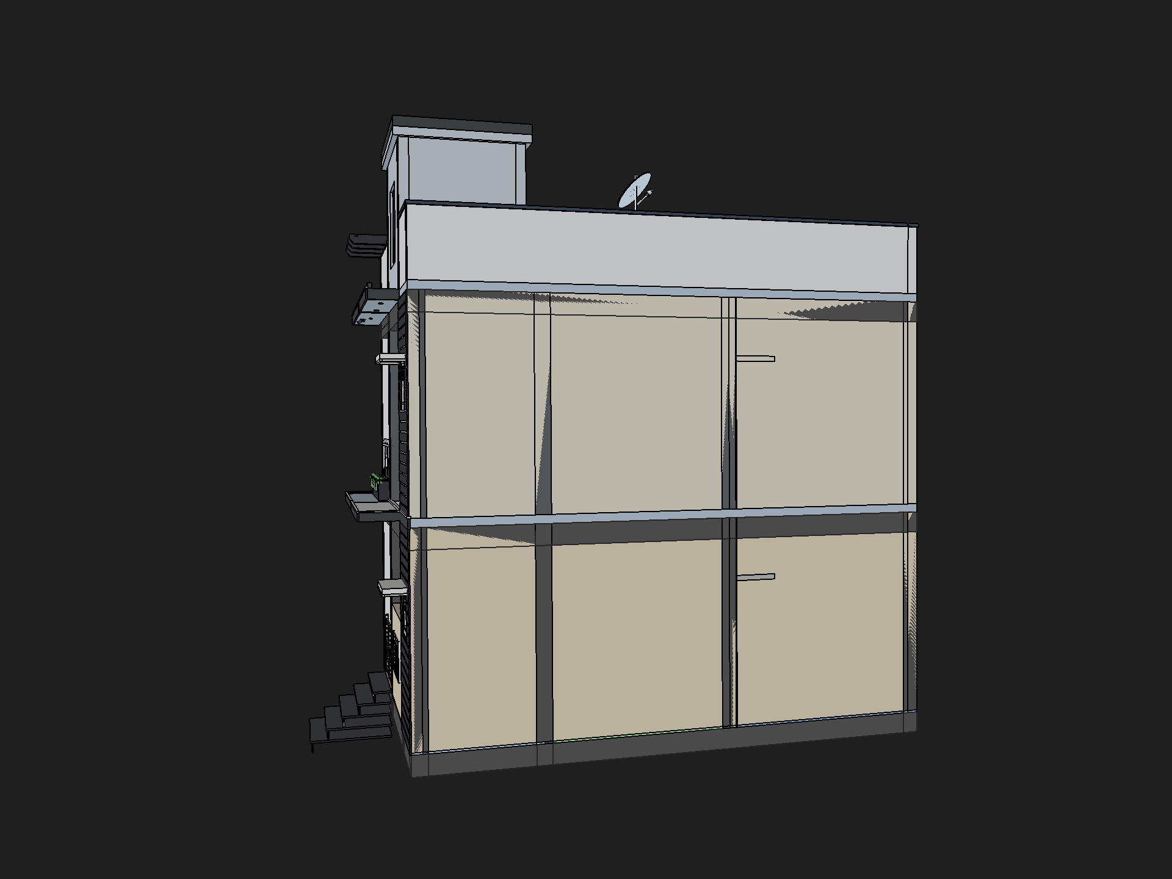
renders/west_elevation_walls_100_visible.png
