Pradeeparul2/house-plan/renders/west_side_elevation.png

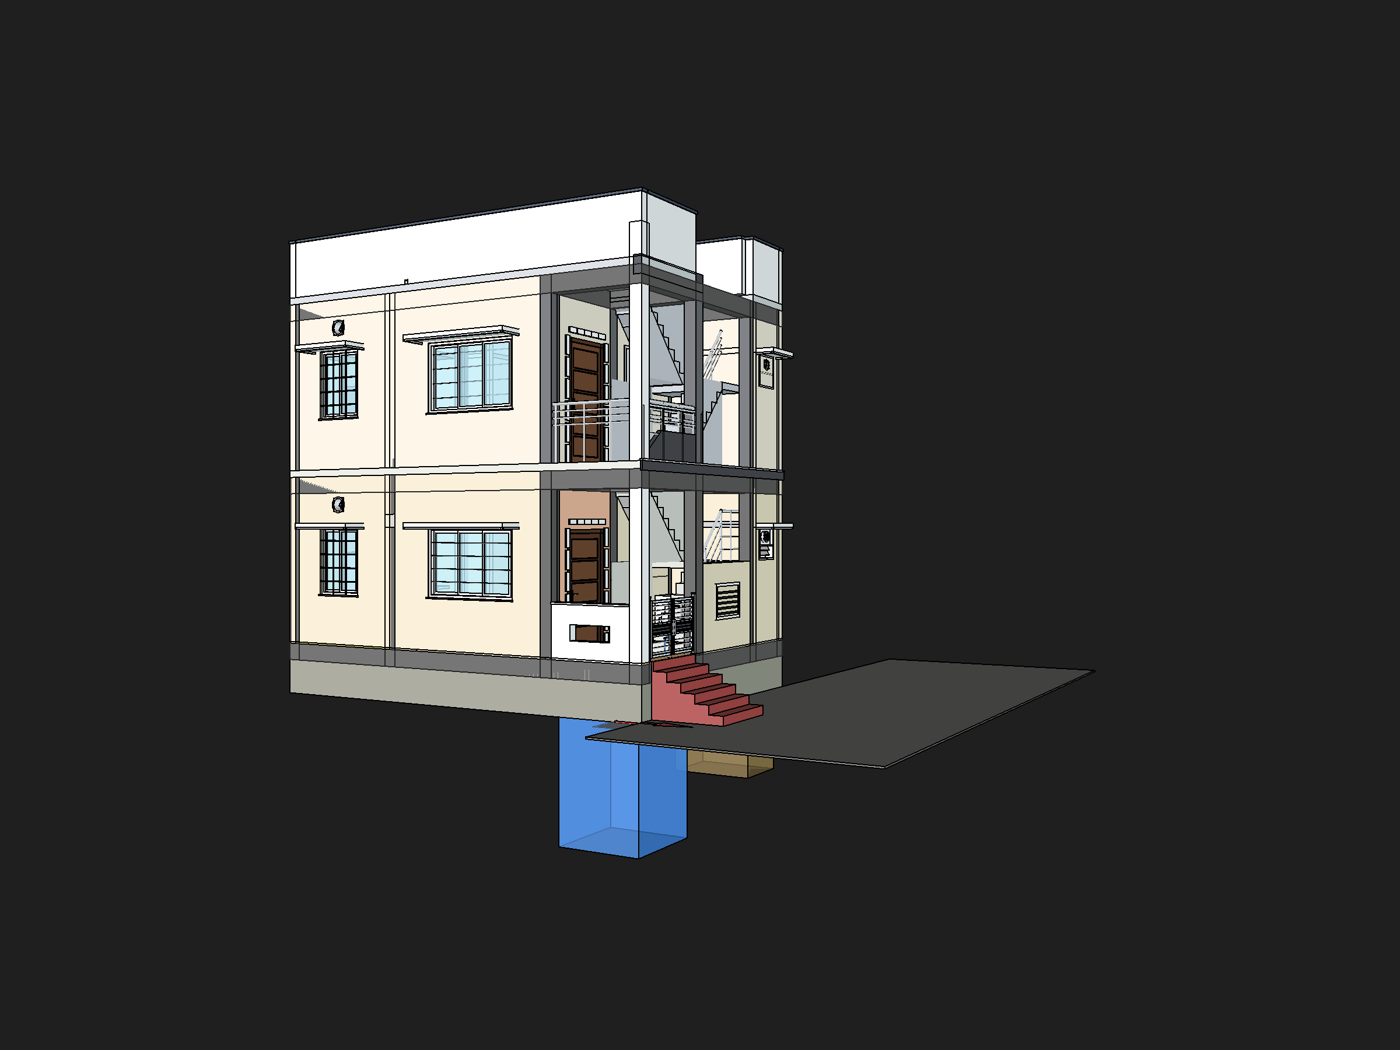
renders/west_side_elevation.png
