Pradeeparul2/house-plan/renders/winder_stairs_zoomed_detail.png

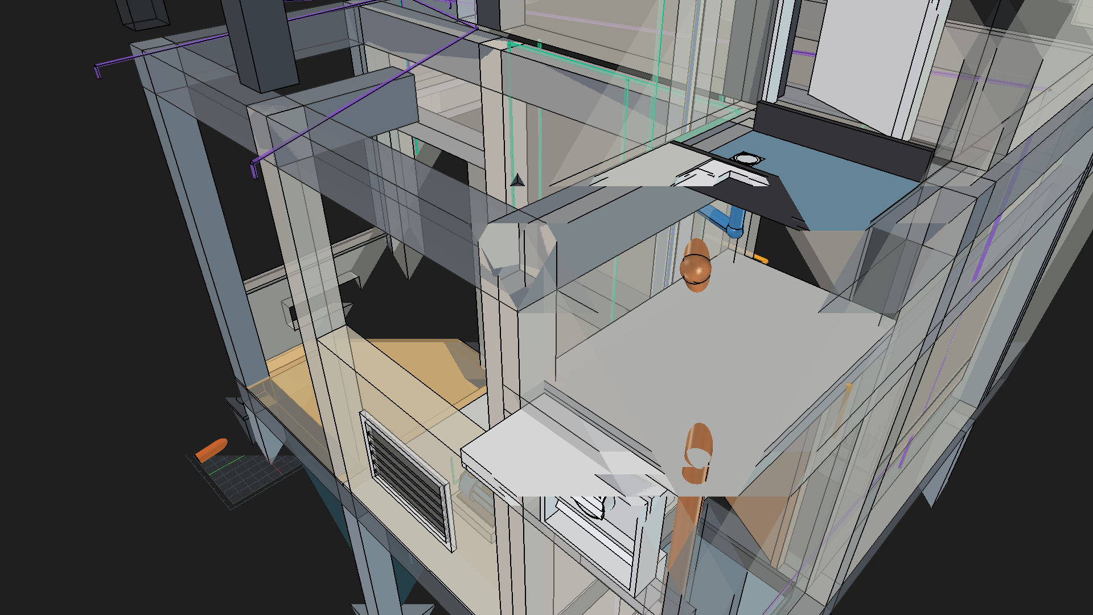
renders/winder_stairs_zoomed_detail.png
