Pradeeparul2/house-plan/renders/wm_perspective_detail.png

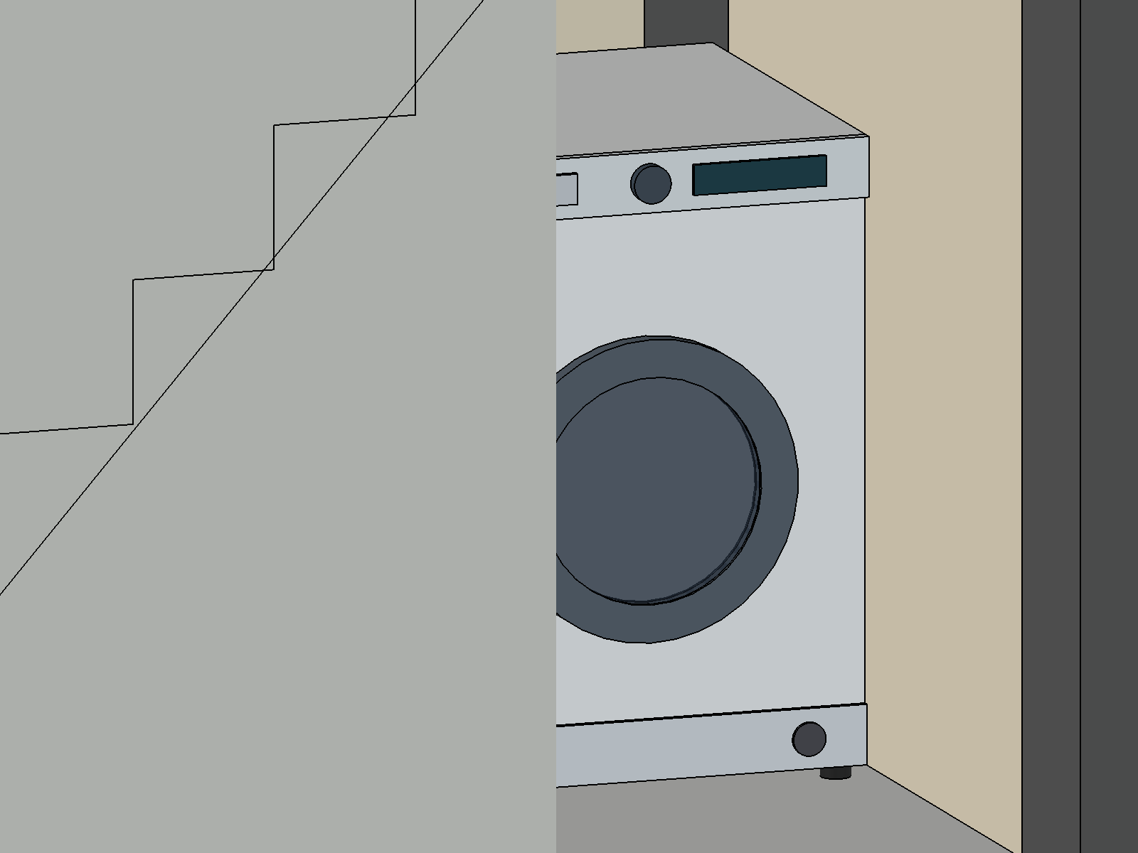
renders/wm_perspective_detail.png
