Pradeeparul2/house-plan/renders/staircase_both_components_labeled_view.png

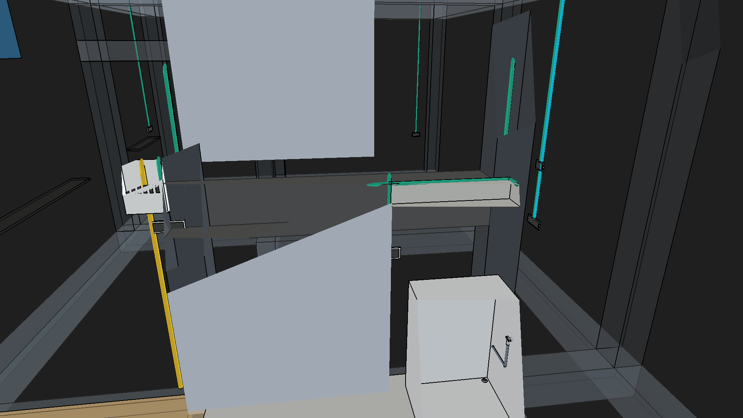
renders/staircase_both_components_labeled_view.png
