Pradeeparul2/house-plan/renders/building_isometric_full_drainage_network.png

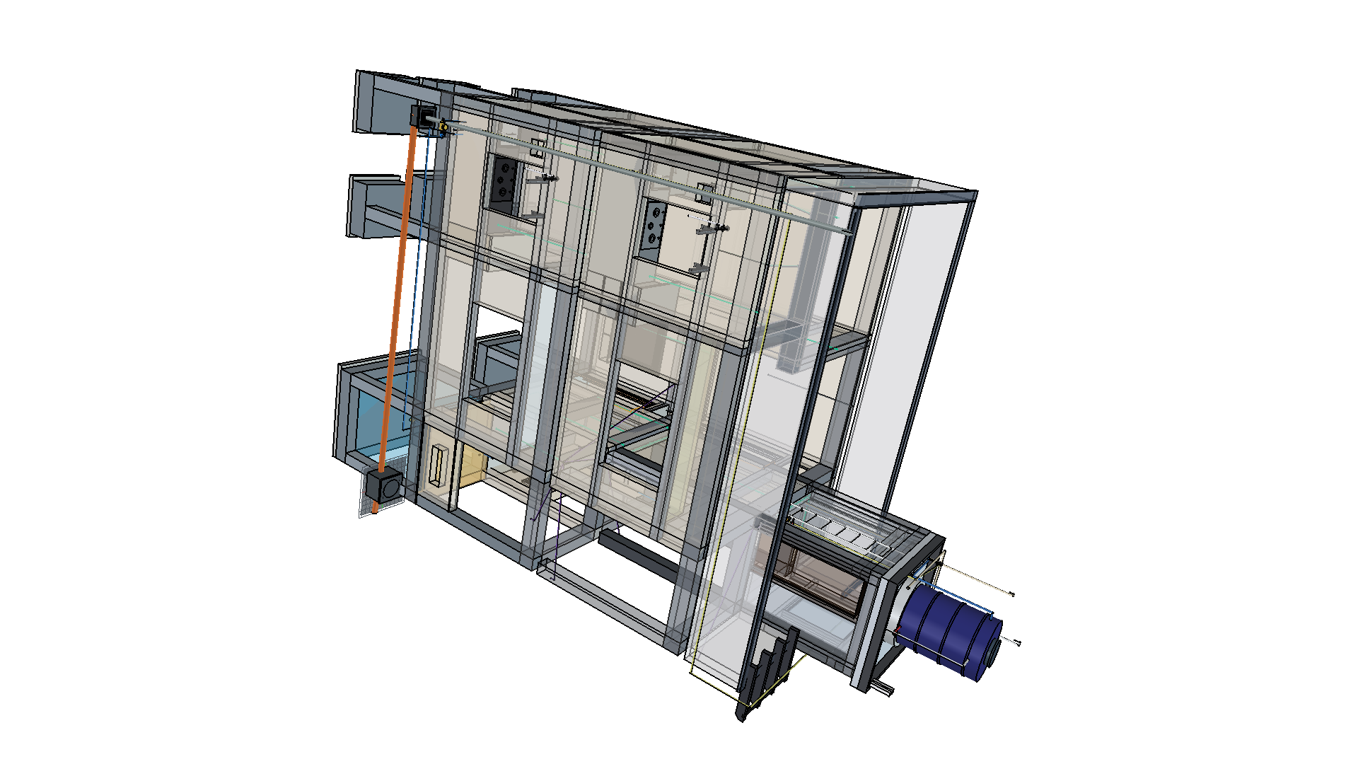
renders/building_isometric_full_drainage_network.png
