Pradeeparul2/house-plan/renders/building_walls_50_opacity_east.png

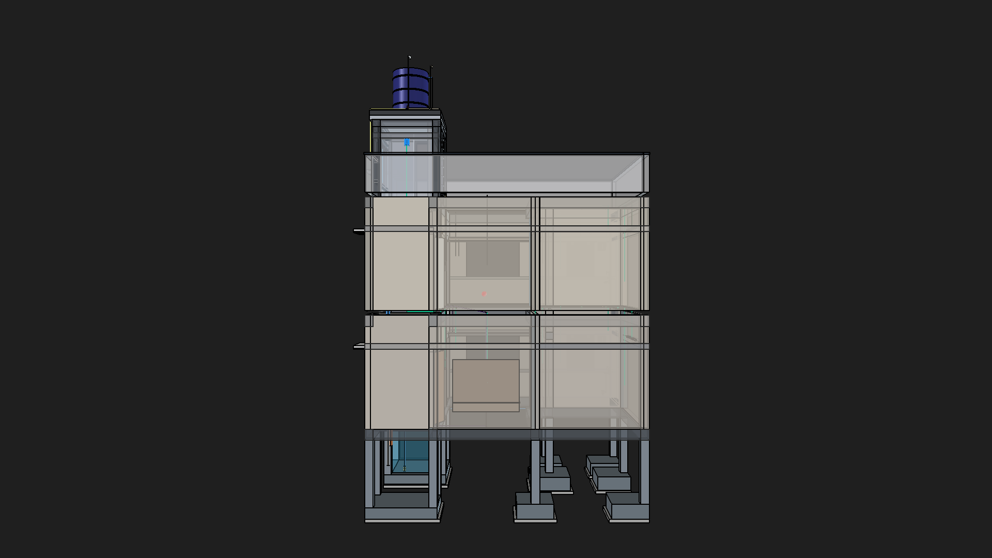
renders/building_walls_50_opacity_east.png
