Pradeeparul2/house-plan/renders/cctv_wiring_schematic_3d.png

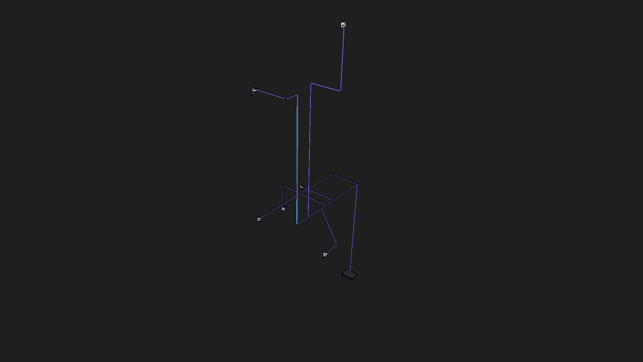
renders/cctv_wiring_schematic_3d.png
