Pradeeparul2/house-plan/renders/full_building_solid_east.png

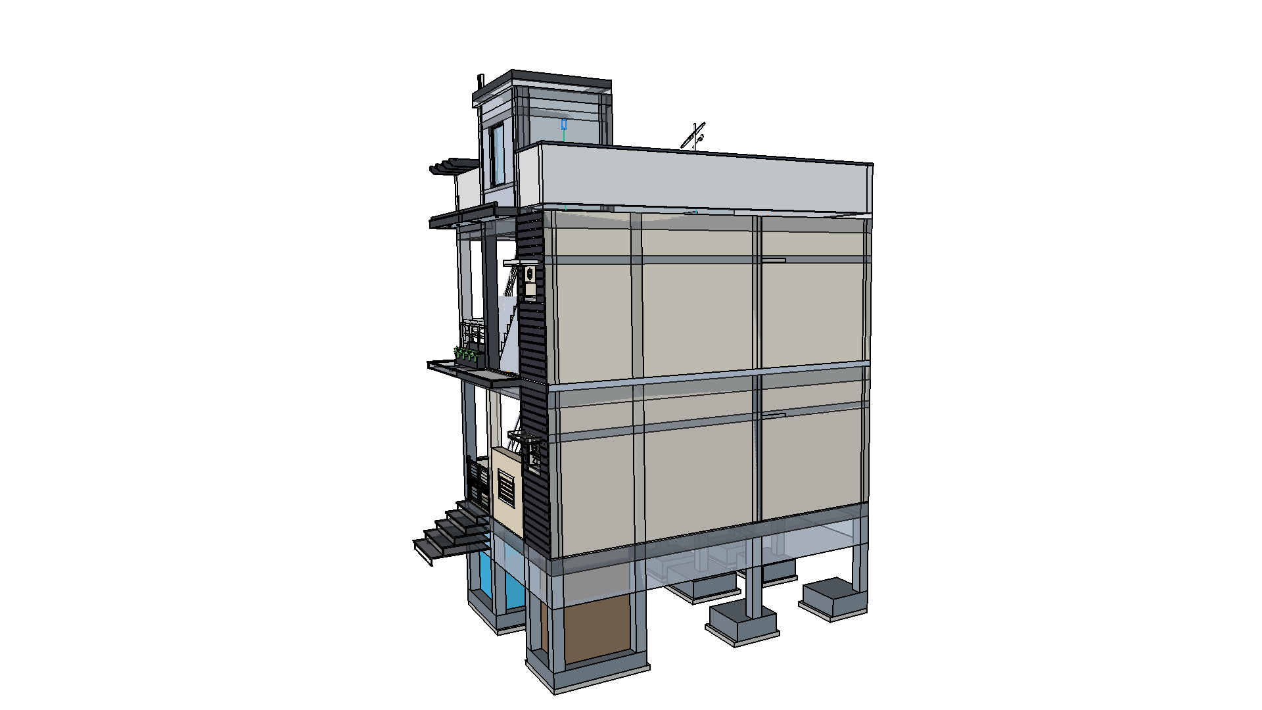
renders/full_building_solid_east.png
