Pradeeparul2/house-plan/renders/full_building_solid_east_true.png

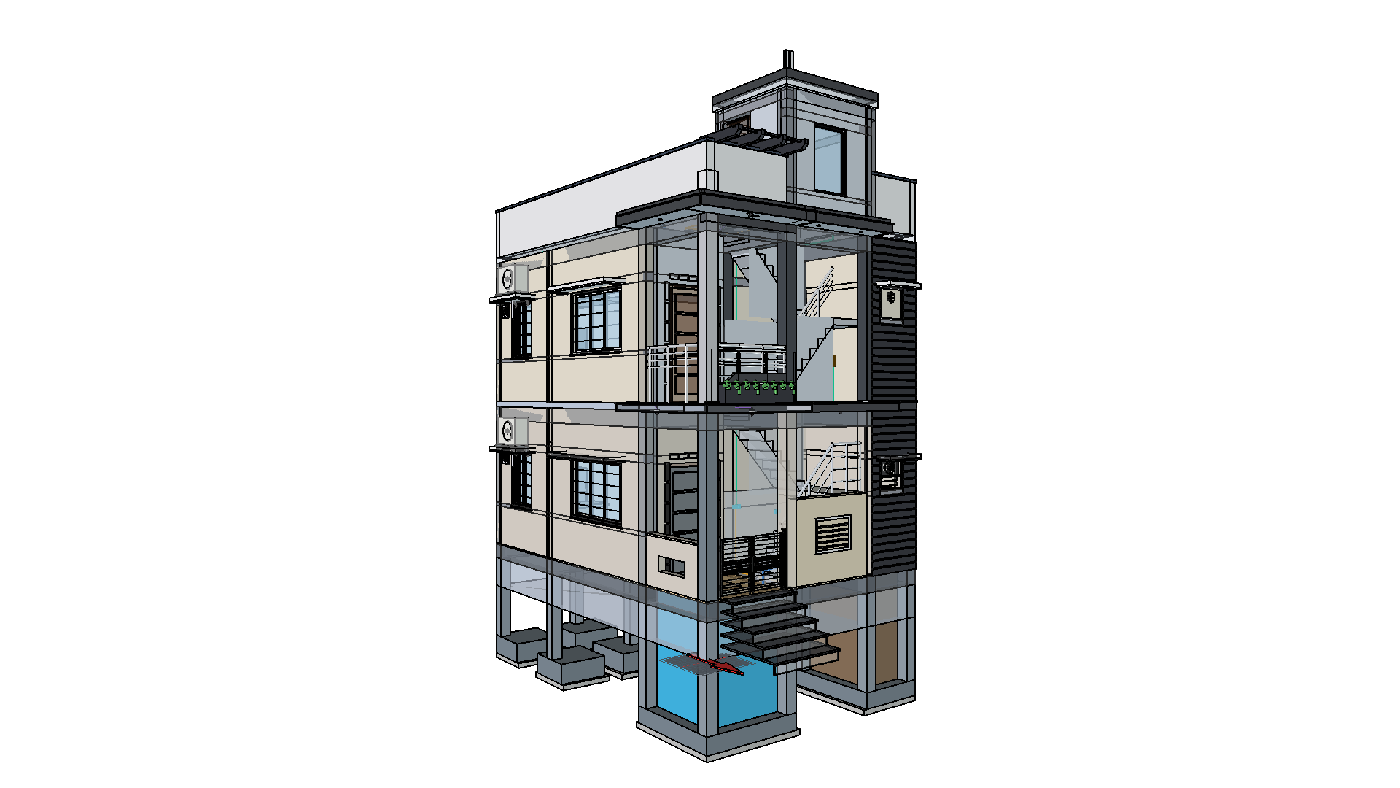
renders/full_building_solid_east_true.png
