Pradeeparul2/house-plan/renders/full_building_solid_front.png

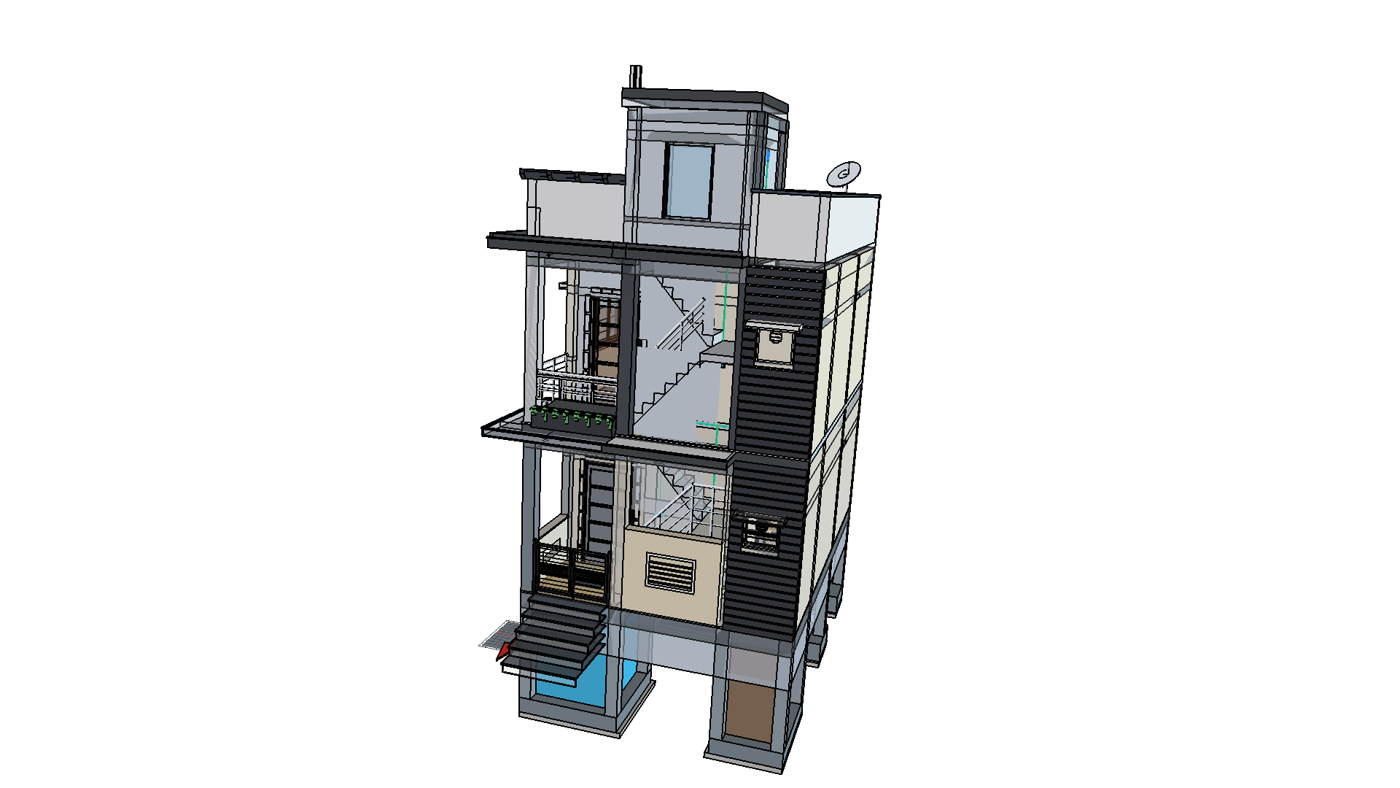
renders/full_building_solid_front.png
