Pradeeparul2/house-plan/renders/living_room_wiring_pipelines_iso.png

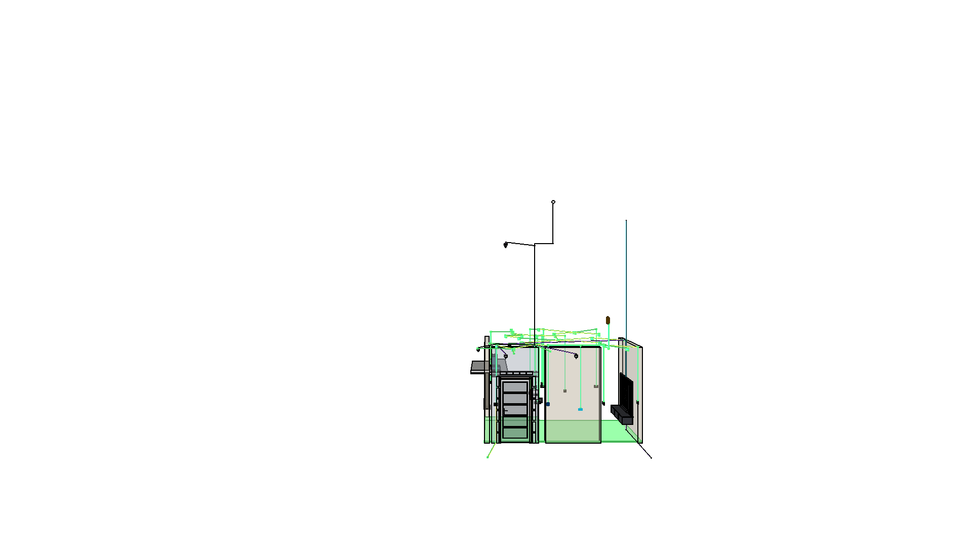
renders/living_room_wiring_pipelines_iso.png
