Pradeeparul2/house-plan/renders/winder_stairs_steps_detail.png

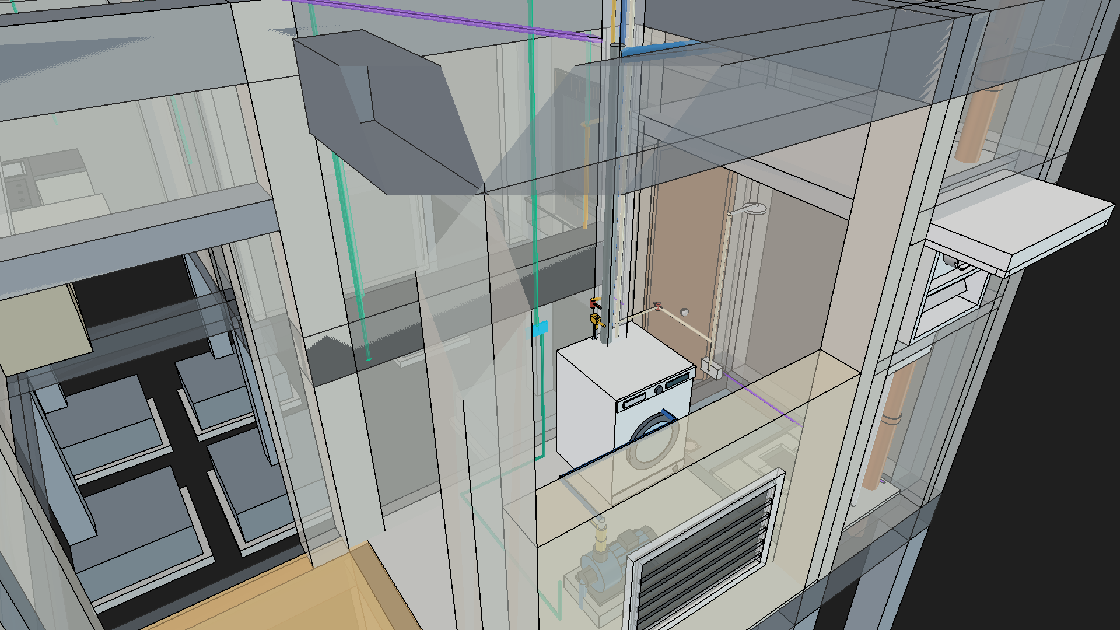
renders/winder_stairs_steps_detail.png
