Pradeeparul2/house-plan/renders/breakfast_counter_spotlight_pipeline_verified.png

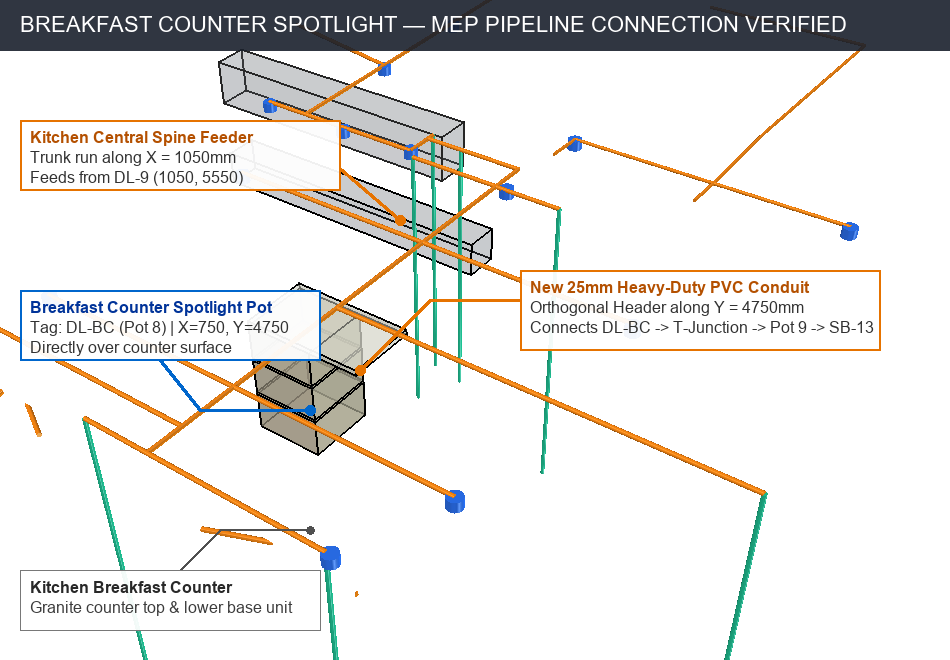
renders/breakfast_counter_spotlight_pipeline_verified.png
