Pradeeparul2/house-plan/renders/test_ff_light_front.png

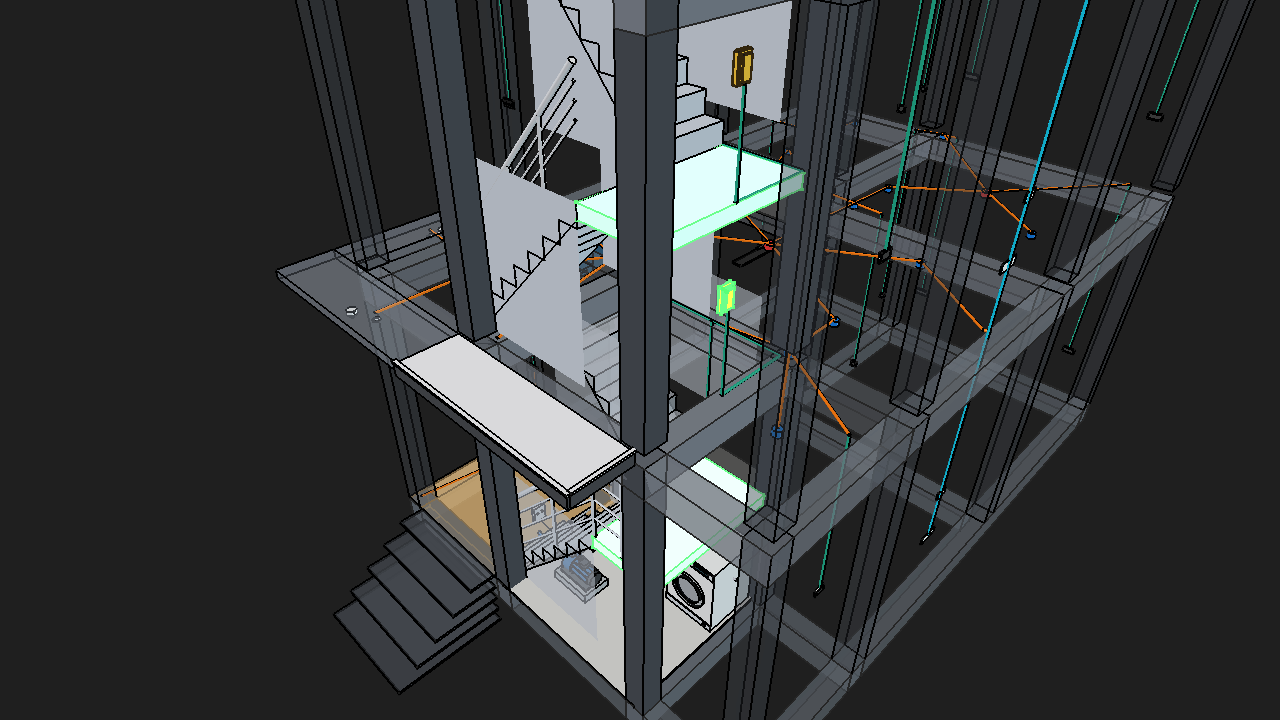
renders/test_ff_light_front.png
