Pradeeparul2/house-plan/renders/test_fit_selection_proper.png

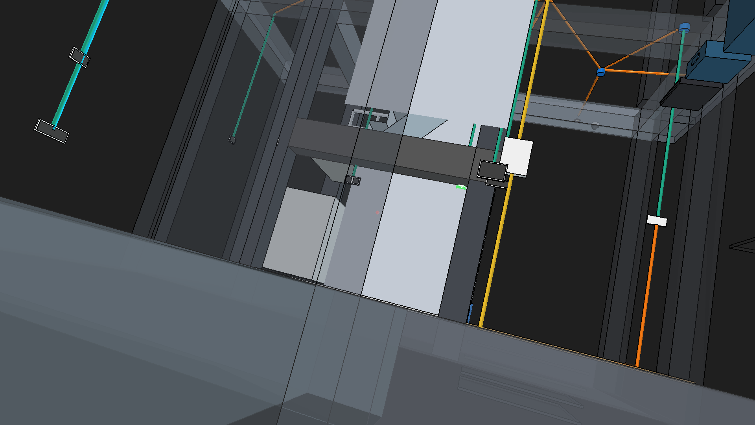
renders/test_fit_selection_proper.png
