Pradeeparul2/house-plan/renders/test_kitchen_counter.png

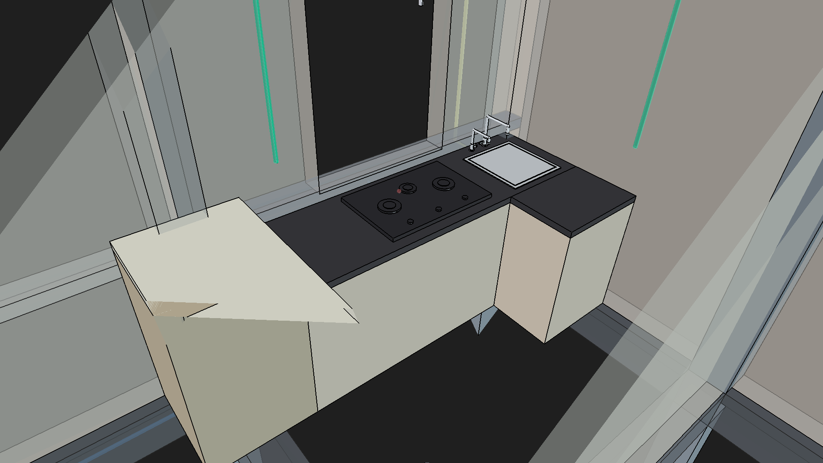
renders/test_kitchen_counter.png
