Pradeeparul2/house-plan/renders/test_view_left.png

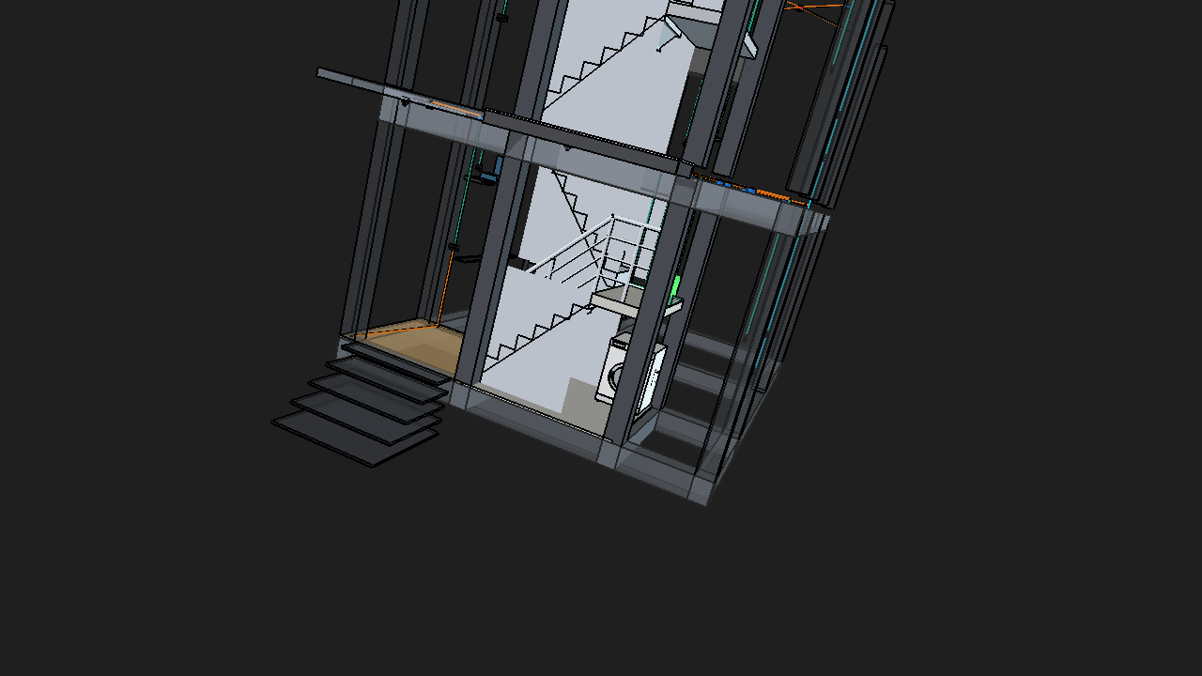
renders/test_view_left.png
