Pradeeparul2/house-plan/renders/test_walls_100_visible.png

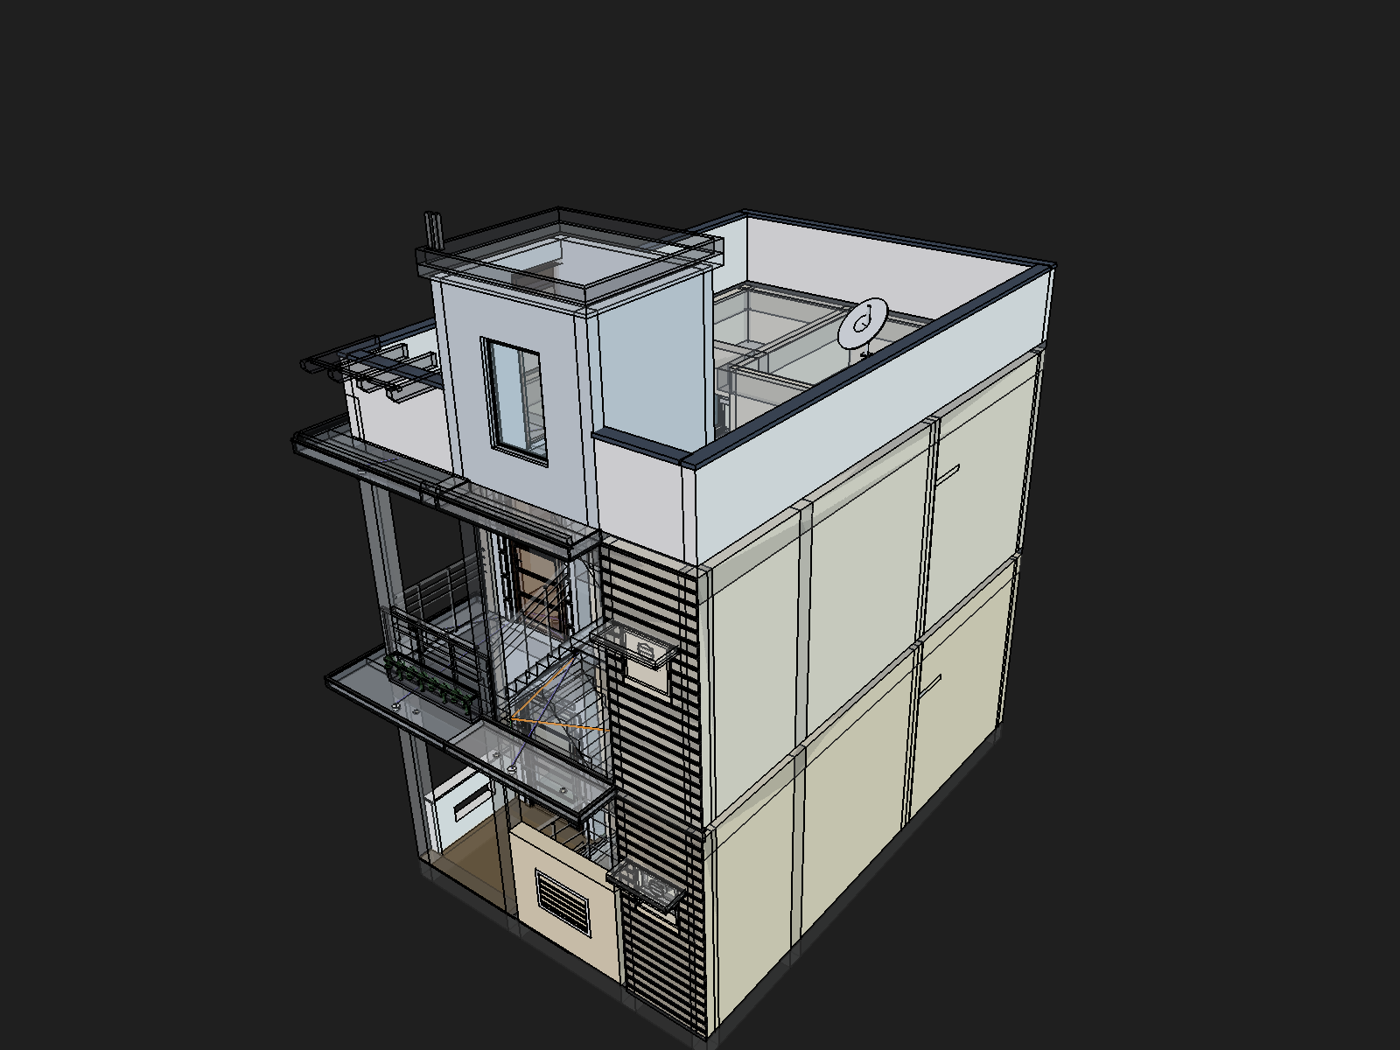
renders/test_walls_100_visible.png
