Pradeeparul2/house-plan/renders/test_zoom_iso.png

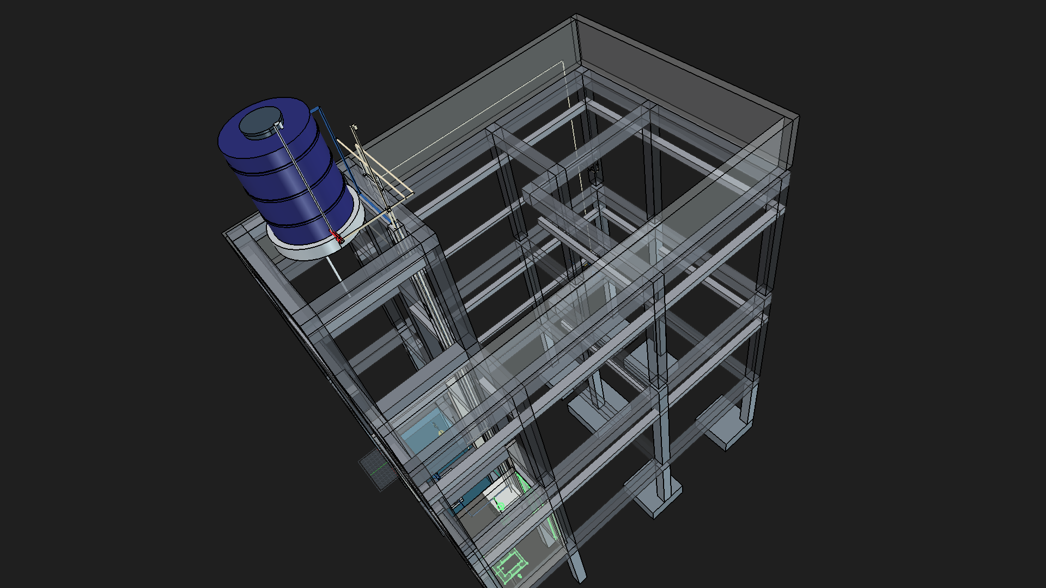
renders/test_zoom_iso.png
