Pradeeparul2/house-plan/renders/Page_Ground_Floor_Plan.pdf

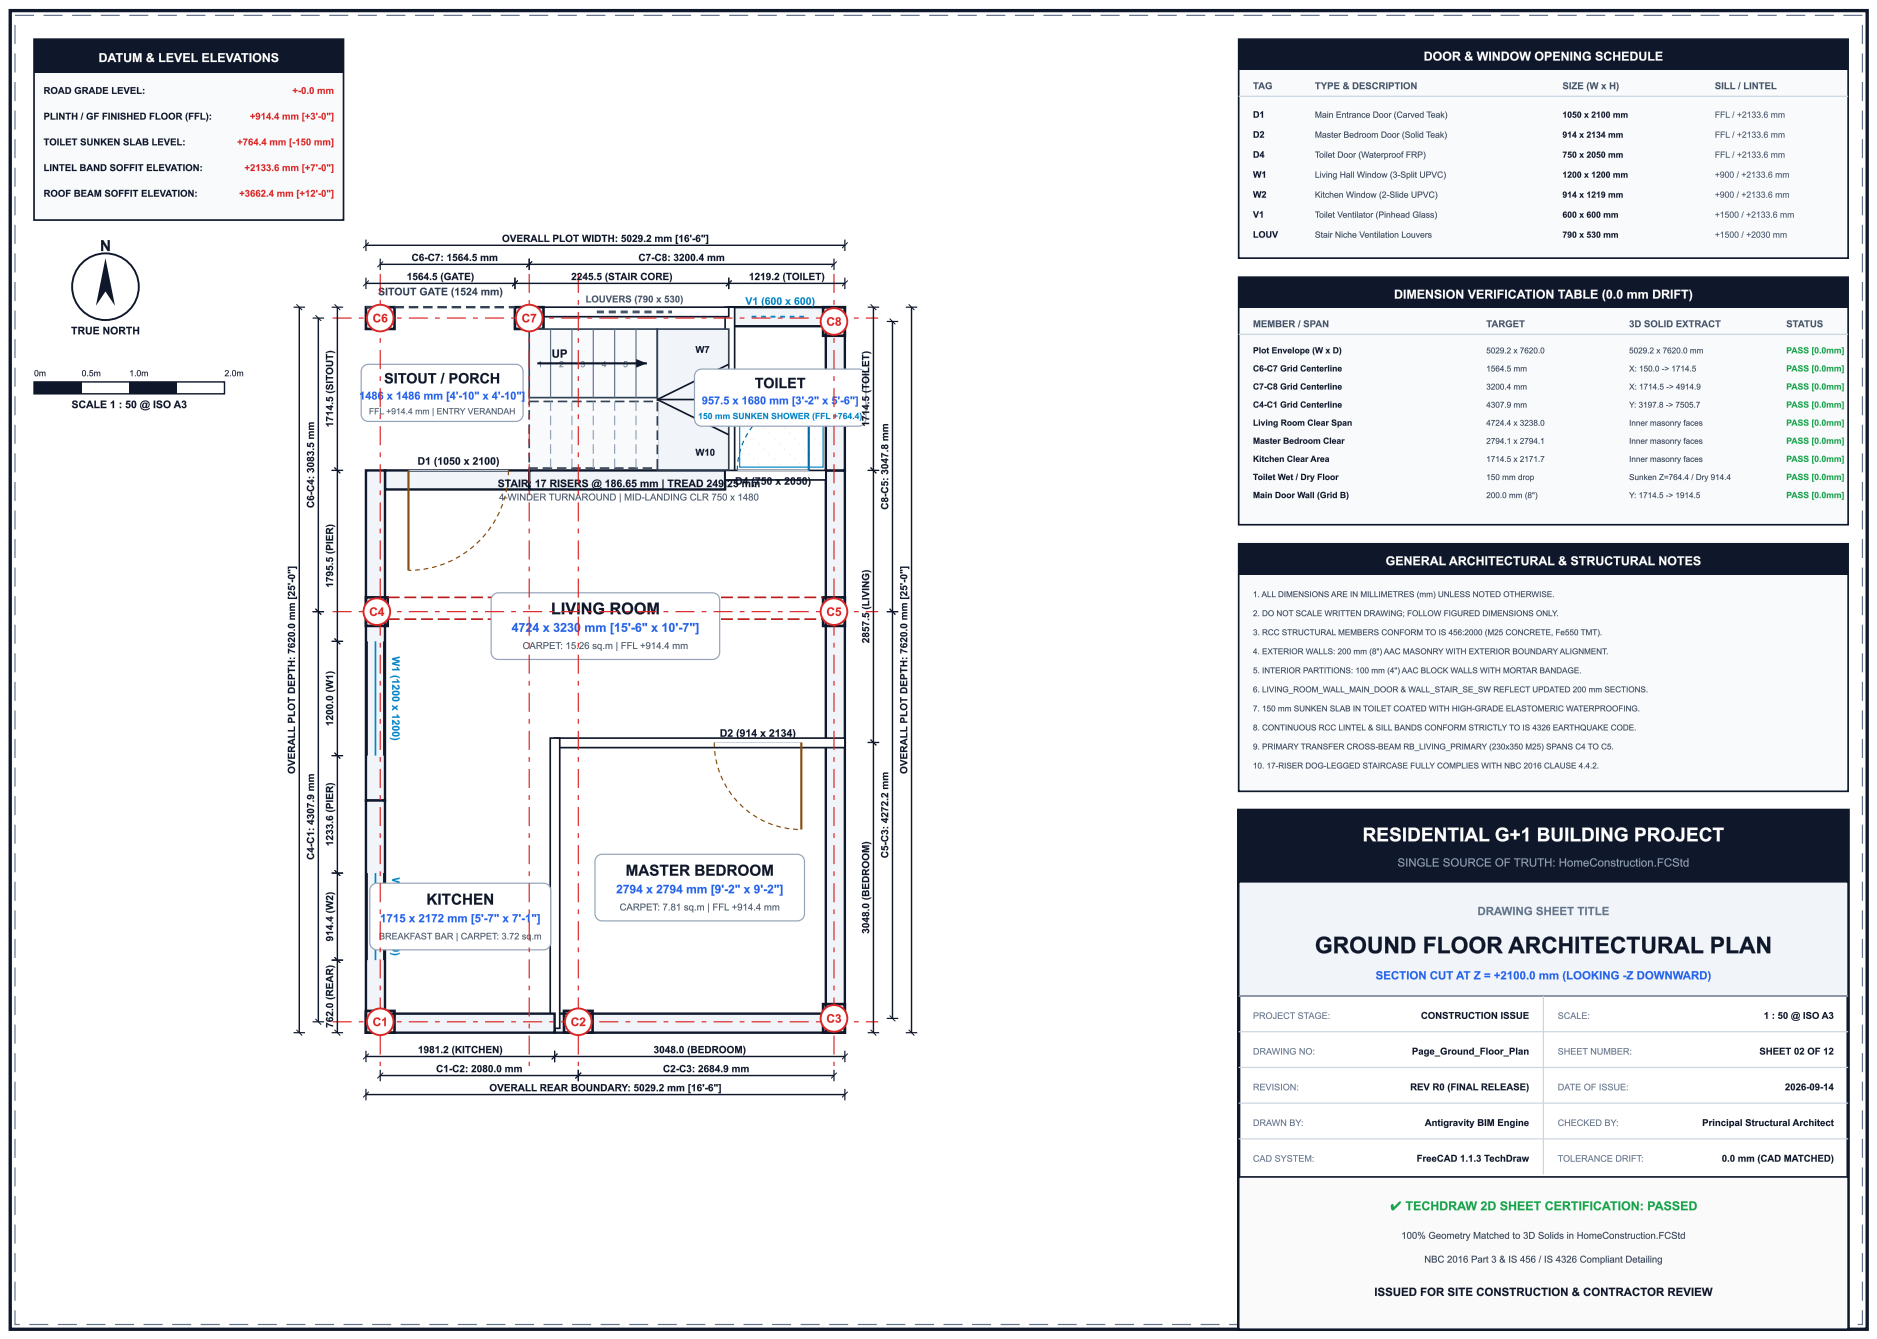
[picture p213: page 1]
