Pradeeparul2/house-plan/renders/GF_Floor_Plan_Architectural.pdf

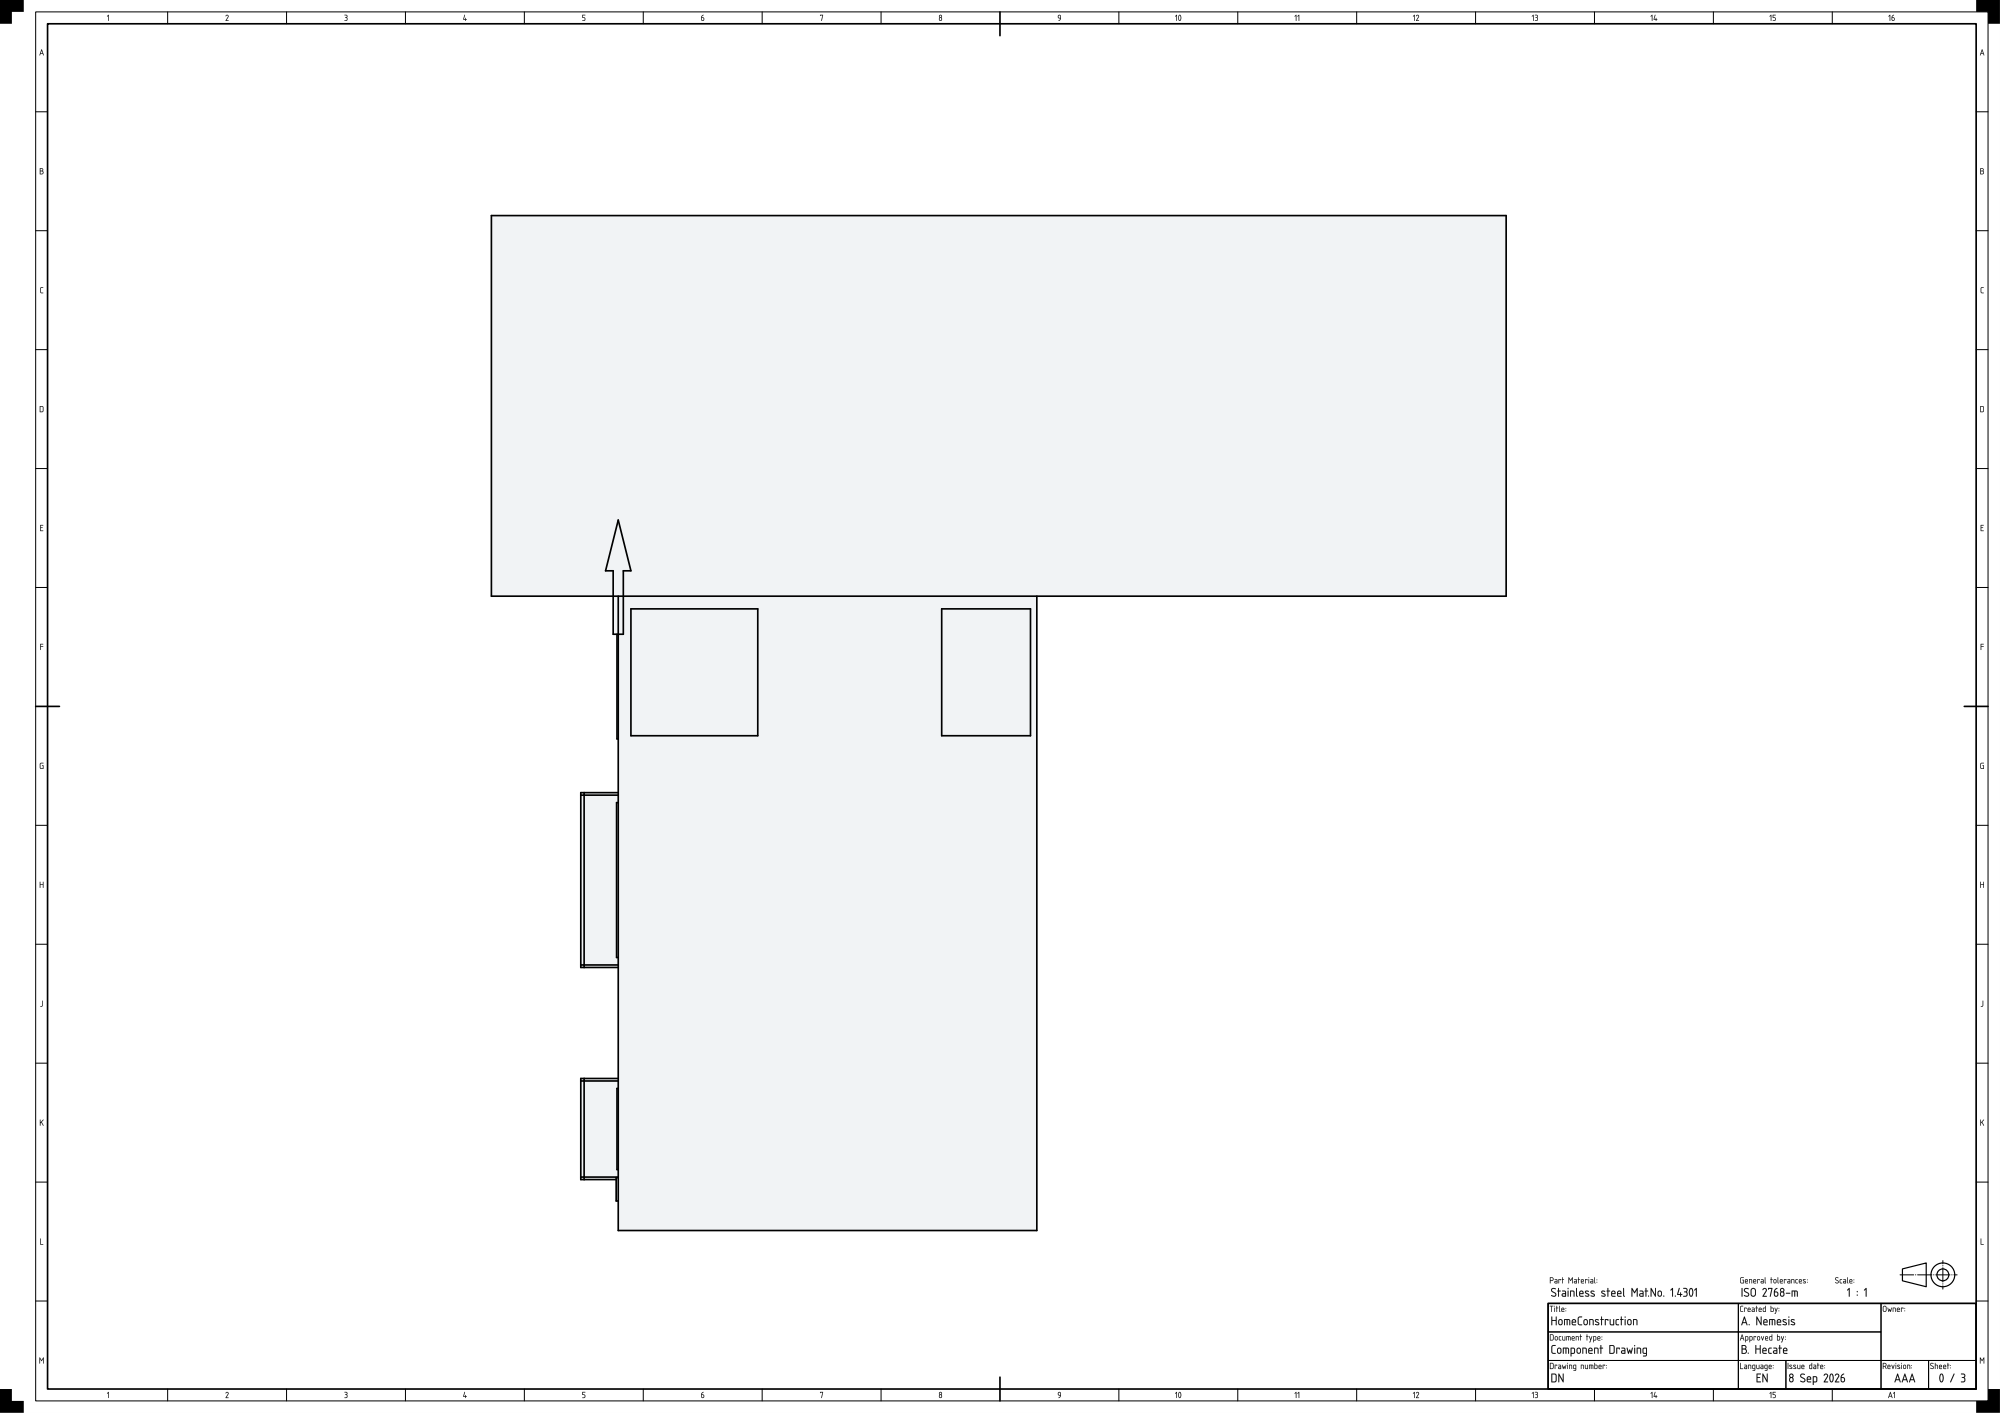
[picture p214: page 1]
