Pradeeparul2/house-plan/renders/Site_Plan_Foundation_Layout.pdf

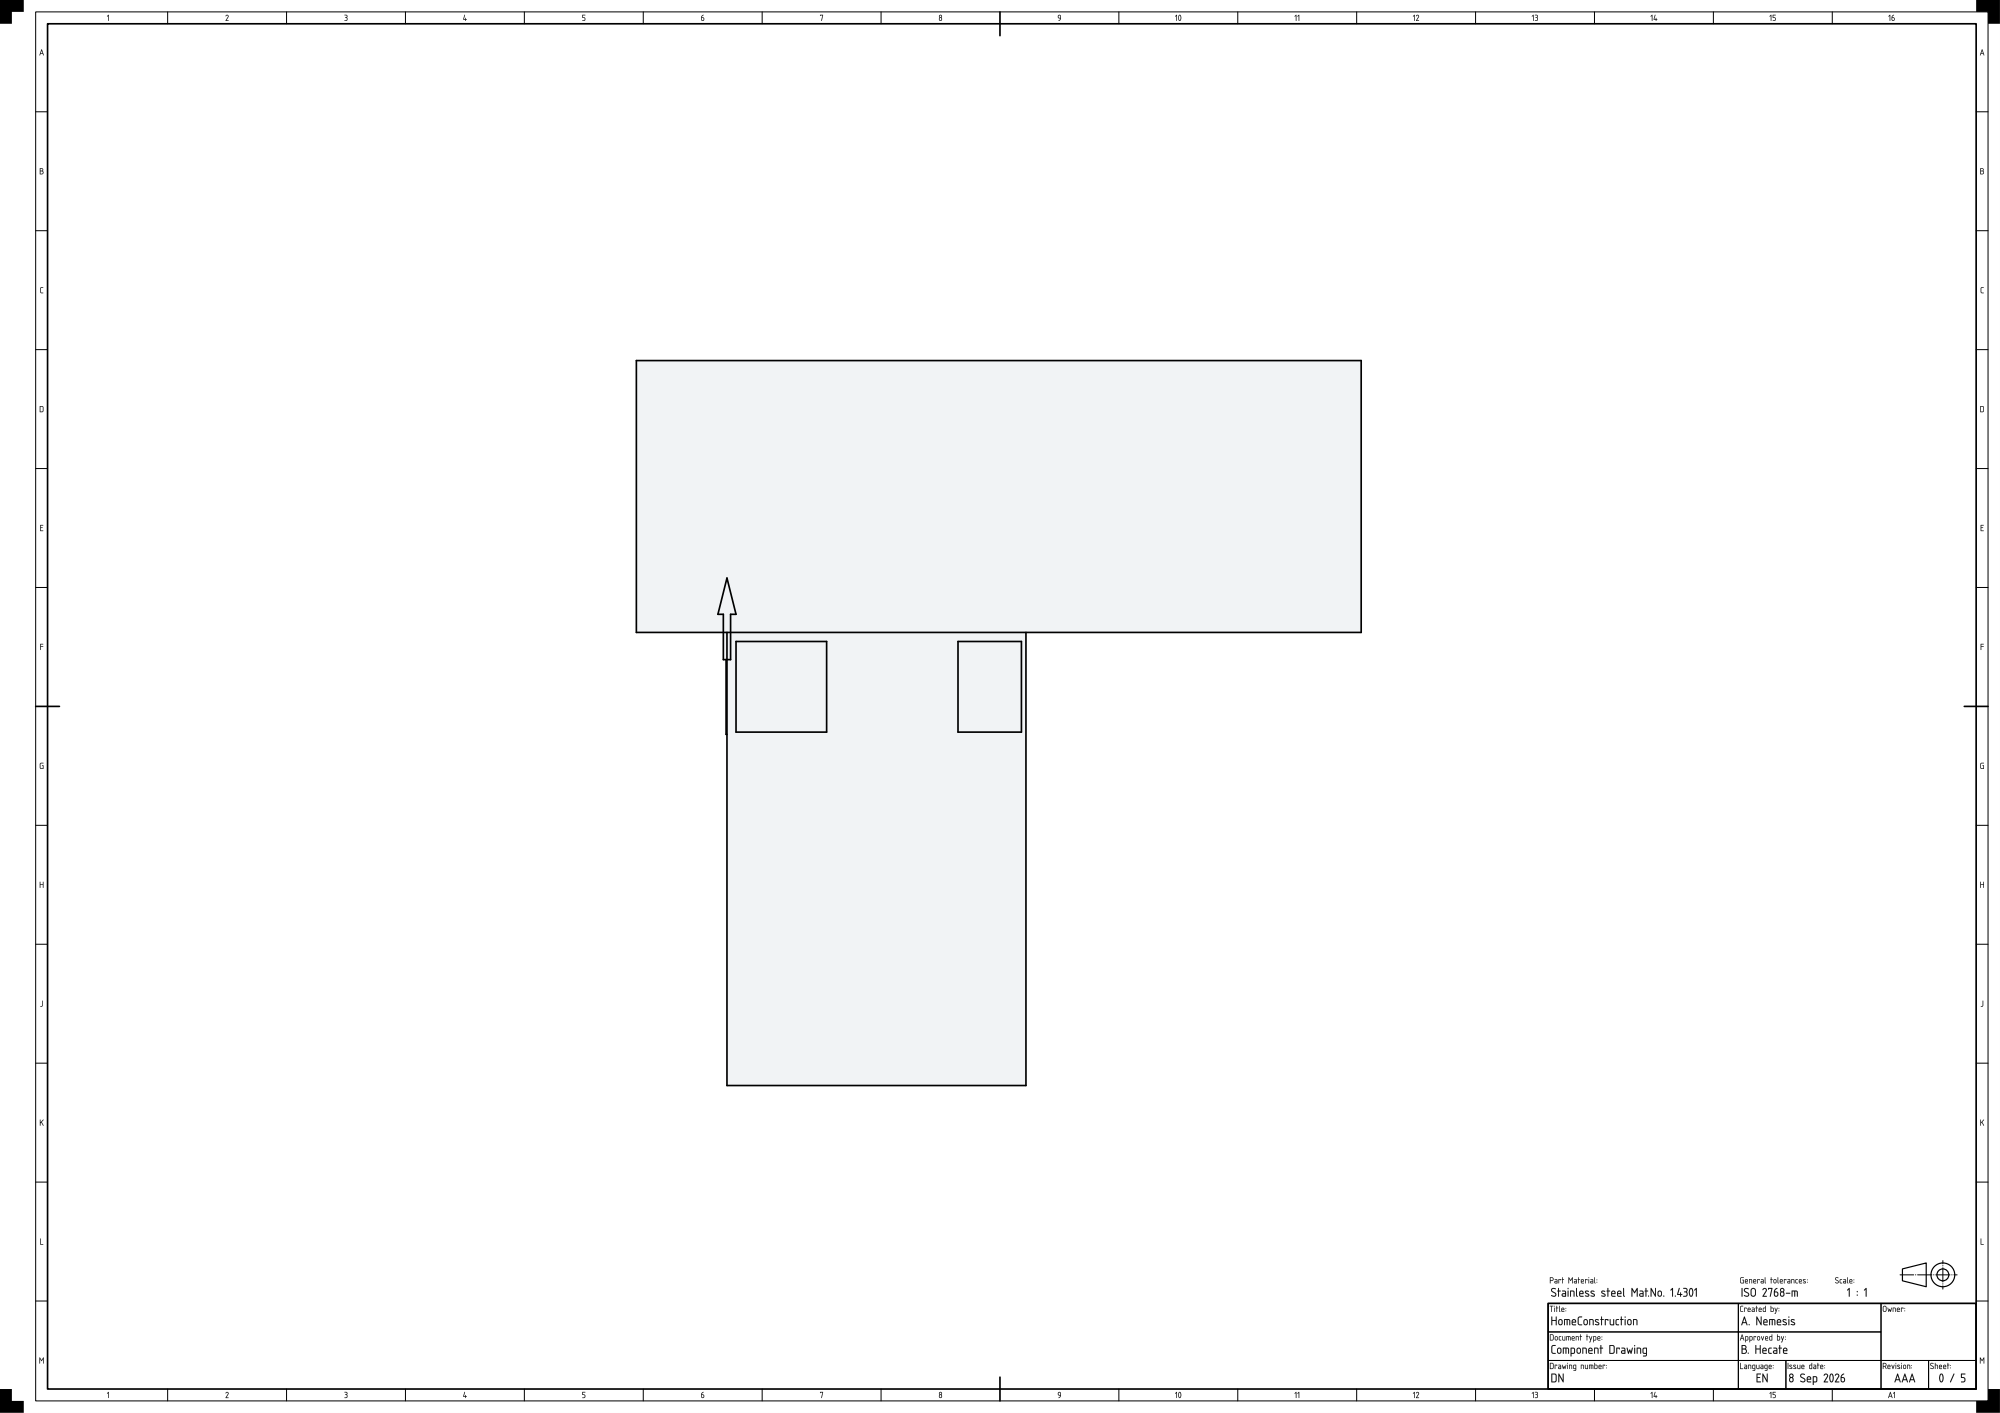
[picture p215: page 1]
