Pradeeparul2/house-plan/renders/Structural_Plan_Columns_Beams.pdf

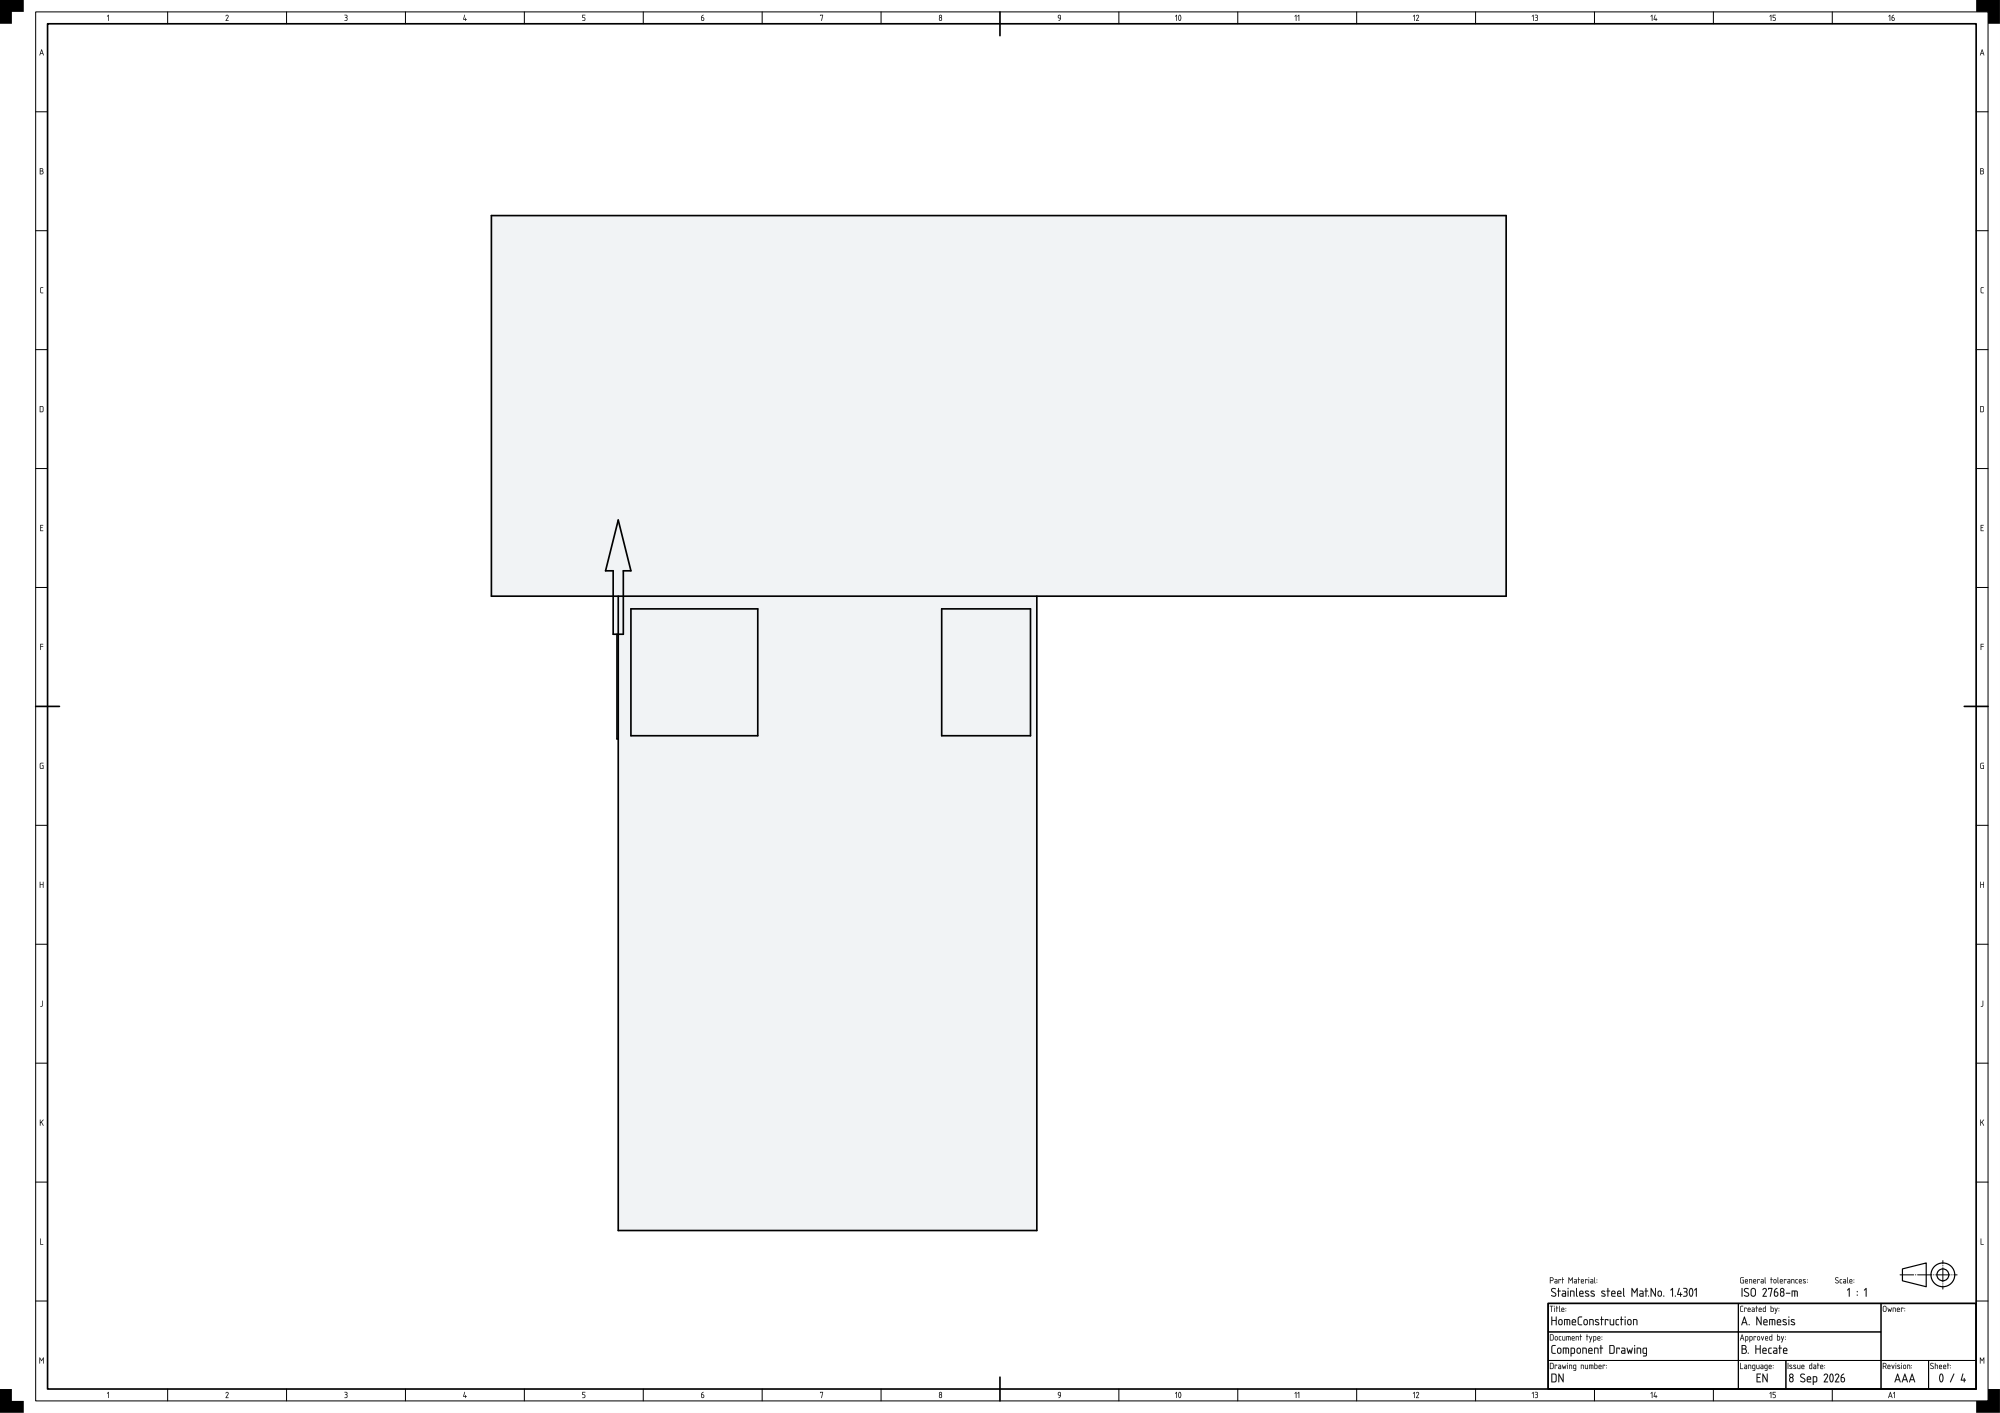
[picture p216: page 1]
